hesingh/ventilator/Medtronic/pb560-vent-files-4/BOM Drawings/PB560 Ventilator/10037185AB0.pdf

REVISION

REV | DESCRIPTION
AB | RELEASE/CHANGE PER EC124632

COVIDIEN
6135 Gunbarrel Avenue
Boulder, CO 80301

TITLE:
CPU Software Requirements
Specification, PB560

DOCUMENT NUMBER
10037185

SHEET 1 of 204

REV
AB
PROPRIETARY & CONFIDENTIAL | FOR INTERNAL USE ONLY
This document may not be copied, disclosed, or used in whole or in part without the consent of COVIDIEN. ã 2014 COVIDIEN All Rights Reserved.

# CPU Software Requirements Specification

PB560

THIS IS A REQUISITE PRO DOCUMENT.
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
