hesingh/ventilator/Medtronic/pb560-vent-files-4/BOM Drawings/PB560 Ventilator/10096510/10096506/10096506A00/10096506A00/eqfc.dxf

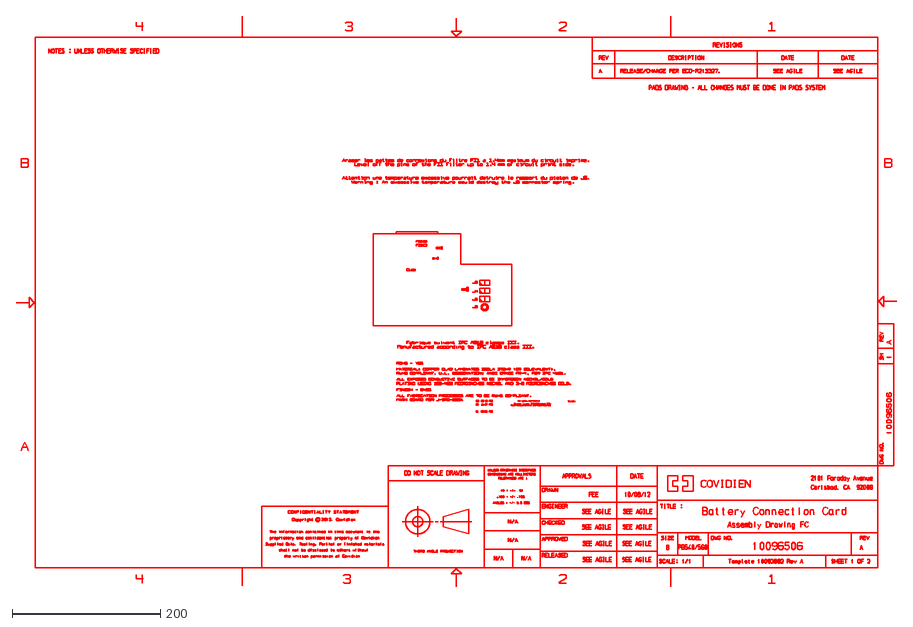
[picture p33: CAD file, 2020-04-06]
Medtronic/pb560-vent-files-4/BOM Drawings/PB560 Ventilator/10096510/10096506/10096506A00/10096506A00/eqfc.dxf
1188.1 x 770.1
