hesingh/ventilator/Medtronic/pb560-vent-files-4/BOM Drawings/PB560 PowerPack/10109800A00/HS Label.SLDPRT

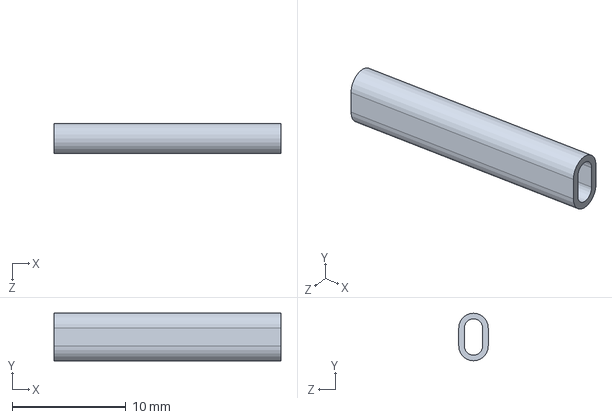
[picture p34: CAD file, 2020-04-06]
Medtronic/pb560-vent-files-4/BOM Drawings/PB560 PowerPack/10109800A00/HS Label.SLDPRT
20.0 x 4.20 x 2.60 mm
