hesingh/ventilator/Medtronic/medtronic-pb560-ventilator-system-file-set-2/3D CAD Models/PB560 Assy/capot 3 capteurs P phase 2.SLDPRT

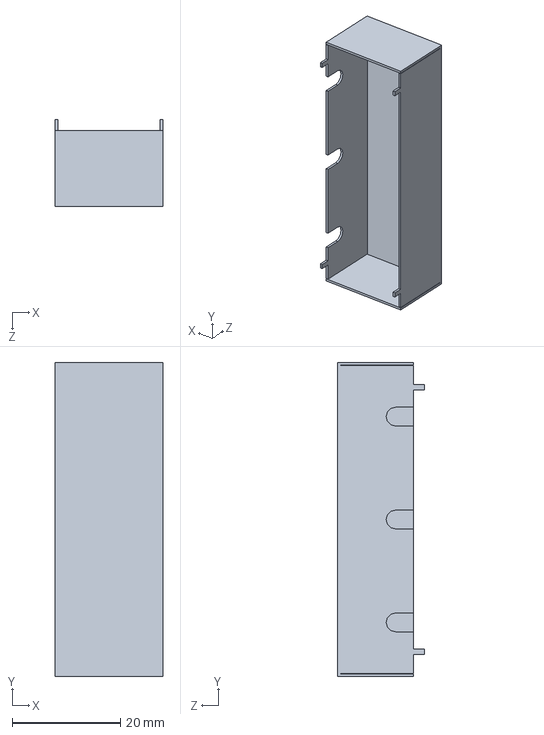
[picture p36: CAD file, 2020-04-06]
Medtronic/medtronic-pb560-ventilator-system-file-set-2/3D CAD Models/PB560 Assy/capot 3 capteurs P phase 2.SLDPRT
19.9 x 58.0 x 16.0 mm
