hesingh/ventilator/Medtronic/medtronic-pb560-ventilator-system-file-set-2/3D CAD Models/PB560 Assy/Insp Mod Connector.SLDPRT

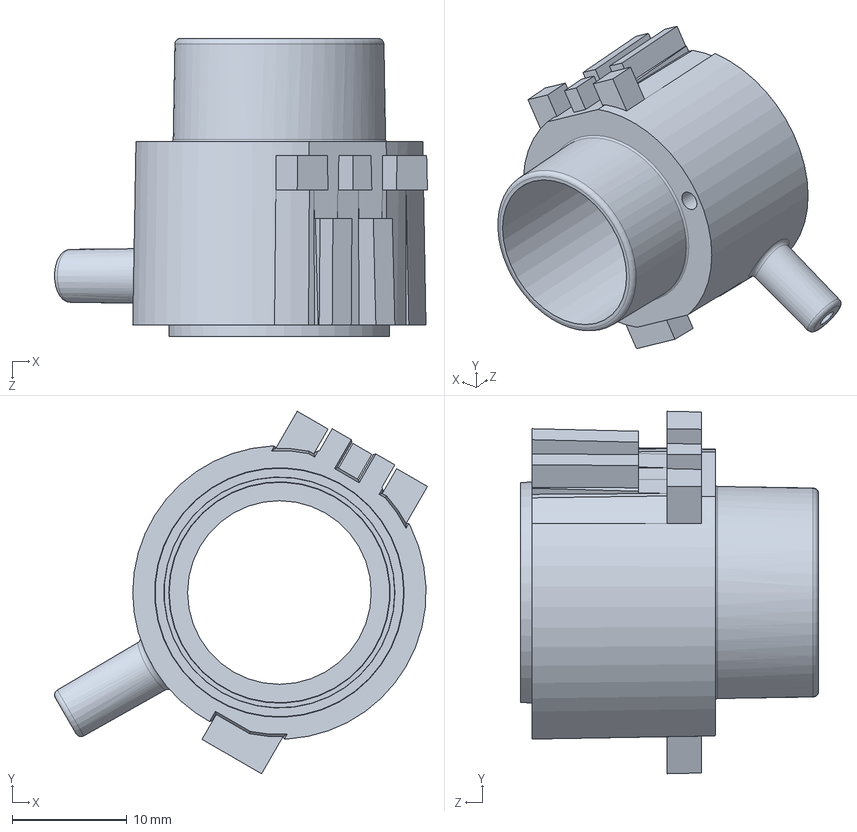
[picture p37: CAD file, 2020-04-06]
Medtronic/medtronic-pb560-ventilator-system-file-set-2/3D CAD Models/PB560 Assy/Insp Mod Connector.SLDPRT
32.5 x 31.6 x 26.0 mm
