hesingh/ventilator/Medtronic/pb560-vent-files-4/BOM Drawings/PB560 PowerPack/10106052C00/JST S2B-ZR-SM4A-TF.SLDPRT

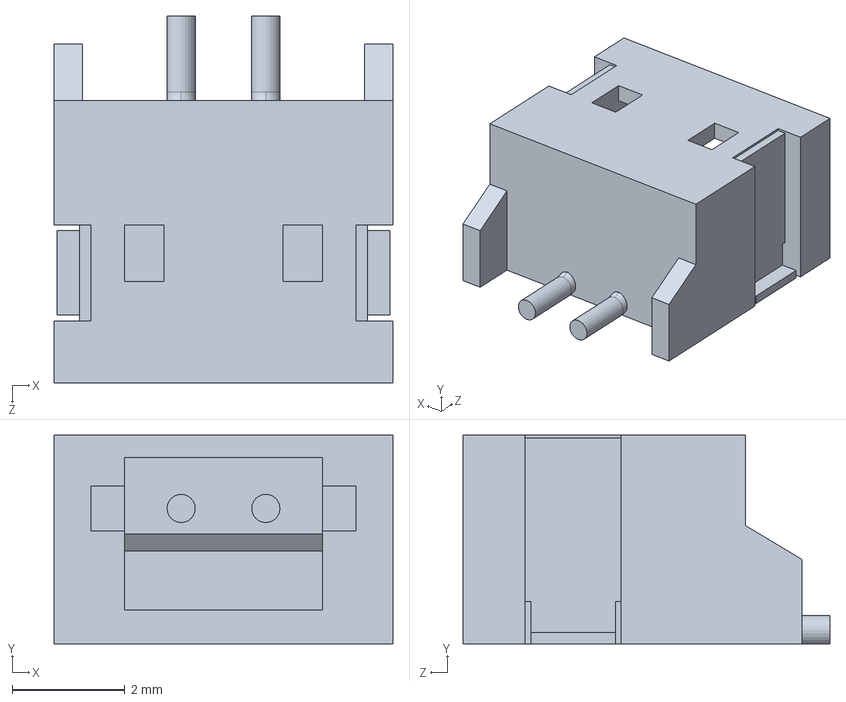
[picture p38: CAD file, 2020-04-06]
Medtronic/pb560-vent-files-4/BOM Drawings/PB560 PowerPack/10106052C00/JST S2B-ZR-SM4A-TF.SLDPRT
6.00 x 3.70 x 6.50 mm
