hesingh/ventilator/Medtronic/pb560-vent-files-4/BOM Drawings/PB560 PowerPack/10109802B00/Switchcraft 761KS15 Insulator sleeve.SLDPRT

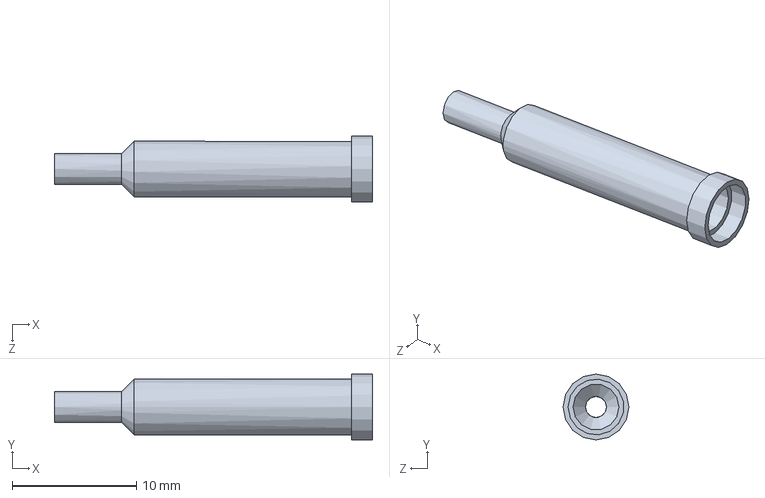
[picture p39: CAD file, 2020-04-06]
Medtronic/pb560-vent-files-4/BOM Drawings/PB560 PowerPack/10109802B00/Switchcraft 761KS15 Insulator sleeve.SLDPRT
25.6 x 5.30 x 5.30 mm
