hesingh/ventilator/Medtronic/pb560-vent-files-4/BOM Drawings/PB560 PowerPack/10106052C00/MOLEX 02661-4020.SLDPRT

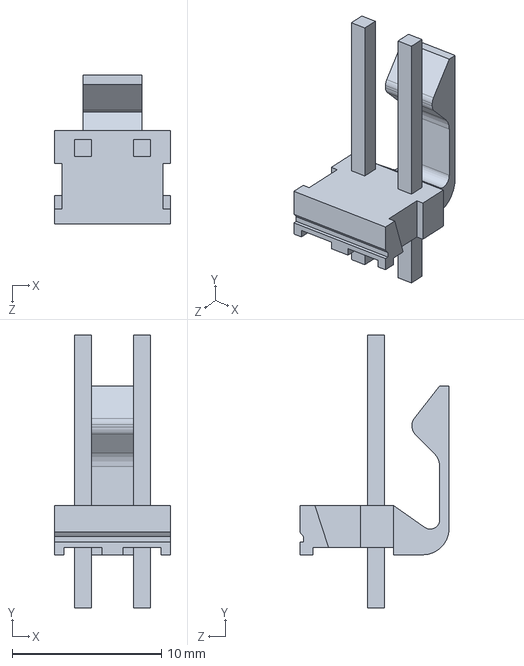
[picture p40: CAD file, 2020-04-06]
Medtronic/pb560-vent-files-4/BOM Drawings/PB560 PowerPack/10106052C00/MOLEX 02661-4020.SLDPRT
7.77 x 18.3 x 10.0 mm
