hesingh/ventilator/Medtronic/pb560-vent-files-4/BOM Drawings/PB560 PowerPack/10109802B00/Switchcraft 761KS15 Centre pin.SLDPRT

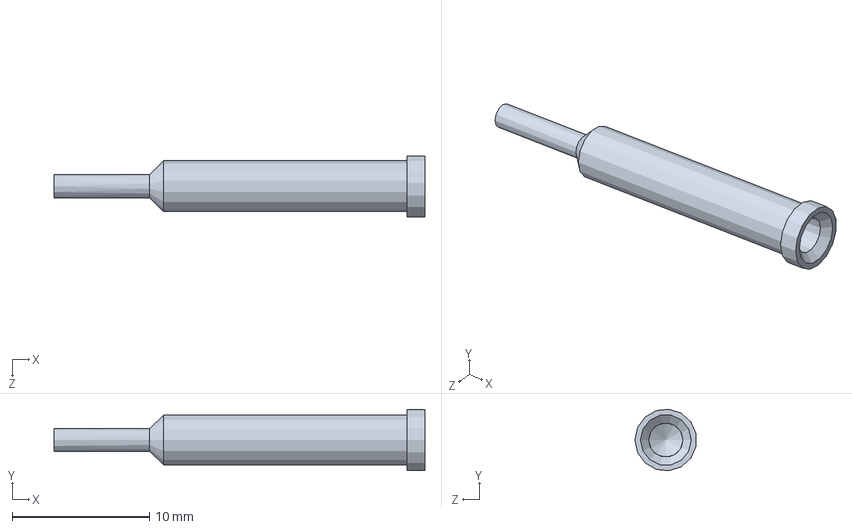
[picture p41: CAD file, 2020-04-06]
Medtronic/pb560-vent-files-4/BOM Drawings/PB560 PowerPack/10109802B00/Switchcraft 761KS15 Centre pin.SLDPRT
27.0 x 4.48 x 4.45 mm
