hesingh/ventilator/Medtronic/medtronic-pb560-ventilator-system-file-set-2/3D CAD Models/PB560 Assy/regulateur.SLDPRT

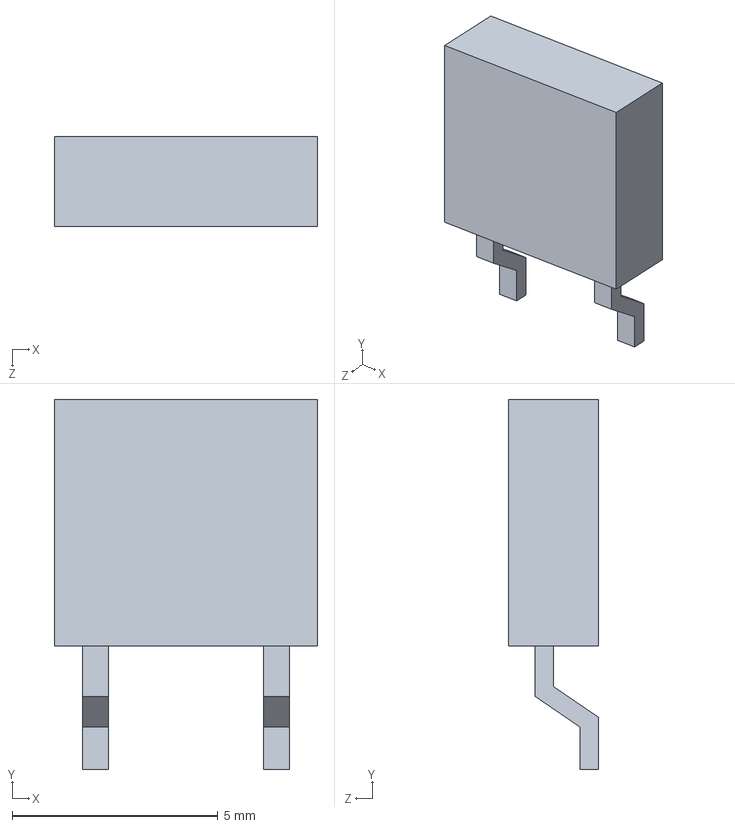
[picture p42: CAD file, 2020-04-06]
Medtronic/medtronic-pb560-ventilator-system-file-set-2/3D CAD Models/PB560 Assy/regulateur.SLDPRT
6.40 x 9.00 x 2.20 mm
