hesingh/ventilator/Medtronic/pb560-vent-files-4/BOM Drawings/PB560 PowerPack/10109802B00/WURTH 74270057.SLDPRT

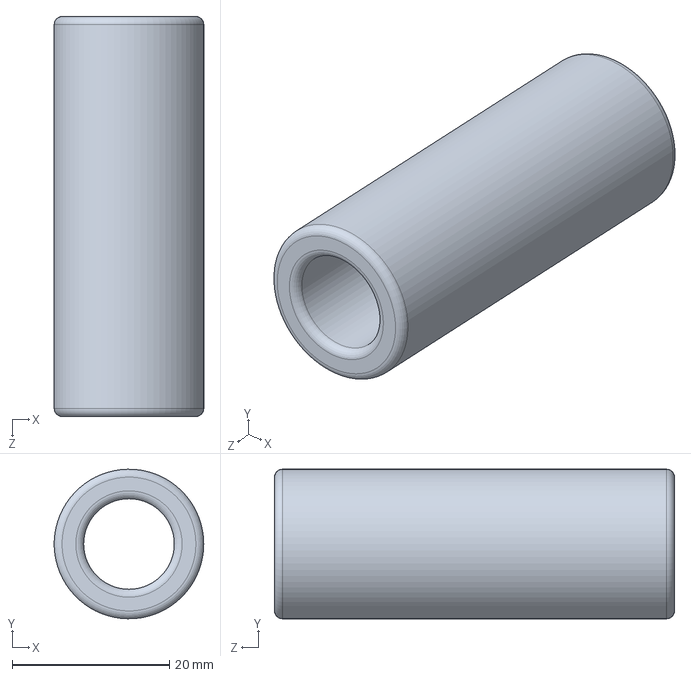
[picture p43: CAD file, 2020-04-06]
Medtronic/pb560-vent-files-4/BOM Drawings/PB560 PowerPack/10109802B00/WURTH 74270057.SLDPRT
19.0 x 19.0 x 50.8 mm
