hesingh/ventilator/Medtronic/medtronic-pb560-ventilator-system-file-set-2/3D CAD Models/PB560 Assy/carte clairitec.SLDPRT

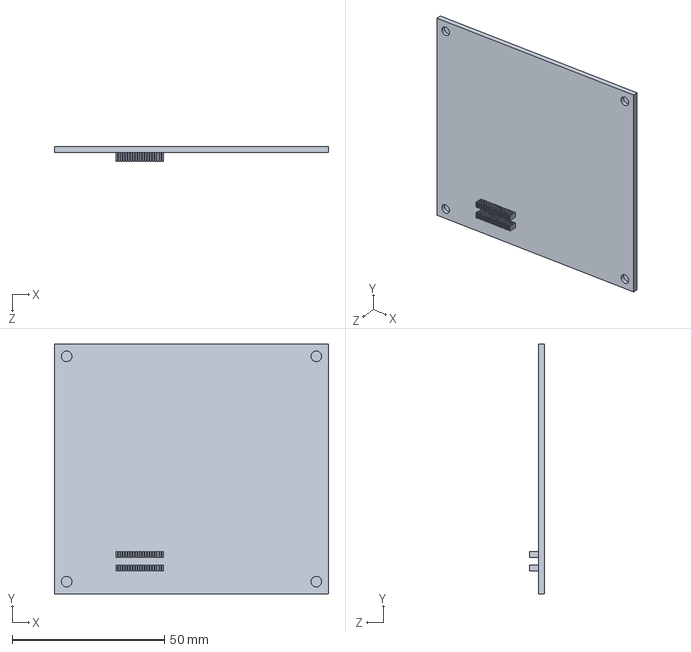
[picture p44: CAD file, 2020-04-06]
Medtronic/medtronic-pb560-ventilator-system-file-set-2/3D CAD Models/PB560 Assy/carte clairitec.SLDPRT
90.0 x 82.0 x 5.00 mm
