hesingh/ventilator/Medtronic/pb560-vent-files-4/BOM Drawings/PB560 PowerPack/10106052C00/MOLEX 43650-0229.SLDPRT

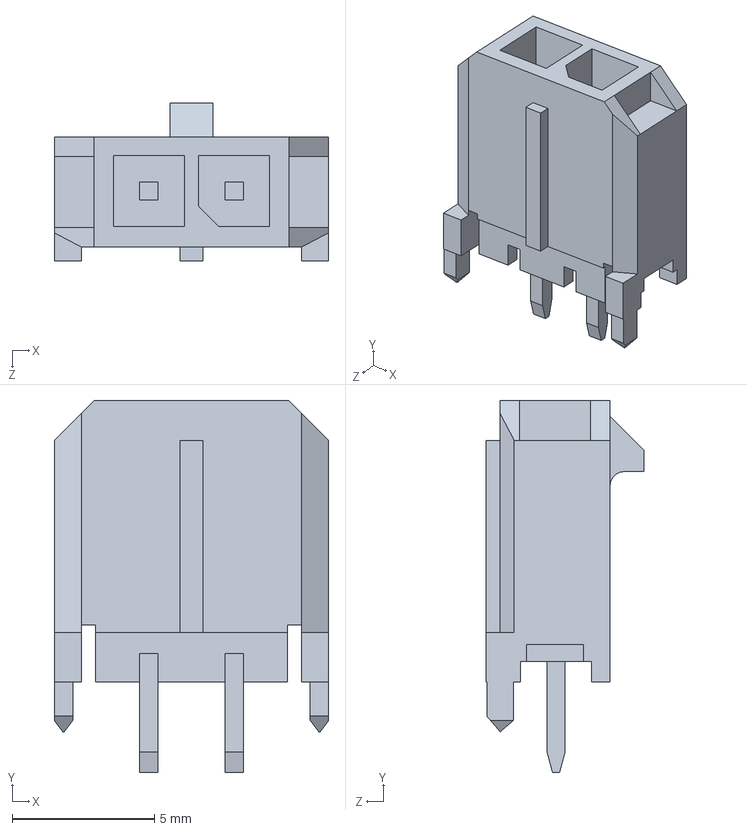
[picture p45: CAD file, 2020-04-06]
Medtronic/pb560-vent-files-4/BOM Drawings/PB560 PowerPack/10106052C00/MOLEX 43650-0229.SLDPRT
9.65 x 13.1 x 5.57 mm
