hesingh/ventilator/Medtronic/pb560-vent-files-4/BOM Drawings/PB560 PowerPack/10109802B00/Switchcraft 761KS15 Terminal spacer.SLDPRT

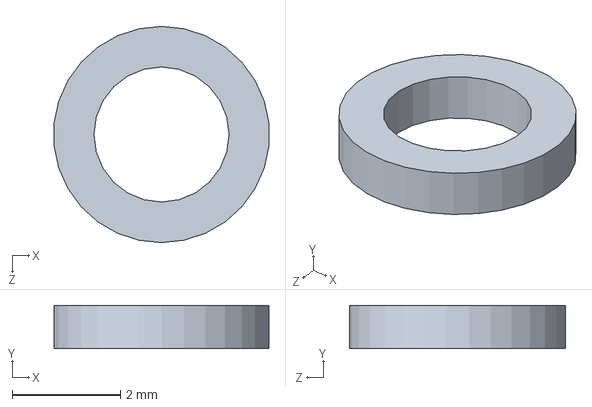
[picture p46: CAD file, 2020-04-06]
Medtronic/pb560-vent-files-4/BOM Drawings/PB560 PowerPack/10109802B00/Switchcraft 761KS15 Terminal spacer.SLDPRT
3.98 x 0.8 x 4.00 mm
