hesingh/ventilator/Medtronic/medtronic-pb560-ventilator-system-file-set-2/3D CAD Models/PB560 Assy/09-48-4038.SLDPRT

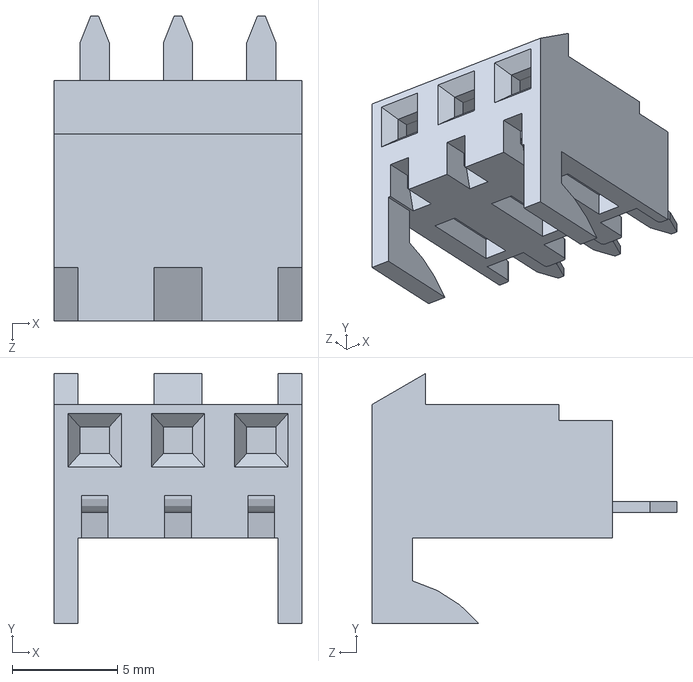
[picture p47: CAD file, 2020-04-06]
Medtronic/medtronic-pb560-ventilator-system-file-set-2/3D CAD Models/PB560 Assy/09-48-4038.SLDPRT
11.8 x 11.9 x 14.5 mm
