hesingh/ventilator/Medtronic/medtronic-pb560-ventilator-system-file-set-2/3D CAD Models/PB560 Assy/HARTING 09185107323.SLDPRT

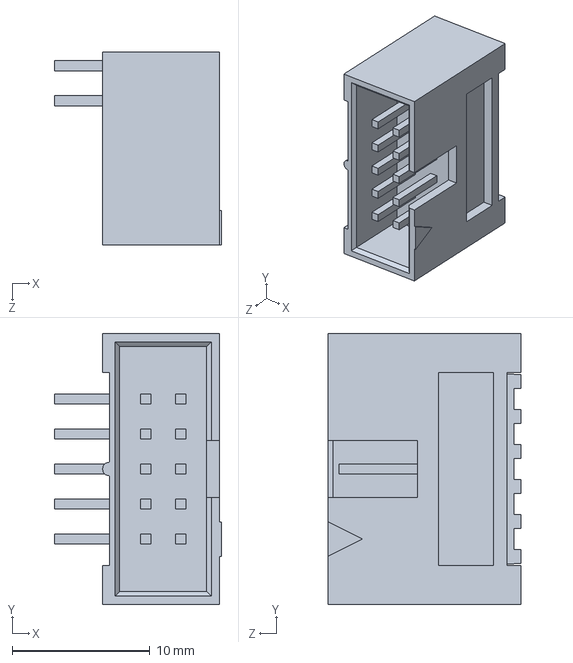
[picture p48: CAD file, 2020-04-06]
Medtronic/medtronic-pb560-ventilator-system-file-set-2/3D CAD Models/PB560 Assy/HARTING 09185107323.SLDPRT
12.1 x 19.7 x 14.0 mm
