hesingh/ventilator/Medtronic/pb560-vent-files-4/BOM Drawings/PB560 PowerPack/10109802B00/LEMO FHG.1B.306.CLAD52.SLDPRT

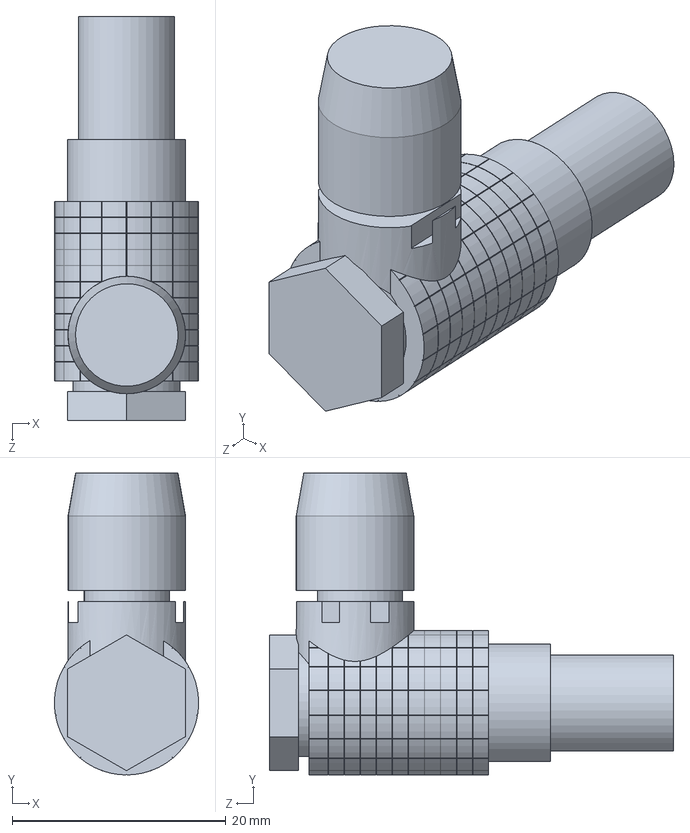
[picture p49: CAD file, 2020-04-06]
Medtronic/pb560-vent-files-4/BOM Drawings/PB560 PowerPack/10109802B00/LEMO FHG.1B.306.CLAD52.SLDPRT
13.5 x 28.2 x 37.8 mm
