hesingh/ventilator/Medtronic/medtronic-pb560-ventilator-system-file-set-2/3D CAD Models/PB560 Assy/3M 7810-0000PR.SLDPRT

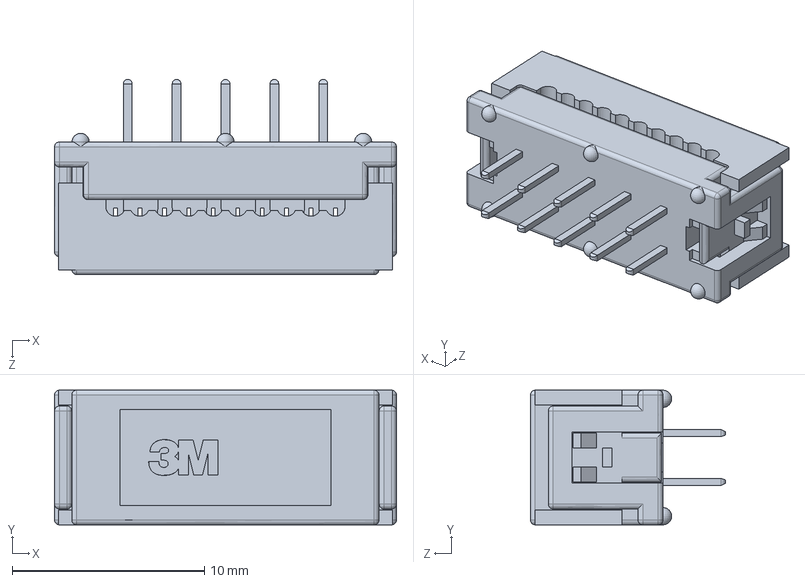
[picture p50: CAD file, 2020-04-06]
Medtronic/medtronic-pb560-ventilator-system-file-set-2/3D CAD Models/PB560 Assy/3M 7810-0000PR.SLDPRT
17.8 x 7.00 x 10.1 mm
