hesingh/ventilator/Medtronic/medtronic-pb560-ventilator-system-file-set-2/3D CAD Models/PB560 Assy/Batt PCB.SLDPRT

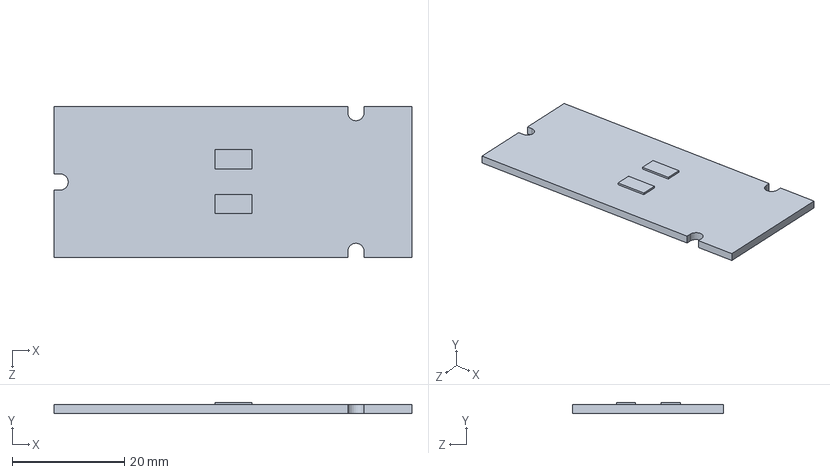
[picture p51: CAD file, 2020-04-06]
Medtronic/medtronic-pb560-ventilator-system-file-set-2/3D CAD Models/PB560 Assy/Batt PCB.SLDPRT
63.9 x 2.00 x 26.9 mm
