hesingh/ventilator/Medtronic/medtronic-pb560-ventilator-system-file-set-2/3D CAD Models/PB560 Assy/Cable tie (ref AML).SLDPRT

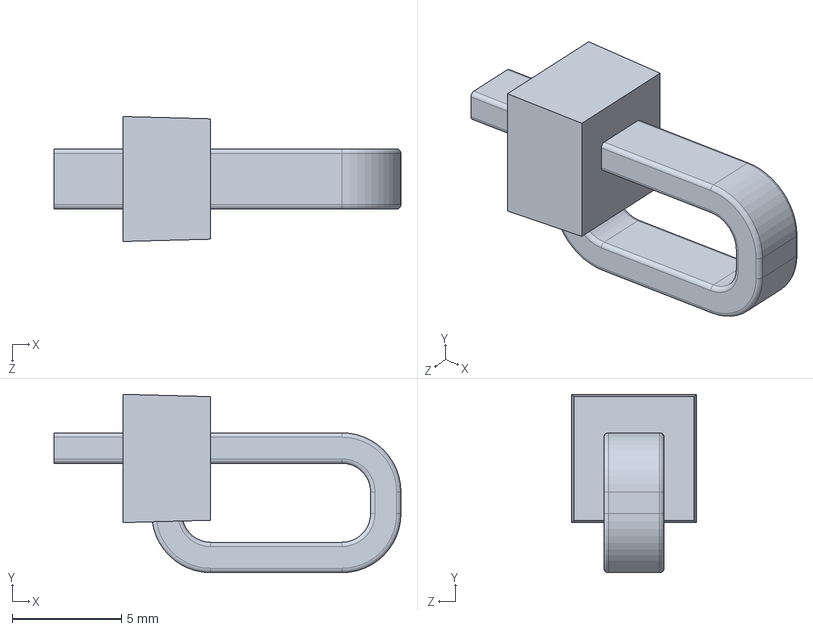
[picture p52: CAD file, 2020-04-06]
Medtronic/medtronic-pb560-ventilator-system-file-set-2/3D CAD Models/PB560 Assy/Cable tie (ref AML).SLDPRT
15.9 x 8.15 x 5.71 mm
