hesingh/ventilator/Medtronic/medtronic-pb560-ventilator-system-file-set-2/3D CAD Models/PB560 Assy/3M 4032 x30mm.SLDPRT

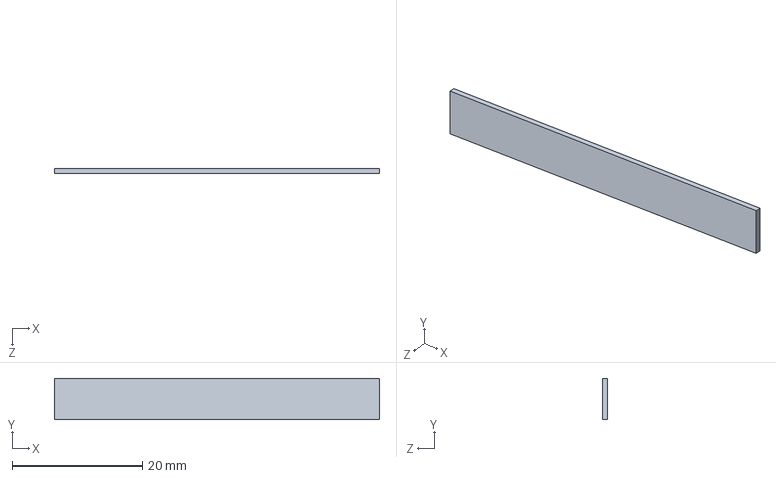
[picture p53: CAD file, 2020-04-06]
Medtronic/medtronic-pb560-ventilator-system-file-set-2/3D CAD Models/PB560 Assy/3M 4032 x30mm.SLDPRT
50.0 x 6.35 x 0.8 mm
