hesingh/ventilator/Medtronic/medtronic-pb560-ventilator-system-file-set-2/3D CAD Models/PB560 Assy/tuyau 15x21 silicone.SLDPRT

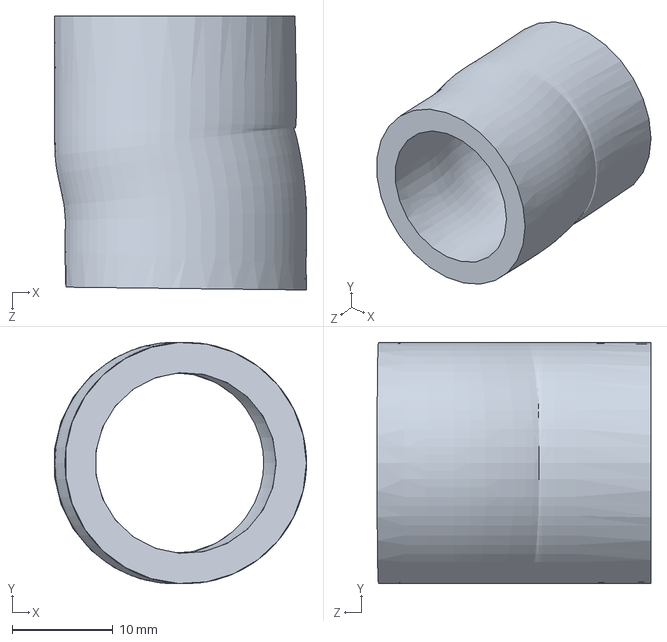
[picture p54: CAD file, 2020-04-06]
Medtronic/medtronic-pb560-ventilator-system-file-set-2/3D CAD Models/PB560 Assy/tuyau 15x21 silicone.SLDPRT
25.1 x 24.0 x 27.2 mm
