hesingh/ventilator/Medtronic/medtronic-pb560-ventilator-system-file-set-2/3D CAD Models/PB560 Assy/tuyau  droit sortie vanne O2.SLDPRT

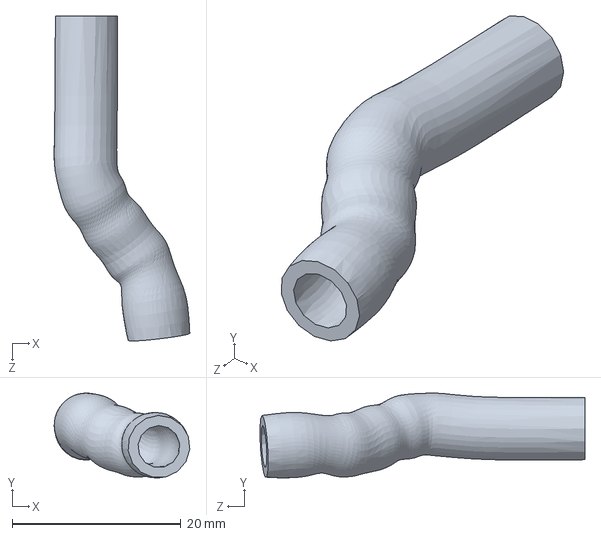
[picture p55: CAD file, 2020-04-06]
Medtronic/medtronic-pb560-ventilator-system-file-set-2/3D CAD Models/PB560 Assy/tuyau droit sortie vanne O2.SLDPRT
16.1 x 10.0 x 38.5 mm
