hesingh/ventilator/Medtronic/medtronic-pb560-ventilator-system-file-set-2/3D CAD Models/PB560 Assy/MOLEX 22-05-7098.SLDPRT

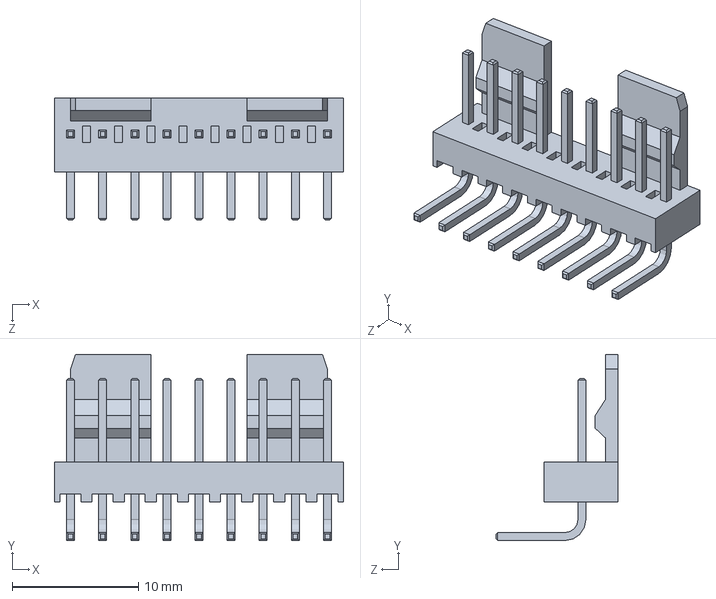
[picture p56: CAD file, 2020-04-06]
Medtronic/medtronic-pb560-ventilator-system-file-set-2/3D CAD Models/PB560 Assy/MOLEX 22-05-7098.SLDPRT
22.9 x 14.7 x 9.65 mm
