hesingh/ventilator/Medtronic/medtronic-pb560-ventilator-system-file-set-2/3D CAD Models/PB560 Assy/tuyau pression prox1.6x4.8.SLDPRT

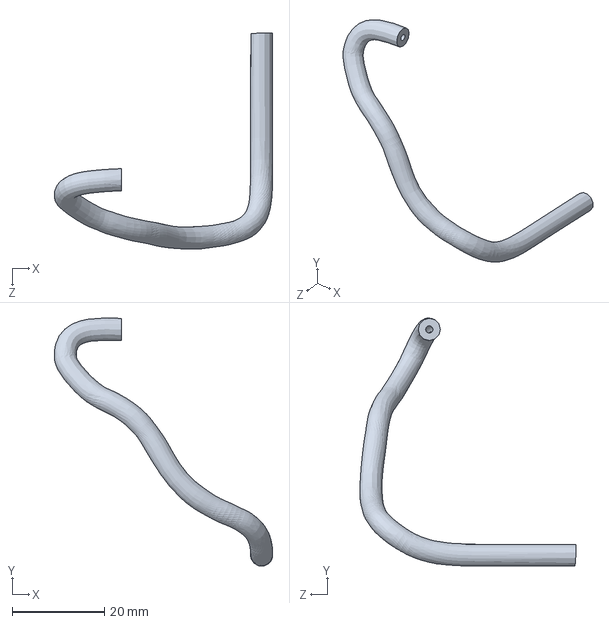
[picture p57: CAD file, 2020-04-06]
Medtronic/medtronic-pb560-ventilator-system-file-set-2/3D CAD Models/PB560 Assy/tuyau pression prox1.6x4.8.SLDPRT
47.2 x 53.6 x 46.8 mm
