hesingh/ventilator/Medtronic/medtronic-pb560-ventilator-system-file-set-2/3D CAD Models/PB560 Assy/thermistances CTN.SLDPRT

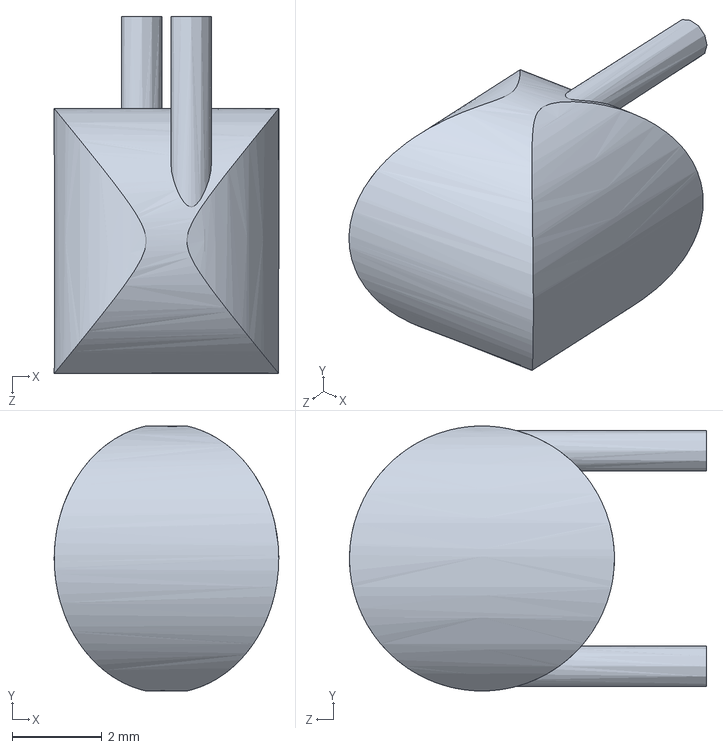
[picture p58: CAD file, 2020-04-06]
Medtronic/medtronic-pb560-ventilator-system-file-set-2/3D CAD Models/PB560 Assy/thermistances CTN.SLDPRT
5.00 x 5.90 x 7.95 mm
