hesingh/ventilator/Medtronic/medtronic-pb560-ventilator-system-file-set-2/3D CAD Models/PB560 Assy/tuyau sortie vanne pilot1.6x4.8.SLDPRT

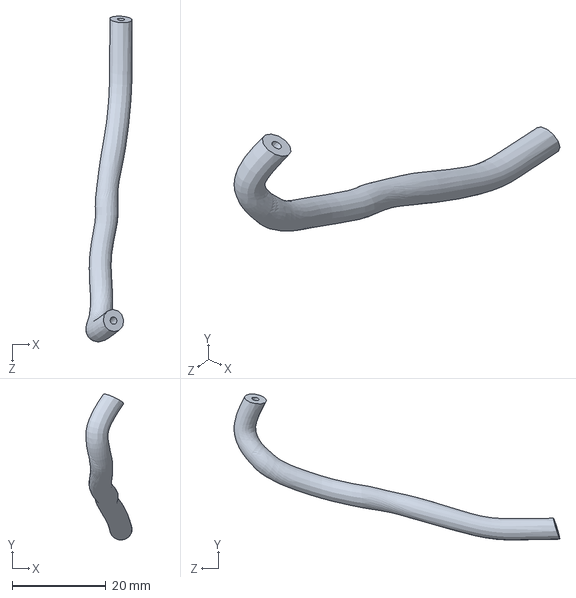
[picture p59: CAD file, 2020-04-06]
Medtronic/medtronic-pb560-ventilator-system-file-set-2/3D CAD Models/PB560 Assy/tuyau sortie vanne pilot1.6x4.8.SLDPRT
9.88 x 31.1 x 69.5 mm
