hesingh/ventilator/Medtronic/medtronic-pb560-ventilator-system-file-set-2/3D CAD Models/PB560 Assy/etiq reperage vanne O2.SLDPRT

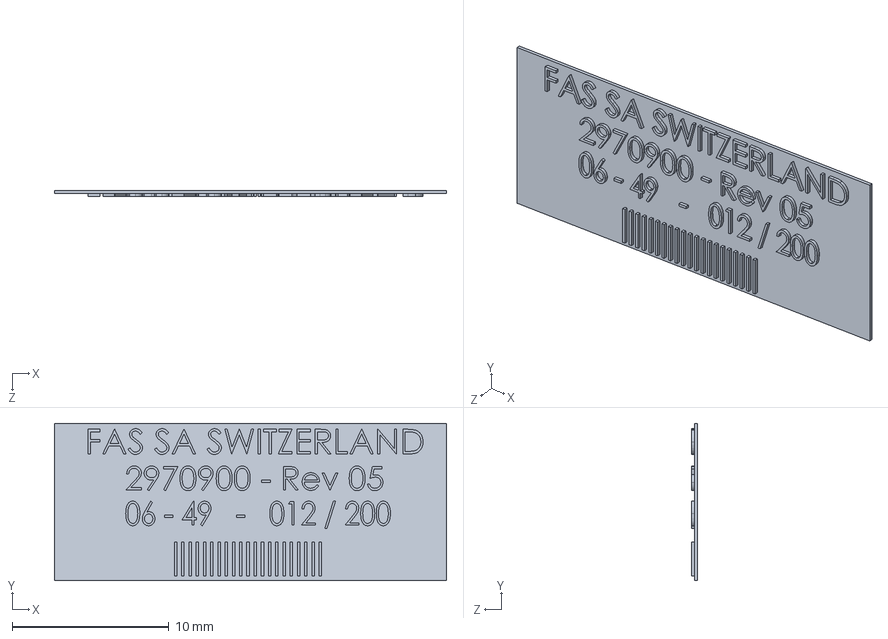
[picture p60: CAD file, 2020-04-06]
Medtronic/medtronic-pb560-ventilator-system-file-set-2/3D CAD Models/PB560 Assy/etiq reperage vanne O2.SLDPRT
25.0 x 10.0 x 0.4 mm
