hesingh/ventilator/Medtronic/medtronic-pb560-ventilator-system-file-set-2/3D CAD Models/PB560 Assy/Molex 90635-1262.SLDPRT

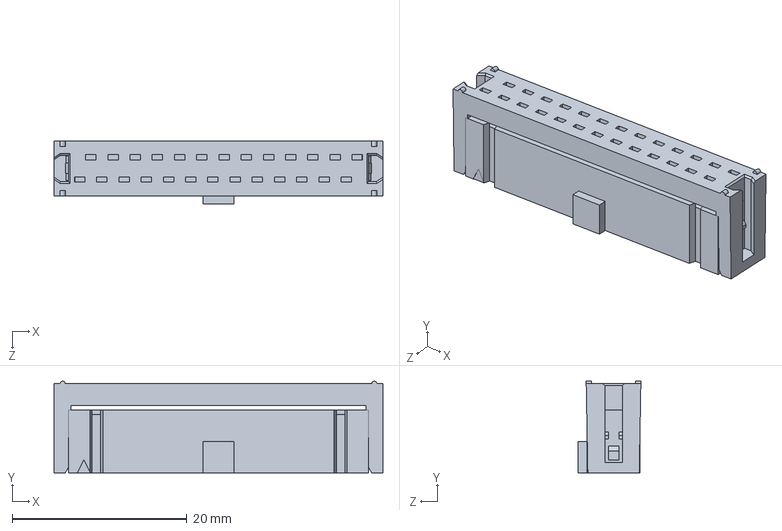
[picture p61: CAD file, 2020-04-06]
Medtronic/medtronic-pb560-ventilator-system-file-set-2/3D CAD Models/PB560 Assy/Molex 90635-1262.SLDPRT
37.6 x 10.5 x 7.18 mm
