hesingh/ventilator/Medtronic/medtronic-pb560-ventilator-system-file-set-2/3D CAD Models/PB560 Assy/HIROSE HR30-6R-6S.SLDPRT

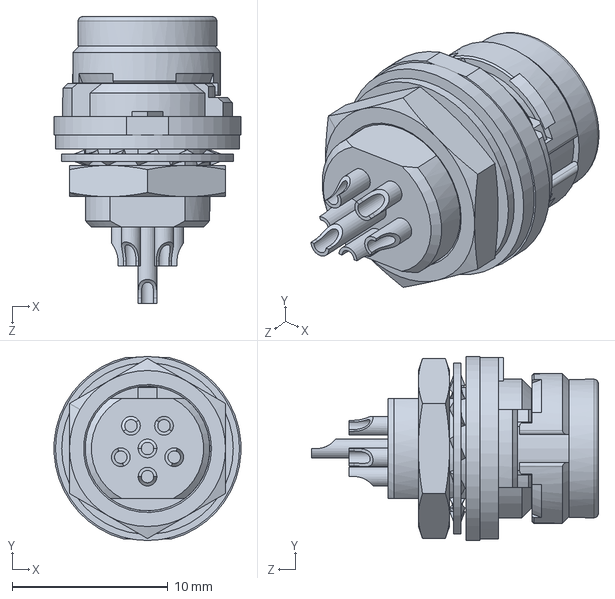
[picture p62: CAD file, 2020-04-06]
Medtronic/medtronic-pb560-ventilator-system-file-set-2/3D CAD Models/PB560 Assy/HIROSE HR30-6R-6S.SLDPRT
12.0 x 11.8 x 18.4 mm
