hesingh/ventilator/Medtronic/medtronic-pb560-ventilator-system-file-set-2/3D CAD Models/PB560 Assy/alimentation phase 2.SLDPRT

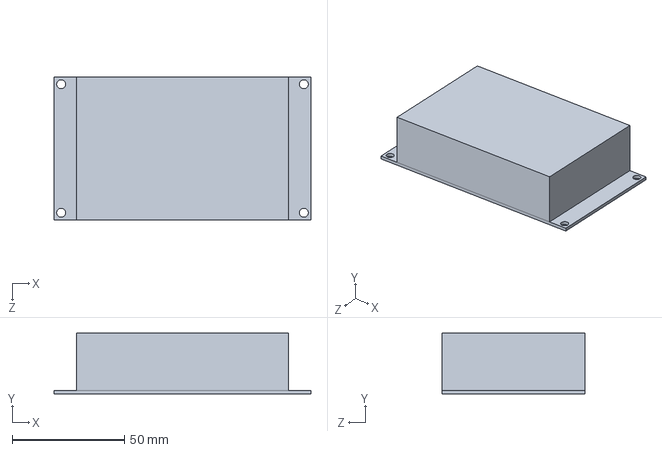
[picture p63: CAD file, 2020-04-06]
Medtronic/medtronic-pb560-ventilator-system-file-set-2/3D CAD Models/PB560 Assy/alimentation phase 2.SLDPRT
114.3 x 27.0 x 63.5 mm
