hesingh/ventilator/Medtronic/medtronic-pb560-ventilator-system-file-set-2/3D CAD Models/PB560 Assy/1mm bumper.SLDPRT

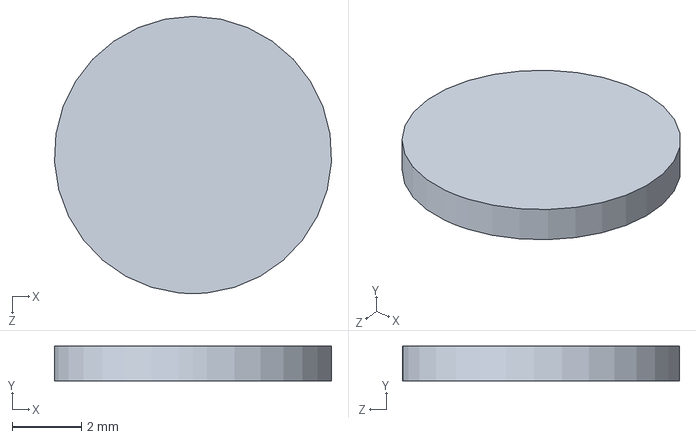
[picture p64: CAD file, 2020-04-06]
Medtronic/medtronic-pb560-ventilator-system-file-set-2/3D CAD Models/PB560 Assy/1mm bumper.SLDPRT
7.99 x 1.00 x 8.00 mm
