hesingh/ventilator/Medtronic/medtronic-pb560-ventilator-system-file-set-2/3D CAD Models/PB560 Assy/Batt Contacts tab.SLDPRT

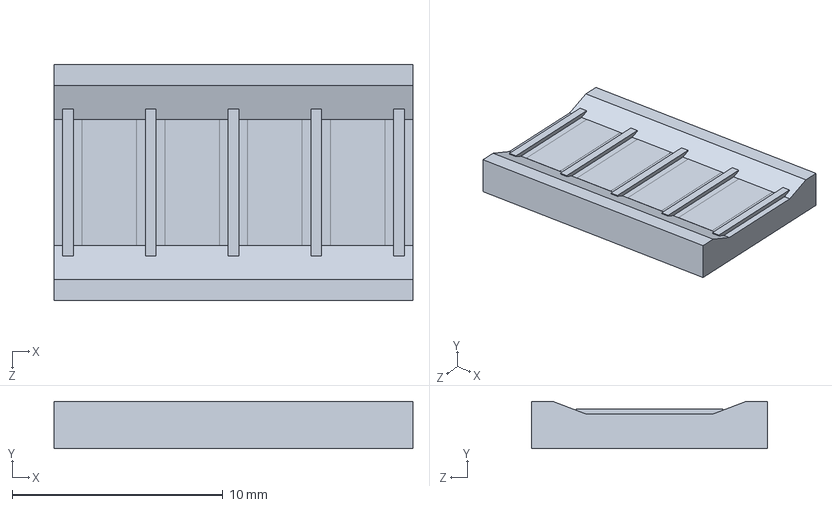
[picture p66: CAD file, 2020-04-06]
Medtronic/medtronic-pb560-ventilator-system-file-set-2/3D CAD Models/PB560 Assy/Batt Contacts tab.SLDPRT
17.0 x 2.25 x 11.2 mm
