hesingh/ventilator/Medtronic/medtronic-pb560-ventilator-system-file-set-2/3D CAD Models/PB560 Assy/Rondelle plate - ZU  3 x 6 EP 0.8.sldprt

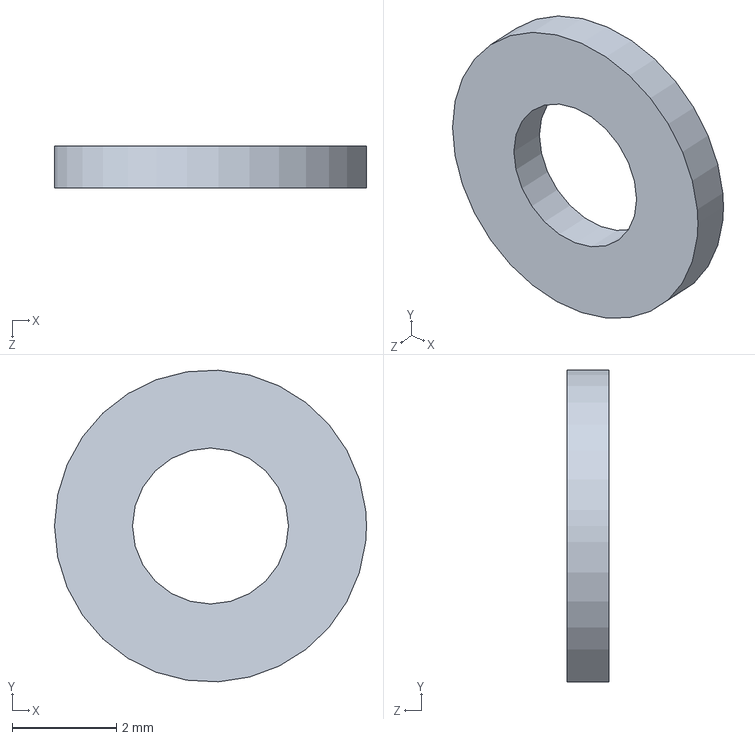
[picture p67: CAD file, 2020-04-06]
Medtronic/medtronic-pb560-ventilator-system-file-set-2/3D CAD Models/PB560 Assy/Rondelle plate - ZU 3 x 6 EP 0.8.sldprt
6.00 x 5.99 x 0.8 mm
