hesingh/ventilator/Medtronic/medtronic-pb560-ventilator-system-file-set-2/3D CAD Models/PB560 Assy/MODULE PRISE 230+INTER.SLDPRT

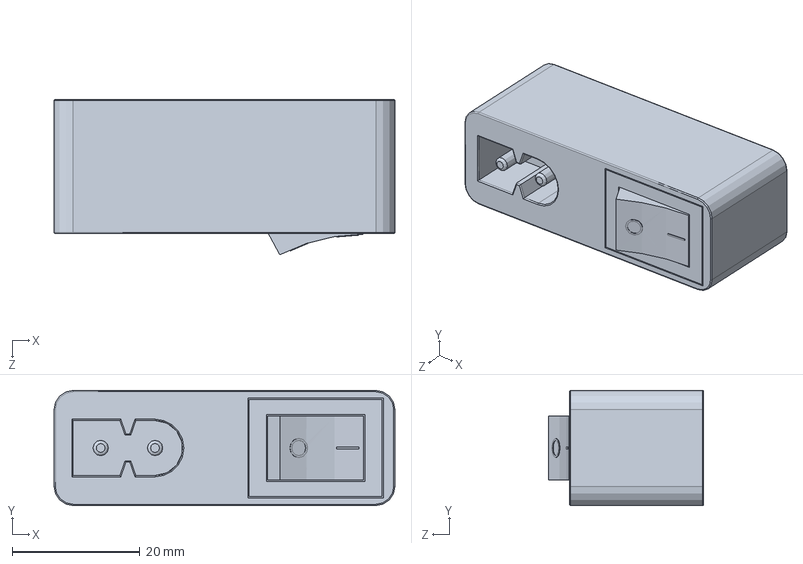
[picture p68: CAD file, 2020-04-06]
Medtronic/medtronic-pb560-ventilator-system-file-set-2/3D CAD Models/PB560 Assy/MODULE PRISE 230+INTER.SLDPRT
53.3 x 18.0 x 24.3 mm
