hesingh/ventilator/Medtronic/medtronic-pb560-ventilator-system-file-set-2/3D CAD Models/PB560 Assy/Vis KA22x5 hexalobes.SLDPRT

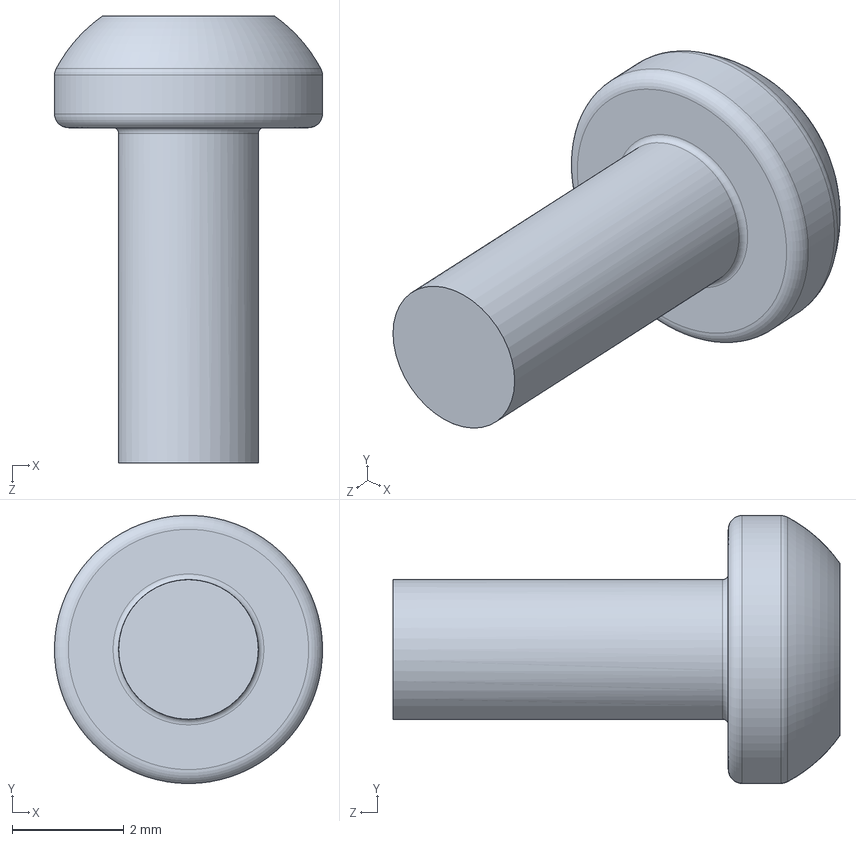
[picture p69: CAD file, 2020-04-06]
Medtronic/medtronic-pb560-ventilator-system-file-set-2/3D CAD Models/PB560 Assy/Vis KA22x5 hexalobes.SLDPRT
4.80 x 4.80 x 8.00 mm
