hesingh/ventilator/Medtronic/medtronic-pb560-ventilator-system-file-set-2/3D CAD Models/PB560 Assy/carte buzzer.SLDPRT

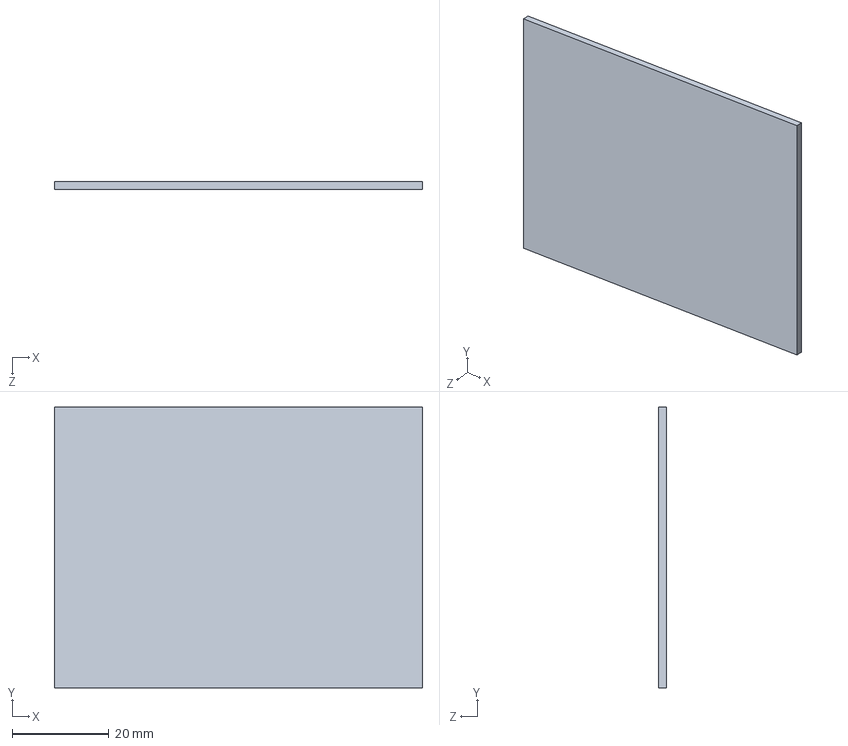
[picture p70: CAD file, 2020-04-06]
Medtronic/medtronic-pb560-ventilator-system-file-set-2/3D CAD Models/PB560 Assy/carte buzzer.SLDPRT
76.0 x 58.0 x 1.60 mm
