hesingh/ventilator/Medtronic/medtronic-pb560-ventilator-system-file-set-2/3D CAD Models/PB560 Assy/Front End Cap.SLDPRT

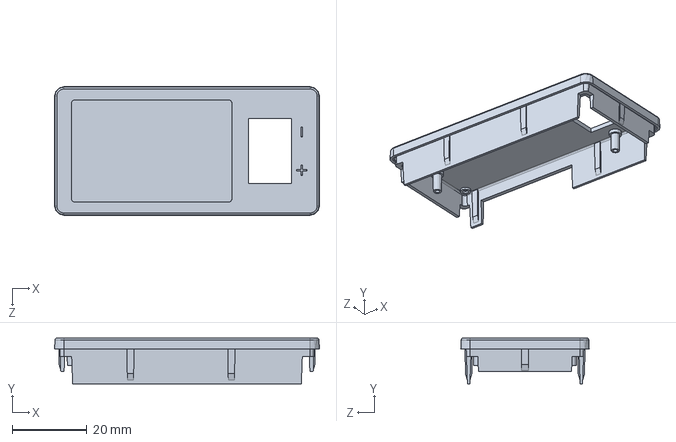
[picture p71: CAD file, 2020-04-06]
Medtronic/medtronic-pb560-ventilator-system-file-set-2/3D CAD Models/PB560 Assy/Front End Cap.SLDPRT
70.9 x 12.3 x 34.4 mm
