hesingh/ventilator/Medtronic/medtronic-pb560-ventilator-system-file-set-2/3D CAD Models/PB560 Assy/condensateur.SLDPRT

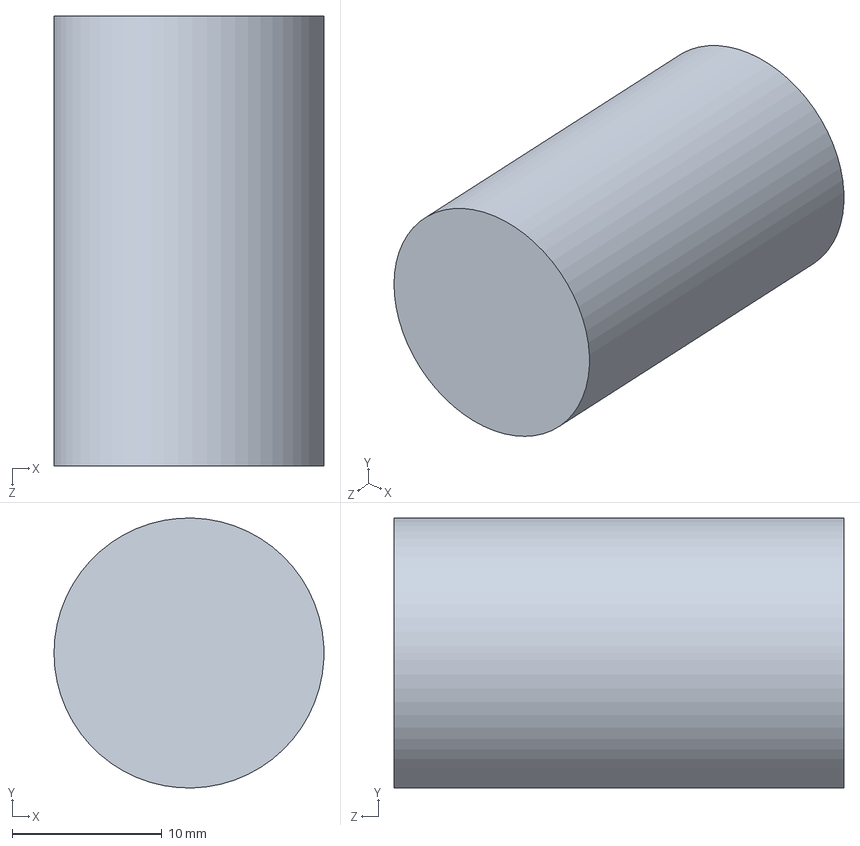
[picture p72: CAD file, 2020-04-06]
Medtronic/medtronic-pb560-ventilator-system-file-set-2/3D CAD Models/PB560 Assy/condensateur.SLDPRT
18.0 x 18.0 x 30.0 mm
