hesingh/ventilator/Medtronic/medtronic-pb560-ventilator-system-file-set-2/3D CAD Models/PB560 Assy/cache transfo.SLDPRT

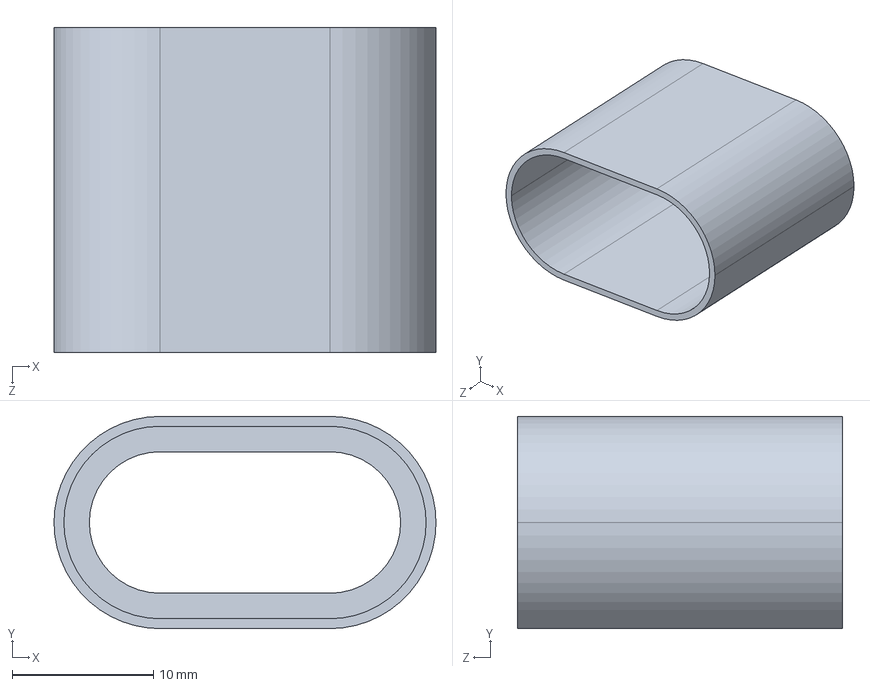
[picture p73: CAD file, 2020-04-06]
Medtronic/medtronic-pb560-ventilator-system-file-set-2/3D CAD Models/PB560 Assy/cache transfo.SLDPRT
27.0 x 15.0 x 23.0 mm
