hesingh/ventilator/Medtronic/medtronic-pb560-ventilator-system-file-set-2/3D CAD Models/PB560 Assy/Extruded housing.SLDPRT

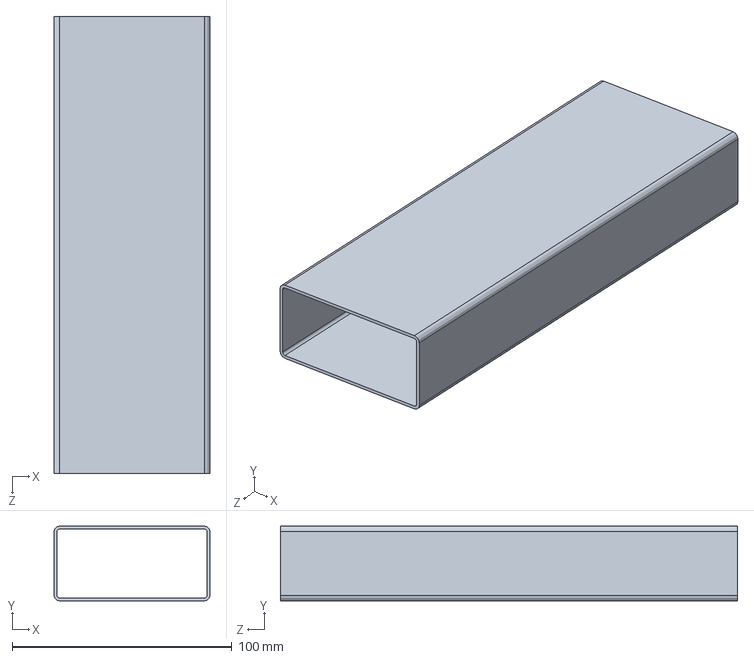
[picture p74: CAD file, 2020-04-06]
Medtronic/medtronic-pb560-ventilator-system-file-set-2/3D CAD Models/PB560 Assy/Extruded housing.SLDPRT
71.0 x 34.0 x 208.0 mm
