hesingh/ventilator/Medtronic/medtronic-pb560-ventilator-system-file-set-2/3D CAD Models/PB560 Assy/MOLEX 22-05-7088.SLDPRT

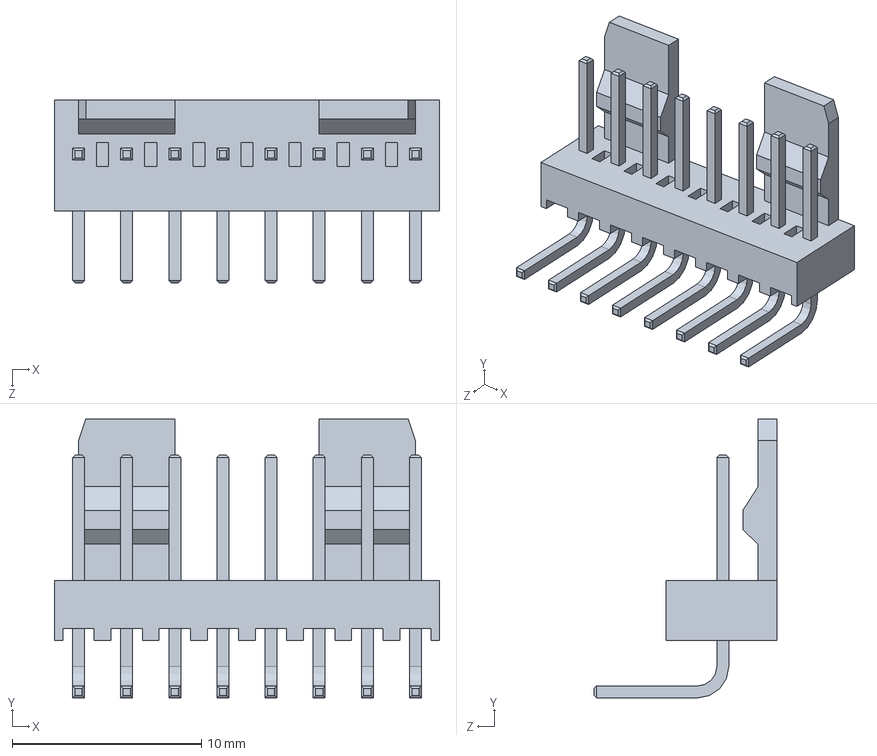
[picture p75: CAD file, 2020-04-06]
Medtronic/medtronic-pb560-ventilator-system-file-set-2/3D CAD Models/PB560 Assy/MOLEX 22-05-7088.SLDPRT
20.3 x 14.7 x 9.65 mm
