hesingh/ventilator/Medtronic/medtronic-pb560-ventilator-system-file-set-2/3D CAD Models/PB560 Assy/AFFICHEUR TWIN.SLDPRT

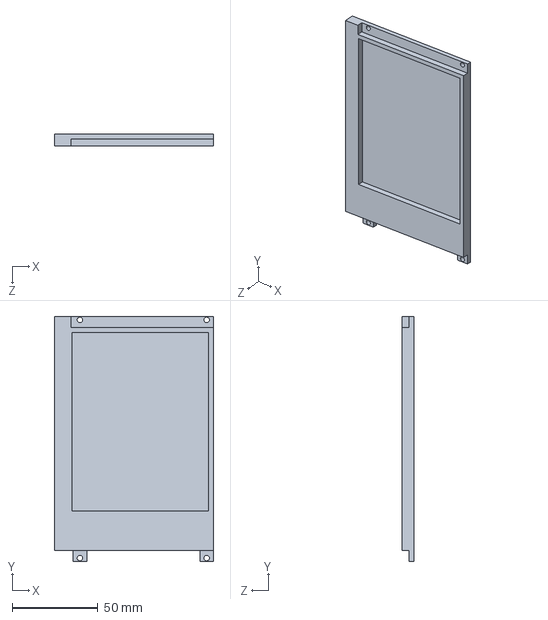
[picture p76: CAD file, 2020-04-06]
Medtronic/medtronic-pb560-ventilator-system-file-set-2/3D CAD Models/PB560 Assy/AFFICHEUR TWIN.SLDPRT
92.6 x 142.6 x 7.00 mm
