hesingh/ventilator/Medtronic/medtronic-pb560-ventilator-system-file-set-2/3D CAD Models/PB560 Assy/capteur pression absolue.SLDPRT

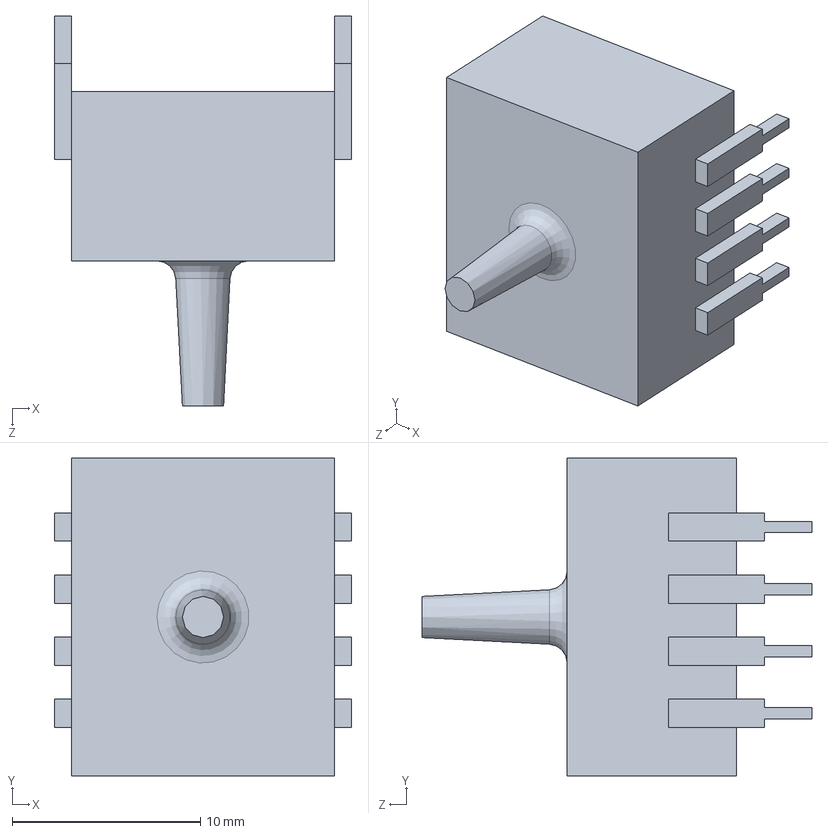
[picture p77: CAD file, 2020-04-06]
Medtronic/medtronic-pb560-ventilator-system-file-set-2/3D CAD Models/PB560 Assy/capteur pression absolue.SLDPRT
15.8 x 16.9 x 20.7 mm
