hesingh/ventilator/Medtronic/medtronic-pb560-ventilator-system-file-set-2/3D CAD Models/PB560 Assy/26-48-1125.SLDPRT

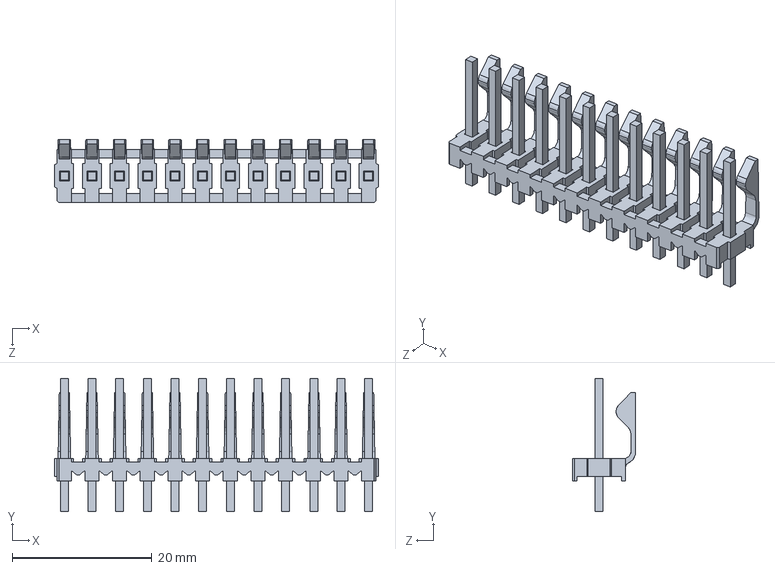
[picture p78: CAD file, 2020-04-06]
Medtronic/medtronic-pb560-ventilator-system-file-set-2/3D CAD Models/PB560 Assy/26-48-1125.SLDPRT
46.4 x 19.1 x 9.02 mm
