hesingh/ventilator/Medtronic/medtronic-pb560-ventilator-system-file-set-2/3D CAD Models/PB560 Assy/capteur debit.SLDPRT

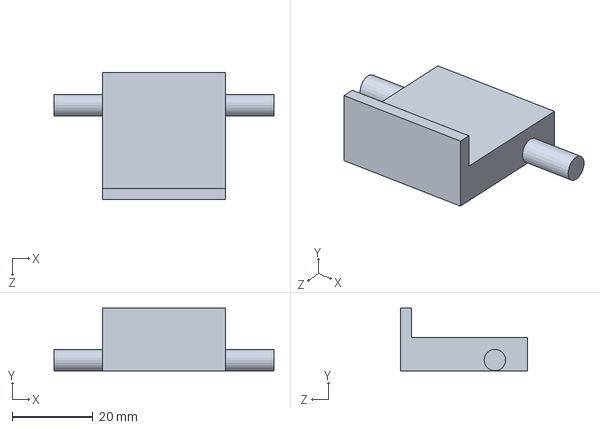
[picture p79: CAD file, 2020-04-06]
Medtronic/medtronic-pb560-ventilator-system-file-set-2/3D CAD Models/PB560 Assy/capteur debit.SLDPRT
54.5 x 15.5 x 31.5 mm
