hesingh/ventilator/Medtronic/medtronic-pb560-ventilator-system-file-set-2/3D CAD Models/PB560 Assy/tuyau pression vanne pilot1.6x4.8.SLDPRT

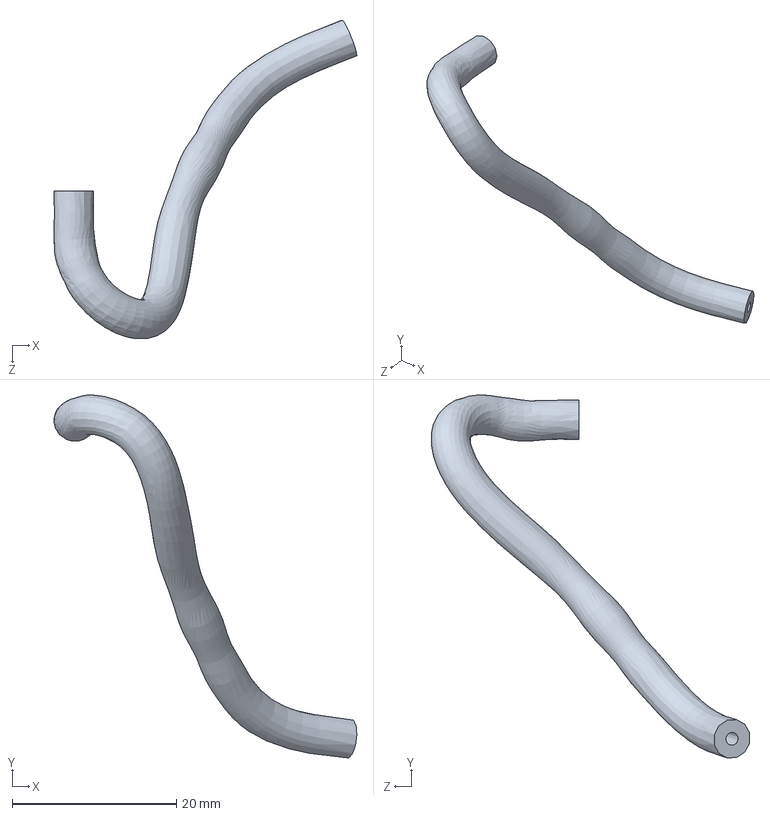
[picture p80: CAD file, 2020-04-06]
Medtronic/medtronic-pb560-ventilator-system-file-set-2/3D CAD Models/PB560 Assy/tuyau pression vanne pilot1.6x4.8.SLDPRT
36.8 x 44.2 x 38.7 mm
