hesingh/ventilator/Medtronic/medtronic-pb560-ventilator-system-file-set-2/3D CAD Models/PB560 Assy/PRECI-DIP 811-S1-002-30-014101.SLDPRT

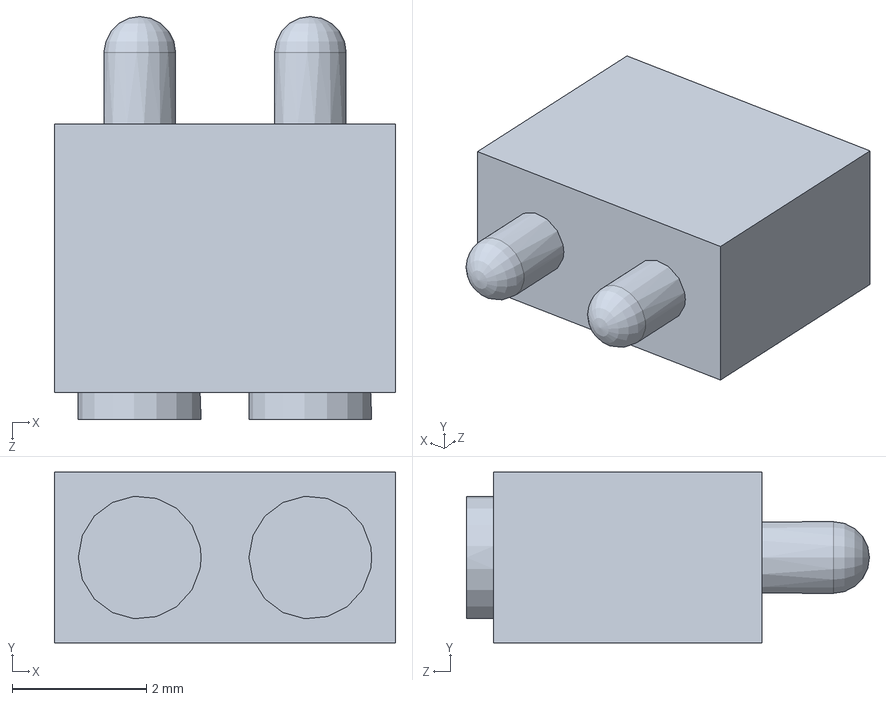
[picture p81: CAD file, 2020-04-06]
Medtronic/medtronic-pb560-ventilator-system-file-set-2/3D CAD Models/PB560 Assy/PRECI-DIP 811-S1-002-30-014101.SLDPRT
5.08 x 2.54 x 6.00 mm
