hesingh/ventilator/Medtronic/medtronic-pb560-ventilator-system-file-set-2/3D CAD Models/PB560 Assy/entretoise richco lg16.SLDPRT

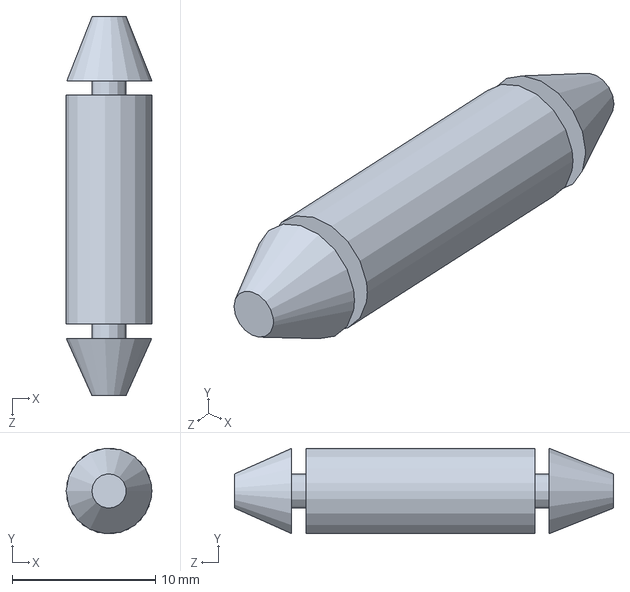
[picture p82: CAD file, 2020-04-06]
Medtronic/medtronic-pb560-ventilator-system-file-set-2/3D CAD Models/PB560 Assy/entretoise richco lg16.SLDPRT
6.00 x 5.97 x 26.5 mm
