hesingh/ventilator/Medtronic/medtronic-pb560-ventilator-system-file-set-2/3D CAD Models/PB560 Assy/boitier capteur pression asdx.SLDPRT

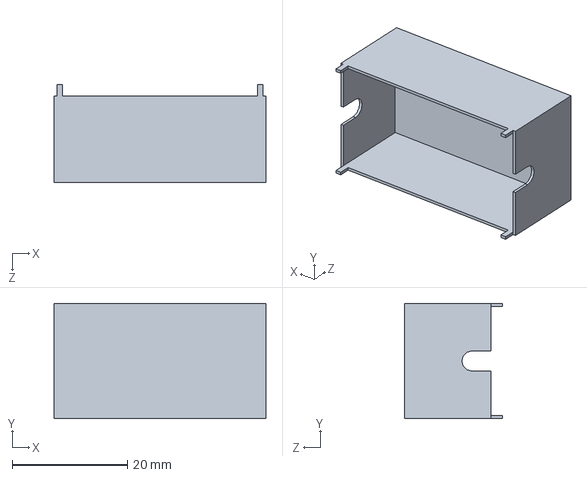
[picture p84: CAD file, 2020-04-06]
Medtronic/medtronic-pb560-ventilator-system-file-set-2/3D CAD Models/PB560 Assy/boitier capteur pression asdx.SLDPRT
36.8 x 20.0 x 17.0 mm
