hesingh/ventilator/Medtronic/medtronic-pb560-ventilator-system-file-set-2/3D CAD Models/PB560 Assy/39-28-5264.SLDPRT

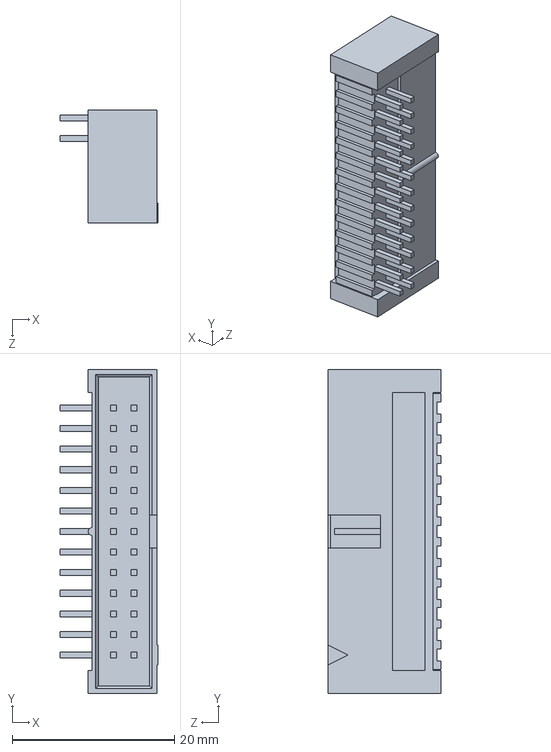
[picture p85: CAD file, 2020-04-06]
Medtronic/medtronic-pb560-ventilator-system-file-set-2/3D CAD Models/PB560 Assy/39-28-5264.SLDPRT
12.1 x 40.0 x 14.0 mm
