hesingh/ventilator/Medtronic/medtronic-pb560-ventilator-system-file-set-2/3D CAD Models/PB560 Assy/buzzer1.SLDPRT

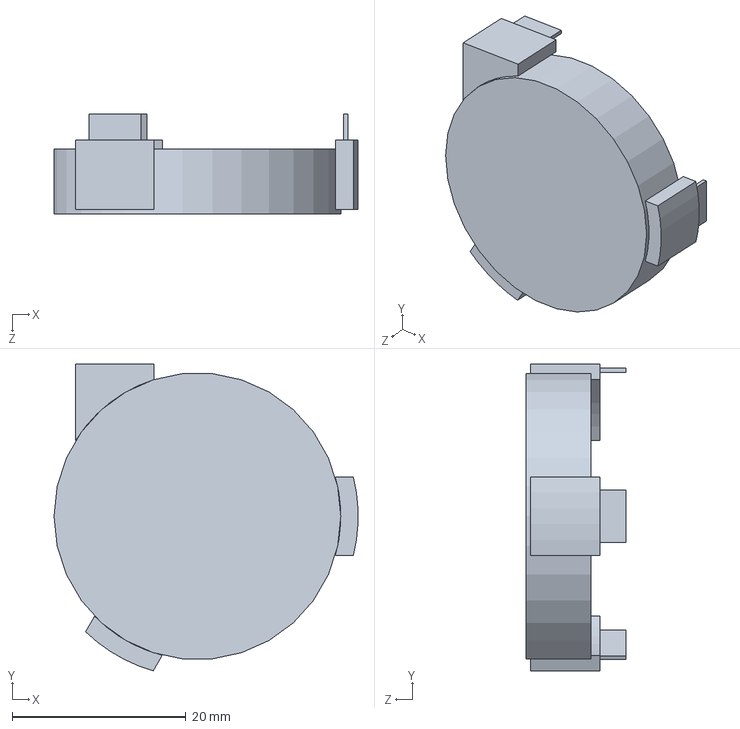
[picture p86: CAD file, 2020-04-06]
Medtronic/medtronic-pb560-ventilator-system-file-set-2/3D CAD Models/PB560 Assy/buzzer1.SLDPRT
35.0 x 35.3 x 11.5 mm
