hesingh/ventilator/Medtronic/medtronic-pb560-ventilator-system-file-set-2/3D CAD Models/PB560 Assy/Back End Cap.SLDPRT

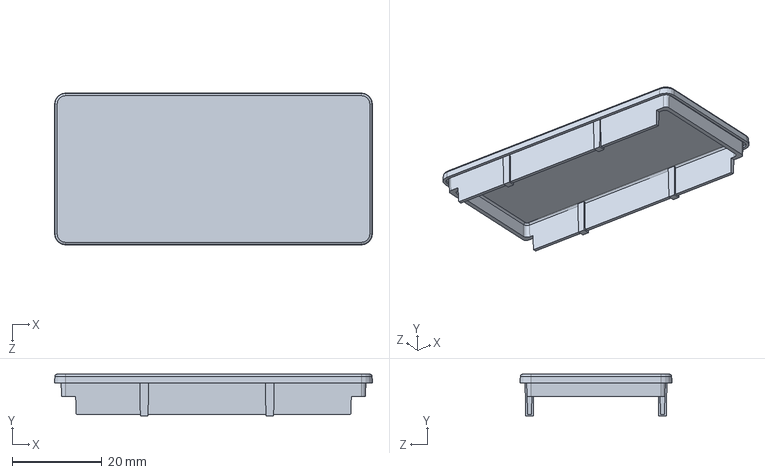
[picture p87: CAD file, 2020-04-06]
Medtronic/medtronic-pb560-ventilator-system-file-set-2/3D CAD Models/PB560 Assy/Back End Cap.SLDPRT
70.9 x 9.30 x 33.9 mm
