hesingh/ventilator/Medtronic/medtronic-pb560-ventilator-system-file-set-2/3D CAD Models/PB560 Assy/isolant adhésif capot capteur.SLDPRT

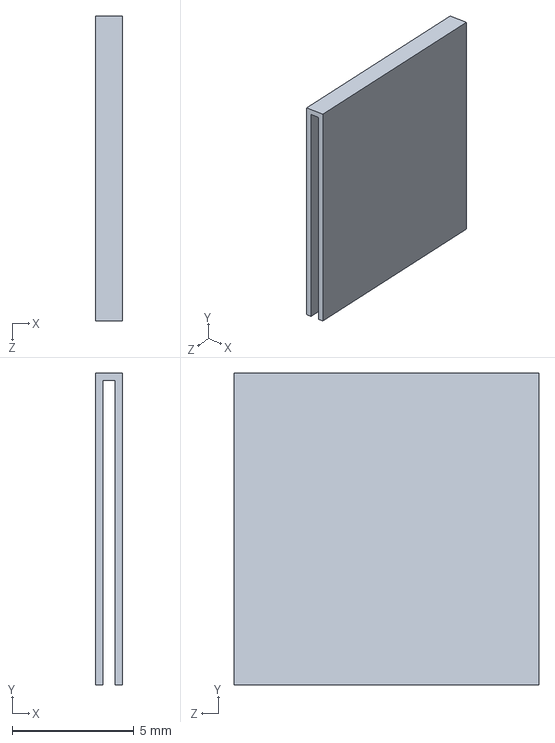
[picture p88: CAD file, 2020-04-06]
Medtronic/medtronic-pb560-ventilator-system-file-set-2/3D CAD Models/PB560 Assy/isolant adhésif capot capteur.SLDPRT
1.10 x 12.8 x 12.5 mm
