hesingh/ventilator/Medtronic/medtronic-pb560-ventilator-system-file-set-2/3D CAD Models/PB560 Assy/isolant adhésif ens afficheur.SLDPRT

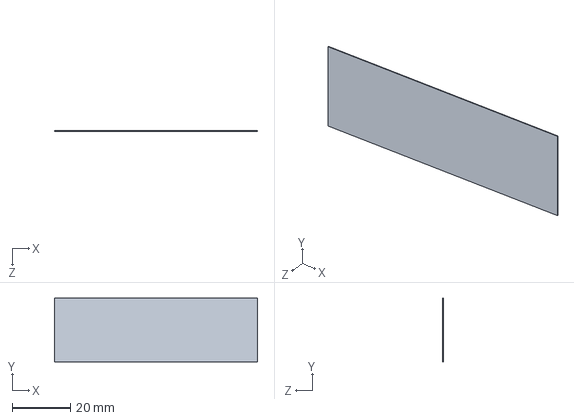
[picture p89: CAD file, 2020-04-06]
Medtronic/medtronic-pb560-ventilator-system-file-set-2/3D CAD Models/PB560 Assy/isolant adhésif ens afficheur.SLDPRT
70.0 x 22.0 x 0.2 mm
