hesingh/ventilator/Medtronic/medtronic-pb560-ventilator-system-file-set-2/3D CAD Models/PB560 Assy/tuyau alim vanne 1.6x4.8.SLDPRT

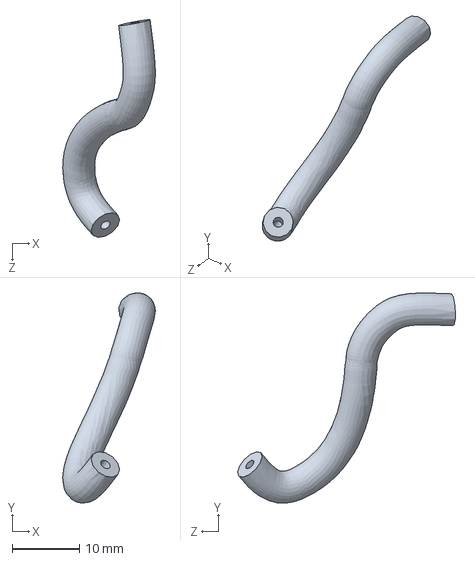
[picture p90: CAD file, 2020-04-06]
Medtronic/medtronic-pb560-ventilator-system-file-set-2/3D CAD Models/PB560 Assy/tuyau alim vanne 1.6x4.8.SLDPRT
13.8 x 31.3 x 32.5 mm
