hesingh/ventilator/Medtronic/medtronic-pb560-ventilator-system-file-set-2/3D CAD Models/PB560 Assy/new circuit support alimentation avec usb.SLDPRT

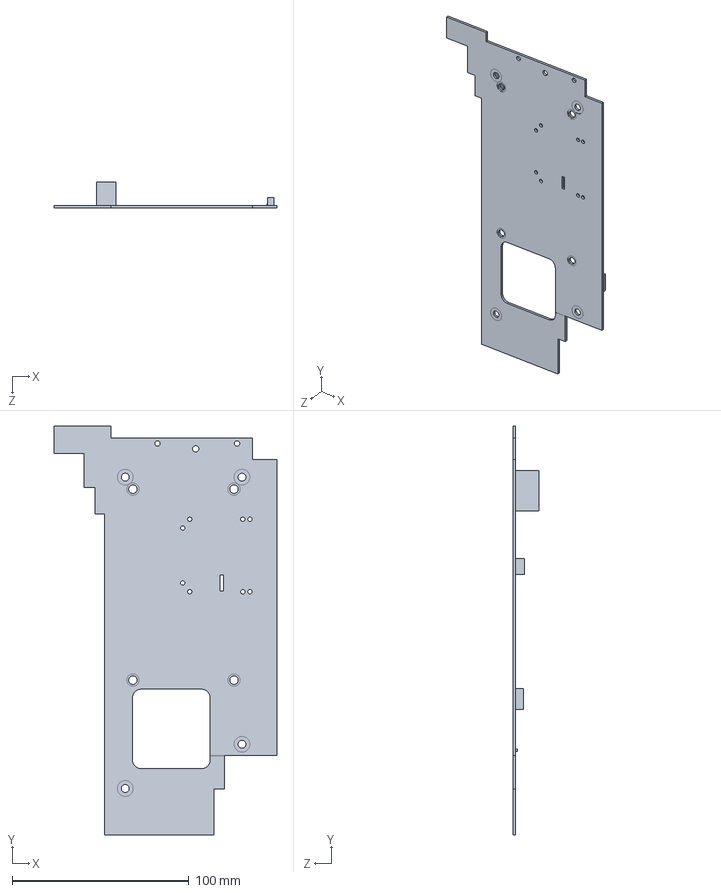
[picture p91: CAD file, 2020-04-06]
Medtronic/medtronic-pb560-ventilator-system-file-set-2/3D CAD Models/PB560 Assy/new circuit support alimentation avec usb.SLDPRT
125.9 x 231.2 x 14.8 mm
