hesingh/ventilator/Medtronic/medtronic-pb560-ventilator-system-file-set-2/3D CAD Models/PB560 Assy/capot 2 capteurs P phase 2.SLDPRT

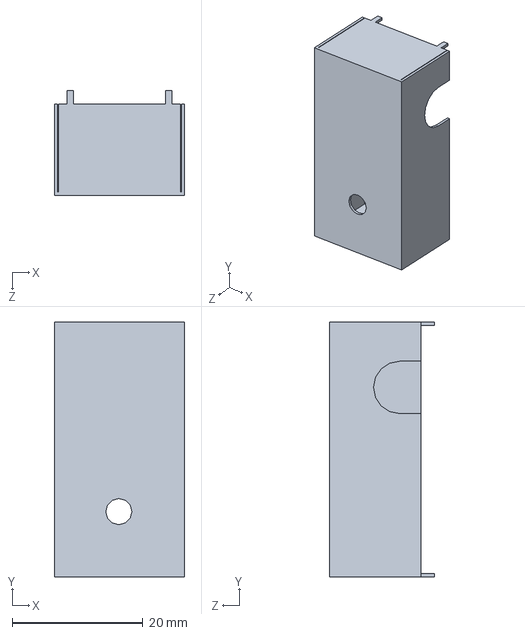
[picture p92: CAD file, 2020-04-06]
Medtronic/medtronic-pb560-ventilator-system-file-set-2/3D CAD Models/PB560 Assy/capot 2 capteurs P phase 2.SLDPRT
19.9 x 39.0 x 16.0 mm
