hesingh/ventilator/Medtronic/medtronic-pb560-ventilator-system-file-set-2/3D CAD Models/PB560 Assy/tuyau d├йbit expi P2.SLDPRT

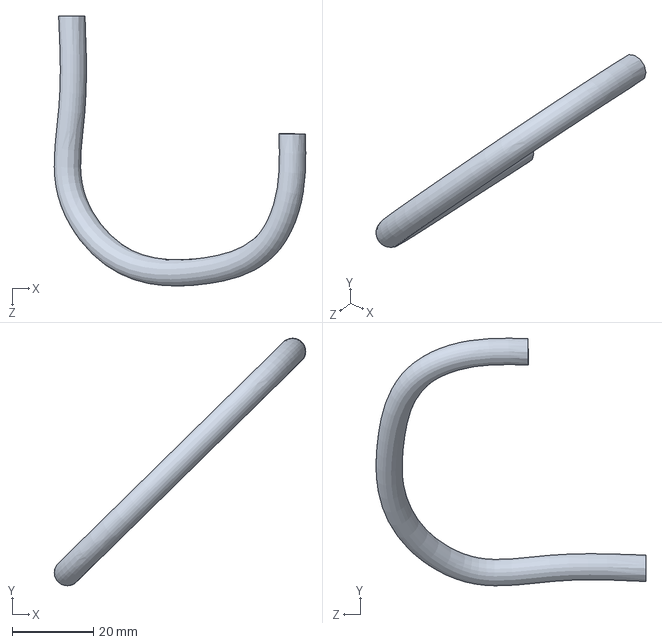
[picture p93: CAD file, 2020-04-06]
Medtronic/medtronic-pb560-ventilator-system-file-set-2/3D CAD Models/PB560 Assy/tuyau d├йbit expi P2.SLDPRT
61.8 x 60.8 x 66.3 mm
