hesingh/ventilator/Medtronic/medtronic-pb560-ventilator-system-file-set-2/3D CAD Models/PB560 Assy/Vis TCB M3-12 hexalobes acier zingué.sldprt

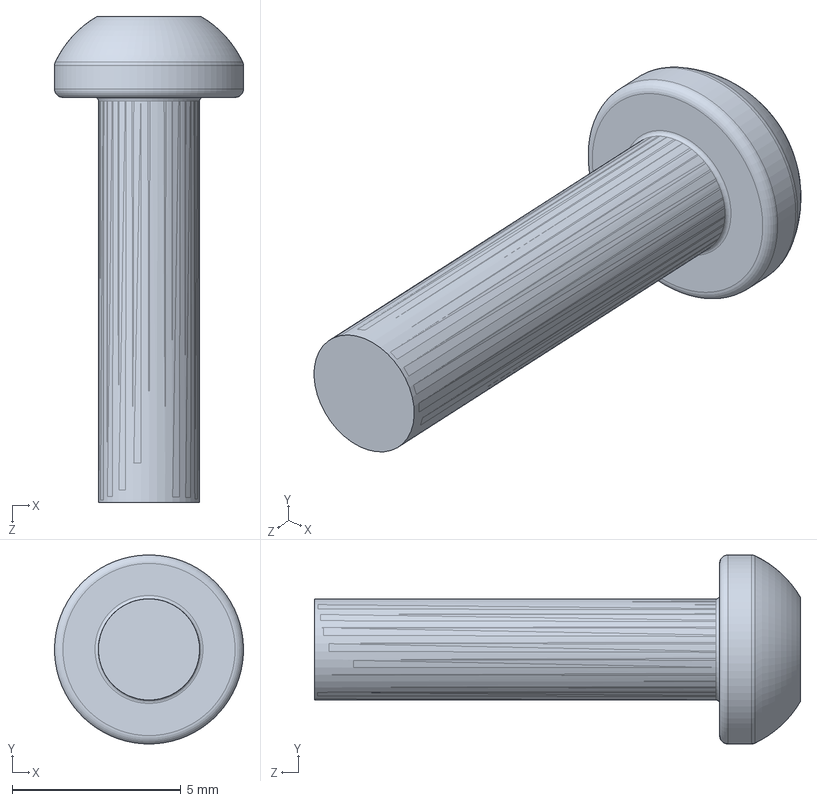
[picture p94: CAD file, 2020-04-06]
Medtronic/medtronic-pb560-ventilator-system-file-set-2/3D CAD Models/PB560 Assy/Vis TCB M3-12 hexalobes acier zingué.sldprt
5.60 x 5.60 x 14.4 mm
