hesingh/ventilator/Medtronic/medtronic-pb560-ventilator-system-file-set-2/3D CAD Models/PB560 Assy/Coude banjo M5-tuyau 6.SLDPRT

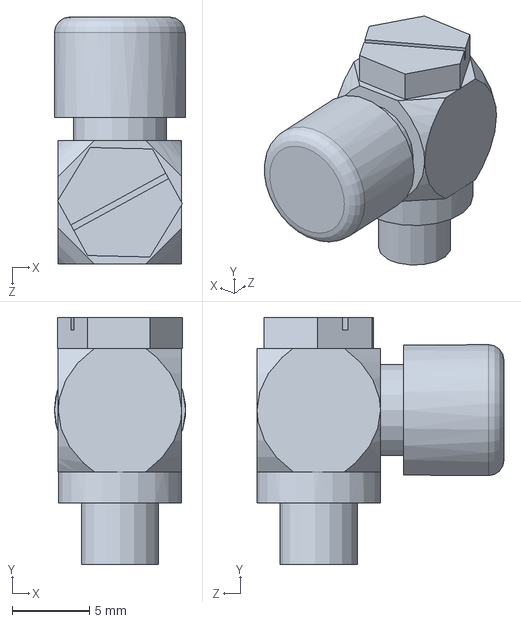
[picture p95: CAD file, 2020-04-06]
Medtronic/medtronic-pb560-ventilator-system-file-set-2/3D CAD Models/PB560 Assy/Coude banjo M5-tuyau 6.SLDPRT
8.50 x 16.0 x 16.0 mm
