hesingh/ventilator/Medtronic/medtronic-pb560-ventilator-system-file-set-2/3D CAD Models/PB560 Assy/condensateur C88.SLDPRT

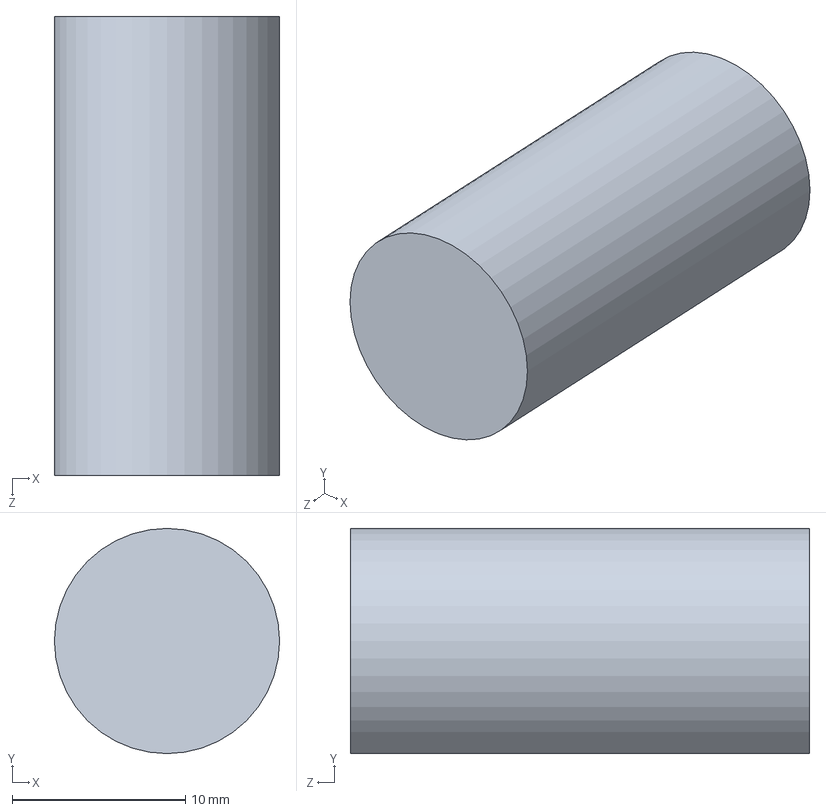
[picture p96: CAD file, 2020-04-06]
Medtronic/medtronic-pb560-ventilator-system-file-set-2/3D CAD Models/PB560 Assy/condensateur C88.SLDPRT
13.0 x 13.0 x 26.5 mm
