hesingh/ventilator/Medtronic/medtronic-pb560-ventilator-system-file-set-2/3D CAD Models/PB560 Assy/connecteur 12-30V.SLDPRT

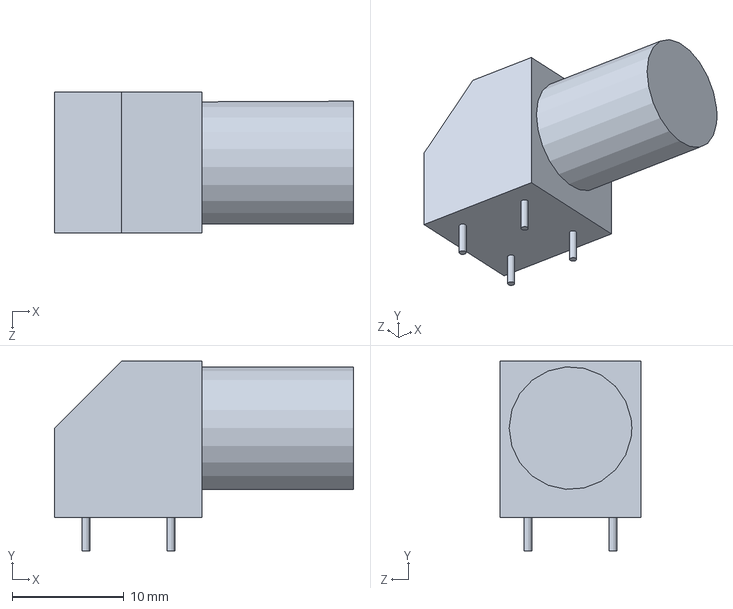
[picture p97: CAD file, 2020-04-06]
Medtronic/medtronic-pb560-ventilator-system-file-set-2/3D CAD Models/PB560 Assy/connecteur 12-30V.SLDPRT
26.8 x 17.0 x 12.6 mm
