hesingh/ventilator/Medtronic/medtronic-pb560-ventilator-system-file-set-2/3D CAD Models/PB560 Assy/MOLEX 43650-0212.SLDPRT

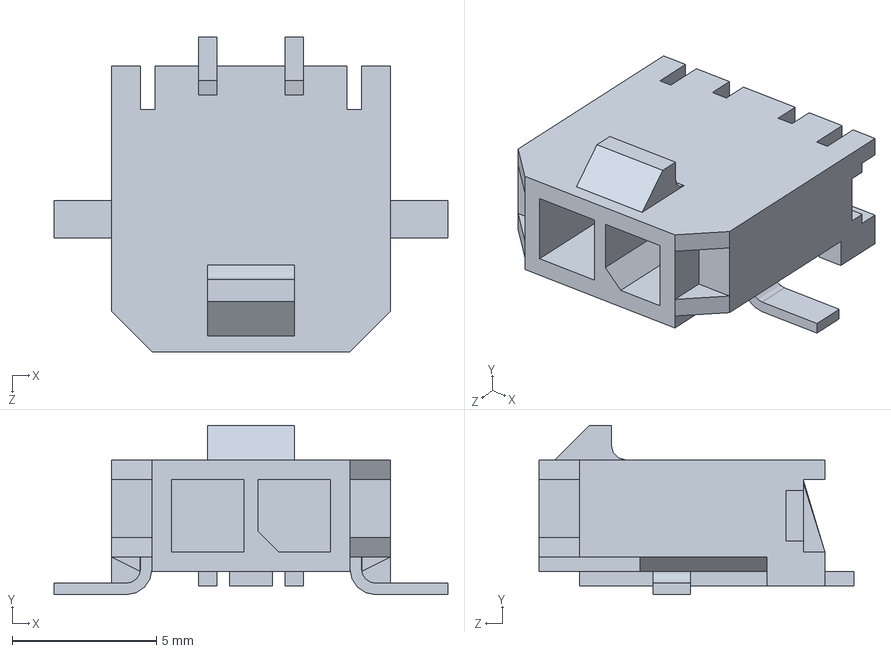
[picture p98: CAD file, 2020-04-06]
Medtronic/medtronic-pb560-ventilator-system-file-set-2/3D CAD Models/PB560 Assy/MOLEX 43650-0212.SLDPRT
13.6 x 5.87 x 10.9 mm
