hesingh/ventilator/Medtronic/medtronic-pb560-ventilator-system-file-set-2/3D CAD Models/PB560 Assy/embase cpu légendair phase 2 ind 01.SLDPRT

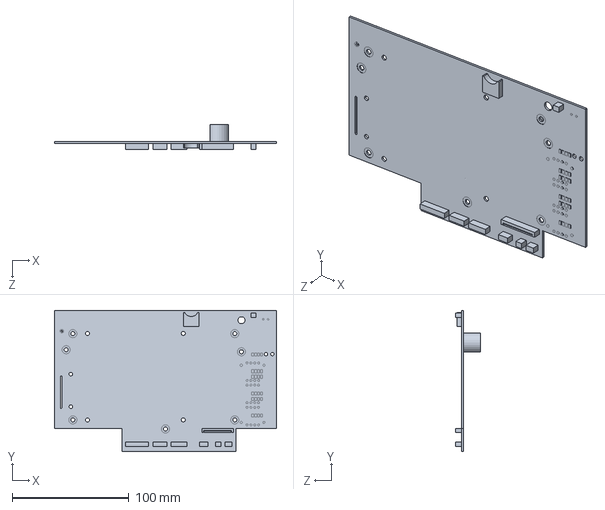
[picture p99: CAD file, 2020-04-06]
Medtronic/medtronic-pb560-ventilator-system-file-set-2/3D CAD Models/PB560 Assy/embase cpu légendair phase 2 ind 01.SLDPRT
190.0 x 121.0 x 21.0 mm
