hesingh/ventilator/Medtronic/medtronic-pb560-ventilator-system-file-set-2/3D CAD Models/PB560 Assy/INGUN GKS 913 305 230 A 15 02 S.SLDPRT

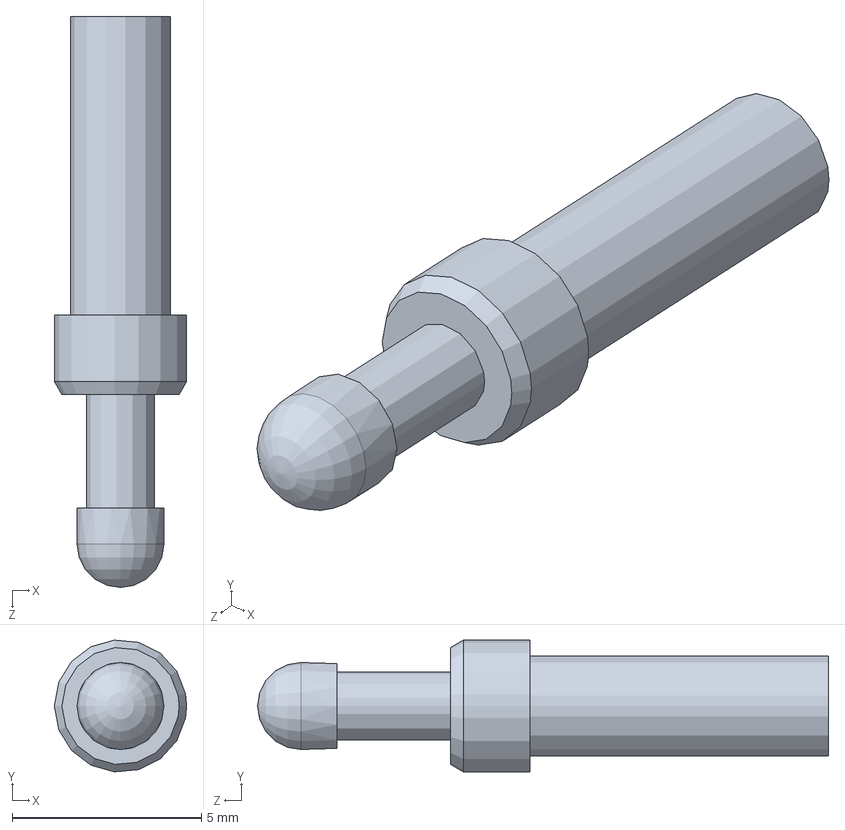
[picture p100: CAD file, 2020-04-06]
Medtronic/medtronic-pb560-ventilator-system-file-set-2/3D CAD Models/PB560 Assy/INGUN GKS 913 305 230 A 15 02 S.SLDPRT
3.50 x 3.49 x 15.1 mm
