hesingh/ventilator/Medtronic/medtronic-pb560-ventilator-system-file-set-2/3D CAD Models/PB560 Assy/entretoise hexa  m3x12.SLDPRT

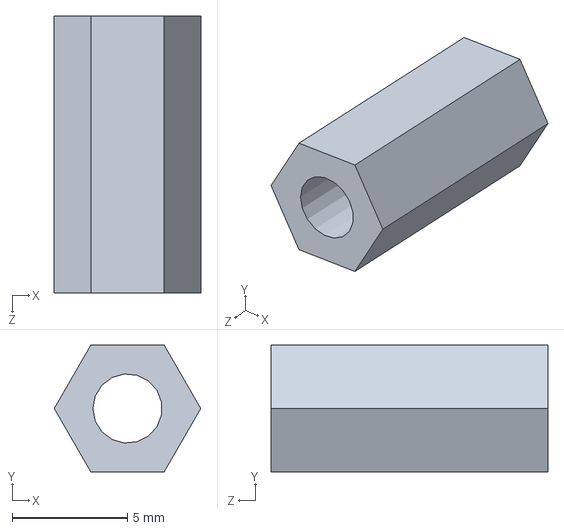
[picture p101: CAD file, 2020-04-06]
Medtronic/medtronic-pb560-ventilator-system-file-set-2/3D CAD Models/PB560 Assy/entretoise hexa m3x12.SLDPRT
6.35 x 5.50 x 12.0 mm
