hesingh/ventilator/Medtronic/medtronic-pb560-ventilator-system-file-set-2/3D CAD Models/PB560 Assy/26-48-1035.SLDPRT

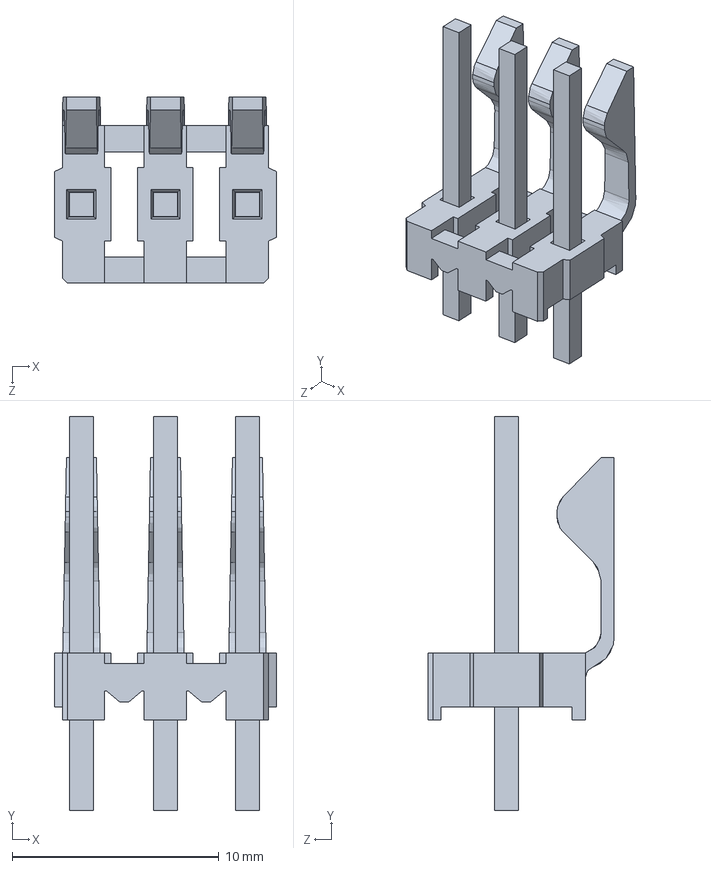
[picture p102: CAD file, 2020-04-06]
Medtronic/medtronic-pb560-ventilator-system-file-set-2/3D CAD Models/PB560 Assy/26-48-1035.SLDPRT
10.7 x 19.1 x 9.02 mm
