hesingh/ventilator/Medtronic/medtronic-pb560-ventilator-system-file-set-2/3D CAD Models/PB560 Assy/39-26-7265.SLDPRT

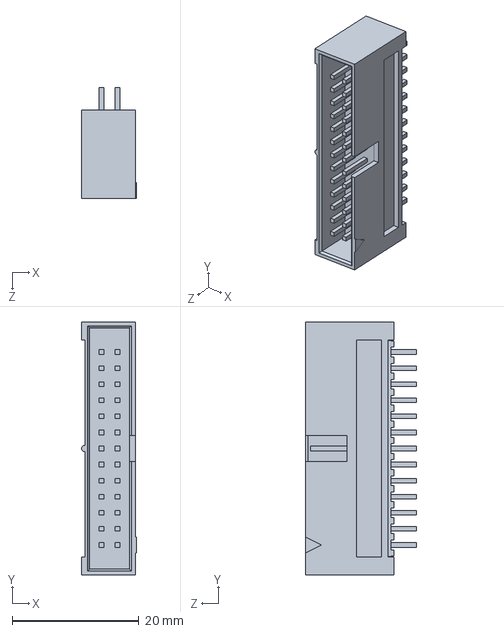
[picture p103: CAD file, 2020-04-06]
Medtronic/medtronic-pb560-ventilator-system-file-set-2/3D CAD Models/PB560 Assy/39-26-7265.SLDPRT
8.65 x 40.0 x 17.5 mm
