hesingh/ventilator/Medtronic/medtronic-pb560-ventilator-system-file-set-2/3D CAD Models/PB560 Assy/Exh Valve connector.SLDPRT

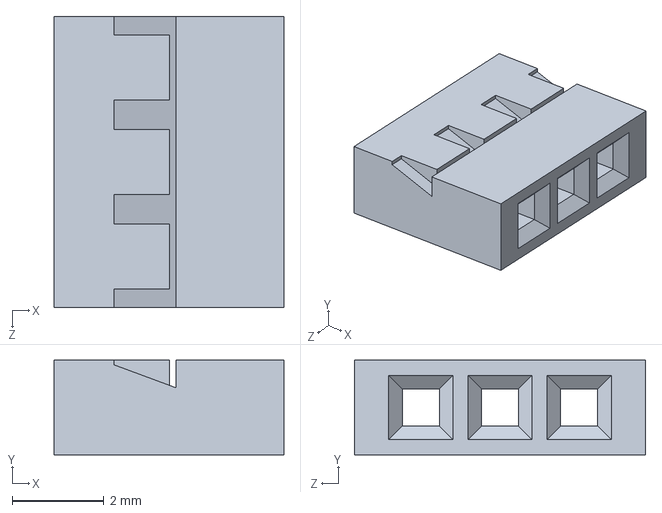
[picture p104: CAD file, 2020-04-06]
Medtronic/medtronic-pb560-ventilator-system-file-set-2/3D CAD Models/PB560 Assy/Exh Valve connector.SLDPRT
5.00 x 2.06 x 6.33 mm
