hesingh/ventilator/Medtronic/medtronic-pb560-ventilator-system-file-set-2/3D CAD Models/PB560 Assy/tuyau pression interne1.6x4.8.SLDPRT

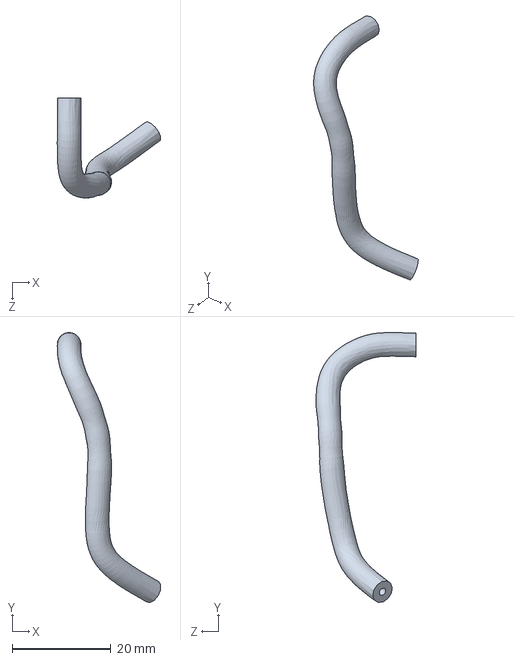
[picture p105: CAD file, 2020-04-06]
Medtronic/medtronic-pb560-ventilator-system-file-set-2/3D CAD Models/PB560 Assy/tuyau pression interne1.6x4.8.SLDPRT
21.0 x 54.7 x 20.3 mm
