hesingh/ventilator/Medtronic/medtronic-pb560-ventilator-system-file-set-2/3D CAD Models/PB560 Assy/22-27-2021.SLDPRT

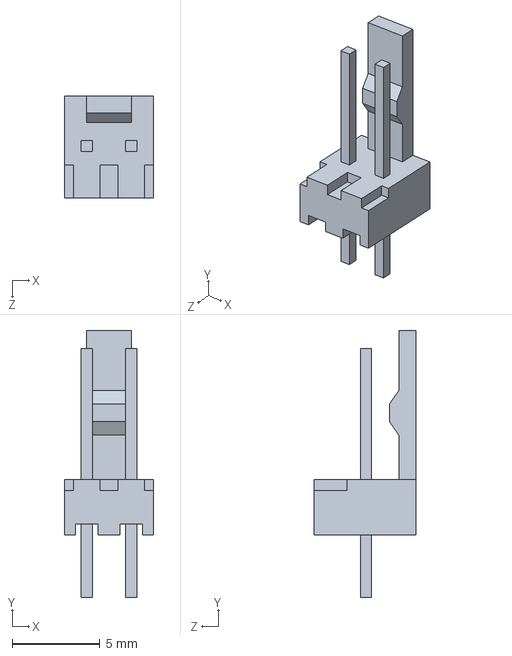
[picture p106: CAD file, 2020-04-06]
Medtronic/medtronic-pb560-ventilator-system-file-set-2/3D CAD Models/PB560 Assy/22-27-2021.SLDPRT
5.08 x 15.2 x 5.84 mm
