hesingh/ventilator/Medtronic/medtronic-pb560-ventilator-system-file-set-2/3D CAD Models/PB560 Assy/I0 179 Entretoise Mediane Legendair.SLDPRT

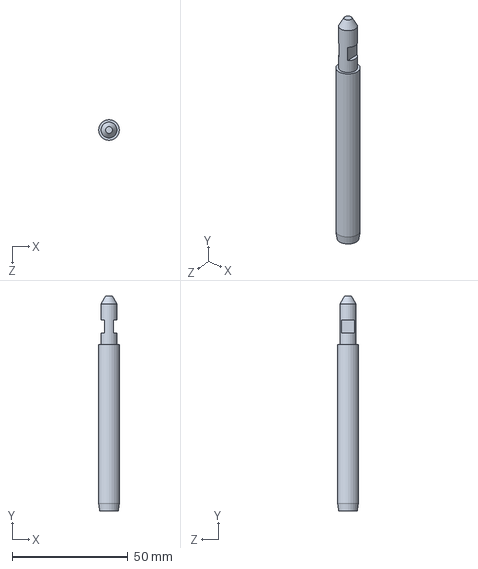
[picture p107: CAD file, 2020-04-06]
Medtronic/medtronic-pb560-ventilator-system-file-set-2/3D CAD Models/PB560 Assy/I0 179 Entretoise Mediane Legendair.SLDPRT
9.00 x 93.0 x 9.00 mm
