hesingh/ventilator/Medtronic/medtronic-pb560-ventilator-system-file-set-2/3D CAD Models/PB560 Assy/condensateur dia 10.SLDPRT

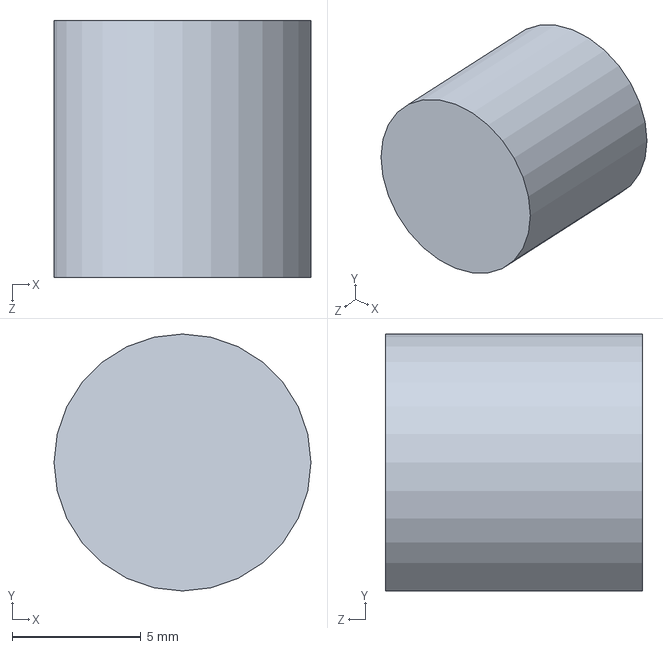
[picture p108: CAD file, 2020-04-06]
Medtronic/medtronic-pb560-ventilator-system-file-set-2/3D CAD Models/PB560 Assy/condensateur dia 10.SLDPRT
10.0 x 10.0 x 10.0 mm
