hesingh/ventilator/Medtronic/medtronic-pb560-ventilator-system-file-set-2/3D CAD Models/PB560 Assy/tuyau d├йbit inspi P2.SLDPRT

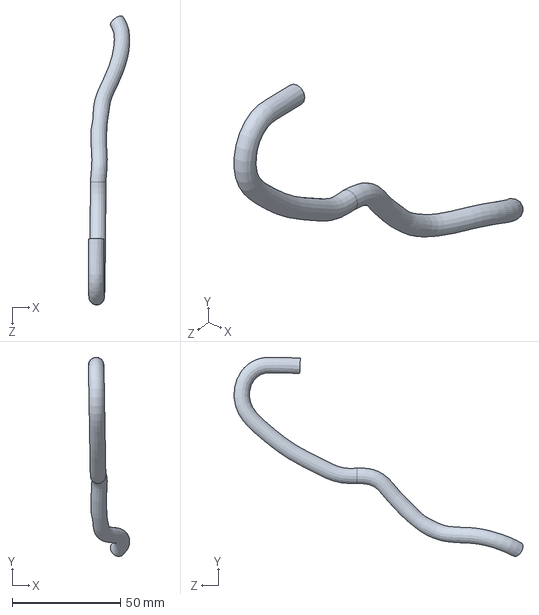
[picture p109: CAD file, 2020-04-06]
Medtronic/medtronic-pb560-ventilator-system-file-set-2/3D CAD Models/PB560 Assy/tuyau d├йbit inspi P2.SLDPRT
19.1 x 92.3 x 133.7 mm
