hesingh/ventilator/Medtronic/medtronic-pb560-ventilator-system-file-set-2/3D CAD Models/PB560 Assy/tuyau alim ballonnet1.6x4.8.SLDPRT

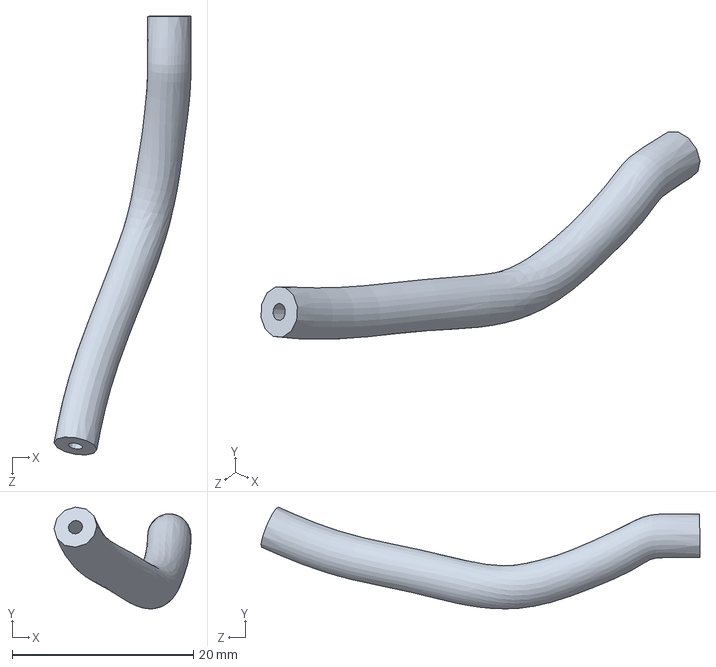
[picture p110: CAD file, 2020-04-06]
Medtronic/medtronic-pb560-ventilator-system-file-set-2/3D CAD Models/PB560 Assy/tuyau alim ballonnet1.6x4.8.SLDPRT
15.1 x 11.2 x 48.5 mm
