hesingh/ventilator/Medtronic/medtronic-pb560-ventilator-system-file-set-2/3D CAD Models/PB560 Assy/capteurpressionASDX001D44R.SLDPRT

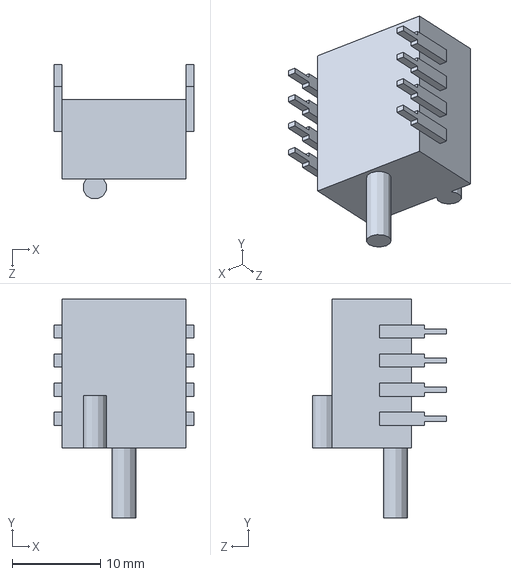
[picture p111: CAD file, 2020-04-06]
Medtronic/medtronic-pb560-ventilator-system-file-set-2/3D CAD Models/PB560 Assy/capteurpressionASDX001D44R.SLDPRT
15.8 x 24.8 x 15.2 mm
