hesingh/ventilator/Medtronic/medtronic-pb560-ventilator-system-file-set-2/3D CAD Models/PB560 Assy/Joint blindage conducteur 72x21xép4.SLDPRT

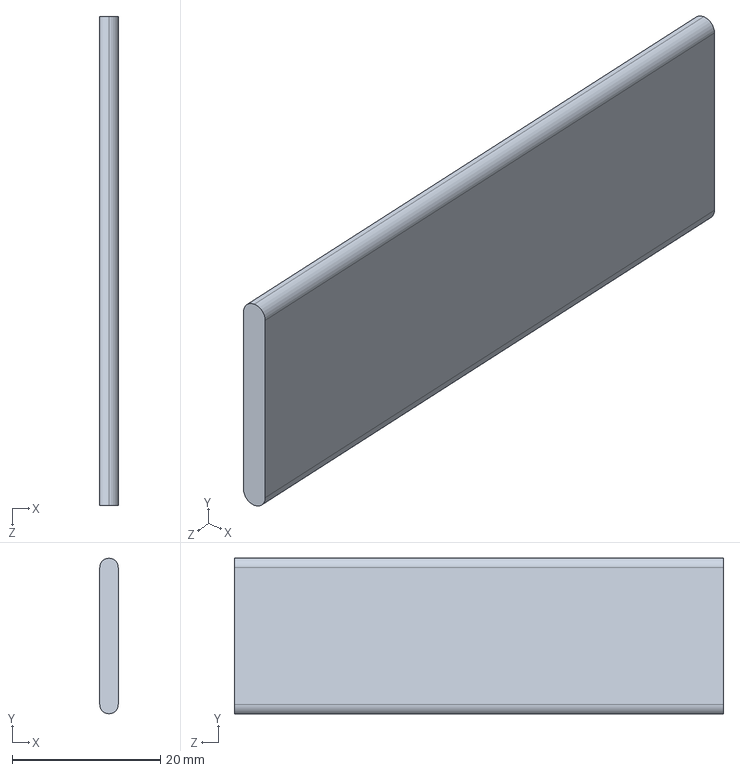
[picture p113: CAD file, 2020-04-06]
Medtronic/medtronic-pb560-ventilator-system-file-set-2/3D CAD Models/PB560 Assy/Joint blindage conducteur 72x21xép4.SLDPRT
2.50 x 21.0 x 66.0 mm
