hesingh/ventilator/Medtronic/medtronic-pb560-ventilator-system-file-set-2/3D CAD Models/PB560 Assy/tuyau d├йbit expi P1.SLDPRT

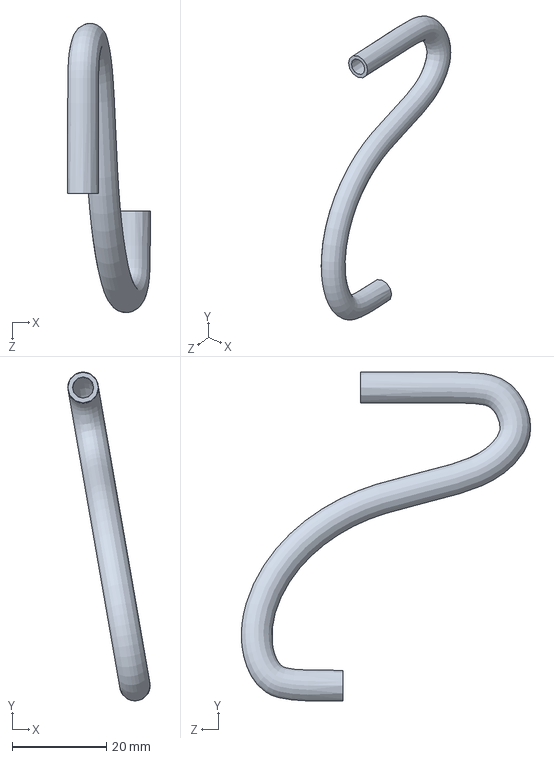
[picture p114: CAD file, 2020-04-06]
Medtronic/medtronic-pb560-ventilator-system-file-set-2/3D CAD Models/PB560 Assy/tuyau d├йbit expi P1.SLDPRT
17.5 x 69.7 x 61.3 mm
