hesingh/ventilator/Medtronic/medtronic-pb560-ventilator-system-file-set-2/3D CAD Models/PB560 Assy/capteurpressionASDX100D44R.SLDPRT

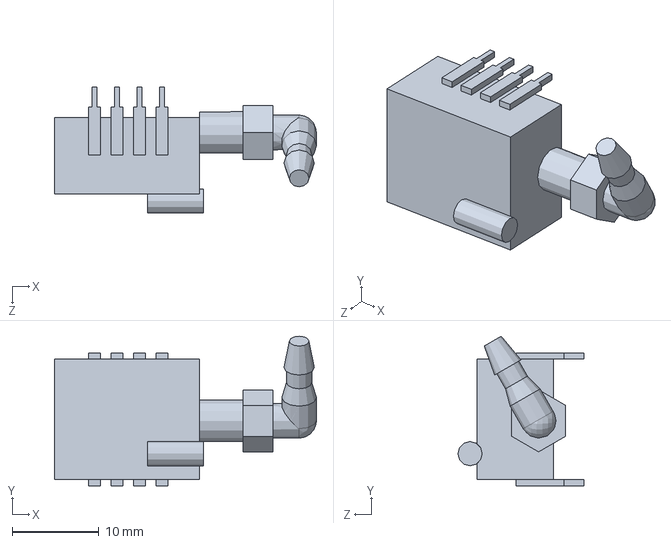
[picture p116: CAD file, 2020-04-06]
Medtronic/medtronic-pb560-ventilator-system-file-set-2/3D CAD Models/PB560 Assy/capteurpressionASDX100D44R.SLDPRT
30.2 x 17.2 x 14.5 mm
