hesingh/ventilator/Medtronic/medtronic-pb560-ventilator-system-file-set-2/3D CAD Models/PB560 Assy/tuyau d├йbit inspi P1.SLDPRT

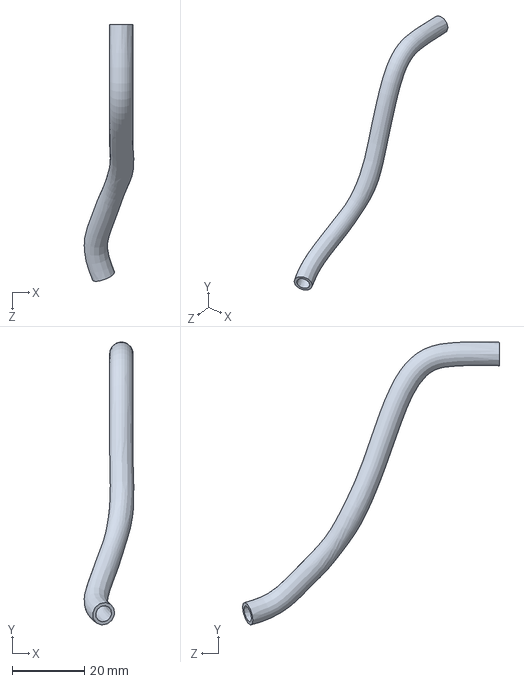
[picture p117: CAD file, 2020-04-06]
Medtronic/medtronic-pb560-ventilator-system-file-set-2/3D CAD Models/PB560 Assy/tuyau d├йbit inspi P1.SLDPRT
13.7 x 78.2 x 71.1 mm
