hesingh/ventilator/Medtronic/medtronic-pb560-ventilator-system-file-set-2/3D CAD Models/PB560 Assy/tuyau O2 entrée vanne.SLDPRT

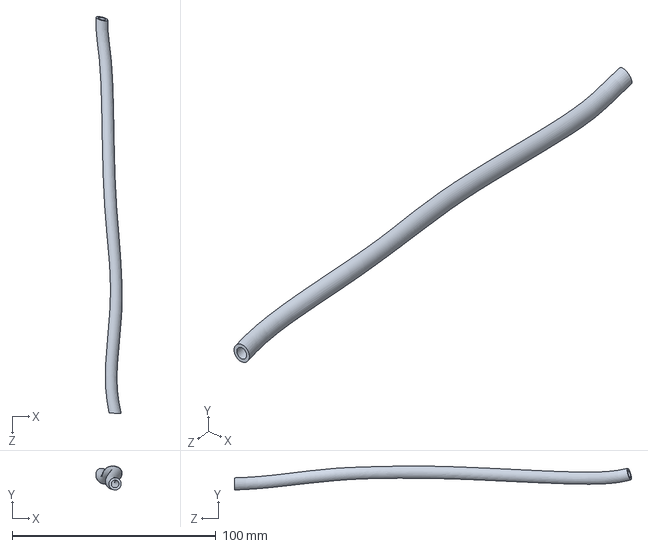
[picture p118: CAD file, 2020-04-06]
Medtronic/medtronic-pb560-ventilator-system-file-set-2/3D CAD Models/PB560 Assy/tuyau O2 entrée vanne.SLDPRT
12.9 x 11.8 x 195.1 mm
