hesingh/ventilator/Medtronic/medtronic-pb560-ventilator-system-file-set-2/3D CAD Models/PB560 Assy/22-05-7028.SLDPRT

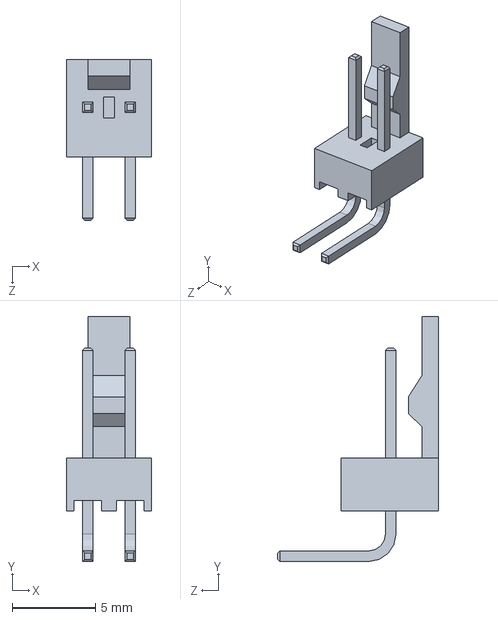
[picture p119: CAD file, 2020-04-06]
Medtronic/medtronic-pb560-ventilator-system-file-set-2/3D CAD Models/PB560 Assy/22-05-7028.SLDPRT
5.08 x 14.7 x 9.65 mm
