hesingh/ventilator/Medtronic/medtronic-pb560-ventilator-system-file-set-2/3D CAD Models/PB560 Assy/tuyau alim vanne 4x6.SLDPRT

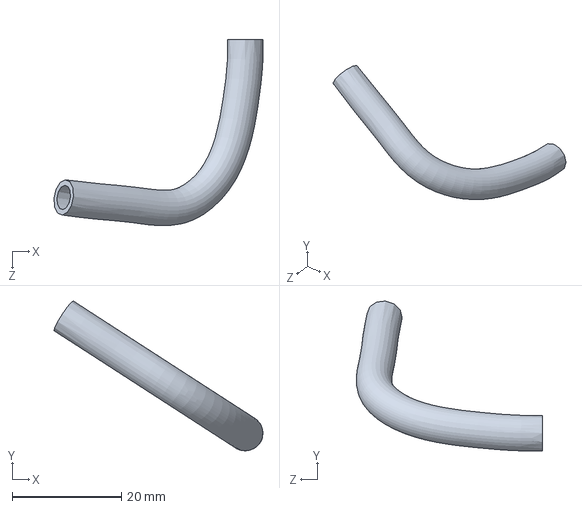
[picture p120: CAD file, 2020-04-06]
Medtronic/medtronic-pb560-ventilator-system-file-set-2/3D CAD Models/PB560 Assy/tuyau alim vanne 4x6.SLDPRT
38.2 x 27.4 x 34.1 mm
