hesingh/ventilator/Medtronic/medtronic-pb560-ventilator-system-file-set-2/3D CAD Models/PB560 Assy/connect molex 22-01-2025.SLDPRT

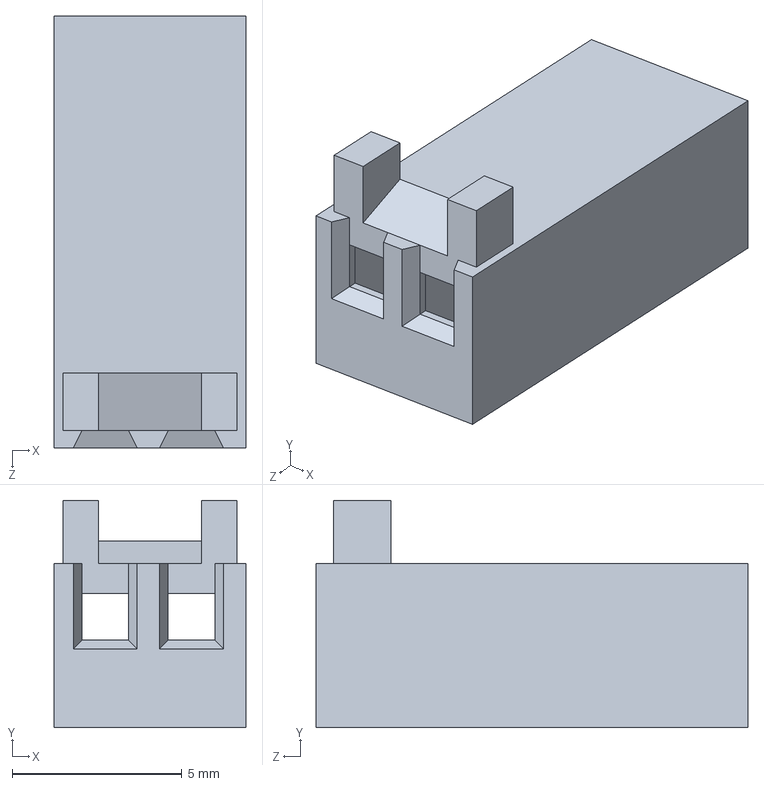
[picture p121: CAD file, 2020-04-06]
Medtronic/medtronic-pb560-ventilator-system-file-set-2/3D CAD Models/PB560 Assy/connect molex 22-01-2025.SLDPRT
5.64 x 6.68 x 12.7 mm
