hesingh/ventilator/Medtronic/medtronic-pb560-ventilator-system-file-set-2/3D CAD Models/PB560 Assy/connecteur USB miniB.SLDPRT

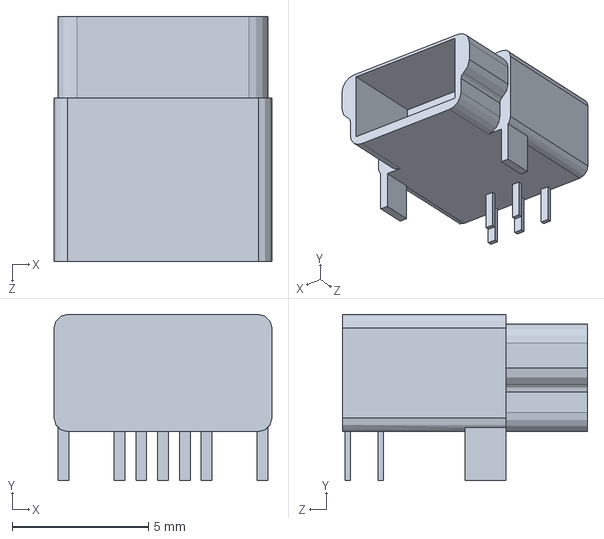
[picture p122: CAD file, 2020-04-06]
Medtronic/medtronic-pb560-ventilator-system-file-set-2/3D CAD Models/PB560 Assy/connecteur USB miniB.SLDPRT
8.00 x 6.10 x 9.00 mm
