hesingh/ventilator/Medtronic/medtronic-pb560-ventilator-system-file-set-2/3D CAD Models/PB560 Assy/connecteur USB A vertical.SLDPRT

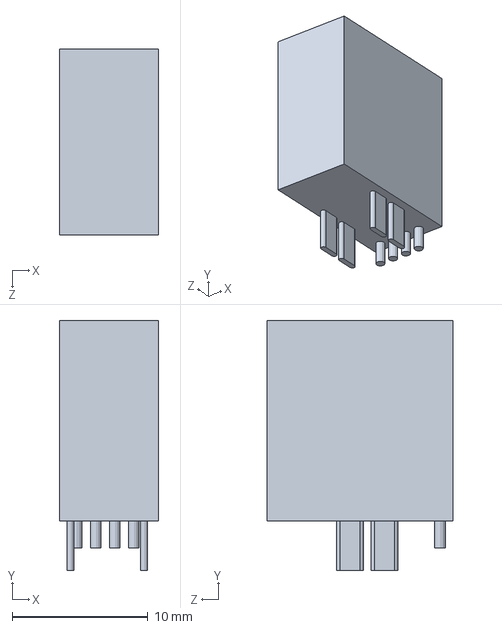
[picture p123: CAD file, 2020-04-06]
Medtronic/medtronic-pb560-ventilator-system-file-set-2/3D CAD Models/PB560 Assy/connecteur USB A vertical.SLDPRT
7.25 x 18.4 x 13.7 mm
