hesingh/ventilator/Medtronic/medtronic-pb560-ventilator-system-file-set-2/3D CAD Models/PB560 Assy/09-48-4128.SLDPRT

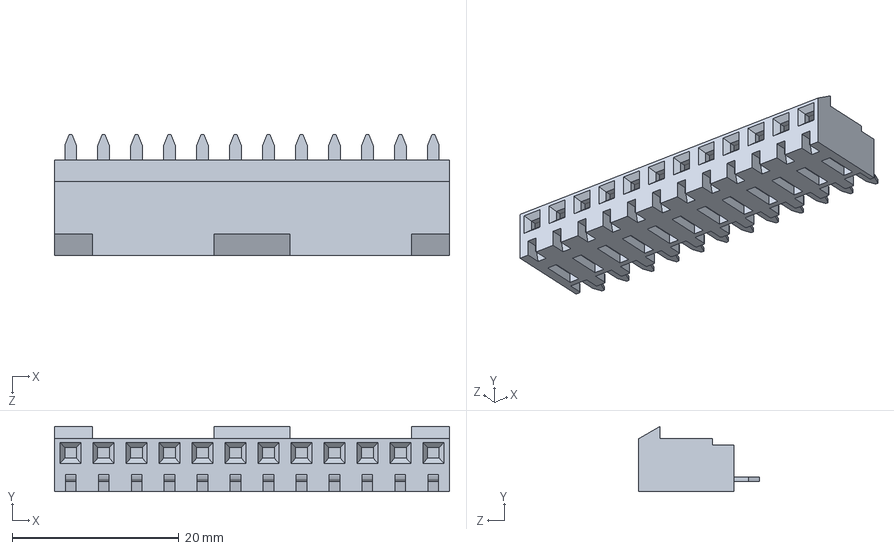
[picture p124: CAD file, 2020-04-06]
Medtronic/medtronic-pb560-ventilator-system-file-set-2/3D CAD Models/PB560 Assy/09-48-4128.SLDPRT
47.4 x 7.82 x 14.5 mm
