hesingh/ventilator/Medtronic/medtronic-pb560-ventilator-system-file-set-2/3D CAD Models/PB560 Assy/I0 178 Entretoise AR Legendair.SLDPRT

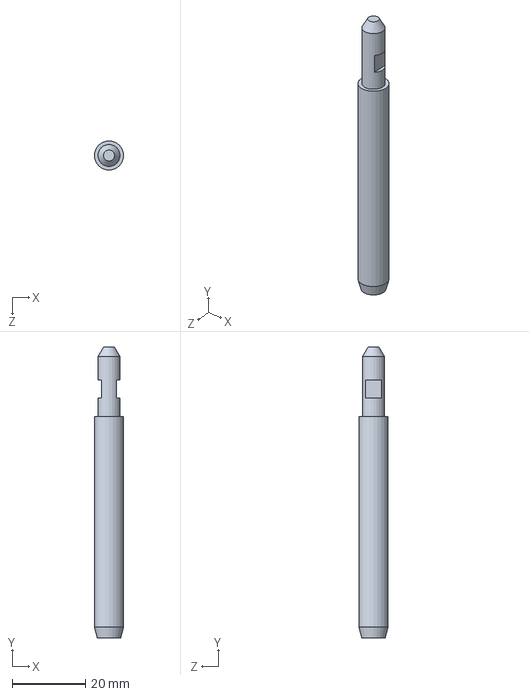
[picture p125: CAD file, 2020-04-06]
Medtronic/medtronic-pb560-ventilator-system-file-set-2/3D CAD Models/PB560 Assy/I0 178 Entretoise AR Legendair.SLDPRT
8.00 x 79.5 x 8.00 mm
