hesingh/ventilator/Medtronic/medtronic-pb560-ventilator-system-file-set-2/3D CAD Models/PB560 Assy/feritte nappe afficheur.SLDPRT

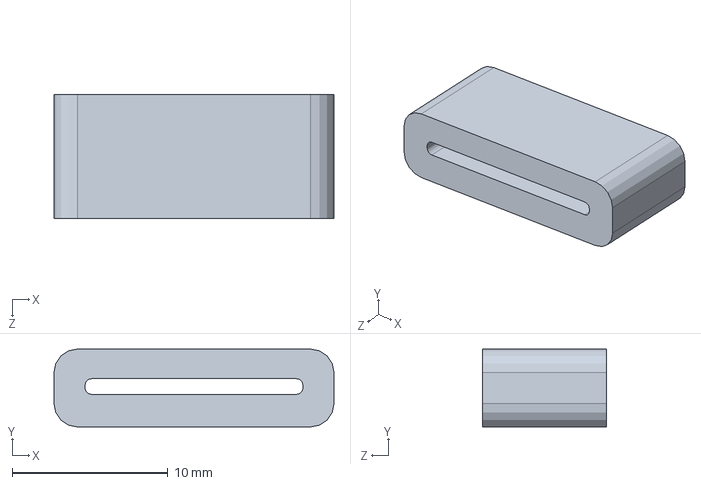
[picture p126: CAD file, 2020-04-06]
Medtronic/medtronic-pb560-ventilator-system-file-set-2/3D CAD Models/PB560 Assy/feritte nappe afficheur.SLDPRT
18.0 x 5.00 x 8.00 mm
