hesingh/ventilator/Medtronic/medtronic-pb560-ventilator-system-file-set-2/3D CAD Models/PB560 Assy/HIROSE HR25A-7R-8S.SLDPRT

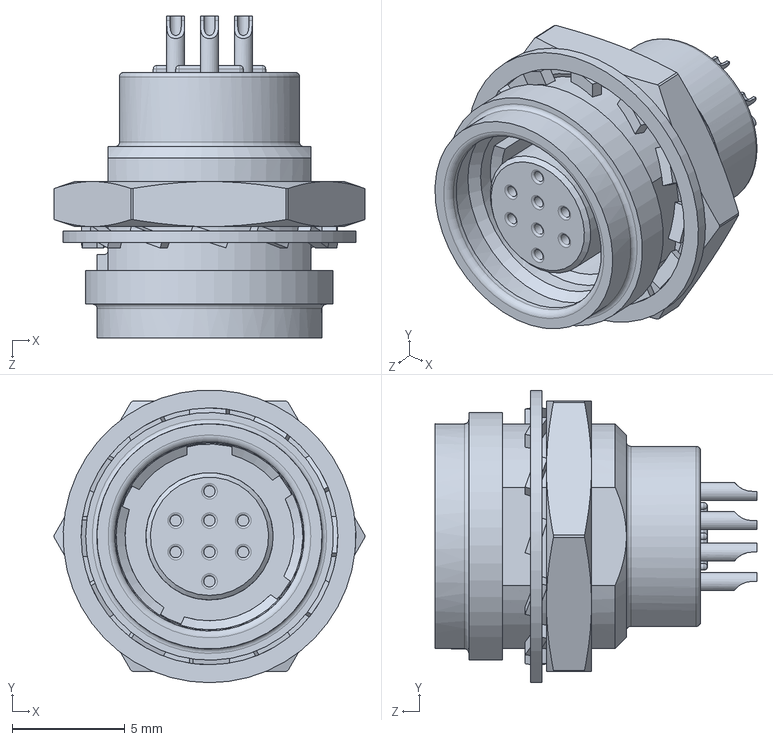
[picture p127: CAD file, 2020-04-06]
Medtronic/medtronic-pb560-ventilator-system-file-set-2/3D CAD Models/PB560 Assy/HIROSE HR25A-7R-8S.SLDPRT
13.8 x 13.0 x 14.3 mm
