hesingh/ventilator/Medtronic/medtronic-pb560-ventilator-system-file-set-2/3D CAD Models/PB560 Assy/embase cpu.SLDPRT

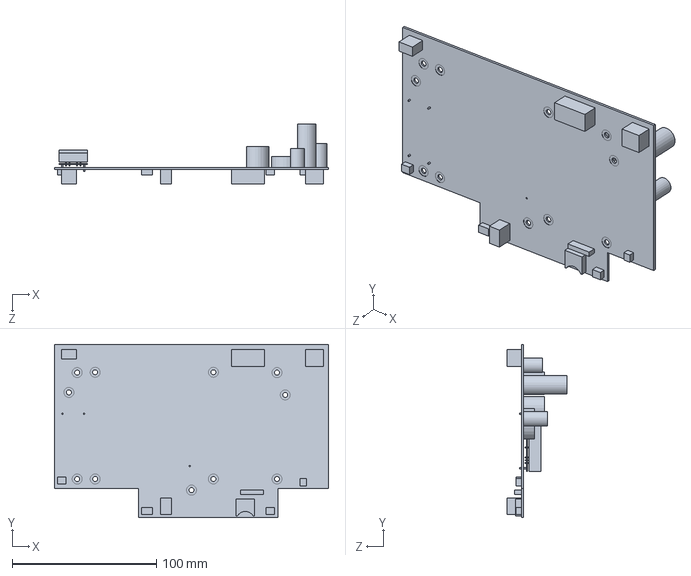
[picture p128: CAD file, 2020-04-06]
Medtronic/medtronic-pb560-ventilator-system-file-set-2/3D CAD Models/PB560 Assy/embase cpu.SLDPRT
190.0 x 120.0 x 41.5 mm
