hesingh/ventilator/Medtronic/medtronic-pb560-ventilator-system-file-set-2/3D CAD Models/PB560 Assy/connect molex 22-01-2087.SLDPRT

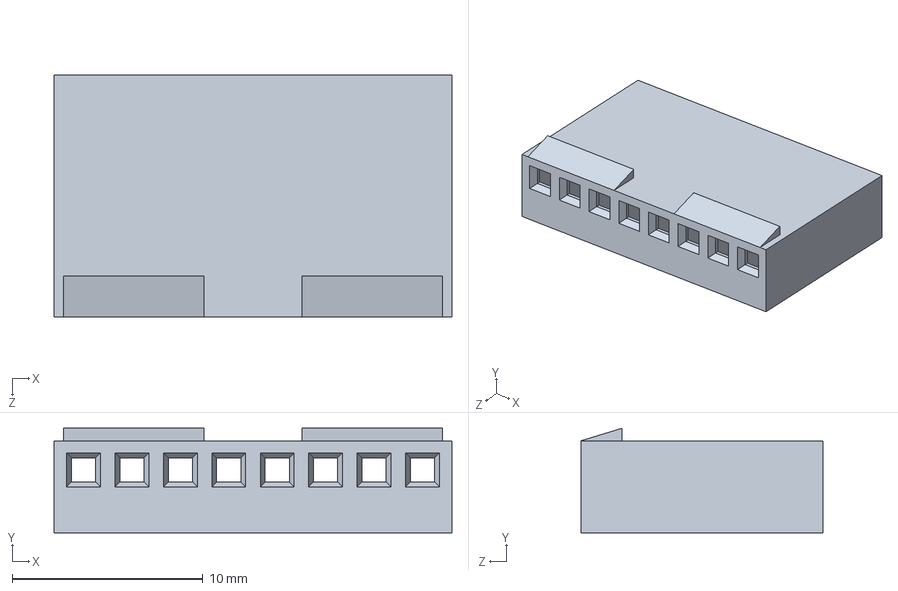
[picture p129: CAD file, 2020-04-06]
Medtronic/medtronic-pb560-ventilator-system-file-set-2/3D CAD Models/PB560 Assy/connect molex 22-01-2087.SLDPRT
20.9 x 5.49 x 12.7 mm
