hesingh/ventilator/Medtronic/medtronic-pb560-ventilator-system-file-set-2/3D CAD Models/PB560 Assy/MOLEX 43645 0200.SLDPRT

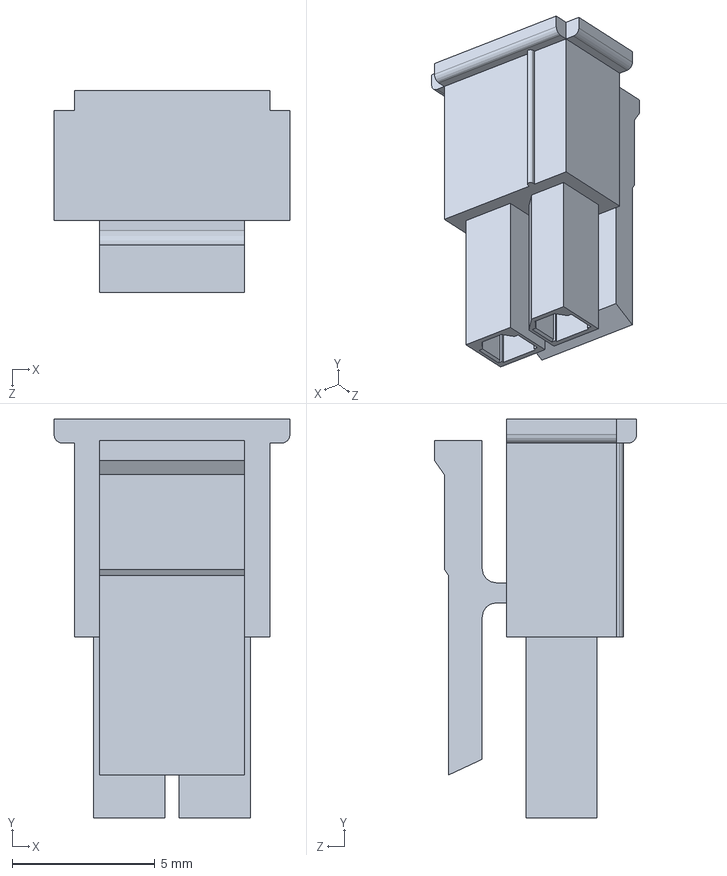
[picture p130: CAD file, 2020-04-06]
Medtronic/medtronic-pb560-ventilator-system-file-set-2/3D CAD Models/PB560 Assy/MOLEX 43645 0200.SLDPRT
8.28 x 14.0 x 7.10 mm
