hesingh/ventilator/Medtronic/pb560-vent-files-4/Risk Documents/10037183W00.xlsx

Sheet: General Information
 |  |  |  | Document #: | 10037183 | Revision: | W
1 | Purpose and Scope
 | The purpose of this analysis is to identify hazards associated with the intended use, as well as, reasonably foreseeable misuse of the medical device and any potentially resulting harms in accordance with EN ISO 14971.
 | This document covers the patient, all intended users, and the device itself during manufacture, use, servicing, transportation, and storage of the medical device.
2 | Assumptions:
 | This hazard analysis assumes that the PB560, PB540, PB520 and PowerPack shall only be operated by qualified, properly trained personnel (i.e. used by prescription only). The users of thePB560, PB540, PB520 and PowerPack include: clinicians, physicians, nurses, homecare providers, patients and patient’s families.
 | Per the Risk Management Plan, 10035479, risk management activities are retrospective to comply with EN ISO 14971:2012, and Remediation Plan for Risk Management Documents 10130032, and shall be carried out in accordance with MITG Risk Management Method GS10004411. Because this is retrospective, the columns in the Product Risk Analysis table below that call for the 'Pre-mitigation risk assessment' will not be populated. The 'Post mitigation' (risidual) risk assessment columns will be the only ones used because the mitigations have already been applied. The PB500 Risk Assessment Team considered the probability of both P1 and P2 occurring together without defining each other separately. The residual probability of harm was arrived by combining engineering design expertise with data from a 3 years period of PB500 customer complaints.
 | Within this file cells that have been shaded brown represent the start of the hazard. All causes, harms and mitigations listed below this line are appropriate for the hazard. P1, P2 and risk zones are correct for the row associated with the 'harm x severity' found on the same row. Grey shading has been used to block out unused cells and are considered equivalent to 'not applicable' for documentation purposes.
3 | Intended Users and Use Environment
 | · Risk Management activities are retrospective to comply with EN ISO 14971:2012 [R5] and Remediation Plan for Risk Management Documents 10130032 [R10], and shall be carried out in accordance with MITG Risk Management Method GS10004411 [R1]. | Intended Users and Use Environment:
 |  | The ventilator is a restricted medical device intended for use by qualified, trained personnel under the direction of a doctor and may be operated by clinicians, physicians, nurses, homecare providers, patients and patient’s families.
 | 3.2 | The intended use environments for the above personnel include:
 |  | The PB500 ventilator is intended for use in institutional, home, and portable settings. The ventilator is not for use as an emergency transport ventilator.
 | 3.3 | Intended Patient Population:
 |  | The PB500 series ventilators are indicated for the continuous or intermittent mechanical ventilatory support of patients weighing at least 11 lbs (5 kg) who require mechanical ventilation delivered invasively or non-invasively.
4 | System Definition/Exclusions:
 | N/A
5 | Characteristics Related to Safety
 | 5.1 | Primary Operating Function(s):
 |  | The PB500 ventilators are applicable for adult and pediatric patients who require the following general types of invasive (via endotracheal and tracheostomy tubes) or non-invasive (via mouthpiece, nasal mask or full face mask) ventilatory support, as prescribed by an attending doctor: • Positive Pressure ventilation • Assist/Control, SIMV, or CPAP modes of ventilation • Breath types including Volume Control, Pressure Control, and Pressure Support PB560 also supports volume control ventilation
 | 5.2 | Frequently Used Function(s):
 |  | N/A
 | 5.3 | Essential Performance:
 |  | Essential Performance for the PB560 ventilator is defined within RE00147193.
6 | Standard Revisions:
 | The standards referenced in the Risk Anaysis Chart correspond with the following standard revisions:
 | EN 60601-1:2006 + A12:2014 |  | Medical Electrical Equipment - Part 1: General Requirements for Safety - Collateral Standard - Safety Requirements for Medical Electrical Systems
 | EN ISO 10993-1:2009 |  | Biological Evaluation of medical devices Part 1: Evaluation and testing within a risk management process
 | EN 10651-2:2009 |  | Lung Ventilators for Medical Use- Particular Requirements for Basic Safety and Essential Performance Part 2: Home Care Ventilators for Ventilator-Dependent Patient
 | IEC 60601-1-11:2015 IEC 60601-1-11:2015 |  | Medical electrical equipment – Part 1-11: General requirements for basic safety and essential performance – Collateral Standard: Requirements for medical electrical equipment and medical electrical systems used in the home healthcare environment
 | EN 60601-1-6:2010 + A1:2014 IEC 60601-1-6: 2010 +A1:2013 |  | Medical Electrical Equipment - Part 1: General Requirements for Safety -2- Collateral standard: Usability
 | EN 60601-1-8:2007 + A11:2017 IEC 60601-1-8:2006 + A1:2012 |  | General Requirements, tests and guidance for alarm systems in medical electrical equipment and medical electrical systems
 | EN ISO 80601-2-55:2011 |  | Medical electrical equipment Part 2-55: Particular requirements for basic safety and essential performance of respiratory gas monitor
 | EN ISO 80601-2-72:2015 |  | Medical Electrical Equipment - Part 2-72:Particular requirements for basic safety and essential performance of home healthcare environments ventilator-dependent patients
 | EN 60601-1-2:2015 IEC 60601-1-2:2014 |  | Medical Electrical Equipment - Part 1-2: General requirements for basic safety and essential performance - Collateral Standard: Electromagnetic Disturbances - requirements and tests
7 | PB560 Worst case Testing
 | Rationale for Worst Case Tubing: The characteristics of the patient circuit impact ventilator’s performance in multiple ways by dynamic interaction with the ventilator’s pneumatic system as well as through thermodynamic and fluid mechanic phenomena pursuant to varying patterns and dynamic characteristics of gas flow through the patient-ventilator system. The accuracy of the measurement of timing and magnitude of pressure and flow changes for detection are dependent on tubing characteristics. The accuracy for delivered and exhaled tidal volumes are directly related to the respective accuracy of the tubing compliance volume during inhalation and exhalation. The ratio of tubing compliance to the patient’s respiratory compliance as well as the rate of circuit pressurization (function of flow rate and circuit resistance) are among the main factors influencing the accuracy of tubing compliance volume. Therefore, the worst-case patient circuit for volume-based ventilation is considered to be the one with highest resistance and the highest compliance. In general, higher circuit resistance poses more challenges for pressure-based ventilation. For testing, the worst-case patient circuit will be selected from amongst the specified breathing circuits based on their compliance and resistance properties. Therefore, the worst-case patient circuit for verification is considered to be the one with highest resistance and the highest compliance i.e. P/N: 5094000 and 5093900.
 | Rationale for Bacteria Filters (As per RE00164878): 351U5856 Bacteria Filters are considered least favorable due to highest resistance and volume combination of all standard bacteria filters recommended for use with the PB560.

Sheet: Annex C Questions
 |  |  | Document #: | 10037183 | Revision: | W
Reference ISO 14971 | Question | Factors to Consider | Response (N/A = Not Relevant) | Potential Hazards(s) | Potential Hazardous situation(s) | Notes / Comments
C.2.1 | What is the intended use and how is the medical device to be used? | What is the medical device's role relative to: • diagnosis, prevention, monitoring, treatment, or alleviation of disease, | The Puritan Bennett™ 560 Ventilator is indicated for the continuous or intermittent mechanical ventilatory support of patients weighing at least 11 lb (5 kg) who require mechanical ventilation. The ventilator is a restricted medical device intended for use by qualified, trained personnel under the direction of a doctor. Specifically, the ventilator is applicable for adult and pediatric patients who require the following general types of invasive or non-invasive ventilatory support, as prescribed by an attending doctor: • Positive Pressure ventilation • Assist/Control, SIMV, or CPAP modes of ventilation • Breath types including Volume Control, Pressure Control, and Pressure Support The ventilator may be operated by: • Respiratory therapists • Doctors • Nurses • Homecare providers • Patient and patient’s families | Refer to RE00076775 Ventilation Hazards | N/A | N/A
 |  | • compensation for injury or handicap or
 |  | • replacement or modification of anatomy, or control of conception?
 |  | • what are the indications for use (e.g., patient population)?
 |  | Does the medical device sustain or support life?
 |  | Is special intervention necessary in the case of failure of the medical device?
C.2.2 | Is the medical device intended to be implanted? | Consider: the location of implantation, the characteristics of the patient population, age, weight, physical activity, the effect of aging on implant performance, the expected lifetime of the implant, the reversibility of the implantation. | N/A | Refer to RE00076775 Ventilation Hazards | N/A | N/A
C.2.3 | Is the medical device intended to be in contact with the patient or other persons? | Nature of the intended contact, i.e. surface contact, invasive contact, or implantation and, for each, the period and frequency of contact. • surface contact points; • invasive contact / contact through body orifices; • implantable contact (permanent / absorbable) | N/A None of the parts of the ventilator is in direct patient contact. A breathing circuit is connected to the ventilator. The breathing circuit does not come into contact with the patient directly. The ventilator may be used with an endotracheal tube, tracheal tube, face mask, nasal mask or prongs, or mouthpiece. |  | N/A | N/A
C.2.4 | What materials or components are utilized in the medical device or are used with, or are in contact with, the medical device? | Consider: • compatibility with relevant substances; | Clinicians may use a variety of interfaces to connect patients to the ventilator: nasal masks or full face masks; endotracheal or tracheotomy tubes. |  | N/A | N/A
 |  | • compatibility with tissues or body fluids;
 |  | • whether characteristics relevant to safety are known;
 |  | • is the device manufactured utilizing materials of animal origin? See Annex I and ISO 22442 Annex I – Biological Hazards ISO 22442-1:2007 = provides requirements and guidance on risk management related to the hazards typical of medical devices manufactured utilizing animal tissues or derivatives
C.2.5 | Is energy delivered to or extracted from the patient? | Consider: • the type of energy transferred; | N/A | N/A | N/A | N/A
 |  | • its control, quality, quantity, intensity, and duration;
 |  | • whether energy levels are higher than those currently used for similar devices.
C.2.6 | Are substances delivered to or extracted from the patient? | Consider: • whether the substance is delivered or extracted; | The ventilator delivers regulated air and/or oxygen to the patient via a medical pipeline system or from gas cylinders. It is supplied to the patient circuit through check valves and exits to the patient circuit close to patient pressure. This ventilator is not for use with anesthetic gases. | Refer to RE00076775 Ventilation Hazards | N/A | N/A
 |  | • whether it is a single substance or range of substances;
 |  | • the maximum and minimum transfer rates and control thereof.
C.2.7 | Are biological materials processed by the medical device for subsequent re-use, transfusion, or transplantation? | Consider: the type of process and substance(s) processed (e.g., auto-transfusion, dialysis, blood component, or cell therapy processing). | N/A | N/A | N/A | N/A
C.2.8 | Is the medical device supplied sterile or intended to be sterilized by the user, or are other microbiological controls applicable? | Consider: • whether the medical device is intended for single use or to be reusable; | N/A The ventilator is not a sterile device | N/A | N/A | N/A
 |  | • any packaging;
 |  | • shelf-life issues;
 |  | • limitation on the number of re-use cycles;
 |  | • method of product sterilization;
 |  | • the impact of other sterilization methods not intended by the manufacturer.
 |  | • Is the medical device properly marked to inform the user whether it is for single use or to be re-used? • Does the packaging clearly indicate any limitation of handling or shelf-life? • Does the accompanying document clearly indicate proper methods of and agents to be used for cleaning or sterilization, and inform about frequencies of cleaning?
 |  | • Simplicity of disassembling / reassembling and any USE errors connected to these?
C.2.9 | Is the medical device intended to be routinely cleaned and disinfected by the user? | Consider: • the types of cleaning or disinfecting agents to be used and any limitations on the number of cleaning cycles. | All external panels and surfaces should be cleaned before and after each patient use and as often as necessary to keep the ventilator clean. Additionally the ventilator should be cleaned the ventilator periodically, whenever it is soiled or dirty, before any maintenance operation, and before storing the ventilator. Approved Cleaning Solutions for Exterior Ventilator Surfaces: Mild dishwashing detergent 70% isopropyl alcohol (rubbing alcohol) 10% chlorine bleach (90% tap water) Glutaraldehyde Hospital disinfectant cleaners Hydrogen peroxide 15% ammonia (85% tap water) Ammonia-based household cleaners Household cleaners Instruction for the cleaning of the accessories is to follow the manufacturer’s instructions for cleaning the ventilator’s accessories and components, including the patient circuit. The exhalation block is intended for single use by a single patient . It may periodically be cleaned, but it cannot be disinfected or sterilized. To maintain good measurement quality when used continuously, clean the exhalation block periodically. The exhalation block should be changed every 4 months and cannot be reused with any other patient. | Refer to RE00076775 Ventilation Hazards | N/A | N/A
 |  | • The design of the medical device can influence the effectiveness of routine cleaning and disinfection. In addition, consideration should be given to the effect of cleaning and disinfecting agents on the safety or performance of the device.
C.2.10 | Is the medical device intended to modify the patient environment? | Consider: • temperature; • humidity; • atmospheric gas composition; • pressure; • light. | The ventilator modifies the patient's breathing environment. User-selectable ventilation modes are: • Assisted Controlled Volume (V A/C) • Assisted Controlled Pressure (P A/C) • Volume Synchronized Intermittent Mandatory Ventilation (V SIMV) • Pressure Synchronized Intermittent Mandatory Ventilation (P SIMV) • Continuous Positive Airway Pressure (CPAP) • Pressure Support Ventilation with apnea ventilation (PSV/ST) | Refer to RE00076775 Ventilation Hazards | N/A | N/A
C.2.11 | Are measurements taken? | Consider: the variables measured and the accuracy and the precision of the measurement results. Also, users have to be aware of frequencies at which measurements have to be initiated, parameters influencing the result, consumables needed, how to handle or interpret the results. Standard issues are legibility and exactness of displays. Neglecting routine maintenance also might cause wrong results. | The ventilator measures and monitors patient respiratory parameters. A trained user will need to understand, evaluate and adjust parameters.
C.2.12 | Is the medical device interpretative? | Consider: whether conclusions are presented by the medical device from input or acquired data, the algorithms used, and confidence limits. Special attention should be given to unintended applications of the data or algorithm.
C.2.13 | Is the medical device intended for use in conjunction with other medical devices, medicines, or other medical technologies? | Consider: identifying any other medical devices, medicines, or other medical technologies that can be involved and the potential problems associated with such interactions, as well as patient compliance with the therapy.
C.2.14 | Are there unwanted outputs of energy or substances? | • Energy-related Consider: noise and vibration, heat, radiation (including ionizing, non-ionizing, and ultraviolet /visible/infrared radiation), contact temperatures, leakage currents, and electric or magnetic fields. | There are no unwanted outputs of energy or substances under normal operating conditions. | Refer to RE00076775 Ventilation Hazards | N/A | N/A
 |  | • The adverse effects of noise, vibration, heat, and waste products (exhaust gases) on physiology and psychology of users and thirds.
 |  | • Substance-related Consider: substances used in manufacturing, cleaning or testing having unwanted physiological effects if they remain in the product.
 |  | • Other substance-related Consider: discharge of chemicals, waste products, and body fluids.
C.2.15 | Is the medical device susceptible to environmental influences? | Consider: the operational, transport and storage environments. These include light, temperature, humidity, vibrations, spillage, susceptibility to variations in power and cooling supplies, and electromagnetic interference. | Yes – temperature, pressure, humidity, vibration, electrical/magnetic field. | Refer to RE00076775 Ventilation Hazards
C.2.16 | Does the medical device influence the environment? | Consider:: • the effects on power and cooling supplies; | Yes – alarm noises/notifications. | Refer to RE00076775 Ventilation Hazards | N/A | N/A
 |  | • emission of toxic materials;
 |  | • the generation of electromagnetic disturbance
C.2.17 | Are there essential consumables or accessories associated with the medical device? | Consider: specifications for such consumables or accessories and any restrictions placed upon users in their selection of these. | Consumables and Replacement Intervals • Air Inlet Filter - (Foam + Fine Particle) Once a month or more often, depending on the extent of soiling • Inspirited Bacteria Filter See manufacturer’s recommendation • Patient Circuit - See manufacturer’s recommendation - Single use Single patient • FIO2 Sensor - 14 to 18 months or more often in case of persistent calibration failure • Exhalation Block 4 months(*) (and for each new patient) humidifiers, water traps • Oxygen solenoid valve - Every 15,000 hours of use •Turbine - Every 15,000 hours of use •Exhalation solenoid valve - Every 15,000 hours of use •Cooling fan - Every 15,000 hours of use •Clean and disinfect Insp block - Every two years •Measurements check and - Every two years •calibration - Every two years •Battery, lithium-ion 4.8 Ah memory - Every two years •Battery, lithium, 3V - Every two years •Buzzer PCBA - Every two years | Refer to RE00076775 Ventilation Hazards | N/A | N/A
C.2.18 | Is maintenance or calibration necessary? | Consider: • whether maintenance or calibration are to be carried out by the operator or user or by a specialist; | Each time the exhalation block or circuit is removed and reinstalled or after installing a new exhalation block, the exhalation flow sensor must be recalibrated before the using the ventilator. This process is automatic and does not require the use of a measurement device. Each time the FIO2 sensor is removed and reinstalled, and on a weekly basis, the FIO2 sensor must be recalibrated before using the ventilator. This process does not require the use of a measurement device. | Refer to RE00076775 Ventilation Hazards | N/A | N/A
 |  | • are special substances or equipment necessary for proper maintenance or calibration?
C.2.19 | Does the medical device contain software? | Consider: whether software is intended to be installed, verified, modified, or exchanged by the operator or user or by a specialist. | Software is installed by a qualified service engineer | N/A | N/A | N/A
C.2.20 | Does the medical device have a restricted shelf-life? | Consider: labeling or indicators and the disposal of such medical devices when the expiration date is reached. | N/A | N/A | N/A | N/A
C.2.21 | Are there any delayed or long-term use effects? | Consider: ergonomic and cumulative effects. Examples could include pumps for saline that corrode over time, mechanical fatigue, loosening of straps and attachments, vibration effects, labels that wear or fall off, long term material degradation. | The patient can become dependent on the ventilator to provide respiration. The ventilator will remain in good service condition when the preventative maintenance schedule is adhered to | Refer to RE00076775 Ventilation Hazards | N/A | N/A
C.2.22 | To what mechanical forces will the medical device be subjected? | Consider: whether the forces to which the medical device will be subjected are under the control of the user or controlled by interaction with other persons. | Shipping – ISTA 2A; shock and vibration The ventilator is suitable for use in institutional, home, and portable settings. It is not intended for use as an emergency transport ventilator. - suitable for use on commercial aircraft, per FAA requirements | Refer to RE00076775 Ventilation Hazards | N/A | N/A
C.2.23 | What determines the lifetime of the medical device? | Consider: aging and battery depletion. | The lifetime of the device is determined by a number of factors: • Life of product line is from inception to withdraw from market • Shelf-Life of components is determined by Stability and Packaging evaluation. | Refer to RE00076775 Ventilation Hazards | N/A | N/A
C.2.24 | Is the medical device intended for single use? | Consider: does the medical device self-destruct after use? Is it obvious that the device has been used? | No | N/A | N/A | N/A
C.2.25 | Is safe decommissioning or disposal of the medical device necessary? | Consider: the waste products that are generated during the disposal of the medical device itself. For example, does it contain toxic or hazardous material, or is the material recyclable? | The ventilator is marked to ensure that it enters the recycled waste system. 'Recycle electrical and electronic items with this marking according to local regulations (EN50419). Do not discard with ordinary household waste. This includes the ventilator and the battery.' | Refer to RE00076775 Ventilation Hazards | N/A | N/A
C.2.26 | Does installation or use of the medical device require special training or special skills? | Consider: the novelty of the medical device and the likely skill and training of the person installing the device. | The ventilator is for use as prescribed by a doctor. The ventilator may be operated by: • Respiratory therapists • Doctors • Nurses • Homecare providers • Patient and patient’s families It is the responsibility of the clinician or clinical educator to ensure that both the patient and the caregiver fully understand the daily use of the ventilator. | Refer to RE00076775 Ventilation Hazards | N/A | N/A
C.2.27 | How will information for safe use be provided? | Consider: • whether information will be provided directly to the end user by the manufacturer or will it involve the participation of third parties such as installers, care providers, health care professionals, or pharmacists, and whether this will have implications for training; | Training and manuals | Refer to RE00076775 Ventilation Hazards | N/A | N/A
 |  | • commissioning and handing over to the end user and whether it is likely/possible that installation can be carried out by people without the necessary skills; |  | Refer to RE00076775 Ventilation Hazards | N/A | N/A
 |  | • based on the expected life of the device, whether re-training or re-certification of operators or service personnel would be required. |  | Refer to RE00076775 Ventilation Hazards | N/A | N/A
C.2.28 | Will new manufacturing processes need to be established or introduced? | Consider: new technology or a new scale of production. | N/A | N/A | N/A | N/A
C.2.29 | Is successful application of the medical device critically dependent on human factors such as the user interface? | Factors that should be considered include user interface design features that can contribute to use error. Features should be designed so that they cannot be easily misused by busy users in an environment where distractions are commonplace, e.g. device control, symbols used, ergonomic features physical design and layout, hierarchy of operation, menus for software driven devices, visibility of warnings, and audibility of alarms, standardized color coding.
C.2.29.1 | Can the user interface design features contribute to use error? | Factors that should be considered are user interface design features that can contribute to use error. Examples of interface design features include: control and indicators, symbols used, ergonomic features, physical design and layout, hierarchy of operation, menus for software driven devices, visibility of warnings, audibility of alarms, and standardization of color coding. See IEC 60601-1-6 for additional guidance on usability and IEC 60601-1-8 for guidance on alarms. | Yes | Refer to RE00076775 Ventilation Hazards | N/A | N/A
C.2.29.2 | Is the medical device used in an environment where distractions can cause use error? | Consider: • the consequence of use error; | Yes | Refer to RE00076775 Ventilation Hazards | N/A | N/A
 |  | • whether the distractions are commonplace; |  | Refer to RE00076775 Ventilation Hazards | N/A | N/A
 |  | • whether the user can be disturbed by an infrequent distraction |  | Refer to RE00076775 Ventilation Hazards | N/A | N/A
C.2.29.3 | Does the medical device have connecting parts or accessories? | Consider: the possibility of wrong connections, similarity to other products’ connections, connection force, feedback on connection integrity, and over- and under-tightening | Yes | Refer to RE00076775 Ventilation Hazards | N/A | N/A
C.2.29.4 | Does the medical device have a control interface? | Consider: spacing, coding, grouping, mapping, modes of feedback, blunders, slips, control differentiation, visibility, direction of activation or change, whether the controls are continuous or discrete, and the reversibility of settings or actions. | Yes | Refer to RE00076775 Ventilation Hazards | N/A | N/A
C.2.29.5 | Does the medical device display information? | Consider: visibility in various environments, orientation, the visual capabilities of the user, populations and perspectives, clarity of the presented information, units, color coding, and the accessibility of critical information. | Yes | Refer to RE00076775 Ventilation Hazards | N/A | N/A
C.2.29.6 | Is the medical device controlled by a menu? | Consider: complexity and number of layers, awareness of state, location of settings, navigation method, number of steps per action, sequence clarity and memorization problems, and importance of control function relative to its accessibility and the impact of deviating from specified operating procedures. | Yes | Refer to RE00076775 Ventilation Hazards | N/A | N/A
C.2.29.7 | Will the medical device be used by persons with special needs? | Consider: the user, their mental and physical abilities, skill, and training, ergonomic aspects, the use environment, installation requirements, and the patient's capability to control or influence the use of the medical device. Special attention should be paid to users with special needs, such as handicapped persons, the elderly, and children. Their special needs might include assistance by another person to enable the use of a medical device. Is the medical device intended to be used by individuals with various skill levels and cultural backgrounds? | Only if the user is differently abled | Refer to RE00076775 Ventilation Hazards | N/A | N/A
C.2.29.8 | Can the user interface be used to initiate user actions? | Consider: the possibility of initiating a deliberate action for the user to enter a controlled operation mode, which enlarges the risks for the patient and which creates awareness for the user for this condition. | yes | N/A | N/A | N/A
C.2.30 | Does the medical device use an alarm system? | Consider: are the risk of false alarms, missing alarms, disconnected alarm systems, unreliable remote alarm systems, and the medical staff’s possibility of understanding how the alarm system works. Guidance for alarm systems is given in IEC 60601-1-8. | Yes | N/A | N/A | N/A
C.2.31 | In what way(s) might the medical device be deliberately misused? | Consider: are incorrect use of connectors, disabling safety features or alarms, neglect of manufacturer's recommended maintenance. | User error inputting the prescribed settings User Error - ventilator settings inappropriate for patient User Error - not adhering to the PM schedule User Error - O2 not connected or obstructed User Error - cables not connected correctly User Error - Physical damage from impact or vibration, or transport bag fault User Error - environmental temperature or relative humidity exceeded User Error - Physical damage from liquid ingress due to spillage or excessive cleaning liquid | Refer to RE00076775 Ventilation Hazards | N/A | N/A
C.2.32 | Does the medical device hold data critical to patient care? | Consider: the consequence of the data being modified or corrupted. | Yes | Refer to RE00076775 Ventilation Hazards | N/A | N/A
C.2.33 | Is the medical device intended to be mobile or portable? | Consider: necessary grips, handles, wheels, brakes, mechanical stability, and durability. | Portable | Refer to RE00076775 Ventilation Hazards | N/A | N/A
C.2.34 | Does the use of the medical device depend on essential performance? | Consider: for example, the characteristics of the output of life-supporting devices or the operation of an alarm. See IEC60601-1-1 for discussion of performance. | Yes | N/A | N/A | N/A

Sheet: Risk Analysis Chart
 |  | Document: | 10037183 | Revision: |  |  | W
SECTION 1 |  |  |  |  |  |  |  |  |  | SECTION 3
RISK ASSESSMENT
HAZARD ANALYSIS |  |  |  |  |  |  |  |  | RISK ANALYSIS (PRE-MITIGATION) | RISK CONTROL (POST-MITIGATION) |  |  |  |  |  |  |  | VERIFICATION |  | RISK ACCEPTABILITY
Hazard ID | Hazard (may be combined with Hazardous Situation) | Hazardous Situation (may be combined with Hazard) | Potential Cause | Potential Harm Name | Essential Performance (Y/N) | FDA Harms Code | Harm Description | Severity | Req. ID | Risk Control Options Use the following risk control options in the priority order listed |  | Information provided to the User | P1 | P2 | Prob. of occurrence of Harm | Risk Zone | Occurrence Rationale | Verification of Implementation | Verification of Effectiveness | Risk Acceptable? | Risk Acceptance Rationale
 |  |  |  |  |  |  |  |  |  | (1st choice) Inherently safe by design | (2nd choice) Protective measures |  |  |  |  |  | P2
VH1 | Alarm - audio volume too high | Patient or user reports alarm volume is too high |  | Anxiety | N | 2328 | Mild symptoms; intervention not indicated; eliminate stressors Asymptomatic asynchrony observed on monitoring. | 1 | PRD417 |  |  | Manual - WARNING: Alarm volume should be adjusted with respect to the ventilator’s operating environment and so that the patient's caretakers can hear the alarms. The audible alarm vents located at the front of the device should never be obstructed. The alarmcan be paused with the Alarm Pause function by pressing the ALARM CONTROL key twice once the alarm has been declared. | 2 | 4 | 2 | 1 | P2 scores are based on clinical expert opinion, engineering inputs, and no patient harm reported in complaint data. | VHVH41 | 10038637 PB560-520 Trace Matrix | Yes | This risk is acceptable and has been reduced as far as possible. The benefits of home care ventilation outweighs this potential risk.
 |  |  | User adjusts alarm volume inappropriately for the environment speaker is out of specification |  | N | 2328 | Symptomatic; requiring minor change in ventilator settings (e.g., sensitivity, eSens) | 2 | PRD32 |  | Protective- alarm volume is adjustable 65 to 80 dBA through the preference menu |  | 2 | 2 | 1 | 1
 |  |  | DFMEA CPU PCBA: No alarm on reset |  | N | 2328 | Symptomatic with vital sign impacts; requiring major change in ventilator settings | 3 | PRD33 |  | Background checks for alarm functions |  | 2 | 1 | 1 | 1
 |  |  |  |  | N | 2328 | Symptomatic requiring major change in therapy (e.g., sedation, paralytics, controlled ventilation) | 4 | PRD296 |  |  | Manual - Operational Verification Checklist - Verify the alarm volume is adapted to the patient environment. | 2 | 1 | 1 | 2
 |  |  |  |  | N |  |  |  | PRD433 (560) |  |  | PB560 - WARNING: A ventilator-dependent patient should always be monitored by trained and competent medical personnel. Ensure that the patient’s caregiver is able and prepared to take suitable action in the event the ventilator identifies an alarmed condition or experiences a problem.
VH2 | Alarm - Delay in response | User or caregiver does not respond to alarm as they do not hear alarm or misinterprets alarm priority | User adjusts alarm volume inappropriately for the environment | Delay of Treatment (Prolonged procedure) | N | N/A | Minor delay, no patient impact | 1 | PRD417 |  |  | Manual - WARNING: Alarm volume should be adjusted with respect to the ventilator’s operating environment and so that the patient's caretakers can hear the alarms. The audible alarm vents located at the front of the device should never be obstructed. The alarm can be paused with the Alarm Pause function by pressing the ALARM CONTROL key twice once the alarm has been declared. | 2 | 3 | 1 | 1 | P2 scores are based on clinical expert opinion, engineering inputs, and complaint data. | 10038637 PB560-520 Trace Matrix | 10038637 PB560-520 Trace Matrix | Yes | This risk is acceptable and has been reduced as far as possible. The benefit of using the ventilator for homecare outweighs the potential risk.
 |  |  | Use Error - Alarm priority misinterpreted by the user |  | N | N/A | Delay with minor patient impact (e.g., extended manual ventilation, stable patient). | 2 | PRD32 |  | Protective - alarm volume is adjustable 65 to 80 dBA through the preference menu |  | 2 | 3 | 1 | 1
 |  |  | User closes the door to a patient room |  | N | N/A | Delay with major patient impact (e.g., extended manual ventilation, unstable severe pulmonary status) | 3 | PRD296 |  |  | Manual - Operational Verification Checklist - Verify the alarm volume is adapted to the patient environment. | 2 | 3 | 1 | 1
 |  |  | User doesn't react to all alarms in event of multiple alarm activation |  | N | N/A | Prolonged delay with major patient impact,. replacement ventilator unavailable (e.g., extended manual ventilation, unstable severe pulmonary status,) | 4 | PRD433 (560) |  |  | PB560 - WARNING: A ventilator-dependent patient should always be monitored by trained and competent medical personnel. Ensure that the patient’s caregiver is able and prepared to take suitable action in the event the ventilator identifies an alarmed condition or experiences a problem. | 2 | 2 | 1 | 2
 |  |  |  |  | N | N/A | Death | 5 | PRD404 |  |  | Manual - WARNING: When an alarm condition is triggered, or there is evidence of a patient-ventilator fault or problem, examine the patient first before examining the ventilator. | 2 | 2 | 1 | 2
 |  |  |  |  | N |  |  |  | PRD43 | Nurse call optional accessory
 |  |  |  |  | Y |  |  |  | PRD162 |  | Protective: Visual alarm messages appear on the screen and may flash
VH3 | Alarm Failure | Device or device accessory fails to alarm when it meets alarm condition such as volume, flow, pressure, device alerts. | Total Power Loss | Delay of Treatment (Prolonged procedure) | N | N/A | Minor delay, no patient impact | 1 |  |  | Protective- The ventilator has 2 speakers - dual circuits and dual speakers provide back up to alarm function |  | 2 | 3 | 1 | 1 | P2 scores are based on clinical expert opinion, engineering inputs, and complaint data | 10038637 PB560-520 Trace Matrix | 10038637 PB560-520 Trace Matrix | Yes | This risk is acceptable and has been reduced as far as possible. The benefits of home care ventilation outweighs this potential risk.
 |  |  | SWFMEA Alarms No detection of High Peak Pressure No detection of Low Pressure Incorrect monitored exhaled tidal volume (VTE)from flow sensor No detection of Apnea No detection of High Breath Rate/Respiratory Rate No detection of Occlusion No detection of "Check Proximal Line 1 " alarm No detection of disconnect No detection of FIO2 alarm condition No main power loss detection |  | Y | N/A | Delay with minor patient impact (e.g., extended manual ventilation, stable patient). | 2 | PRD53 PRD54 |  | Security shut down alarm will sound on total power loss |  | 2 | 3 | 1 | 1
 |  |  |  |  | N | N/A | Delay with major patient impact (e.g., extended manual ventilation, unstable severe pulmonary status) | 3 | PRD162 |  | graphics to display patient response |  | 2 | 2 | 1 | 1
 |  |  |  | Respiratory failure | N | 2484 | Symptomatic early clinical intervention; Requires increased ventilatory support of one or more parameters | 2 | PRD50 |  | The ventilator performs visual and auditory tests of LEDs and alarm buzzers |  | 2 | 1 | 1 | 1
 |  |  |  |  | N | 2484 | Symptomatic; Requires multiple ventilator adjustments, administration of medication, and/or elective change from non-invasive to invasive ventilation. | 3 |  |  | Protective - each alarm condition has different priority alarms |  | 2 | 1 | 1 | 1
 |  |  |  |  | N | 2484 | Symptomatic; Requires move from non-invasive to invasive ventilation with emergent intubation. | 4 | PRD404 |  |  | Manual - WARNING: When an alarm condition is triggered, or there is evidence of a patient-ventilator fault or problem, examine the patient first before examining the ventilator. | 2 | 1 | 1 | 2
 |  |  |  |  | N | 2484 | Death | 5 | PRD296 PRD437 |  |  | Manual - Operational Verification Checklist If the ventilator fails the alarm tests or if you cannot complete the tests, refer to Chapter 3, “Alarms and Troubleshooting” or call your equipment supplier or Covidien. | 2 | 1 | 1 | 2
 |  |  |  | Pneumothorax | N | 2012 | Asymptomatic; clinical or diagnostic observations only; intervention not indicated | 1 | PRD433 (560) |  |  | PB560 - WARNING: A ventilator-dependent patient should always be monitored by trained and competent medical personnel. Ensure that the patient’s caregiver is able and prepared to take suitable action in the event the ventilator identifies an alarmed condition or experiences a problem. | 2 | 1 | 1 | 1
 |  |  |  |  | N | 2012 | Symptomatic intervention indicated (e.g. tube placement without sclerosis (no pleurodesis), hospitalization observation, electively place chest tube | 2 | PRD435 |  |  | Manual - Warnings - While the ventilator is in use, an alternative means of ventilation should always be available in the event of a ventilator problem. This is particularly true for ventilator-dependent patients. Supplementary observation, appropriate for the patient's condition, is also recommended. | 2 | 1 | 1 | 1
 |  |  |  |  | N |  |  |  | PRD437 |  |  | PB560 - WARNING: If the ventilator fails the alarm tests or if you cannot complete the tests, refer to section 3.8, “Troubleshooting” or call your equipment supplier or Covidien.
 |  |  |  |  | N |  |  |  | PRD436 (560) |  |  | PB560 - WARNING: Verify the functionality of the alarm conditions before connecting the patient to the ventilator
VH4 | False Alarm | Ventilator alarm(s) activated when it should not have occurred | Flow sensor or pressure sensor out of calibration or inaccurate. SW detection criteria is faulty. | Delay of Treatment (Prolonged procedure) | N | N/A | Minor delay, no patient impact | 1 | PRD396 | Calibration of the exhalation flow sensor |  |  | 2 | 2 | 1 | 1 | P2 scores are based on clinical expert opinion, engineering inputs, and complaint data | 10038637 PB560-520 Trace Matrix | 10038637 PB560-520 Trace Matrix | Yes | This risk is acceptable and has been reduced as far as possible. The benefits of home care ventilation outweighs this potential risk.
 |  |  | SWFMEA Alarms Incorrect detection of High Peak Pressure Incorrect detection of Low Pressure Incorrect monitored exhaled tidal volume (VTE) from flow sensor Incorrect detection of Apnea Incorrect detection of Occlusion Incorrect detection of "Check Proximal Line 1 " alarm Incorrect detection of disconnect Monitors Incorrect annunciation of FIO2 alarm Incorrect battery level monitor |  | N | N/A | Delay with minor patient impact (e.g., extended manual ventilation, stable patient). | 2 | PRD50 |  | visual and auditory tests of LEDs and alarm buzzers (POST) |  | 2 | 2 | 1 | 1
 |  |  |  |  | N | N/A | Delay with major patient impact (e.g., extended manual ventilation, unstable severe pulmonary status) | 3 | PRD357 |  | Preventative maintenance schedule - pressure sensor change |  | 2 | 2 | 1 | 1
 |  |  |  |  | N |  |  |  | PRD162 |  | graphics to display patient response
 |  |  |  |  | N |  |  |  | PRD356 |  |  | WARNING: To ensure proper performance of the ventilator, the preventative maintenance schedule should be followed. For further information contact Covidien.
 |  |  |  |  | N |  |  |  | PRD435 |  |  | Manual - Warnings - While the ventilator is in use, an alternative means of ventilation should always be available in the event of a ventilator problem. This is particularly true for ventilator-dependent patients. Supplementary observation, appropriate for the patient's condition, is also recommended.
 |  |  |  |  | N |  |  |  | PRD433 (560) |  |  | PB560 - WARNING: A ventilator-dependent patient should always be monitored by trained and competent medical personnel. Ensure that the patient’s caregiver is able and prepared to take suitable action in the event the ventilator identifies an alarmed condition or experiences a problem.
VH5 | No shut down alarm | Audible alarm fails to activate during an unexpected shut down. | User error - lack of service - Buzzer board with battery not serviced | Delay of Treatment (Prolonged procedure) | N | N/A | Minor delay, no patient impact | 1 | PRD50 PRD417 | POST |  |  | 2 | 1 | 1 | 1 | P2 scores are based on clinical expert opinion, engineering inputs, and complaint data | 10038637 PB560-520 Trace Matrix | 10038637 PB560-520 Trace Matrix | Yes | This risk is acceptable and has been reduced as far as possible. The benefits of home care ventilation outweighs this potential risk.
 |  |  | DFMEA CPU PCBA: Security buzzer Buzzer board connector |  | N | N/A | Delay with minor patient impact (e.g., extended manual ventilation, stable patient). | 2 |  |  | Protective - The ventilator has 2 speakers - dual circuits and dual speakers provide back u to alarm function |  | 2 | 1 | 1 | 1
 |  |  | DFMEA Cables - Buzzer board to CPU cable |  | N | N/A | Delay with major patient impact (e.g., extended manual ventilation, unstable severe pulmonary status) | 3 | PRD51 | Safety net - watchdogs |  |  | 2 | 1 | 1 | 1
 |  |  | DFMEA Buzzer PCBA: DC/DC (5V to 12V) Convertor Supply Switch (5V; battery) Power supply loss management Buzzer PCBA back up coin battery Coin Battery Oscillator PWM signal process Buzzers CPU/ Buzzer Board connector Shutdown DC/DC management |  | N | N/A | Prolonged delay with major patient impact,. replacement ventilator unavailable (e.g., extended manual ventilation, unstable severe pulmonary status,) | 4 | PRD50 |  | BUZZER FAULT1 alarm - Defective operation of the buzzers BUZZER FAULT2 alarm - Failure detected in the Very High Priority buzzer BUZZER FAULT3 alarm - Battery Charge Failure due to incorrect voltage BUZZER LOW BATTERY alarm - Buzzer Battery Failure (previously called BUZZER FAULT 4) |  | 2 | 1 | 1 | 2
 |  |  | SWFMEA Audio Device Driver |  | N | N/A | Death | 5 | PRD417 |  |  | warning instructing the user to adjust the alarm volume to an appropriate level and to be careful not to obstruct the buzzers outlet. | 2 | 1 | 1 | 2
 |  |  |  | Respiratory failure | N | 2484 | Symptomatic early clinical intervention; Requires increased ventilatory support of one or more parameters | 2 | PRD296 |  |  | Manual - Operational Verification Checklist | 2 | 2 | 1 | 1
 |  |  |  |  | N | 2484 | Symptomatic; Requires multiple ventilator adjustments, administration of medication, and/or elective change from non-invasive to invasive ventilation. | 3 | PRD435 |  |  | Manual - Warnings - While the ventilator is in use, an alternative means of ventilation should always be available in the event of a ventilator problem. This is particularly true for ventilator-dependent patients. Supplementary observation, appropriate for the patient's condition, is also recommended. | 2 | 1 | 1 | 1
 |  |  |  |  | N | 2484 | Symptomatic; Requires move from non-invasive to invasive ventilation with emergent intubation. | 4 | PRD433 (560) |  |  | PB560 - WARNING: A ventilator-dependent patient should always be monitored by trained and competent medical personnel. Ensure that the patient’s caregiver is able and prepared to take suitable action in the event the ventilator identifies an alarmed condition or experiences a problem. | 2 | 1 | 1 | 2
VH6 | False annunciation of security (shut down) alarm | Audible shut down alarm activates during ventilation. | DFMEA - CPU PCBA: Security Buzzer | Anxiety |  | 2328 | Mild symptoms; intervention not indicated; eliminate stressors Asymptomatic asynchrony observed on monitoring. | 1 |  | Design - Power button and audio pause pressed at the same time will turn the alarm off |  |  | 2 | 2 | 1 | 1 | P2 scores are based on clinical expert opinion, engineering inputs, and complaint data | 10038637 PB560-520 Trace Matrix | 10038637 PB560-520 Trace Matrix | Yes | This risk is acceptable and has been reduced as far as possible. The benefits of home care ventilation outweighs this potential risk.
 |  |  | DFMEA Buzzer PCBA: Shutdown DC/DC management |  | N | 2328 | Symptomatic; requiring minor change in ventilator settings (e.g., sensitivity, eSens) | 2 | PRD50 |  | BUZZER FAULT1 alarm - Defective operation of the buzzers BUZZER FAULT2 alarm - Failure detected in the Very High Priority buzzer BUZZER FAULT3 alarm - Battery Charge Failure due to incorrect voltage BUZZER LOW BATTERY alarm - Buzzer Battery Failure (previously called BUZZER FAULT 4) |  | 2 | 2 | 1 | 1
 |  |  | DFMEA Cables - Nurse call system / CPU cables and connectors |  | N | 2328 | Symptomatic with vital sign impacts; requiring major change in ventilator settings | 3 | PRD296 |  |  | Manual - Operational Verification Checklist | 2 | 2 | 1 | 1
 |  |  |  | Delay of Treatment (Prolonged procedure) | N | N/A | Minor delay, no patient impact | 1 | PRD435 |  |  | Manual - Warnings - While the ventilator is in use, an alternative means of ventilation should always be available in the event of a ventilator problem. This is particularly true for ventilator-dependent patients. Supplementary observation, appropriate for the patient's condition, is also recommended. | 2 | 2 | 1 | 1
 |  |  |  |  | N | N/A | Delay with minor patient impact (e.g., extended manual ventilation, stable patient). | 2 | PRD433 (560) |  |  | PB560 - WARNING: A ventilator-dependent patient should always be monitored by trained and competent medical personnel. Ensure that the patient’s caregiver is able and prepared to take suitable action in the event the ventilator identifies an alarmed condition or experiences a problem. | 2 | 2 | 1 | 1
 |  |  |  |  | N | N/A | Delay with major patient impact (e.g., extended manual ventilation, unstable severe pulmonary status) | 3 | PRD404 |  |  | When an alarm condition is triggered, or there is evidence of a patient-ventilator fault or problem, examine the patient first before examining the ventilator. | 2 | 2 | 1 | 1
VH7 | Alarm - Remote - fail | Remote alarms fail to activate when the ventilator meets an alarm condition. | User Error - Mixing up between open and closed nurse call system | Delay of Treatment (Prolonged procedure) | N | N/A | Minor delay, no patient impact | 1 | PRD41 |  | The ventilator connects to either a normally-open nurse call system or a normally closed nurse call system that will transmit any alarm to the nurse call system. | Clinicians Manual - WARNING: To connect the ventilator to a Nurse Call device, contact Covidien to check the ventilator's compatibility with the Nurse Call device and order a suitable connection cable. | 2 | 2 | 1 | 1 | P2 scores are based on clinical expert opinion, engineering inputs, and complaint data | 10038637 PB560-520 Trace Matrix | 10038637 PB560-520 Trace Matrix | Yes | This risk is acceptable and has been reduced as far as possible. The benefits of home care ventilation outweighs this potential risk.
 |  |  | User Error - Cable not connected |  | N | N/A | Delay with minor patient impact (e.g., extended manual ventilation, stable patient). | 2 | PRD42 |  | The ventilator connects to a normally-closed nurse call system that will transmit any alarm to the nurse call system. | Clinicians Manual - WARNING: Do not use Nurse Call devices that operate based on the closure of an electrical circuit, because the devices often do not take into account possible cable disconnection or a total loss of power. Ensure that the Nurse Call device is always connected to the ventilator. | 2 | 2 | 1 | 1
 |  |  | DFMEA- CPU PCBA Remote alarm or nurse call Remote alarm connector KEYBOARD MEMBRANE - USER INTERFACE Nurse call / Remote alarm- Connection to ventilator |  | N | N/A | Delay with major patient impact (e.g., extended manual ventilation, unstable severe pulmonary status) | 3 | PRD43 |  | The ventilator's nurse call is activated when an audible alarm is active and shall be audio paused by pressing the audio paused key of the ventilator. |  | 2 | 2 | 1 | 1
 |  |  | Misidentification of nurse call cable |  | N | N/A | Prolonged delay with major patient impact,. replacement ventilator unavailable (e.g., extended manual ventilation, unstable severe pulmonary status,) | 4 | PRD239 |  |  | Clinicians Manual - WARNING: Before using the Nurse Call system, ensure that its connections are secure and it operates properly. For more information, contact Covidien. | 2 | 1 | 1 | 2
 |  |  |  |  | N | N/A | Death | 5 | PRD232 |  |  | The user and clinician manuals include accurate explanations to check the connection of opened and closed nurse call system. | 2 | 1 | 1 | 2
 |  |  |  | Respiratory failure | N | 2484 | Symptomatic early clinical intervention; Requires increased ventilatory support of one or more parameters | 2 | PRD267 |  |  | The service manual includes an explanation to check proper connection of the opened and closed nurse call system. Complete a self-test after the cable has been installed and at regular intervals to ensure the system is operating as intended. | 2 | 2 | 1 | 1
 |  |  |  |  | Y | 2484 | Supplemental oxygen is given; COPD patients: Use with caution. Monitored closely. Symptomatic; Requires multiple ventilator adjustments, administration of medication, and/or elective change from non-invasive to invasive ventilation. | 3 |  |  | Protective - primary ventilator alarms are not impacted alarms for volume, flow, pressure, rate, device alerts |  | 2 | 2 | 1 | 1
 |  |  |  |  | N | 2484 | Life-threatening consequences; urgent intervention, intubation, or move from non-invasive to invasive ventilatory support indicated. | 4 |  |  | CHECK REMOTE ALARM - No activation of Nurse Call or remote alarm system when an alarm is in progress. |  | 2 | 1 | 1 | 2
 |  |  |  |  | N | 2484 | Death | 5 | PRD336 | Remote cable compatibilities |  |  | 2 | 1 | 1 | 2
 |  |  |  |  | N |  |  |  | PRD435 |  |  | Manual - Warnings - While the ventilator is in use, an alternative means of ventilation should always be available in the event of a ventilator problem. This is particularly true for ventilator-dependent patients. Supplementary observation, appropriate for the patient's condition, is also recommended.
 |  |  |  |  | N |  |  |  | PRD433 (560) |  |  | PB560 - WARNING: A ventilator-dependent patient should always be monitored by trained and competent medical personnel. Ensure that the patient’s caregiver is able and prepared to take suitable action in the event the ventilator identifies an alarmed condition or experiences a problem.
VH8 | Alarm - Audio - Constant | User is unable to manually reset the audible alarm and/or audible alarm fails to reset when the ventilator alarm violation condition has resolved. | SWFMEA Audio Device Driver | Delay of Treatment (Prolonged procedure) | N | N/A | Minor delay, no patient impact | 1 |  | Design Power cycling resets the ventilator clearing the issue |  |  | 1 | 2 | 1 | 1 | P2 scores are based on clinical expert opinion, engineering inputs, and complaint data | 10038637 PB560-520 Trace Matrix | 10038637 PB560-520 Trace Matrix | Yes | This risk is acceptable and has been reduced as far as possible. The benefits of home care ventilation outweighs this potential risk.
 |  |  |  |  | N | N/A | Delay with minor patient impact (e.g., extended manual ventilation, stable patient). | 2 | PRD162 |  | graphics to display patient response |  | 1 | 2 | 1 | 1
 |  |  |  |  | N | N/A | Delay with major patient impact (e.g., extended manual ventilation, unstable severe pulmonary status) | 3 | PRD50 |  | POST - performs visual and auditory tests of LEDs and alarm buzzers |  | 1 | 2 | 1 | 1
 |  |  |  | Anxiety | N | 2328 | Mild symptoms; intervention not indicated; eliminate stressors Asymptomatic asynchrony observed on monitoring. | 1 | PRD435 |  |  | Manual - Warnings - While the ventilator is in use, an alternative means of ventilation should always be available in the event of a ventilator problem. This is particularly true for ventilator-dependent patients. Supplementary observation, appropriate for the patient's condition, is also recommended. | 1 | 2 | 1 | 1
 |  |  |  |  | N | 2328 | Symptomatic; requiring minor change in ventilator settings (e.g., sensitivity, eSens) | 2 | PRD433 (560) |  |  | PB560 - WARNING: A ventilator-dependent patient should always be monitored by trained and competent medical personnel. Ensure that the patient’s caregiver is able and prepared to take suitable action in the event the ventilator identifies an alarmed condition or experiences a problem. | 1 | 2 | 1 | 1
 |  |  |  |  |  | 2328 | Symptomatic with vital sign impacts; requiring major change in ventilator settings | 3 |  |  |  |  | 1 | 2 | 1 | 1
VH9 | Alarm - Visual - Constant | User is unable to manually reset the visual alarm and/or visual alarm fails to reset when the ventilator alarm violation condition has resolved. | DFMEA- CPU PCBA keyboard connector | Delay of Treatment (Prolonged procedure) | Y | N/A | Minor delay, no patient impact | 1 | PRD32 PRD33 |  | Audible alarms annunciate |  | 1 | 2 | 1 | 1 | P2 scores are based on clinical expert opinion, engineering inputs, and complaint data | 10038637 PB560-520 Trace Matrix | 10038637 PB560-520 Trace Matrix | Yes | This risk is acceptable and has been reduced as far as possible. The benefits of home care ventilation outweighs this potential risk.
 |  |  |  |  | N | N/A | Delay with minor patient impact (e.g., extended manual ventilation, stable patient). | 2 | PRD162 |  | graphics to display patient response |  | 1 | 2 | 1 | 1
 |  |  |  |  | N | N/A | Delay with major patient impact (e.g., extended manual ventilation, unstable severe pulmonary status) | 3 | PRD435 |  |  | Manual - Warnings - While the ventilator is in use, an alternative means of ventilation should always be available in the event of a ventilator problem. This is particularly true for ventilator-dependent patients. Supplementary observation, appropriate for the patient's condition, is also recommended. | 1 | 2 | 1 | 1
 |  |  |  | Anxiety | N | 2328 | Mild symptoms; intervention not indicated; eliminate stressors Asymptomatic asynchrony observed on monitoring. | 1 | PRD433 (560) |  |  | PB560 - WARNING: A ventilator-dependent patient should always be monitored by trained and competent medical personnel. Ensure that the patient’s caregiver is able and prepared to take suitable action in the event the ventilator identifies an alarmed condition or experiences a problem. | 1 | 2 | 1 | 1
 |  |  |  |  |  | 2328 | Symptomatic; requiring minor change in ventilator settings (e.g., sensitivity, eSens) | 2 |  |  |  |  | 1 | 2 | 1 | 1
 |  |  |  |  |  | 2328 | Symptomatic with vital sign impacts; requiring major change in ventilator settings | 3 |  |  |  |  | 1 | 2 | 1 | 1
VH10 | Alarm - Audio - fails to enunciate/sound | Audio alarms fail to activate when the ventilator meets the alarm violation conditions. | DFMEA CPU PCBA Watchdog | Delay of Treatment (Prolonged procedure) | N | N/A | Minor delay, no patient impact | 1 |  |  | Protective - The ventilator has 2 speakers - dual circuits and dual speakers provide back u to alarm function | Operational Verification Test | 2 | 3 | 1 | 1 | P2 scores are based on clinical expert opinion, engineering inputs, and complaint data | 10038637 PB560-520 Trace Matrix | 10038637 PB560-520 Trace Matrix | Yes | This risk is acceptable and has been reduced as far as possible. The benefits of home care ventilation outweighs this potential risk.
 |  |  | SWFMEA Audio Device Driver |  | N | N/A | Delay with minor patient impact (e.g., extended manual ventilation, stable patient). | 2 | PRD51 |  | Safety net -Alarm system that continuously monitors both patient and machine. The machine-related alarm conditions are factory set, |  | 2 | 3 | 1 | 1
 |  |  |  |  | N | N/A | Delay with major patient impact (e.g., extended manual ventilation, unstable severe pulmonary status) | 3 | PRD162 |  | graphics to display patient response |  | 2 | 2 | 1 | 1
 |  |  |  | Respiratory failure | Y | 2484 | Symptomatic early clinical intervention; Requires increased ventilatory support of one or more parameters | 2 |  |  | alarms for volume, flow, pressure, rate, device alerts |  | 2 | 1 | 1 | 1
 |  |  |  |  | Y | 2484 | Symptomatic; Requires multiple ventilator adjustments, administration of medication, and/or elective change from non-invasive to invasive ventilation. | 3 | PRD53 PRD54 |  | Security shut down alarm will sound on total power loss |  | 2 | 1 | 1 | 1
 |  |  |  |  | N | 2484 | Symptomatic; Requires move from non-invasive to invasive ventilation with emergent intubation. | 4 | PRD404 |  |  | When an alarm condition is triggered, or there is evidence of a patient-ventilator fault or problem, examine the patient first before examining the ventilator. | 2 | 1 | 1 | 2
 |  |  |  |  | N | 2484 | Death | 5 | PRD162 |  | graphics to display patient response |  | 2 | 1 | 1 | 2
 |  |  |  | Pneumothorax | N | 2012 | Asymptomatic; clinical or diagnostic observations only; intervention not indicated | 1 | PRD435 |  |  | Manual - Warnings - While the ventilator is in use, an alternative means of ventilation should always be available in the event of a ventilator problem. This is particularly true for ventilator-dependent patients. Supplementary observation, appropriate for the patient's condition, is also recommended. | 2 | 1 | 1 | 1
 |  |  |  |  | N | 2012 | Small to Moderate Pneumothorax, electively place chest tube or observation | 2 | PRD433 (560) |  |  | PB560 - WARNING: A ventilator-dependent patient should always be monitored by trained and competent medical personnel. Ensure that the patient’s caregiver is able and prepared to take suitable action in the event the ventilator identifies an alarmed condition or experiences a problem. | 2 | 1 | 1 | 1
 |  |  |  |  |  | 2012 | Ventilation: Pneumothorax requiring placement chest tube with hospitalization or prolonged hospitalization | 3 |  |  |  |  | 2 | 1 | 1 | 1
 |  |  |  |  |  | 2012 | Life-threatening consequences; Tension pneumothorax; airway compromise requiring intubation; urgent surgical intervention or emergency Chest tube placement indicated | 4 |  |  |  |  | 2 | 1 | 1 | 2
VH11 | Alarm - Visual - fails to illuminate/light | Visual alarm indicator and/or alarm message fail to activate when the ventilator meets the alarm violation conditions | DFMEA CPU PCBA - Power Supply Board connector - keyboard connector | Delay of Treatment (Prolonged procedure) | N | N/A | Minor delay, no patient impact | 1 | PRD296 |  |  | Manual - Operational Verification Checklist | 1 | 2 | 1 | 1 | P2 scores are based on clinical expert opinion, engineering inputs, and complaint data | 10038637 PB560-520 Trace Matrix | 10038637 PB560-520 Trace Matrix | Yes | This risk is acceptable and has been reduced as far as possible. The benefits of home care ventilation outweighs this potential risk.
 |  |  | DFMEA KEYBOARD MEMBRANE USER INTERFACE |  | Y | N/A | Delay with minor patient impact (e.g., extended manual ventilation, stable patient). | 2 | PRD33 PRD34 |  | audio alarm will annunciate |  | 1 | 2 | 1 | 1
 |  |  |  |  | N | N/A | Delay with major patient impact (e.g., extended manual ventilation, unstable severe pulmonary status) | 3 | PRD162 |  | graphics to display patient response |  | 1 | 2 | 1 | 1
 |  |  |  |  | N |  |  |  | PRD435 |  |  | Manual - Warnings - While the ventilator is in use, an alternative means of ventilation should always be available in the event of a ventilator problem. This is particularly true for ventilator-dependent patients. Supplementary observation, appropriate for the patient's condition, is also recommended.
 |  |  |  |  | N |  |  |  | PRD433 (560) |  |  | PB560 - WARNING: A ventilator-dependent patient should always be monitored by trained and competent medical personnel. Ensure that the patient’s caregiver is able and prepared to take suitable action in the event the ventilator identifies an alarmed condition or experiences a problem.
VH12 | Alarm - Volume too low | Patient or user reports alarm volume is too low. | User adjusts alarm volume inappropriately for the environment | Delay of Treatment (Prolonged procedure) | N | N/A | Minor delay, no patient impact | 1 | PRD32 | Graphics display includes a Parameter adjustment bar for alarm volume | operational verification checklist | Labelling - Manual - WARNING: Alarm volume should be adjusted with respect to the ventilator’s operating environment and so that the patient's caretakers can hear the alarms. The audible alarm vents located at the front of the device should never be obstructed. The alarm can be paused with the Alarm Pause function by pressing the ALARM CONTROL key twice once the alarm has been declared. | 2 | 2 | 1 | 1 | P2 scores are based on clinical expert opinion, engineering inputs, and complaint data | 10038637 PB560-520 Trace Matrix | 10038637 PB560-520 Trace Matrix | Yes | This risk is acceptable and has been reduced as far as possible. The benefits of home care ventilation outweighs this potential risk.
 |  |  | Obstruction of the sound diffusion holes |  | N | N/A | Delay with minor patient impact (e.g., extended manual ventilation, stable patient). | 2 |  |  | Protective - alarm volume is adjustable 65 to 80 dBA |  | 2 | 2 | 1 | 1
 |  |  |  |  | Y | N/A | Delay with major patient impact (e.g., extended manual ventilation, unstable severe pulmonary status) | 3 | PRD32 PRD33 |  | Audible alarms annunciate |  | 2 | 3 | 1 | 1
 |  |  |  |  | N | N/A | Prolonged delay with major patient impact,. replacement ventilator unavailable (e.g., extended manual ventilation, unstable severe pulmonary status,) | 4 | PRD34 |  | Buzzer alarm |  | 2 | 3 | 1 | 2
 |  |  |  |  | N | N/A | Death | 5 |  |  | Visual alarms LEDs |  | 2 | 3 | 1 | 2
 |  |  |  | Respiratory failure | Y | 2484 | Symptomatic early clinical intervention; Requires increased ventilatory support of one or more parameters | 2 | PRD417 |  | Alarm message on display |  | 2 | 2 | 1 | 1
 |  |  |  |  | N | 2484 | Symptomatic; Requires multiple ventilator adjustments, administration of medication, and/or elective change from non-invasive to invasive ventilation. | 3 | PRD435 |  |  | warning instructing the user to adjust the alarm volume to an appropriate level and to be careful not to obstruct the buzzers outlet. | 2 | 1 | 1 | 1
 |  |  |  |  | N | 2484 | Symptomatic; Requires move from non-invasive to invasive ventilation with emergent intubation. | 4 | PRD433 (560) |  |  | Manual - Warnings - While the ventilator is in use, an alternative means of ventilation should always be available in the event of a ventilator problem. This is particularly true for ventilator-dependent patients. Supplementary observation, appropriate for the patient's condition, is also recommended. | 2 | 1 | 1 | 2
 |  |  |  |  | N | 2484 | Death | 5 |  |  |  | PB560 - WARNING: A ventilator-dependent patient should always be monitored by trained and competent medical personnel. Ensure that the patient’s caregiver is able and prepared to take suitable action in the event the ventilator identifies an alarmed condition or experiences a problem. | 2 | 1 | 1 | 2
VH13 | Deleted
VH14 | Battery fails to charge | Battery fails to charge (internal or external). | User error - Ventilator has not been charged whilst in storage | Delay of Treatment (Prolonged procedure) | N | N/A | Minor delay, no patient impact | 1 | PRD213 | Whenever an AC power supply is available, the ventilator recharges the internal battery |  |  | 2 | 2 | 1 | 1 | P2 scores are based on clinical expert opinion, engineering inputs, and complaint data | 10038637 PB560-520 Trace Matrix | 10038637 PB560-520 Trace Matrix | Yes | This risk is acceptable and has been reduced as far as possible. The benefits of home care ventilation outweighs this potential risk.
 |  |  | DFMEA: Power Supply PCBA - Current control for battery charge (Constant current Generator) ACDC POWER cables ports |  | N | N/A | Delay with minor patient impact (e.g., extended manual ventilation, stable patient). | 2 | PRD217 | The ventilator is able to estimate battery ageing. |  |  | 2 | 2 | 1 | 1
 |  |  |  |  | N | N/A | Delay with major patient impact (e.g., extended manual ventilation, unstable severe pulmonary status) | 3 | PRD220 | When the Ventilator is in Active Ventilation State, the time to fully charge the internal battery from a complete discharge does not exceed 13 hours. | Battery charge level is displayed in time whilst ventilating and in % while on standby |  | 2 | 2 | 1 | 1
 |  |  |  |  | N | N/A | Prolonged delay with major patient impact,. replacement ventilator unavailable (e.g., extended manual ventilation, unstable severe pulmonary status,) | 4 | PRD157 | Real time battery life indicator will adjust the indication of battery time remaining depending on current ventilator settings and/or setting changes |  | Manual - WARNING: Before using the ventilator’s internal battery, ensure that the battery is fully charged and that the charge holds. Back up ventilators or those in storage should be connected to an AC power source to protect the integrity of the battery. | 2 | 1 | 1 | 2
 |  |  |  |  | Y | N/A | Death | 5 | PRD199 |  | Battery alarms EMPTY BATTERY ALARM - Internal battery capacity < 10 min. or 3% CHECK BATTERY CHARGE ALARM - Internal battery charging failure |  | 2 | 1 | 1 | 2
 |  |  |  | Respiratory failure | N | 2484 | Symptomatic early clinical intervention; Requires increased ventilatory support of one or more parameters | 2 | PRD243 |  |  | Manual - WARNING: Before using the ventilator’s internal battery, ensure that the battery is fully charged and that the charge holds. Back up ventilators or those in storage should be connected to an AC power source to protect the integrity of the battery. | 2 | 1 | 1 | 1
 |  |  |  |  | N | 2484 | Symptomatic; Requires multiple ventilator adjustments, administration of medication, and/or elective change from non-invasive to invasive ventilation. | 3 | PRD423 |  |  | WARNING: The maximum recommended shelf life of the internal battery is two (2) years. Do not use a battery that has been stored for two years prior to its first use. | 2 | 1 | 1 | 1
 |  |  |  |  | N | 2484 | Symptomatic; Requires move from non-invasive to invasive ventilation with emergent intubation. | 4 | PRD377 | The ventilator packaging includes the storage duration recommended before recharging the internal batteries. |  |  | 2 | 1 | 1 | 2
 |  |  |  |  | N | 2484 | Death | 5 | PRD155 | Design - Battery Power indicator flashes when battery is charging |  |  | 2 | 1 | 1 | 2
 |  |  |  |  | Y |  |  |  | PRD309 |  | LOW BATTERY alarm | Manual - WARNING: When the “LOW BATTERY“ alarm is triggered, immediately connect the ventilator to an AC power supply to maintain ventilation and recharge the internal battery.
 |  |  |  |  | N |  |  |  |  |  |  | Manual - WARNING: To ensure that ventilation continues uninterrupted ensure alternative power sources are available (AC power source, extra batteries, or an auxiliary DC car adapter). Be prepared for the possibility of power failure by having an alternative means of ventilation ready for use—particularly for ventilator-dependent patients.
 |  |  |  |  | Y |  |  |  | PRD197 |  | AC POWER DISCONNECTION alarm
 |  |  |  |  | N |  |  |  | PRD435 |  |  | Manual - Warnings - While the ventilator is in use, an alternative means of ventilation should always be available in the event of a ventilator problem. This is particularly true for ventilator-dependent patients. Supplementary observation, appropriate for the patient's condition, is also recommended.
 |  |  |  |  | N |  |  |  | PRD433 (560) |  |  | PB560 - WARNING: A ventilator-dependent patient should always be monitored by trained and competent medical personnel. Ensure that the patient’s caregiver is able and prepared to take suitable action in the event the ventilator identifies an alarmed condition or experiences a problem.
 |  |  |  |  | N |  |  |  | PRD216 |  |  | PB560 - WARNING: Even if the “INTERNAL BATTERY” charging indicator is off, charging of the battery may sometimes be incomplete if the ambient temperature is above 40°C (104°F) because of the battery’s internal heat safety device.
VH15 | Battery level indication is inaccurate | Displayed Battery level indicator displays incorrect charge status of battery. | SWFMEA: - Incorrect battery level monitor Software algorithms are showing incorrect % | Delay of Treatment (Prolonged procedure) | N | N/A | Minor delay, no patient impact | 1 | PRD155 | Design - Battery Power indicator flashes when battery is charging |  |  | 1 | 2 | 1 | 1 | P2 scores are based on clinical expert opinion, engineering inputs, and complaint data | 10038637 PB560-520 Trace Matrix | 10038637 PB560-520 Trace Matrix | Yes | This risk is acceptable and has been reduced as far as possible. The benefits of home care ventilation outweighs this potential risk.
 |  |  | PM schedule not adhered to |  | N | N/A | Delay with minor patient impact (e.g., extended manual ventilation, stable patient). | 2 | PRD156 | Real time battery life indicator will adjust the indication of battery percent available depending on current ventilator settings and/or setting changes |  |  | 1 | 2 | 1 | 1
 |  |  |  |  | N | N/A | Delay with major patient impact (e.g., extended manual ventilation, unstable severe pulmonary status) | 3 | PRD157 | Real time battery life indicator will adjust the indication of battery time remaining depending on current ventilator settings and/or setting changes |  | Manual - WARNING: Before using the ventilator’s internal battery, ensure that the battery is fully charged and that the charge holds. Back up ventilators or those in storage should be connected to an AC power source to protect the integrity of the battery. | 1 | 1 | 1 | 1
 |  |  |  |  | N | N/A | Prolonged delay with major patient impact,. replacement ventilator unavailable (e.g., extended manual ventilation, unstable severe pulmonary status,) | 4 | PRD158 | The ventilator provides a visual indication of the active ventilator power source (AC, DC or Battery) that is operational in all ventilator states and modes. |  | Manual - WARNING: To ensure that ventilation continues uninterrupted ensure alternative power sources are available (AC power source, extra batteries, or an auxiliary DC car adapter). Be prepared for the possibility of power failure by having an alternative means of ventilation ready for use—particularly for ventilator-dependent patients. | 1 | 1 | 1 | 2
 |  |  |  |  | N | N/A | Death | 5 | PRD219 | When the Ventilator is in Ventilation Stand-by State, the time to fully charge the internal battery from a complete discharge does not exceed 6 hours. |  |  | 1 | 1 | 1 | 2
 |  |  |  | Respiratory failure | N | 2484 | Symptomatic early clinical intervention; Requires increased ventilatory support of one or more parameters | 2 | PRD220 | When the Ventilator is in Active Ventilation State, the time to fully charge the internal battery from a complete discharge does not exceed 13 hours. | Battery charge level is displayed in time whilst ventilating and in % while on standby |  | 1 | 1 | 1 | 1
 |  |  |  |  | N | 2484 | Symptomatic; Requires multiple ventilator adjustments, administration of medication, and/or elective change from non-invasive to invasive ventilation. | 3 | PRD357 | PM schedule - battery charge level information is tested during PM |  |  | 1 | 1 | 1 | 1
 |  |  |  |  | N | 2484 | Symptomatic; Requires move from non-invasive to invasive ventilation with emergent intubation. | 4 | PRD243 |  |  | Manual - WARNING: Before using the ventilator’s internal battery, ensure that the battery is fully charged and that the charge holds. Back up ventilators or those in storage should be connected to an AC power source to protect the integrity of the battery. | 1 | 1 | 1 | 2
 |  |  |  |  | N | 2484 | Death | 5 | PRD423 |  |  | WARNING: The maximum recommended shelf life of the internal battery is two (2) years. Do not use a battery that has been stored for two years prior to its first use. WARNING: Periodic recharging is important to help maximize useful life of the battery. Do not store the internal battery for extended periods, without recharging, as this may reduce the maximum life. | 1 | 1 | 1 | 2
 |  |  |  |  | N |  |  |  | PRD377 | The ventilator packaging shall include the storage duration recommended before recharging the internal batteries.
 |  |  |  |  | Y |  |  |  | PRD199 |  | Battery alarm CHECK BATTERY CHARGE ALARM - Internal battery charging failure
 |  |  |  |  | Y |  |  |  | PRD194 |  | Low Battery Alarm: A ventilator operating on internal battery shall provide a high priority alarm when the estimated remaining operating time is 30 minutes or below.
 |  |  |  |  | N |  |  |  | PRD195 |  | Empty Battery Alarm: A ventilator operating on internal battery shall provide a high priority alarm when the estimated remaining operating time is 10 minutes or below.
 |  |  |  |  | Y |  |  |  | PRD309 |  | LOW BATTERY alarm | Manual - WARNING: When the “LOW BATTERY“ alarm is triggered, immediately connect the ventilator to an AC power supply to maintain ventilation and recharge the internal battery.
 |  |  |  |  | Y |  |  |  | PRD197 |  | AC POWER DISCONNECTION alarm
 |  |  |  |  | Y |  |  |  | PRD53 PRD54 |  | Security shut down alarm will sound on total power loss
 |  |  |  |  | N |  |  |  |  |  |  | Manual - WARNING: To ensure that ventilation continues uninterrupted ensure alternative power sources are available (AC power source, extra batteries, or an auxiliary DC car adapter). Be prepared for the possibility of power failure by having an alternative means of ventilation ready for use—particularly for ventilator-dependent patients.
 |  |  |  |  | N |  |  |  | PRD435 |  |  | Manual - Warnings - While the ventilator is in use, an alternative means of ventilation should always be available in the event of a ventilator problem. This is particularly true for ventilator-dependent patients. Supplementary observation, appropriate for the patient's condition, is also recommended.
 |  |  |  |  | N |  |  |  | PRD433 (560) |  |  | PB560 - WARNING: A ventilator-dependent patient should always be monitored by trained and competent medical personnel. Ensure that the patient’s caregiver is able and prepared to take suitable action in the event the ventilator identifies an alarmed condition or experiences a problem.
VH16 | Battery does not power ventilator | No power when on battery. Ventilator fails to switch to battery. | User does not connect to AC or DC power No Preventative Maintenance - battery life exceeded | Delay of Treatment (Prolonged procedure) | N | N/A | Minor delay, no patient impact | 1 | PRD158 | Visual LED indication of the active ventilator power source (AC, DC or Battery) that is operational in all ventilator states and modes. | - |  | 1 | 3 | 1 | 1 | P2 scores are based on clinical expert opinion, engineering inputs, and complaint data | 10038637 PB560-520 Trace Matrix | 10038637 PB560-520 Trace Matrix | Yes | This risk is acceptable and has been reduced as far as possible. The benefits of home care ventilation outweighs this potential risk.
 |  |  | DFMEA: Power Supply PCBA - reference 3 V supply Micro-controller Cooling fan control (ventilator) Cooling fan connector |  | Y | N/A | Delay with minor patient impact (e.g., extended manual ventilation, stable patient). | 2 | PRD197 |  | AC POWER DISCONNECTION alarm |  | 1 | 2 | 1 | 1
 |  |  |  |  | Y | N/A | Delay with major patient impact (e.g., extended manual ventilation, unstable severe pulmonary status) | 3 | PRD198 |  | DC POWER DISCONNECTION alarm |  | 1 | 1 | 1 | 1
 |  |  |  |  | Y | N/A | Prolonged delay with major patient impact,. replacement ventilator unavailable (e.g., extended manual ventilation, unstable severe pulmonary status,) | 4 | PRD199 |  | Battery alarms EMPTY BATTERY ALARM - Internal battery capacity < 10 min. or 3% CHECK BATTERY CHARGE ALARM - Internal battery charging failure |  | 1 | 1 | 1 | 2
 |  |  |  |  |  | N/A | Death | 5 |  |  |  |  | 1 | 1 | 1 | 2
 |  |  |  | Respiratory failure |  | 2484 | Symptomatic; Requires move from non-invasive to invasive ventilation with emergent intubation. | 4 | PRD423 |  |  |  | 1 | 1 | 1 | 2
 |  |  |  |  | N | 2484 | Death | 5 | PRD407 |  |  | WARNING: Ensure that the ventilator’s internal battery is fully charged before connecting the ventilator to an external DC power source. Powering the ventilator using an external 12– 30 VDC power source (via the DC power cable) does not enable its internal battery to recharge. | 1 | 1 | 1 | 2
 |  |  |  | Hypoventilation | N | 1916 | Asymptomatic; PaCO2 or ETCO2 elevated. | 1 | PRD212 |  |  | PB560 WARNING: Due to its limited internal battery’s reserve capacity, the ventilator should only be operated on the internal battery when no other power source is available. Ensure that the internal battery never becomes fully discharged. | 1 | 3 | 1 | 1
 |  |  |  |  |  | 1916 | Symptomatic; PaCO2 or ETCO2 elevated. ↓ in Minute Ventilation, requires minor ventilator adjustment | 2 |  |  |  |  | 1 | 3 | 1 | 1
 |  |  |  |  |  | 1916 | Symptomatic; PaCO2 or ETCO2 severely elevated. Severe ↓ in Minute Ventilation, requires major ventilator adjustment | 3 |  |  |  |  | 1 | 2 | 1 | 1
 |  |  |  |  |  | 1916 | Symptomatic; PaCO2 or ETCO2 severely elevated/loss of respiratory drive. Severe ↓ in Minute Ventilation, requires Major change of therapy (e.g., ECMO, CPR, Intubation) | 4 | PRD435 |  |  |  | 1 | 1 | 1 | 2
 |  |  |  |  |  | 1916 | Death | 5 | PRD433 (560) |  |  |  | 1 | 1 | 1 | 2
 |  |  |  | Oxygen saturation, Low (Hypoxemia) |  | 2477 | Episodic shortness of breath; resolved with rest. Asymptomatic: self resolving. | 1 |  |  |  |  | 1 | 2 | 1 | 1
 |  |  |  |  |  | 2477 | Symptomatic and/or ≤92: Minor increase or incremental increases in oxygen levels resolves | 2 |  |  |  |  | 1 | 1 | 1 | 1
 |  |  |  |  |  | 2477 | Symptomatic ≤88% : Major increase or incremental increases in oxygen levels and increase ventilatory support. | 3 |  |  |  |  | 1 | 1 | 1 | 1
 |  |  |  |  |  | 2477 | Symptomatic ≤85% prolonged or ≤ 80% sudden and continuous dropping : Major increase or incremental increases in oxygen levels and Major increase ventilatory support. | 4 |  |  |  |  | 1 | 1 | 1 | 2
 |  |  |  |  |  | 2477 | Death | 5 |  |  |  |  | 1 | 1 | 1 | 2
VH17 | Battery is unable to be removed | Battery is stuck or jammed in place. |  | This hazard is not applicable to this ventilator - This failure has been designed out as the PB500 series battery is changed during service. All service engineers must ne trained. Service departments should have the tools necessary to unscrew the door and to drill out the screws if the screws are damaged.
VH18 | Biohazard Exposure | During the use or handling of the device or system (e.g. device surface, circuit, humidifiers) user or patient is exposed to pathogens. | Re-use of single patient use components | Infection | N | 1930 | Infection that resolves without intervention (skin infection-see cellulitis) | 1 | PRD259 |  |  | WARNING: Single Use accessories should not be reused | 2 | 1 | 1 | 1 | P2 scores are based on clinical expert opinion, engineering inputs, and complaint data | 10038637 PB560-520 Trace Matrix | 10038637 PB560-520 Trace Matrix | Yes | This risk is acceptable and has been reduced as far as possible. The benefits of home care ventilation outweighs this potential risk.
 |  |  | contaminated component package Inadequate package design Improper package handling |  | N | 1930 | An infection that requires medical intervention Examples: Antibiotics, antifungals, or antivirals, or medication by mouth or inhalation, Incision/drainage see abscess | 2 | PRD260 |  |  | WARNING: Before opening the packaging for the Patient Circuit, ensure that no damage is evident to the packaging or its contents. Do not use if evidence of damage exists. | 2 | 1 | 1 | 1
 |  |  | User Error - Water trap condensate spilled on removal |  | N | 1930 | Symptomatic; IV antibiotics required with increased ventilatory support. An infection that requires more advanced medical intervention | 3 | PRD262 |  |  | Manual - It is highly recommended that you install a bacteria filter (see Figure 4-12. ) on both single and double-limb circuits. | 2 | 1 | 1 | 1
 |  |  | Contamination of blower vanes due to air inlet filter not being in place |  | N | 1930 | Symptomatic; IV antibiotics required, increased ventilatory support, isolation, refractory to treatment. | 4 | PRD35 |  | The air inlet filter is designed such that an unclean state can be easily detected |  | 2 | 1 | 1 | 2
 |  |  | DFMEA FILTRATION SYSTEM - Exhalation Bacteria filter Inspiratory Bacteria Filter |  | N | 1930 | Death | 5 | PRD251 |  |  | WARNING: Regularly check the cleanliness of the air inlet filter located on the rear of the ventilator. If necessary, replace the filter before the recommended replacement period is over (see Chapter 8, “Routine Maintenance”). This is particularly important when the ventilator is installed on a wheelchair, because environmental conditions may cause the filter to become dirty more rapidly. WARNING: The air inlet filter is not reusable; do not attempt to wash, clean, or reuse it. Failing to replace a dirty air inlet filter, or operating the ventilator without a filter, may cause serious damage to the ventilator. | 2 | 1 | 1 | 2
 |  |  |  | No consequences or impact to patient | N | 2199 | Delay in treatment causes user frustration only (Severity would be no harm) | 1 | PRD264 |  | PM Schedule | Service Manual - WARNING - Do not start ventilation until you ensure the device is correctly assembled, that the air inlet filter is properly installed and unobstructed, and that there is proper clearance all around the unit. Also ensure the patient circuit is correctly connected to both the ventilator and the patient, and that the patient circuit, including all hoses, is not damaged or obstructed. | 2 | 1 | 1 | 1
 |  |  |  | Cross Patient Exposure To Body Fluids | N | 1745 | No medical treatment required if in contact with in-tack skin | 1 | PRD280 | The ventilator packaging and shipping complies with ADR and IATA regulations depending on the level of dangerous goods contained in the device. All finished goods units deemed critical to the safe operation of the ventilator will be subjected to the ISTA-2A test standard ensuring that product integrity is maintained after the distribution environment. |  |  | 2 | 1 | 1 | 1
 |  |  |  |  | N |  | prophylactic treatment required for exposure to blood or body fluid | 2 |  |  |  | Manual - WARNING: The exhalation block is intended for single use by a single patient . It may periodically be cleaned, but it cannot be disinfected or sterilized. To maintain good measurement quality when used continuously, clean the exhalation block periodically. The exhalation block should be changed every 4 months and cannot be reused with any other patient. | 2 | 1 | 1 | 1
 |  |  |  |  | N |  | extended prophylactic treatment required for exposure to blood or body fluid | 3 | PRD405 |  |  | WARNING: A patient treated by mechanical ventilation is highly vulnerable to the risks of infection. Dirty or contaminated equipment is a potential source of infection. Clean the ventilator and its accessories regularly and systematically before and after each use and following any maintenance procedure to reduce the risks of infection. The use of a bacterial filter at the ventilator’s outlet – or both ports if a double-limb circuit is used – is highly recommended. Refer to chapter 7, “Cleaning”. To reduce the risk of infection, wash your hands thoroughly before and after handling the ventilator or its accessories. | 2 | 1 | 1 | 1
 |  |  |  |  | N |  | life threatening infection, hospitalization or prolonged hospitalization, or greater than 3 drugs | 4 |  | DAR filters labelling indicates filtration efficiencies | Acceptable DAR filters are listed as accessories in the User Manual |  | 2 | 1 | 1 | 2
 |  |  |  |  | N |  | Death | 5 |  |  | Air Inlet filter is on the Preventative Maintenance schedule |  | 2 | 1 | 1 | 2
 |  |  |  |  | N |  |  |  | PRD231 |  |  | WARNING: The patient circuit is intended for single use by a single patient and should be changed according to the manufacturer’s recommendations and according to the patient circuit lifetime. Refer to the instructions for use supplied by the manufacturer of the patient circuit (included with the ventilator) and Chapter 4, “Installation and Assembly.”
 |  |  |  |  | N |  |  |  | PRD435 |  |  | Manual - Warnings - While the ventilator is in use, an alternative means of ventilation should always be available in the event of a ventilator problem. This is particularly true for ventilator-dependent patients. Supplementary observation, appropriate for the patient's condition, is also recommended.
 |  |  |  |  | N |  |  |  | PRD433 (560) |  |  | PB560 - WARNING: A ventilator-dependent patient should always be monitored by trained and competent medical personnel. Ensure that the patient’s caregiver is able and prepared to take suitable action in the event the ventilator identifies an alarmed condition or experiences a problem.
 |  |  |  |  | N |  |  |  | PRD1 |  |  | Warning: Lay responsible organisation (e.g. Homecare Vent Provider) must contact local authorities to determine the proper method of disposal of potentially bio hazardous parts and accessories.
VH19 | Breathing circuit leak | Breathing circuit has a leak | Use of a single limb patient circuit with a vented NIV interface and with a volume mode leading to insufficient ventilation | Hypoventilation | Y | 1916 | Asymptomatic; PaCO2 or ETCO2 elevated. | 1 | PRD350 |  | Low pressure alarms CHECK EXH VALVE CHECK PROXIMAL LINE1 NO PROXIMAL LINE2 |  | 2 | 3 | 1 | 1 | P2 scores are based on clinical expert opinion, engineering inputs, and complaint data | 10038637 PB560-520 Trace Matrix | 10038637 PB560-520 Trace Matrix | Yes | This risk is acceptable and has been reduced as far as possible. The benefits of home care ventilation outweighs this potential risk.
 |  |  | Leak in patient circuit |  | Y | 1916 | Symptomatic; PaCO2 or ETCO2 elevated. ↓ in Minute Ventilation, requires minor ventilator adjustment | 2 | PRD174 |  | PATIENT DISCONNECTION alarm |  | 2 | 3 | 1 | 1
 |  |  | Patient movement, Patient circuit accidentally disconnected (ventilation loss) |  | N | 1916 | Symptomatic; PaCO2 or ETCO2 severely elevated. Severe ↓ in Minute Ventilation, requires major ventilator adjustment | 3 | PRD273 |  | All device operational connectors and ports are labeled |  | 2 | 2 | 1 | 1
 |  |  | DFMEA humidifier - connection to the breathing circuit water traps - connection to the breathing circuit |  | N | 1916 | Symptomatic; PaCO2 or ETCO2 severely elevated/loss of respiratory drive. Severe ↓ in Minute Ventilation, requires Major change of therapy (e.g., ECMO, CPR, Intubation) | 4 | PRD248 |  |  | Manual WARNING: The patient circuit should always be positioned to avoid hindering the patient's movements, to prevent accidental disconnection or leakage, and to minimize the risk of patient strangulation. | 2 | 1 | 1 | 2
 |  |  | Use Error - Incorrect set-up of patient circuit |  | Y | 1916 | Death | 5 | PRD178 (560) PRD179 (560) |  | HIGH VTE ALARM LOW VTE Alarm | Manual - WARNING: Minimum and maximum VTE alarm parameters must be properly set to warn in the event of patient disconnection. | 2 | 1 | 1 | 2
 |  |  |  | Oxygen saturation, Low (Hypoxemia) | Y | 2477 | Episodic shortness of breath; resolved with rest. Asymptomatic: self resolving. | 1 | PRD 180 PRD181 PRD188 |  | HIGH VTI ALARM LOW VTI Alarm |  | 2 | 3 | 1 | 1
 |  |  |  |  | Y | 2477 | Symptomatic and/or ≤92: Minor increase or incremental increases in oxygen levels resolves | 2 | PRD184 |  | NO PROXIMAL LINE2 alarm |  | 2 | 2 | 1 | 1
 |  |  |  |  | Y | 2477 | Symptomatic ≤88% : Major increase or incremental increases in oxygen levels and increase ventilatory support. | 3 | PRD320 |  | Leakage alarms HIGH LEAKAGE Alarm EXH VALVE LEAKAGE ALARM E SENS FAULT OR CIRC LEAK |  | 2 | 1 | 1 | 1
 |  |  |  |  | N | 2477 | Symptomatic ≤85% prolonged or ≤ 80% sudden and continuous dropping : Major increase or incremental increases in oxygen levels and Major increase ventilatory support. | 4 | PRD189 (560) |  | HIGH RATE alarm (due to autotriggering) |  | 2 | 1 | 1 | 2
 |  |  |  |  | N | 2477 | Death | 5 | PRD240 |  |  | Manual - WARNING: After assembling, cleaning, or reassembling the patient circuit, and on a daily basis, inspect the hoses and other components to ensure that there are no cracks or leaks and that all connections are secure. On a DAILY basis, inspect the patient circuit to ensure that it shows no signs of damage, is properly connected, and is operating correctly without leakage. | 2 | 1 | 1 | 2
 |  |  |  | Respiratory failure | N | 2484 | Symptomatic early clinical intervention; Requires increased ventilatory support of one or more parameters | 2 | PRD306 |  |  | Manual - WARNING: The patient circuit should not be changed during ventilation. | 2 | 2 | 1 | 1
 |  |  |  |  | N | 2484 | Symptomatic; Requires multiple ventilator adjustments, administration of medication, and/or elective change from non-invasive to invasive ventilation. | 3 | PRD230 |  |  | Description of patient circuit | 2 | 2 | 1 | 1
 |  |  |  |  | N | 2484 | Symptomatic; Requires move from non-invasive to invasive ventilation with emergent intubation. | 4 | PRD415 |  |  | Manual - WARNING: When using non-invasive ventilation (NIV), without an exhalation valve, use a vented nose or face mask or a non vented combined with a leak accessory. When using noninvasive ventilation (NIV), with an exhalation valve, use a non vented mask. | 2 | 1 | 1 | 2
 |  |  |  |  | N | 2484 | Death | 5 | PRD245 |  |  | WARNING: The patient circuit is intended for single use by a single patient and should be changed according to the manufacturer’s recommendations and according to the patient circuit lifetime. | 2 | 1 | 1 | 2
 |  |  |  | Anxiety | N | 2328 | Mild symptoms; intervention not indicated; eliminate stressors Asymptomatic asynchrony observed on monitoring. | 1 | PRD280 | Circuit packaging is ISTA-2 complaint |  |  | 2 | 2 | 1 | 1
 |  |  |  |  | N | 2328 | Symptomatic; requiring minor change in ventilator settings (e.g., sensitivity, eSens) | 2 |  | Design - Water traps are screwed in and keyed |  |  | 2 | 1 | 1 | 1
 |  |  |  |  | N | 2328 | Symptomatic with vital sign impacts; requiring major change in ventilator settings | 3 |  |  |  | WARNING: Users must always possess an additional breathing circuit and exhalation valve | 2 | 1 | 1 | 1
 |  |  |  |  | N | 2328 | Symptomatic requiring major change in therapy (e.g., sedation, paralytics, controlled ventilation) | 4 |  |  |  | The circuit check menu displays instructions for the steps needed to conduct the test and a confirmation step and a warning to ensure the patient is not connected prior to conducting the test. | 2 | 1 | 1 | 2
 |  |  |  |  | N | 2328 | See cause of anxiety | 5 |  | Design - Hose connections are designed that the fittings are not easily pulled out, optional swivel adapter for patient wye |  |  | 2 | 1 | 1 | 2
 |  |  |  | Delay of Treatment (Prolonged procedure) | N | N/A | Minor delay, no patient impact | 1 | PRD247 |  |  | WARNING: To ensure correct and lasting operation of the ventilator, ensure that its air circulation holes (main inlet or cooling) are never obstructed. Place the device in an area where air can freely circulate around the ventilator and avoid installing it near floating fabrics, such as curtains. Do not place the ventilator in a position where a child, Pet or pest can reach it or in any position that might cause it to fall on the patient or someone else. Ensure that the ventilator’s immediate surroundings allow for the proper operational connection of the device without folding, pinching, or damaging any of the required cables or tubes, and that the connection of the patient circuit to the patient provides for a secure, comfortable fit. | 2 | 2 | 1 | 1
 |  |  |  |  | N | N/A | Delay with minor patient impact (e.g., extended manual ventilation, stable patient). | 2 | PRD459 | Circuit leak test |  |  | 2 | 2 | 1 | 1
 |  |  |  |  | N | N/A | Delay with major patient impact (e.g., extended manual ventilation, unstable severe pulmonary status) | 3 | PRD435 |  |  | Manual - Warnings - While the ventilator is in use, an alternative means of ventilation should always be available in the event of a ventilator problem. This is particularly true for ventilator-dependent patients. Supplementary observation, appropriate for the patient's condition, is also recommended. | 2 | 1 | 1 | 1
 |  |  |  |  | N | N/A | Prolonged delay with major patient impact,. replacement ventilator unavailable (e.g., extended manual ventilation, unstable severe pulmonary status,) | 4 | PRD433 (560) |  |  | PB560 - WARNING: A ventilator-dependent patient should always be monitored by trained and competent medical personnel. Ensure that the patient’s caregiver is able and prepared to take suitable action in the event the ventilator identifies an alarmed condition or experiences a problem. | 2 | 1 | 1 | 2
 |  |  |  |  | N | N/A | Death | 5 | PRD411 |  |  | WARNING: The level of inspiratory resistance of the circuit and accessories (bacteria filter, humidifier, and so on) must be as low as possible. Settings – particularly the PATIENT DISCONNECTION alarm, High inspired volume (High VTI), and Low inspired volume (Low VTI) settings – must be periodically adjusted according to changes in the patient circuit resistance – especially when filters are replaced. | 2 | 1 | 1 | 2
VH20 | Breathing circuit occluded, pinched or kinked | Patient Breathing circuit has a restriction causing decreased pressure, flow, or volume. | Mucus impaction, not sufficient ventilation. | Hypoventilation | Y | 1916 | Asymptomatic; PaCO2 or ETCO2 elevated. | 1 | PRD176 |  | HIGH PRESSURE alarm HIGH baseline pressure alarm | WARNING: The patient circuit should always be positioned to avoid hindering the patient's movements, to prevent accidental disconnection or leakage, and to minimize the risk of patient strangulation. | 2 | 3 | 1 | 1 | P2 scores are based on clinical expert opinion, engineering inputs, and complaint data | 10038637 PB560-520 Trace Matrix | 10038637 PB560-520 Trace Matrix | Yes | This risk is acceptable and has been reduced as far as possible. The benefits of home care ventilation outweighs this potential risk.
 |  |  | User error - water inside exhalation block due to humidifier use |  | Y | 1916 | Symptomatic; PaCO2 or ETCO2 elevated. ↓ in Minute Ventilation, requires minor ventilator adjustment | 2 | PRD190 |  | OCCLUSION CHECK CIRCUIT alarms |  | 2 | 2 | 1 | 1
 |  |  | Use error - Patient circuit occluded, pinched or kinked |  | Y | 1916 | Symptomatic; PaCO2 or ETCO2 severely elevated. Severe ↓ in Minute Ventilation, requires major ventilator adjustment | 3 | PRD189 (560) |  | CHECK EXHALATION VALVE alarm (PB560) |  | 2 | 1 | 1 | 1
 |  |  | Patient circuit arm faulty or not used properly installed on the cart. |  | Y | 1916 | Symptomatic; PaCO2 or ETCO2 severely elevated/loss of respiratory drive. Severe ↓ in Minute Ventilation, requires Major change of therapy (e.g., ECMO, CPR, Intubation) | 4 | PRD174 |  | Low pressure alarms CHECK EXH VALVE CHECK PROXIMAL LINE1 |  | 2 | 1 | 1 | 2
 |  |  | SWFMEA No detection of Occlusion |  | N | 1916 | Death | 5 | PRD306 |  |  | Manual - WARNING: The patient circuit should not be changed during ventilation. | 2 | 1 | 1 | 2
 |  |  |  | Lung, Over inflation | N | 2397 | Asymptomatic-Observed | 1 |  |  |  | WARNING: Users must always possess an additional breathing circuit and exhalation valve | 2 | 2 | 1 | 1
 |  |  |  |  | N | 2397 | Small ↑ mean airway pressure, requiring minor change in ventilator settings. | 2 | PRD230 |  |  | Description of patient circuit | 2 | 1 | 1 | 1
 |  |  |  |  | N | 2397 | Moderate ↑ mean airway pressure, radiographical signs, requiring major change in ventilator settings. | 3 | PRD234 |  |  | Manual - WARNING: After assembling, cleaning, or reassembling the patient circuit, and on a daily basis, inspect the hoses and other components to ensure that there are no cracks or leaks and that all connections are secure. | 2 | 1 | 1 | 1
 |  |  |  |  | N | 2397 | Critical↑ mean airway pressure, radiographical signs parenchemal destruction (e.g. blebs), requiring major change in ventilator therapy (e.g., ECMO, HFV) | 4 | PRD248 |  |  | Manual - WARNING: The patient circuit should always be positioned to avoid hindering the patient's movements, to prevent accidental disconnection or leakage, and to minimize the risk of patient strangulation. | 2 | 1 | 1 | 2
 |  |  |  |  | N | 2397 | Death | 5 | PRD273 |  | All device operational connectors and ports are labeled |  | 2 | 1 | 1 | 2
 |  |  |  | Oxygen saturation, Low (Hypoxemia) | N | 2477 | Episodic shortness of breath; resolved with rest. Asymptomatic: self resolving. | 1 | PRD412 |  |  | WARNING: Always position a humidification device so that it is lower than both the ventilator and the patient. Use water traps, if necessary, to limit water in the patient circuit and precautions should be taken when discarding the fluid in the water trap, discard per local ordinance for proper disposal. If a heated humidifier is used, you should always monitor the temperature of the gas delivered to the patient. Gas delivered from the ventilator that becomes too hot may burn the patient's airway. | 2 | 2 | 1 | 1
 |  |  |  |  | Y | 2477 | Symptomatic and/or ≤92: Minor increase or incremental increases in oxygen levels resolves | 2 | PRD174 |  | PATIENT DISCONNECTION alarm |  | 2 | 1 | 1 | 1
 |  |  |  |  | Y | 2477 | Symptomatic ≤88% : Major increase or incremental increases in oxygen levels and increase ventilatory support. | 3 | PRD178 (560) PRD179 (560) |  | HIGH VTE ALARM LOW VTE Alarm |  | 2 | 1 | 1 | 1
 |  |  |  |  | Y | 2477 | Symptomatic ≤85% prolonged or ≤ 80% sudden and continuous dropping : Major increase or incremental increases in oxygen levels and Major increase ventilatory support. | 4 | PRD 180 PRD181 PRD188 |  | HIGH VTI ALARM LOW VTI Alarm |  | 2 | 1 | 1 | 2
 |  |  |  |  | N | 2477 | Death | 5 | PRD247 |  |  | WARNING: To ensure correct and lasting operation of the ventilator, ensure that its air circulation holes (main inlet or cooling) are never obstructed. Place the device in an area where air can freely circulate around the ventilator and avoid installing it near floating fabrics, such as curtains. Do not place the ventilator in a position where a child, Pet or pest can reach it or in any position that might cause it to fall on the patient or someone else. Ensure that the ventilator’s immediate surroundings allow for the proper operational connection of the device without folding, pinching, or damaging any of the required cables or tubes, and that the connection of the patient circuit to the patient provides for a secure, comfortable fit. | 2 | 1 | 1 | 2
 |  |  |  | Delay of Treatment (Prolonged procedure) | Y | N/A | Minor delay, no patient impact | 1 | PRD103 PRD104 PRD105 PRD106 |  | LOW PRESSURE alarms |  | 2 | 2 | 1 | 1
 |  |  |  |  | N | N/A | Delay with minor patient impact (e.g., extended manual ventilation, stable patient). | 2 | PRD107 PRD108 PRD109 |  | High pressure threshold |  | 2 | 2 | 1 | 1
 |  |  |  |  | Y | N/A | Delay with major patient impact (e.g., extended manual ventilation, unstable severe pulmonary status) | 3 | PRD110 PRD111 |  | low inspiratory tidal volume alarm LOW VTI alarm |  | 2 | 1 | 1 | 1
 |  |  |  |  | N | N/A | Prolonged delay with major patient impact,. replacement ventilator unavailable (e.g., extended manual ventilation, unstable severe pulmonary status,) | 4 | PRD112 |  | High VTI settings in CPAP, PRES A/C, PSV ST, and PSIMV Modes |  | 2 | 1 | 1 | 2
 |  |  |  |  | N | N/A | Death | 5 | PRD173 |  | HIGH RATE alarm |  | 2 | 1 | 1 | 2
 |  |  |  |  | Y |  |  |  | PRD174 |  | PATIENT DISCONNECTION alarm
 |  |  |  |  | N |  |  |  | PRD435 |  |  | Manual - Warnings - While the ventilator is in use, an alternative means of ventilation should always be available in the event of a ventilator problem. This is particularly true for ventilator-dependent patients. Supplementary observation, appropriate for the patient's condition, is also recommended.
 |  |  |  |  | N |  |  |  | PRD433 (560) |  |  | PB560 - WARNING: A ventilator-dependent patient should always be monitored by trained and competent medical personnel. Ensure that the patient’s caregiver is able and prepared to take suitable action in the event the ventilator identifies an alarmed condition or experiences a problem.
 |  |  |  |  | N |  |  |  | PRD411 |  |  | WARNING: Resistance of the exhalation valve and accessories (water traps, filters, HMEs, etc.) must be as low as possible. WARNING: The exhalation valve must allow rapid discharge of the circuit pressure. Ensure that the exhalation valve is always clean and its evacuation aperture (exhaust port) is never obstructed.
VH21 | Breath not delivered | Ventilator does not deliver breaths per prescribed setting | User Error - Circuit Check is enabled while the patient is being ventilated or connected to the ventilator. | Hypoventilation | N | 1916 | Asymptomatic; PaCO2 or ETCO2 elevated. | 1 | PRD459 | Circuit leak test |  |  | 2 | 3 | 1 | 1 | P2 scores are based on clinical expert opinion, engineering inputs, and complaint data | 10038637 PB560-520 Trace Matrix | 10038637 PB560-520 Trace Matrix | Yes | This risk is acceptable and has been reduced as far as possible. The benefits of home care ventilation outweighs this potential risk.
 |  |  | User Error - ventilator settings inappropriate for patient (e.g. I sense, E sense) |  | N | 1916 | Symptomatic; PaCO2 or ETCO2 elevated. ↓ in Minute Ventilation, requires minor ventilator adjustment | 2 | PRD460 PRD461 | The circuit check menu displays instructions for the steps needed to conduct the test and a confirmation step and a warning to ensure the patient is not connected prior to conducting the test. |  |  | 2 | 2 | 1 | 1
 |  |  | DFMEA Pneumatic fittings - Inspiratory flow sensor fitting |  | N | 1916 | Symptomatic; PaCO2 or ETCO2 severely elevated. Severe ↓ in Minute Ventilation, requires major ventilator adjustment | 3 | PRD162 |  | graphics to display patient response |  | 2 | 1 | 1 | 1
 |  |  | SWFMEA Breath Delivery Initiates breaths incorrectly Alarms No detection of Apnea No detection of disconnect |  | N | 1916 | Symptomatic; PaCO2 or ETCO2 severely elevated/loss of respiratory drive. Severe ↓ in Minute Ventilation, requires Major change of therapy (e.g., ECMO, CPR, Intubation) | 4 | PRD237 |  |  | WARNING: Before operating the ventilator, read, understand, and strictly follow the information contained in Chapter 1, “Safety Information.” | 2 | 1 | 1 | 2
 |  |  | Use Error - Incorrect set-up of patient circuit |  | N | 1916 | Death | 5 | PRD413 |  |  | WARNING: Adding accessories to the ventilator breathing circuit, such as a humidifier and water trap(s), may result in a decrease in tidal volume delivered to the patient due to the added compressible volume of the accessory. Always assure that the patient is receiving the appropriate inspired volume when altering the breathing circuit configuration. | 2 | 1 | 1 | 2
 |  |  |  | Anxiety | N | 2328 | Mild symptoms; intervention not indicated; eliminate stressors Asymptomatic asynchrony observed on monitoring. | 1 | PRD430 |  |  | WARNING: This ventilator must be used only under the responsibility and on the prescription of a doctor. | 2 | 3 | 1 | 1
 |  |  |  |  | N | 2328 | Symptomatic; requiring minor change in ventilator settings (e.g., sensitivity, eSens) | 2 | PRD289 |  | Leak is displayed |  | 2 | 2 | 1 | 1
 |  |  |  |  | Y | 2328 | Symptomatic with vital sign impacts; requiring major change in ventilator settings | 3 | PRD320 |  | Leakage alarms HIGH LEAKAGE Alarm EXH VALVE LEAKAGE ALARM E SENS FAULT OR CIRC LEAK |  | 2 | 1 | 1 | 1
 |  |  |  |  | Y | 2328 | Symptomatic requiring major change in therapy (e.g., sedation, paralytics, controlled ventilation) | 4 | PRD172 |  | Apnea alarms |  | 2 | 1 | 1 | 2
 |  |  |  |  | N |  |  |  | PRD173 |  | HIGH RATE alarm
 |  |  |  |  | N |  |  |  | PRD74 | PEEP adjustment range
 |  |  |  |  | N |  |  |  | PRD102 | APNEA TIME adjustment range
 |  |  |  |  | N |  |  |  | PRD388 PRD87 | Inspiratory Sensitivity settings Exhalation sensitivity settings
 |  |  |  |  | Y |  |  |  | PRD103 PRD104 PRD105 PRD106 |  | LOW PRESSURE alarms
 |  |  |  |  | Y |  |  |  | PRD110 PRD111 |  | low inspiratory tidal volume alarm LOW VTI alarm
 |  |  |  |  | N |  |  |  | PRD112 |  | High VTI settings in CPAP, PRES A/C, PSV ST, and PSIMV Modes
 |  |  |  |  | N |  |  |  | PRD435 |  |  | Manual - Warnings - While the ventilator is in use, an alternative means of ventilation should always be available in the event of a ventilator problem. This is particularly true for ventilator-dependent patients. Supplementary observation, appropriate for the patient's condition, is also recommended. Provide the patient with an alternate means of ventilation before conducting any verification tests.
 |  |  |  |  | N |  |  |  | PRD74 |  |  | PEEP adjustment range
 |  |  |  |  | N |  |  |  | PRD433 (560) |  |  | PB560 - WARNING: A ventilator-dependent patient should always be monitored by trained and competent medical personnel. Ensure that the patient’s caregiver is able and prepared to take suitable action in the event the ventilator identifies an alarmed condition or experiences a problem.
 |  |  |  |  | N |  |  |  | PRD54 |  |  | PB560 - WARNING: A continuous alarm condition will be activated if the ventilator power switch is turned off while ventilation is in progress. When the power switch is turned back on again, ventilation will resume without having to press the VENTILATION ON/OFF button.
 |  |  |  |  | N |  |  |  | PRD432 (560) |  |  | PB560 - WARNING: Do not allow a patient to remain connected to the ventilator when ventilation is stopped, because a substantial quantity of exhalation gas, primarily carbon dioxide, may be inhaled by the patient. In some circumstances, inhaling carbon dioxide may lead to under-ventilation, suffocation, and serious injury or death.
 |  |  |  |  | N |  |  |  | PRD435 |  |  | WARNING: Always have immediate access to an alternative means of ventilation, which is ready for use, to avoid patient death or serious injury
 |  |  |  |  | N |  |  |  | PRD1 |  |  | WARNING: When using the ventilator in a carrying case, only use a carrying case that is listed in the instructions for use to prevent adverse ventilator performance which can consequently result in Patient death
 |  |  |  |  | N |  |  |  | PRD1 |  |  | WARNING: Do not cover the ventilator or place in a position that affects proper operation”, eg. front or lateral opening.
 |  |  |  |  | N |  |  |  | PRD320a |  |  | WARNING: The setting of the Max Leak alarm must be adjusted for the patient, but must also be set low enough to allow the HIGH LEAKAGE alarm to trigger properly. Perform the Max Leak Test (refer to section E.7, “Max Leak Test”) to ensure the Max Leak alarm is functionally properly . This alarm only applies to Leak configuration (NIV)
 |  |  |  |  | N |  |  |  | PRD424a |  |  | WARNING: Ensure that the ventilator is switched off and disconnected from all external power supplies before installation.
 |  |  |  |  | N |  |  |  | PRD320a |  |  | WARNING: The Max Leak alarm setting must be adjusted for the patient, but must also be set low enough to allow the High Leakage alarm to trigger properly. Perform the max leak test (see section F.2, Max Leak Test (Only NIV)) to ensure that the alarm is functioning properly. This alarm only applies to leak configuration (NIV).
VH22 | Ventilator autotrigger | Inappropriate triggering of ventilation when the patient is not attempting to initiate a breath(e.g. inappropriate sensitivity, cardiogenic noise, leaks) | User Error - Incorrect set up by Clinician - too sensitive settings | Lung, Over inflation | N | 2397 | Asymptomatic-Observed | 1 | PRD161 | Indication of patient triggered breath |  |  | 2 | 2 | 1 | 1 | P2 scores are based on clinical expert opinion, engineering inputs, and complaint data | 10038637 PB560-520 Trace Matrix | 10038637 PB560-520 Trace Matrix | Yes | This risk is acceptable and has been reduced as far as possible. The benefits of home care ventilation outweighs this potential risk.
 |  |  | leaks |  | Y | 2397 | Small ↑ mean airway pressure, requiring minor change in ventilator settings. | 2 | PRD178 (560) PRD179 (560) |  | HIGH VTE ALARM LOW VTE Alarm | Manual - WARNING: Minimum and maximum VTE alarm parameters must be properly set to warn in the event of patient disconnection. | 2 | 2 | 1 | 1
 |  |  | DFMEA CPU PCBA - Inspiratory flow measure PNEUMATIC FITTINGS - flow sensor fitting |  | Y | 2397 | Moderate ↑ mean airway pressure, radiographical signs, requiring major change in ventilator settings. | 3 | PRD320 |  | Leakage alarms HIGH LEAKAGE Alarm EXH VALVE LEAKAGE ALARM E SENS FAULT OR CIRC LEAK |  | 2 | 1 | 1 | 1
 |  |  | SWFMEA Breath delivery Initiates breaths incorrectly Alarms No detection of High Breath Rate/Respiratory Rate |  | N | 2397 | Critical↑ mean airway pressure, radiographical signs parenchemal destruction (e.g. blebs), requiring major change in ventilator therapy (e.g., ECMO, HFV) | 4 | PRD173 |  | HIGH RATE alarm |  | 2 | 1 | 1 | 2
 |  |  |  |  | N | 2397 | Death | 5 | PRD191 |  | BREATH TIME CYCLED Alarm |  | 2 | 1 | 1 | 2
 |  |  |  | Hyperventilation | N | 1910 | Asymptomatic; PaCO2 or ETCO2 low. Mild tachypnea. | 1 | PRD359 | CHECKLIST |  | WARNING: Ensure that the I Sens setting is not set to OFF when ventilating patients capable of triggering spontaneous breaths. Carefully modify the trigger threshold setting to reduce the risk of ventilator autotriggering. Level 0P, the most sensitive inspiratory trigger, is recommended for pediatric use. For an adult, this setting may result in ventilator autotriggering. | 2 | 3 | 1 | 1
 |  |  |  |  | N | 1910 | Symptomatic; PaCO2 or ETCO2 low. Tachypnea/↑ in Minute Ventilation, requires minor ventilator adjustment | 2 | PRD307 |  |  | WARNING: If APNEA TIME is set to a value higher than 60/Control R then the APNEA alarm will not activate. If an APNEA alarm is required, set the APNEA setting to YES in the Preferences Menu. | 2 | 2 | 1 | 1
 |  |  |  |  | N | 1910 | Symptomatic; PaCO2 or ETCO2 low. Tachypnea/↑ in Minute Ventilation, requires major ventilator adjustment | 3 | PRD447 (560) |  |  | WARNING: The Apnea Alarm should be set to YES for ventilator dependent patients. | 2 | 1 | 1 | 1
 |  |  |  | Hypoventilation | N | 1916 | Asymptomatic; PaCO2 or ETCO2 elevated. | 1 | PRD296 |  |  | Manual - Operational Verification Checklist - Ensure the patient breathing circuit is correctly attached to the ventilator | 2 | 2 | 1 | 1
 |  |  |  |  | N | 1916 | Symptomatic; PaCO2 or ETCO2 elevated. ↓ in Minute Ventilation, requires minor ventilator adjustment | 2 | PRD107 PRD108 PRD109 |  | High pressure threshold |  | 2 | 2 | 1 | 1
 |  |  |  |  | Y | 1916 | Symptomatic; PaCO2 or ETCO2 severely elevated. Severe ↓ in Minute Ventilation, requires major ventilator adjustment | 3 | PRD110 PRD111 |  | low inspiratory tidal volume alarm LOW VTI alarm |  | 2 | 1 | 1 | 1
 |  |  |  | Anxiety | N | 2328 | Mild symptoms; intervention not indicated; eliminate stressors Asymptomatic asynchrony observed on monitoring. | 1 | PRD162 |  | graphics to display patient response |  | 2 | 3 | 1 | 1
 |  |  |  |  | N | 2328 | Symptomatic; requiring minor change in ventilator settings (e.g., sensitivity, eSens) | 2 | PRD86 | EXH SENS setting |  |  | 2 | 2 | 1 | 1
 |  |  |  |  | N | 2328 | Symptomatic with vital sign impacts; requiring major change in ventilator settings | 3 | PRD83 | adjustable trigger sensitivity setting |  |  | 2 | 1 | 1 | 1
 |  |  |  |  | N |  |  |  | PRD435 |  |  | Manual - Warnings - While the ventilator is in use, an alternative means of ventilation should always be available in the event of a ventilator problem. This is particularly true for ventilator-dependent patients. Supplementary observation, appropriate for the patient's condition, is also recommended.
 |  |  |  |  | N |  |  |  | PRD433 (560) |  |  | PB560 - WARNING: A ventilator-dependent patient should always be monitored by trained and competent medical personnel. Ensure that the patient’s caregiver is able and prepared to take suitable action in the event the ventilator identifies an alarmed condition or experiences a problem.
VH23 | Burning smell or odor | Device or device accessory exhibits a burning smell or odor |  | Anxiety | N | 2328 | Mild symptoms; intervention not indicated; eliminate stressors Asymptomatic asynchrony observed on monitoring. | 1 |  | Design - Cooling fan will withdraw any smoke from the interior of the ventilator |  |  | 2 | 2 | 1 | 1 | P2 scores are based on clinical expert opinion, engineering inputs, and complaint data | 10038637 PB560-520 Trace Matrix | 10038637 PB560-520 Trace Matrix | Yes | This risk is acceptable and has been reduced as far as possible. The benefits of home care ventilation outweighs this potential risk.
 |  |  | DFMEA Blower Turbine |  | N | 2328 | Symptomatic; requiring minor change in ventilator settings (e.g., sensitivity, eSens) | 2 |  | Design - No inlet into the gas pathway from the ventilator electrical interior |  |  | 2 | 2 | 1 | 1
 |  |  |  |  | N | 2328 | Symptomatic with vital sign impacts; requiring major change in ventilator settings | 3 |  | All PCBAs are IPC compliant which includes flame retardant materials |  |  | 2 | 1 | 1 | 1
 |  |  |  |  | N | 2328 | Symptomatic requiring major change in therapy (e.g., sedation, paralytics, controlled ventilation) | 4 | PRD435 |  |  | Manual - Warnings - While the ventilator is in use, an alternative means of ventilation should always be available in the event of a ventilator problem. This is particularly true for ventilator-dependent patients. Supplementary observation, appropriate for the patient's condition, is also recommended. | 2 | 1 | 1 | 2
 |  |  |  | Chemical (gas or liquid)exposure , Hazardous | N | 2570-Chemical Exposure | Minor Inflammation, no treatment needed | 1 | PRD433 (560) |  |  | PB560 - WARNING: A ventilator-dependent patient should always be monitored by trained and competent medical personnel. Ensure that the patient’s caregiver is able and prepared to take suitable action in the event the ventilator identifies an alarmed condition or experiences a problem. | 2 | 2 | 1 | 1
 |  |  |  |  | N |  | Temporary injury or impairment that requires minor professional medical intervention | 2 | PRD1 | PB560 Ventilator is designed to meet the The ventilator complies with Medical Electrical Equipment: General Requirements for Safety IEC 60601-1 |  |  | 2 | 2 | 1 | 1
 |  |  |  |  |  |  | Results in injury or impairment requiring major professional medical intervention; May require hospitalization for treatment due to chemical exposure; Patient stable. | 3 |  |  |  |  | 2 | 1 | 1 | 1
 |  |  |  | No consequences or impact to patient |  | 2199 | Delay in treatment causes user frustration only (Severity would be no harm) | 1 |  |  |  |  | 2 | 3 | 1 | 1
 |  |  |  | Delay of Treatment (Prolonged procedure) |  | N/A | Minor delay, no patient impact | 1 |  |  |  |  | 2 | 3 | 1 | 1
 |  |  |  |  |  | N/A | Delay with minor patient impact (e.g., extended manual ventilation, stable patient). | 2 |  |  |  |  | 2 | 2 | 1 | 1
 |  |  |  |  |  | N/A | Delay with major patient impact (e.g., extended manual ventilation, unstable severe pulmonary status) | 3 |  |  |  |  | 2 | 1 | 1 | 1
 |  |  |  |  |  | N/A | Prolonged delay with major patient impact,. replacement ventilator unavailable (e.g., extended manual ventilation, unstable severe pulmonary status,) | 4 |  |  |  |  | 2 | 1 | 1 | 2
VH24 | Cable Entanglement | Device or device accessory that becomes entangled around patient or user | Patient circuit wraps around neck, legs, arms - patient or user harm | Tissue Damage/Tissue Trauma | N | 2104 | Minor tissue damage not requiring medical intervention (minor bruise); Self-limited; Minor bleeding/injury to tissue/vessels that may resolve without medical intervention | 1 |  |  | Breathing circuits come equipped with cable management clips. |  | 1 | 1 | 1 | 1 | P2 scores are based on clinical expert opinion, engineering inputs, and complaint data | 10038637 PB560-520 Trace Matrix | 10038637 PB560-520 Trace Matrix | Yes | This risk is acceptable and has been reduced as far as possible. The benefits of home care ventilation outweighs this potential risk.
 |  |  | Patient circuit wraps around neck, legs, arms - ventilator disconnect |  | N | 2104 | Tissue damage requiring minor suturing. Bleeding/injury to tissue/vessels that may resolve with minor medical intervention Examples: minor suture repair may be required (including closing of extended incision), no blood transfusions. | 2 | PRD248 |  |  | WARNING: The patient circuit should always be positioned to avoid hindering the patient's movements, to prevent accidental disconnection or leakage, and to minimize the risk of patient strangulation. | 1 | 1 | 1 | 1
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
