hesingh/ventilator/Medtronic/medtronic-pb560-ventilator-system-file-set-1/Electrical Schematics/PB560 - Electrical Schematics/10105965B00_10106052_POWERPACK2 BOARD (DUAL BATTERY).pdf

D | D
C | C
B | B
A | A
3 | Project: Powerpack2 (dual battery)

4

# Power supply & Switching Microcontroller

# 3. Bypass capacitors shall be distributed evenly amongst power

pins of the IC power and GND pin.

# 4. Always observe layout guidelines and documentation from the component

manufacturers, beside the indications and comments marked on schematics.

R?

# SHEET

# 1. Components marked with a dashed and crossed box will not

be installed during assembly.

# Title Page

# DESCRIPTION

# TABLE OF CONTENTS

2 | Block Diagram

NOTES: UNLESS OTHERWISE SPECIFIED.

1

2. Please refer to the 10106052 - Powerpack board (dual battery) Bill of Material (BOM) which provides all necessary component information for the final assembly.

# 5. J1 to J8 conn - Through hole components, place on Top side of the PCB

# 6. RL1, FL1, J9 & J11 conn - Through hole components, place on Top right side of the PCB

# 7. J12 conn - SMD component, place on Bottom left side of the PCB

8. Power tracks - marked with thick line on schematic, should be able to withstand minimum 3.3A continuous current route as wide as possible, minimum of 0.6mm.
9. Components names to be marked in silkscreen and also PCB board name, number and revision.
Revision Changes | REVISIONS
REV | DESCRIPTION | DATE | APPROVED
B B B | RELEASE PER ECO-R249715 RELEASE PER ECO-R249715 RELEASE PER ECO-R249715 | SEE AGILE SEE AGILE SEE AGILE | SEE AGILE SEE AGILE SEE AGILE
REV | DESCRIPTION
X01 | Initial release
X02 | D16 added, U1 part number updated to TPS7A1650Q1, C13,C16,C18,C20 to be mounted by default on PCBA.
X03 | Removed D16, replaced with T14, T15, R52 to R56. Capacitors C13, C15, C16, C17, C18, C19, C20, C21 removed. R5, R15 value changed to 18k. R41 value changed to 4.7k. R48 value changed to 62k. U1 changed to NCV87725D7S50R4G. Removed RS-232 interface (U5, C26, C27, C28, C29, C31, J14). Deleted TP1 to TP10. R57, R58 added. R4, R14, R50, R51, R57, R58, D15, T12, T13 marked as not installed.
A | Production release. Changed R26 to 68 Ohm & R32 to 2.2k.
B | Changed R32 to 470 Ohm.

# ORCAD CAPTURE DRAWING -ALL CHANGES MUST BE DONE IN ORCAD SYSTEM

# ORCAD CAPTURE DRAWING -ALL CHANGES MUST BE DONE IN ORCAD SYSTEM

# ORCAD CAPTURE DRAWING -ALL CHANGES MUST BE DONE IN ORCAD SYSTEM

SIZE SIZE SIZE B B B | MODEL MODEL MODEL PB500 PB500 PB500 | DWG NO. DWG NO. DWG NO. 10105965 10105965 10105965 | REV: REV: REV: B B B

# Carlsbad, CA 92008

# 2101 Faraday Avenue

# CONFIDENTIAL STATEMENT

### Copyright (C) 2013, Covidien The information contained in this document is the

proprietary and confidential property of Covidien.

### Supplied Data, Tooling, Partial or Finished Materials shall not be disclosed to others without

the written permissions of Covidien.

APPROVALS APPROVALS APPROVALS | DATE DATE DATE
DRAWN: DRAWN: DRAWN: | 14-May-2013 14-May-2013 14-May-2013 | SCHEMATIC DIAGRAM SCHEMATIC DIAGRAM SCHEMATIC DIAGRAM POWERPACK2 BOARD, PB500 POWERPACK2 BOARD, PB500 POWERPACK2 BOARD, PB500
ENGINEER: ENGINEER: ENGINEER: | 14-May-2013 14-May-2013 14-May-2013
SEE AGILE CHECKED CHECKED CHECKED | SEE AGILE
APPROVED APPROVED APPROVED SEE AGILE SEE AGILE SEE AGILE | SEE AGILE SEE AGILE SEE AGILE
RELEASED: RELEASED: RELEASED: SEE AGILE SEE AGILE SEE AGILE | SEE AGILE SEE AGILE SEE AGILE | SCALE: NONE SCALE: NONE SCALE: NONE | Template 10093694 Rev A Template 10093694 Rev A Template 10093694 Rev A | SHEET SHEET SHEET 1 1 1 4 4 4 of of of

# Carlsbad, CA 92008

# 2101 Faraday Avenue

# CONFIDENTIAL STATEMENT

### Copyright (C) 2013, Covidien The information contained in this document is the

proprietary and confidential property of Covidien.

### Supplied Data, Tooling, Partial or Finished Materials shall not be disclosed to others without

the written permissions of Covidien.

# Carlsbad, CA 92008

# 2101 Faraday Avenue

# CONFIDENTIAL STATEMENT

### Copyright (C) 2013, Covidien The information contained in this document is the

proprietary and confidential property of Covidien.

### Supplied Data, Tooling, Partial or Finished Materials shall not be disclosed to others without

the written permissions of Covidien.

# POWERPACK2 PCBA

## +BAT1

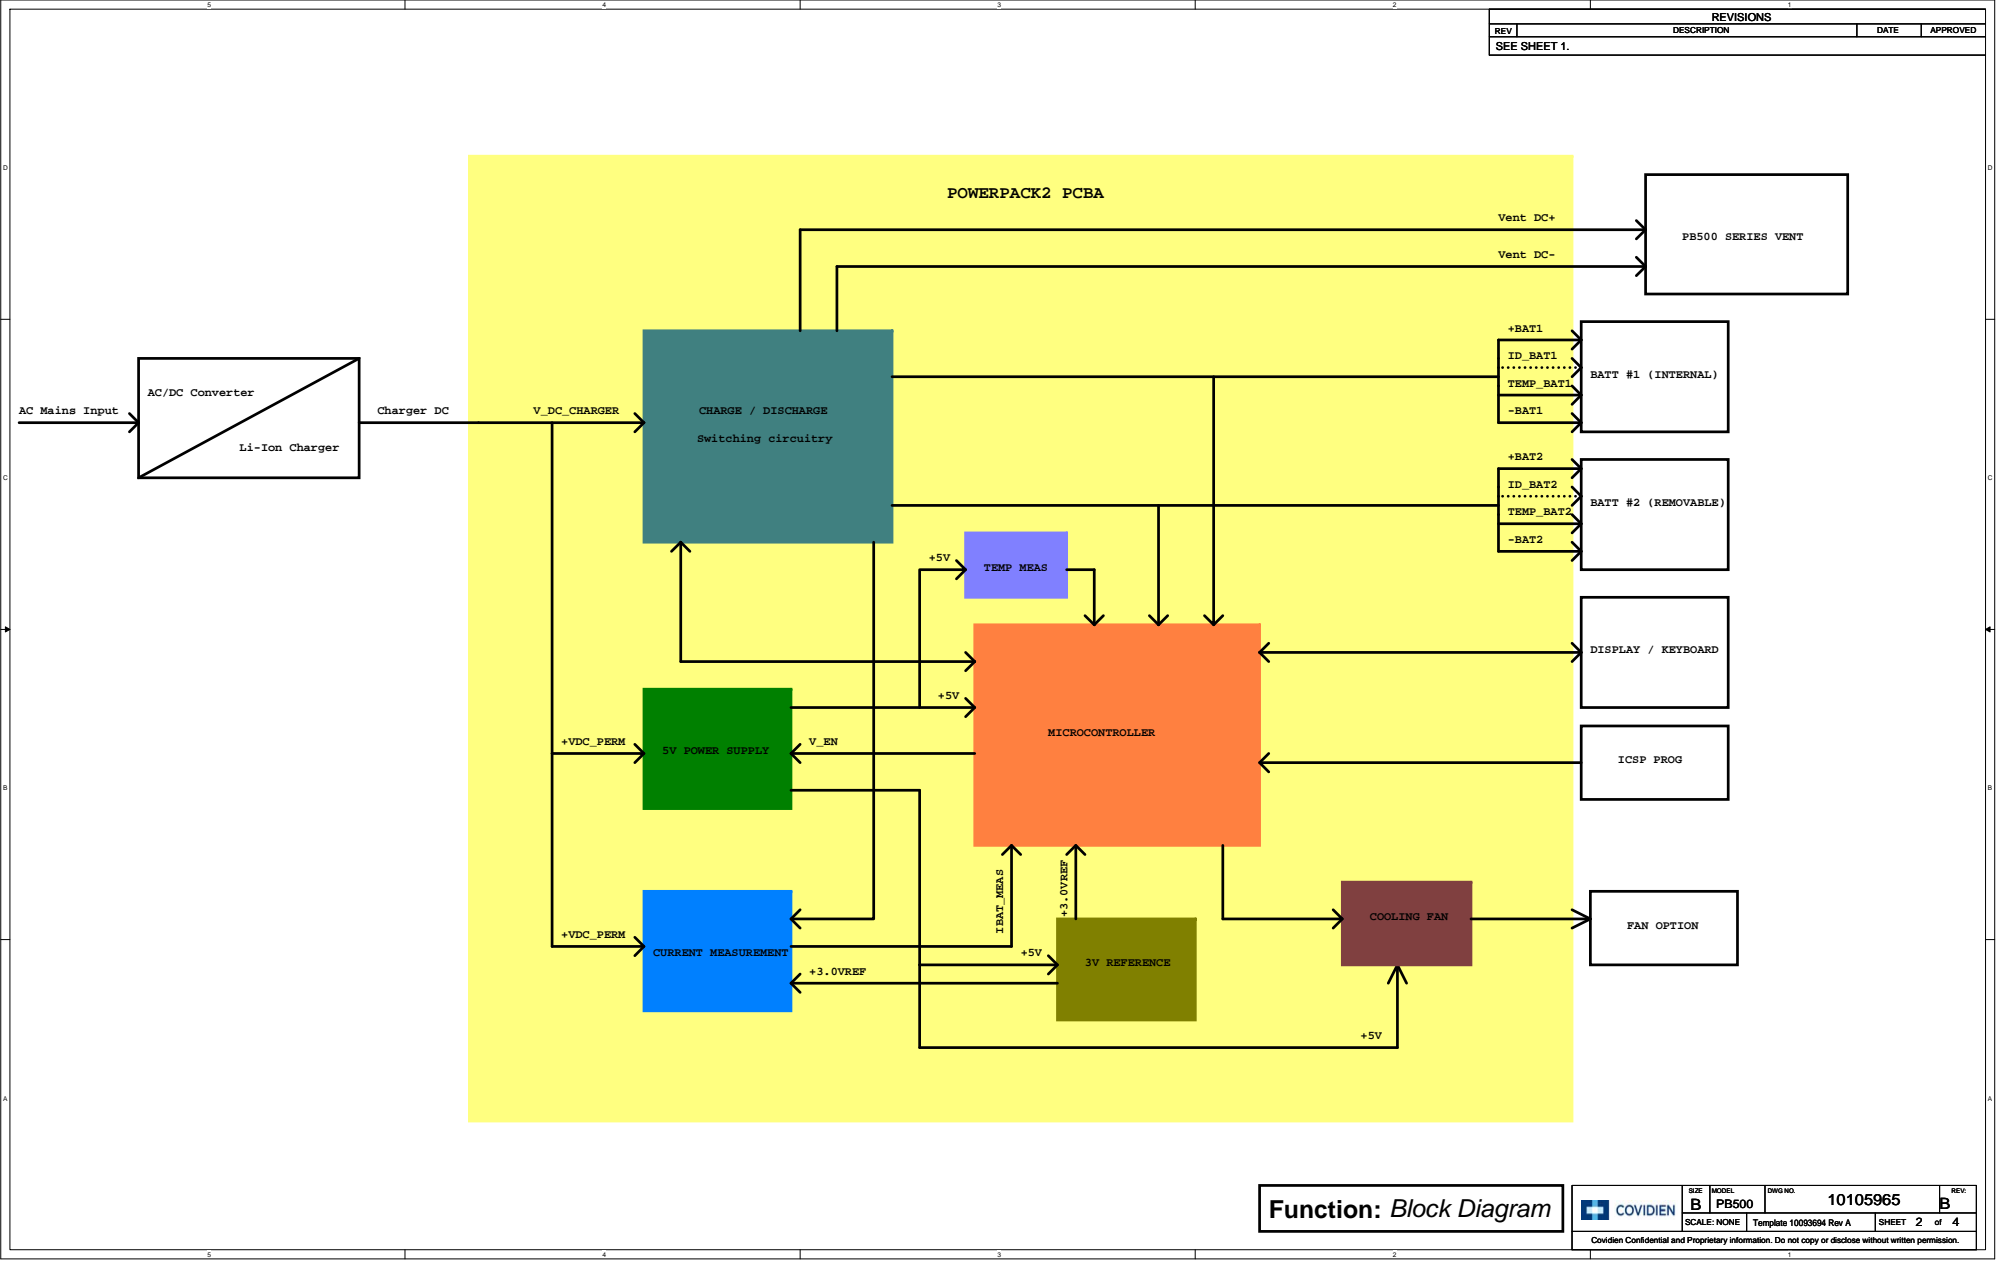
[picture p132: page 2]
V_DC_CHARGER; Switching circuitry; Charger DC; CHARGE / DISCHARGE; BATT #1 (INTERNAL); BATT #2 (REMOVABLE); +BAT2; MICROCONTROLLER; 5V POWER SUPPLY; +VDC_PERM; DISPLAY / KEYBOARD; 3V REFERENCE; CURRENT MEASUREMENT; IBAT_MEAS; +3.0VREF; COOLING FAN; FAN OPTION; ICSP PROG; PB500 SERIES VENT; Vent DC+; Vent DC-; TEMP MEAS +5V; SIZE; MODEL; REV:; SHEET; SCALE: NONE; DWG NO.; Template 10093694 Rev A; SEE SHEET 1.

ID_BAT1

TEMP_BAT1

AC/DC Converter

AC Mains Input

-BAT1

Li-Ion Charger

ID_BAT2

TEMP_BAT2

-BAT2

Function: Block Diagram

Covidien Confidential and Proprietary information. Do not copy or disclose without written permission.

# +5V Power Supply

# Switching block

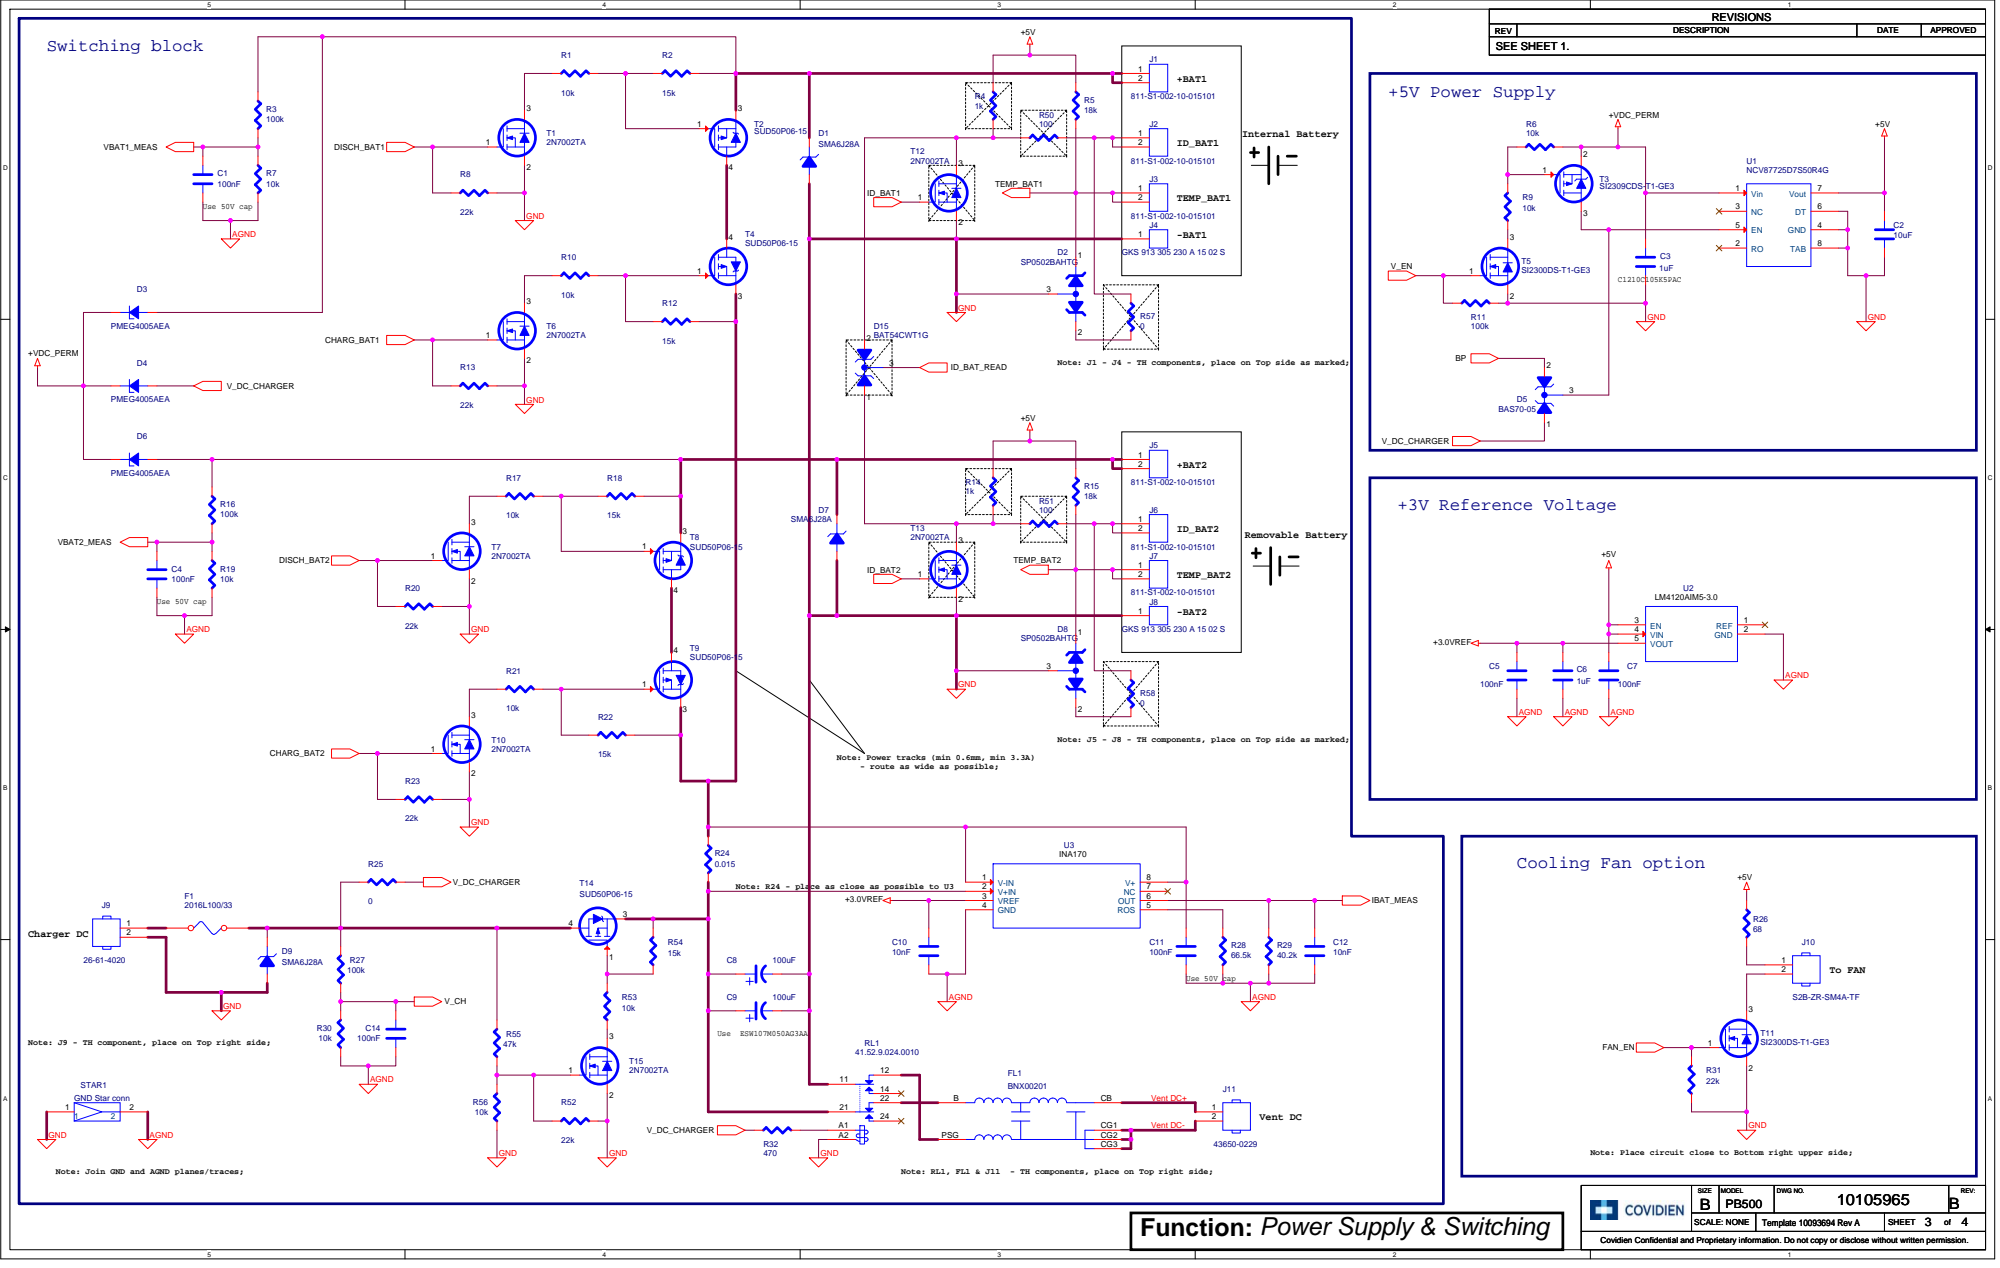
[picture p133: page 3]

Note: J1 - J4 - TH components, place on Top side as marked;

Note: J5 - J8 - TH components, place on Top side as marked;

Note: Power tracks (min 0.6mm, min 3.3A)
- route as wide as possible;

Note: R24 - place as close as possible to U3

Note: J9 - TH component, place on Top right side;

Note: Place circuit close to Bottom right upper side;

Function: Power Supply & Switching

Covidien Confidential and Proprietary information. Do not copy or disclose without written permission.

Microcontroller block | R33 1k

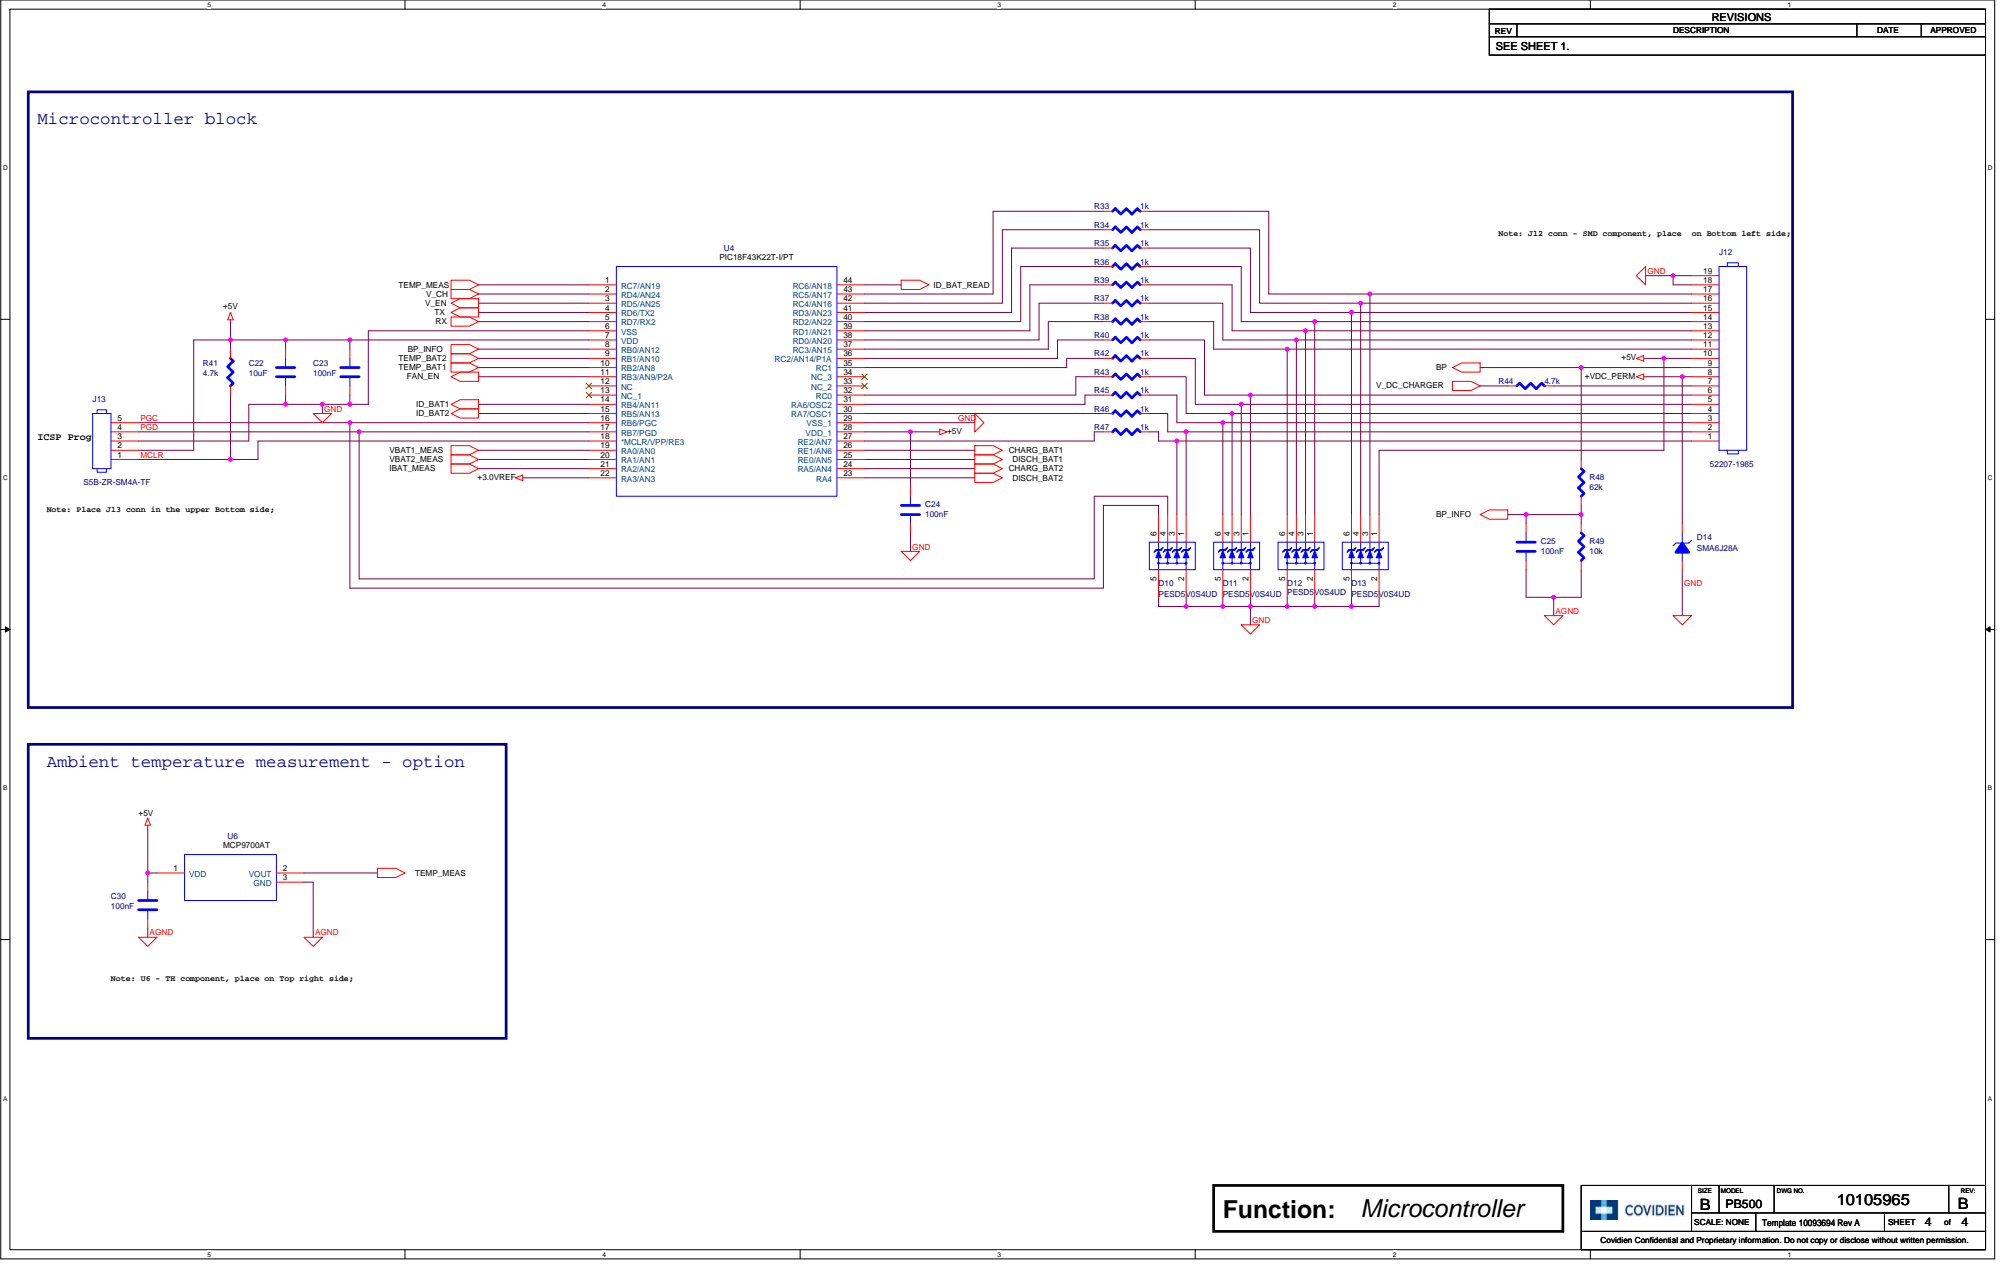
[picture p134: page 4]

Note: J12 conn - SMD component, place on Bottom left side;

15
14
13

Note: Place J13 conn in the upper Bottom side;

Ambient temperature measurement - option

Note: U6 - TH component, place on Top right side;

Covidien Confidential and Proprietary information. Do not copy or disclose without written permission.
