hesingh/ventilator/Medtronic/medtronic-pb560-ventilator-system-file-set-2/Mechanical Part Drawings/10000915/10000915B00.PDF

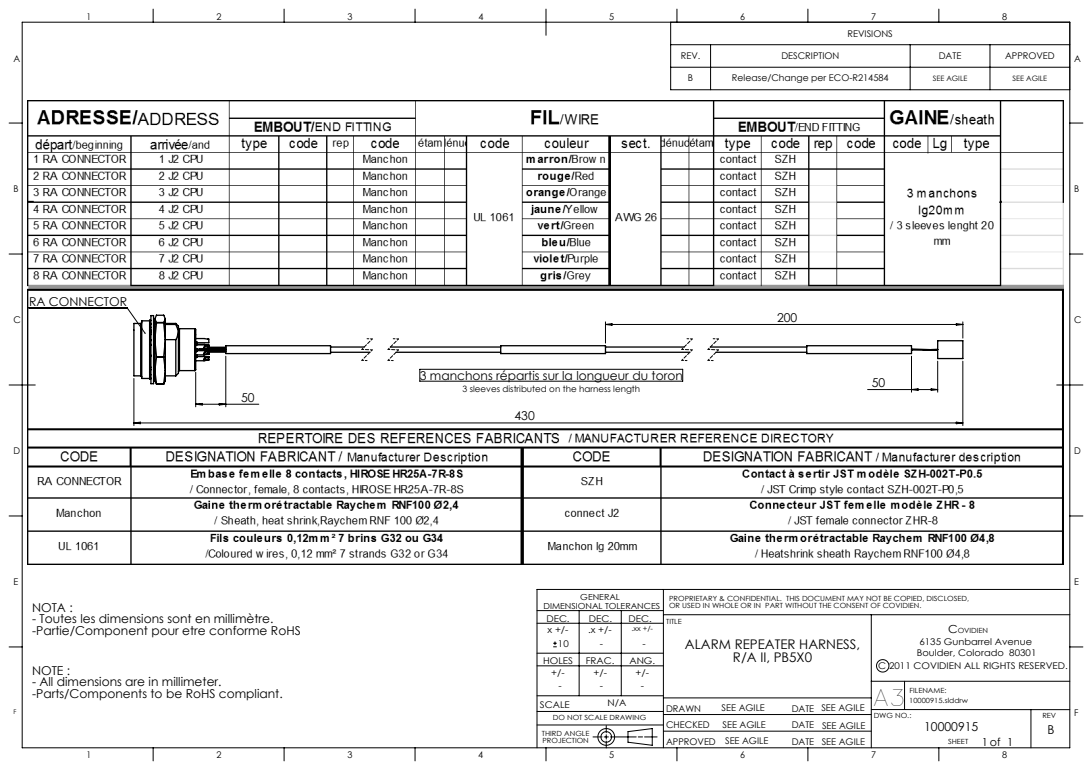
[picture p135: page 1]
RA CONNECTOR; Boulder, Colorado 80301; 6135 Gunbarrel Avenue; DWG NO.:; DIMENSIONAL TOLERANCES; THIRD ANGLE; DO NOT SCALE DRAWING; SEE AGILE

REVISIONS

REV. | DESCRIPTION | DATE | APPROVED
B | Release/Change per ECO-R214584 | SEE AGILE | SEE AGILE

3 manchons répartis sur la longueur du toron

3 sleeves distributed on the harness length

NOTA :
- Toutes les dimensions sont en millimètre.
-Partie/Component pour etre conforme RoHS

PROPRIETARY & CONFIDENTIAL. THIS DOCUMENT MAY NOT BE COPIED, DISCLOSED,
OR USED IN WHOLE OR IN PART WITHOUT THE CONSENT OF COVIDIEN.
TITLE
ALARM REPEATER HARNESS,

NOTE :
- All dimensions are in millimeter.
-Parts/Components to be RoHS compliant.

C 2011 COVIDIEN ALL RIGHTS RESERVED.
