hesingh/ventilator/Medtronic/medtronic-pb560-ventilator-system-file-set-2/Mechanical Part Drawings/10049560/10049560D00.PDF

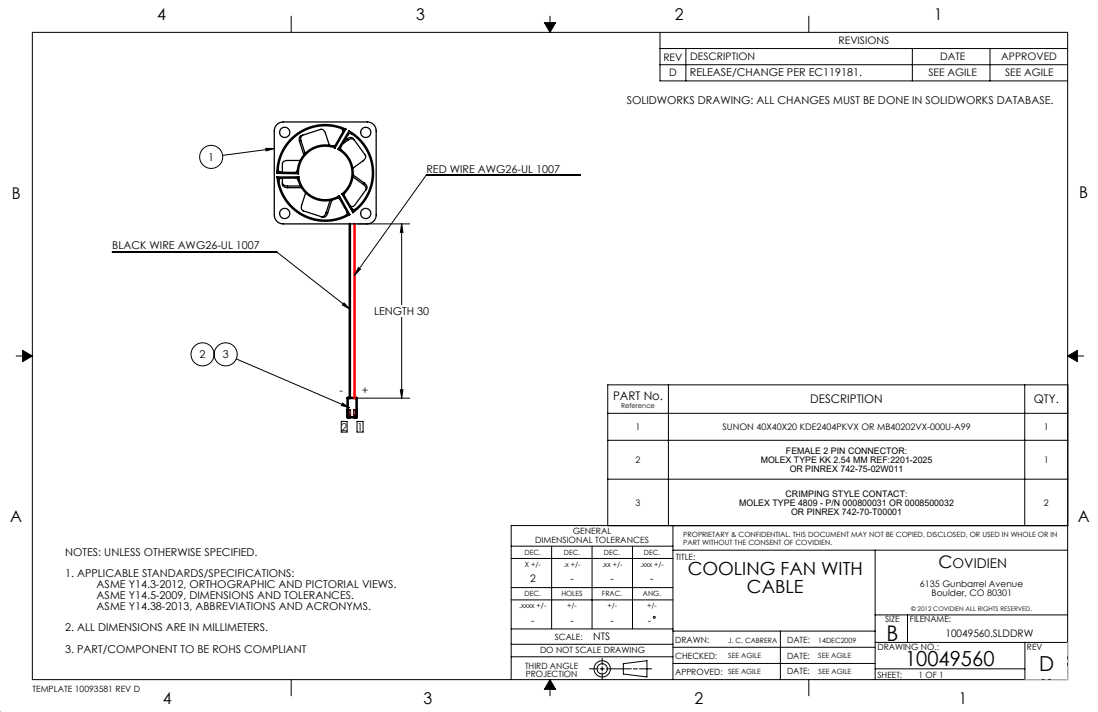
[picture p137: page 1]
LENGTH 30; 2 TEMPLATE 10093581 REV D; .xxxx +/-; THIRD ANGLE; .xxx +/-; SHEET:

REVISIONS

REV | DESCRIPTION | DATE | APPROVED
D | RELEASE/CHANGE PER EC119181. | SEE AGILE | SEE AGILE

SOLIDWORKS DRAWING: ALL CHANGES MUST BE DONE IN SOLIDWORKS DATABASE.

RED WIRE AWG26-UL 1007

BLACK WIRE AWG26-UL 1007

PART No. Reference | DESCRIPTION | QTY.

1 | SUNON 40X40X20 KDE2404PKVX OR MB40202VX-000U-A99 | 1

2 | FEMALE 2 PIN CONNECTOR: MOLEX TYPE KK 2.54 MM REF:2201-2025 OR PINREX 742-75-02W011 | 1

3 | CRIMPING STYLE CONTACT: MOLEX TYPE 4809 - P/N 000800031 OR 0008500032 OR PINREX 742-70-T00001 | 2

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

NOTES: UNLESS OTHERWISE SPECIFIED.
1. APPLICABLE STANDARDS/SPECIFICATIONS:
ASME Y14.3-2012, ORTHOGRAPHIC AND PICTORIAL VIEWS.
ASME Y14.5-2009, DIMENSIONS AND TOLERANCES.
ASME Y14.38-2013, ABBREVIATIONS AND ACRONYMS.
2. ALL DIMENSIONS ARE IN MILLIMETERS.
3. PART/COMPONENT TO BE ROHS COMPLIANT

TITLE: COOLING FAN WITH CABLE | COVIDIEN 6135 Gunbarrel Avenue Boulder, CO 80301 © 2012 COVIDIEN ALL RIGHTS RESERVED. B -

SIZE | FILENAME: 10049560.SLDDRW

NTS SCALE: | DRAWN: J. C. CABRERA CHECKED: SEE AGILE APPROVED: SEE AGILE | DATE: 14DEC2009 DATE: SEE AGILE DATE: SEE AGILE
DO NOT SCALE DRAWING | | | DRAWING NO.: 10049560 | REV D
