hesingh/ventilator/Medtronic/medtronic-pb560-ventilator-system-file-set-2/Mechanical Part Drawings/2967200/2967200C00.pdf

4 | 3 | 2 | 1

D

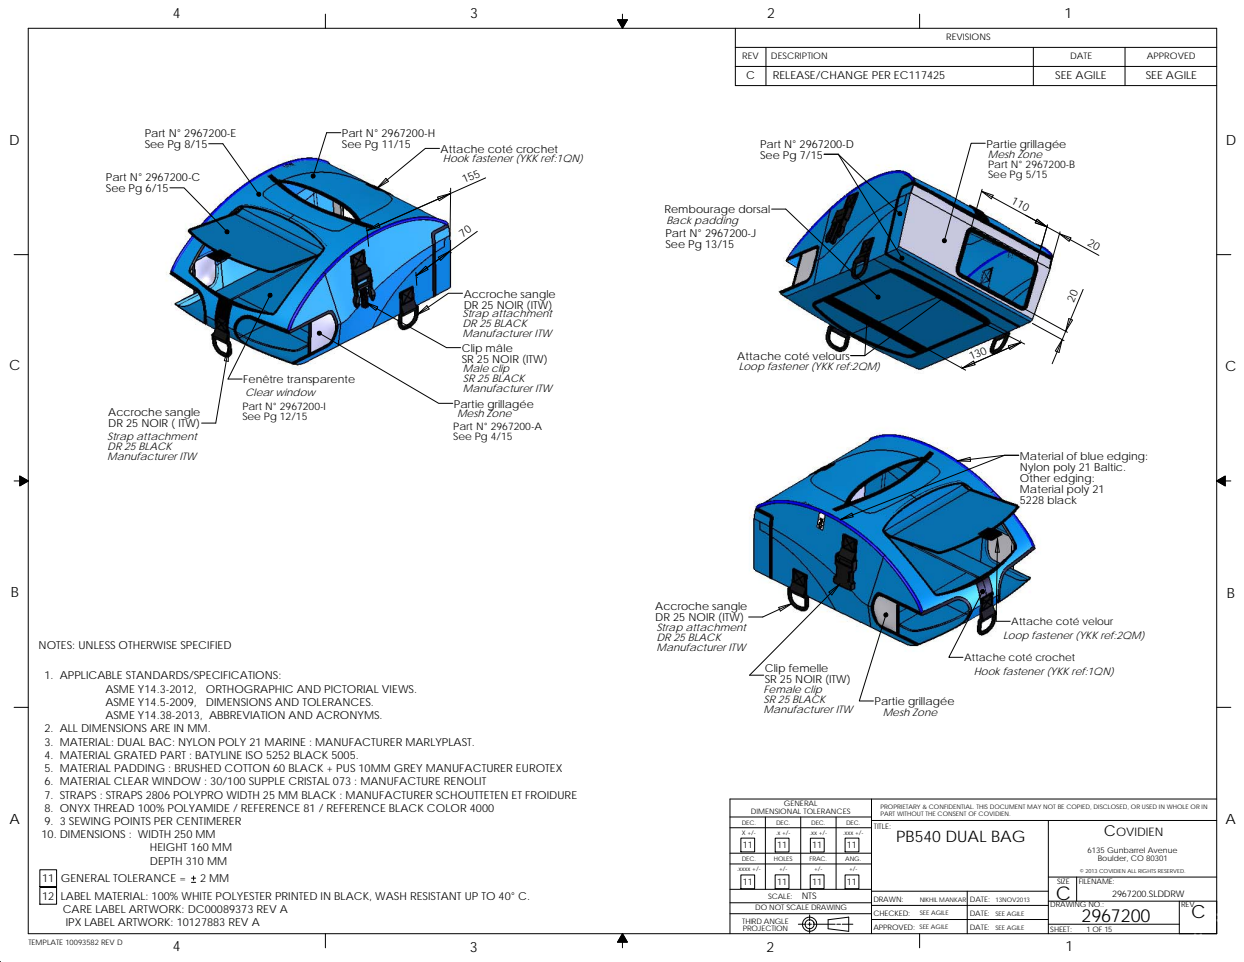
[picture p142: page 1]
HEIGHT 160 MM DEPTH 310 MM; 11 GENERAL TOLERANCE =; TEMPLATE 10093582 REV D; PROJECTION; SHEET:; DATE:; DRAWING NO.:; THIRD ANGLE; See Pg 5/15; Back padding Part N° 2967200-J; Partie grillagée; See Pg 13/15; Rembourage dorsal; See Pg 7/15; Part N° 2967200-D; Part N° 2967200-B; Mesh Zone; Fenêtre transparente; See Pg 8/15; Part N° 2967200-E; See Pg 12/15; Part N° 2967200-I; Clear window; Part N° 2967200-C See Pg 6/15; Part N° 2967200-H See Pg 11/15; Manufacturer ITW

REVISIONS

REV | DESCRIPTION | DATE | APPROVED
RELEASE/CHANGE PER EC117425 | SEE AGILE | SEE AGILE

Attache coté crochet
Hook fastener (YKK ref:1QN)

Accroche sangle
DR 25 NOIR (ITW)
Strap attachment
DR 25 BLACK
Manufacturer ITW
Clip mâle
SR 25 NOIR (ITW)
Male clip
SR 25 BLACK
Partie grillagée
Mesh Zone
Part N° 2967200-A
See Pg 4/15

Attache coté velours
Loop fastener (YKK ref:2QM)

DR 25 NOIR ( ITW)

Material of blue edging:
Nylon poly 21 Baltic.
Other edging:
Material poly 21
5228 black

Attache coté velour

NOTES: UNLESS OTHERWISE SPECIFIED

Clip femelle
Female clip

1. APPLICABLE STANDARDS/SPECIFICATIONS:

ASME Y14.3-2012, ORTHOGRAPHIC AND PICTORIAL VIEWS.
ASME Y14.5-2009, DIMENSIONS AND TOLERANCES.
ASME Y14.38-2013, ABBREVIATION AND ACRONYMS.

2. ALL DIMENSIONS ARE IN MM.
3. MATERIAL: DUAL BAC: NYLON POLY 21 MARINE : MANUFACTURER MARLYPLAST.
4. MATERIAL GRATED PART : BATYLINE ISO 5252 BLACK 5005.
5. MATERIAL PADDING : BRUSHED COTTON 60 BLACK + PUS 10MM GREY MANUFACTURER EUROTEX
6. MATERIAL CLEAR WINDOW : 30/100 SUPPLE CRISTAL 073 : MANUFACTURE RENOLIT
7. STRAPS : STRAPS 2806 POLYPRO WIDTH 25 MM BLACK : MANUFACTURER SCHOUTTETEN ET FROIDURE
8. ONYX THREAD 100% POLYAMIDE / REFERENCE 81 / REFERENCE BLACK COLOR 4000
9. 3 SEWING POINTS PER CENTIMERER
10. DIMENSIONS : WIDTH 250 MM

GENERAL DIMENSIONAL TOLERANCES | PROPRIETARY & CONFIDENTIAL. THIS DOCUMENT MAY NOT BE COPIED, DISCLOSED, OR USED IN WHOLE OR IN PART WITHOUT THE CONSENT OF COVIDIEN.

DEC. | DEC. | DEC. | DEC.
X +/-11 | .x +/-11 | .xx +/-11 | .xxx +/-11

TITLE: PB540 DUAL BAG | COVIDIEN 6135 Gunbarrel Avenue Boulder, CO 80301 © 2013 COVIDIEN ALL RIGHTS RESERVED.

DEC. | HOLES | FRAC. | ANG.
.xxxx +/- | +/-11 | +/- | +/-
DO NOT SCALE DRAWING | | | | REV C

12 LABEL MATERIAL: 100% WHITE POLYESTER PRINTED IN BLACK, WASH RESISTANT UP TO 40° C.
CARE LABEL ARTWORK: DC00089373 REV A
IPX LABEL ARTWORK: 10127883 REV A

SIZE | FILENAME: 2967200.SLDDRW
SCALE: NTS | DRAWN: NIKHIL MANKAR | 13NOV2013

CHECKED: SEE AGILE | DATE: SEE AGILE
APPROVED: SEE AGILE | DATE: SEE AGILE

D

D

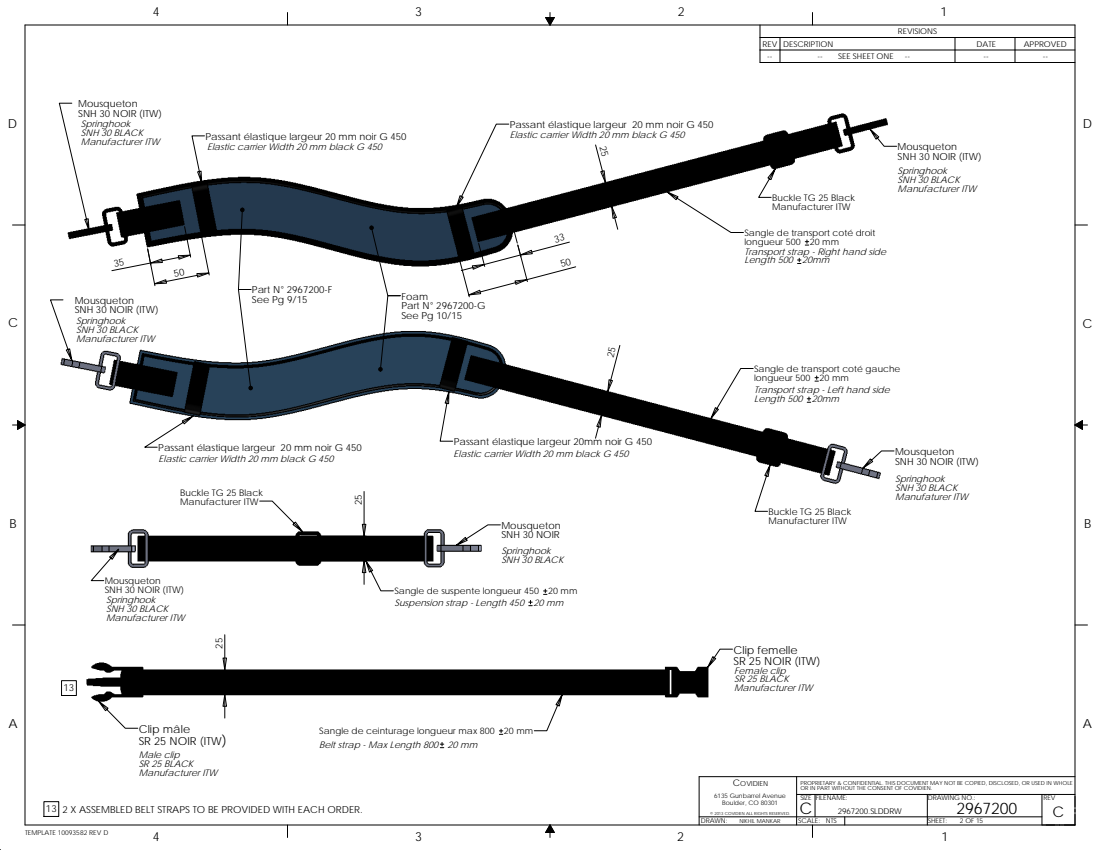
[picture p143: page 2]
Sangle de suspente longueur 450; Mousqueton SNH 30 NOIR; Suspension strap - Length 450; Springhook SNH 30 BLACK; longueur 500; Passant élastique largeur 20 mm noir G 450; Passant élastique largeur 20mm noir G 450; Length 500; Part N° 2967200-F; See Pg 9/15; Foam Part N° 2967200-G; See Pg 10/15; 13 2 X ASSEMBLED BELT STRAPS TO BE PROVIDED WITH EACH ORDER.; 2967200.SLDDRW; 2 TEMPLATE 10093582 REV D; Sangle de ceinturage longueur max 800; Belt strap - Max Length 800; Springhook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

REV | DESCRIPTION | DATE | APPROVED
-- | --SEE SHEET ONE -- | -- | --

Mousqueton
SNH 30 NOIR (ITW)

Passant élastique largeur 20 mm noir G 450

Elastic carrier Width 20 mm black G 450

Springhook
SNH 30 BLACK
Manufacturer ITW

Buckle TG 25 Black

Sangle de transport coté droit
Transport strap - Right hand side

Sangle de transport coté gauche
Transport strap - Left hand side

Manufaturer ITW

Mousqueton SNH 30 NOIR (ITW)

Clip femelle
SR 25 NOIR (ITW)
Female clip
SR 25 BLACK

Clip mâle
Male clip

COVIDIEN 6135 Gunbarrel Avenue Boulder, CO 80301 © 2013 COVIDIEN ALL RIGHTS RESERVED. | PROPRIETARY & CONFIDENTIAL. THIS DOCUMENT MAY NOT BE COPIED, DISCLOSED, OR USED IN WHOLE OR IN PART WITHOUT THE CONSENT OF COVIDIEN.

SIZE | FILENAME: | DRAWING NO.: | REV

DRAWN: | SCALE: NTS | | SHEET: 2 OF 15

D

D

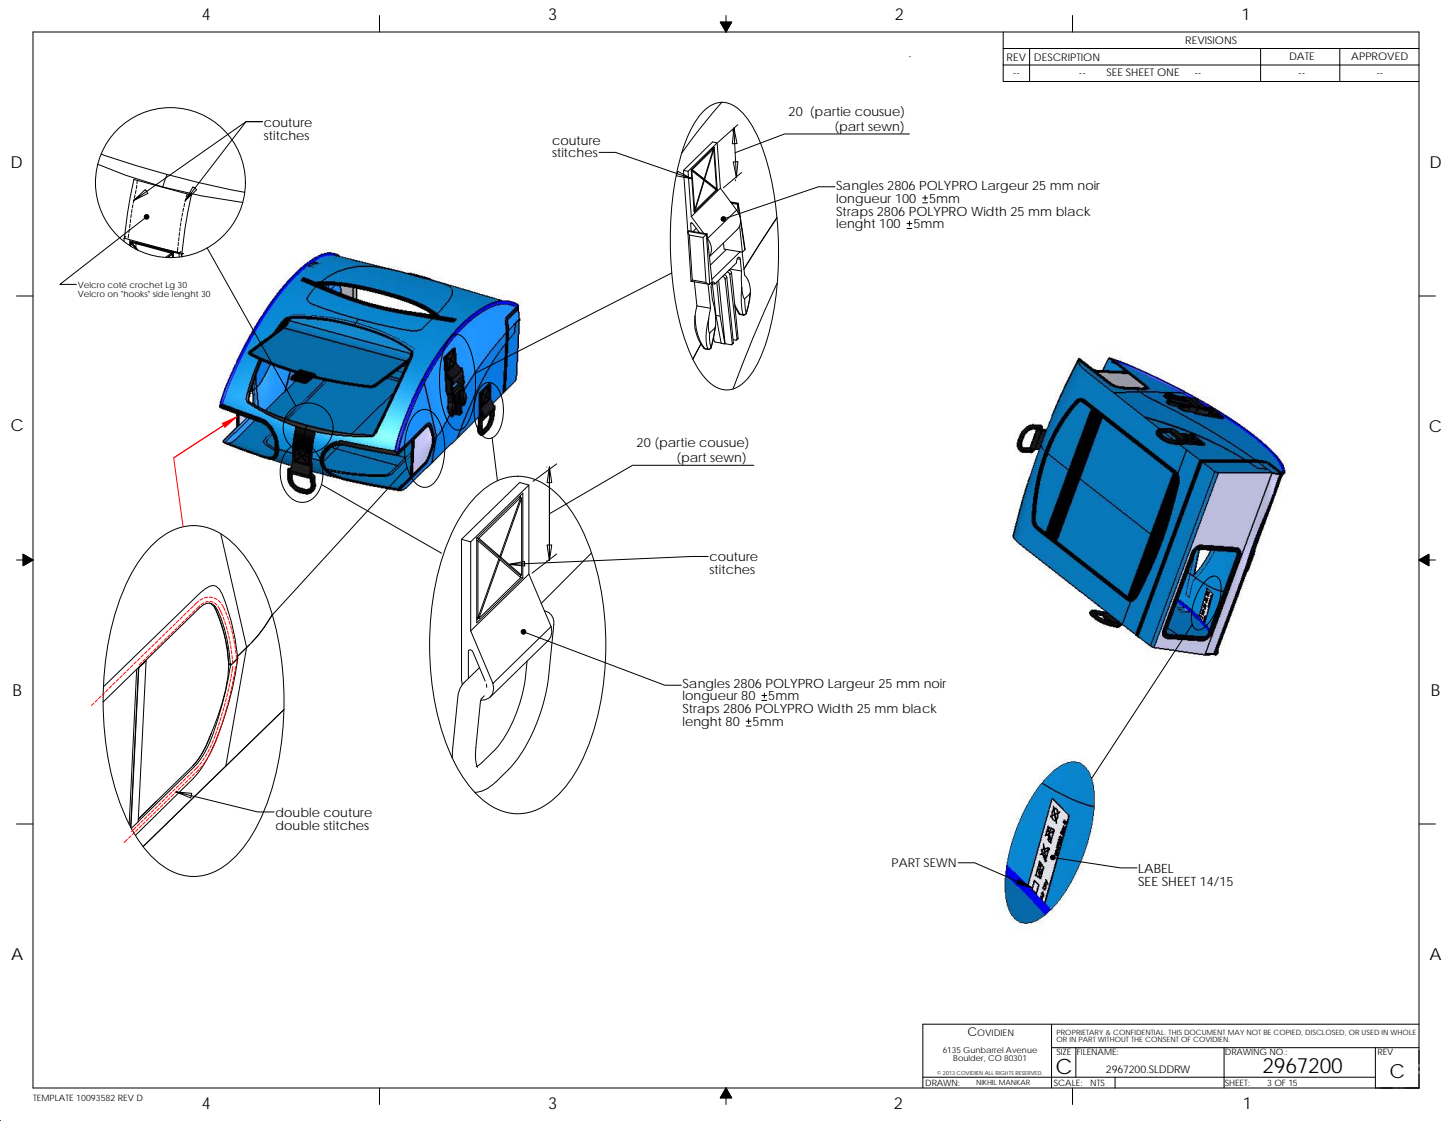
[picture p144: page 3]
20 (partie cousue) (part sewn); longueur 100; lenght 100; couture stitches; double couture double stitches; 2967200.SLDDRW; LABEL SEE SHEET 14/15; PART SEWN; longueur 80; lenght 80

Sangles 2806 POLYPRO Largeur 25 mm noir
Straps 2806 POLYPRO Width 25 mm black

Velcro coté crochet Lg 30
Velcro on "hooks" side lenght 30

D

D

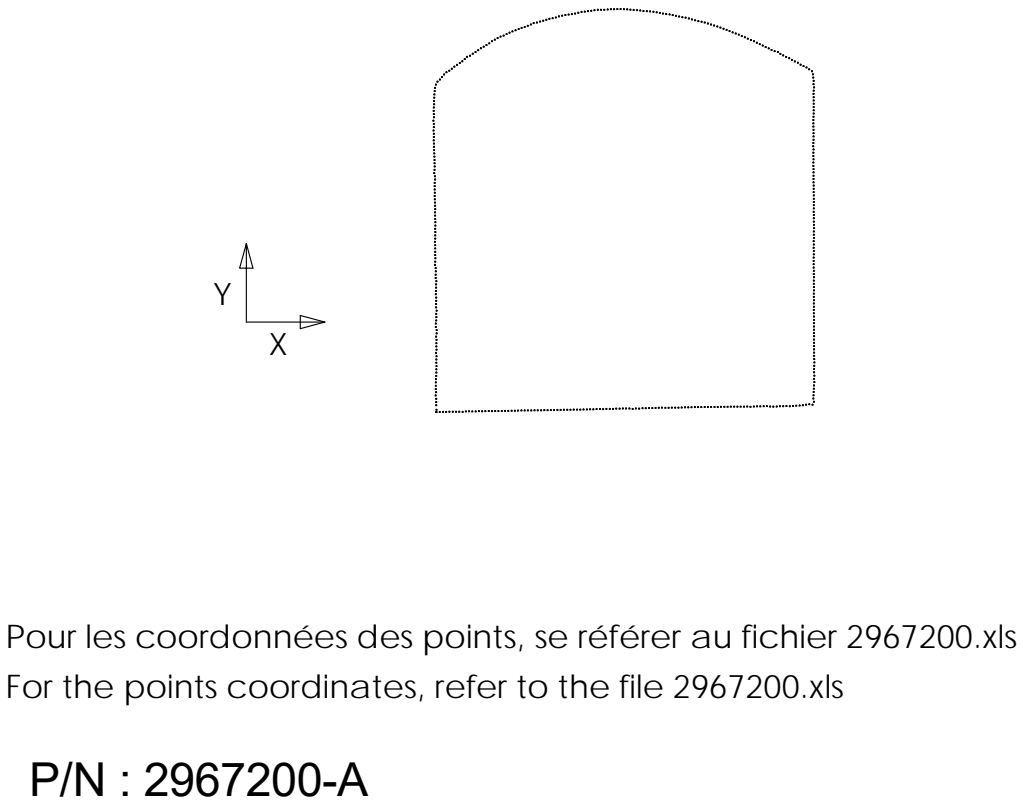
[picture p145: page 4]

Pour les coordonnées des points, se référer au fichier 2967200.xls
For the points coordinates, refer to the file 2967200.xls

D

D

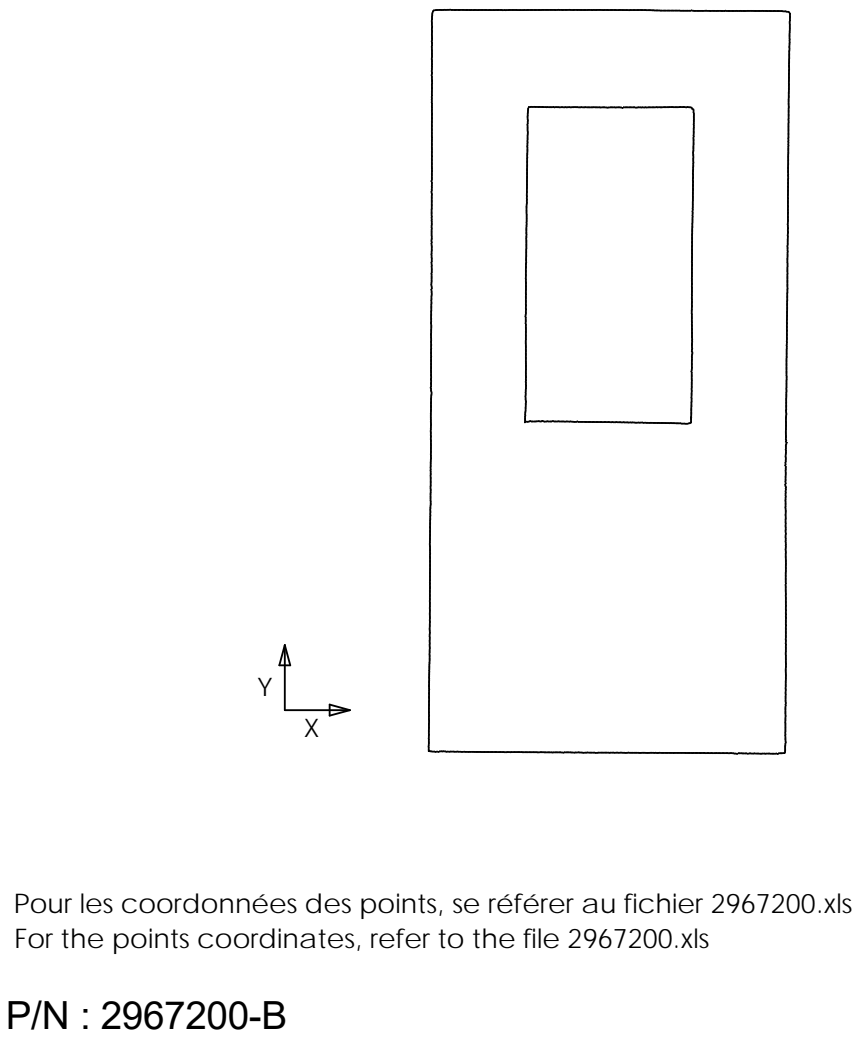
[picture p146: page 5]
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

D

D

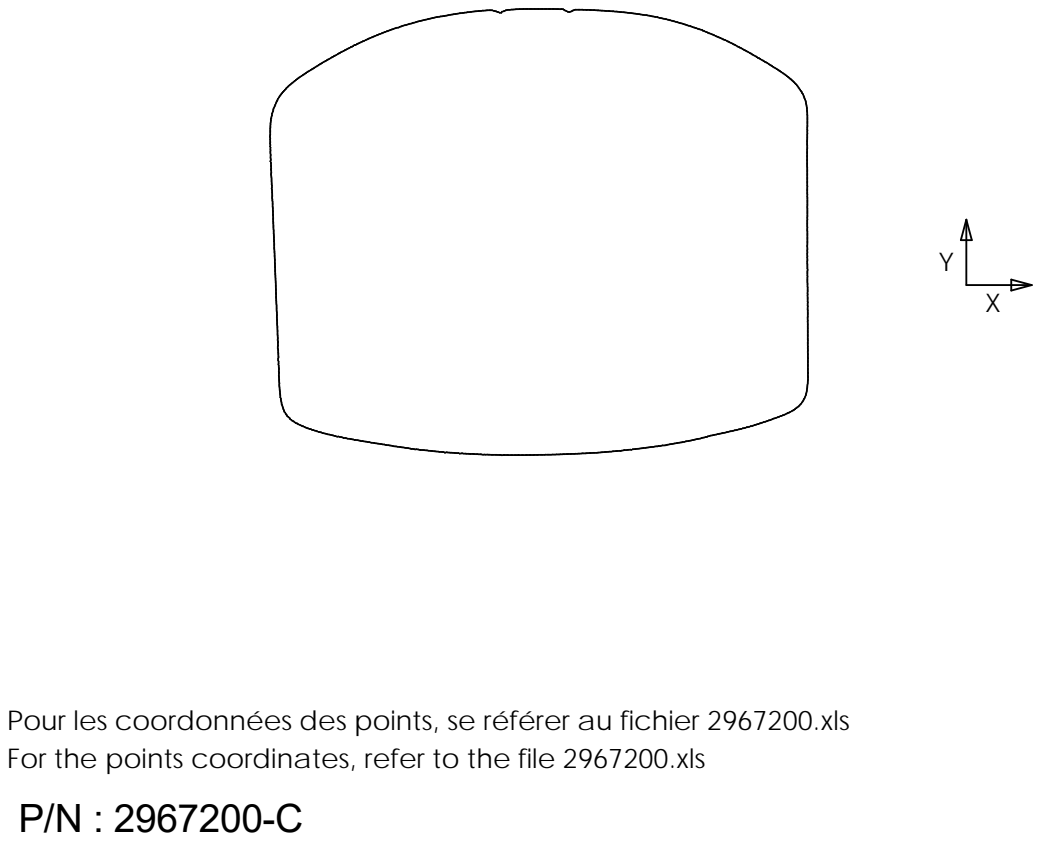
[picture p147: page 6]
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

D

D

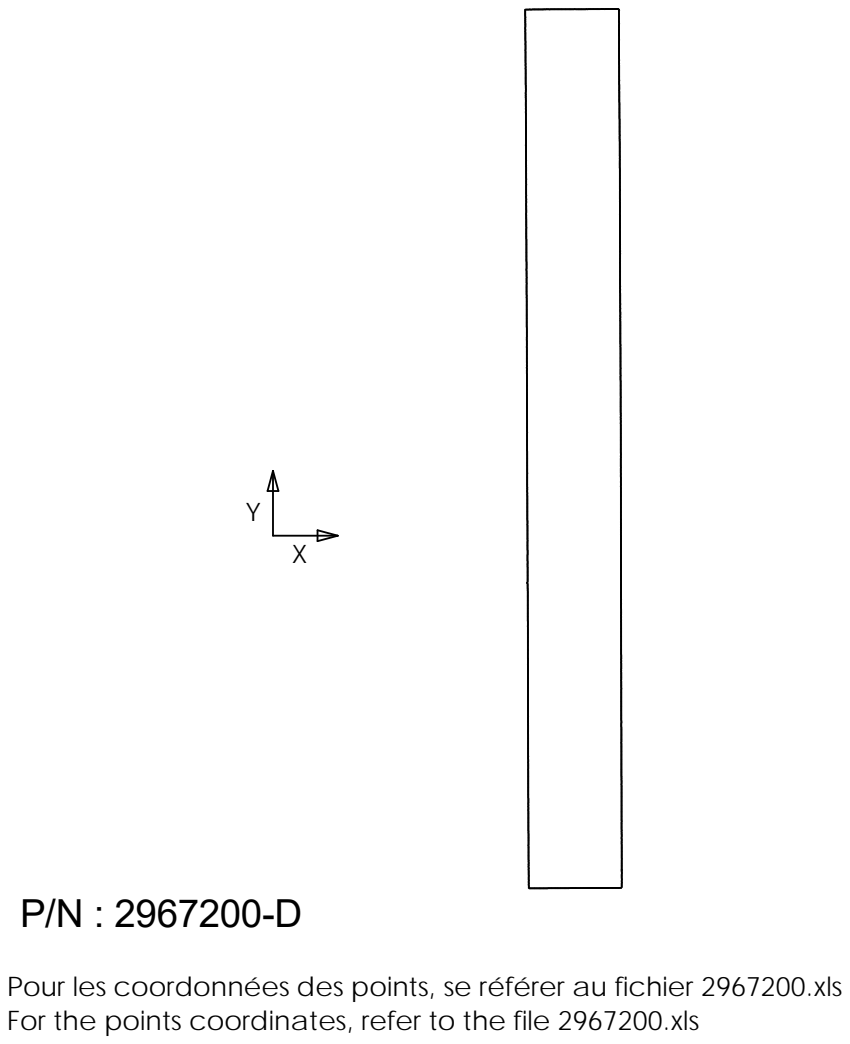
[picture p148: page 7]
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

D

D

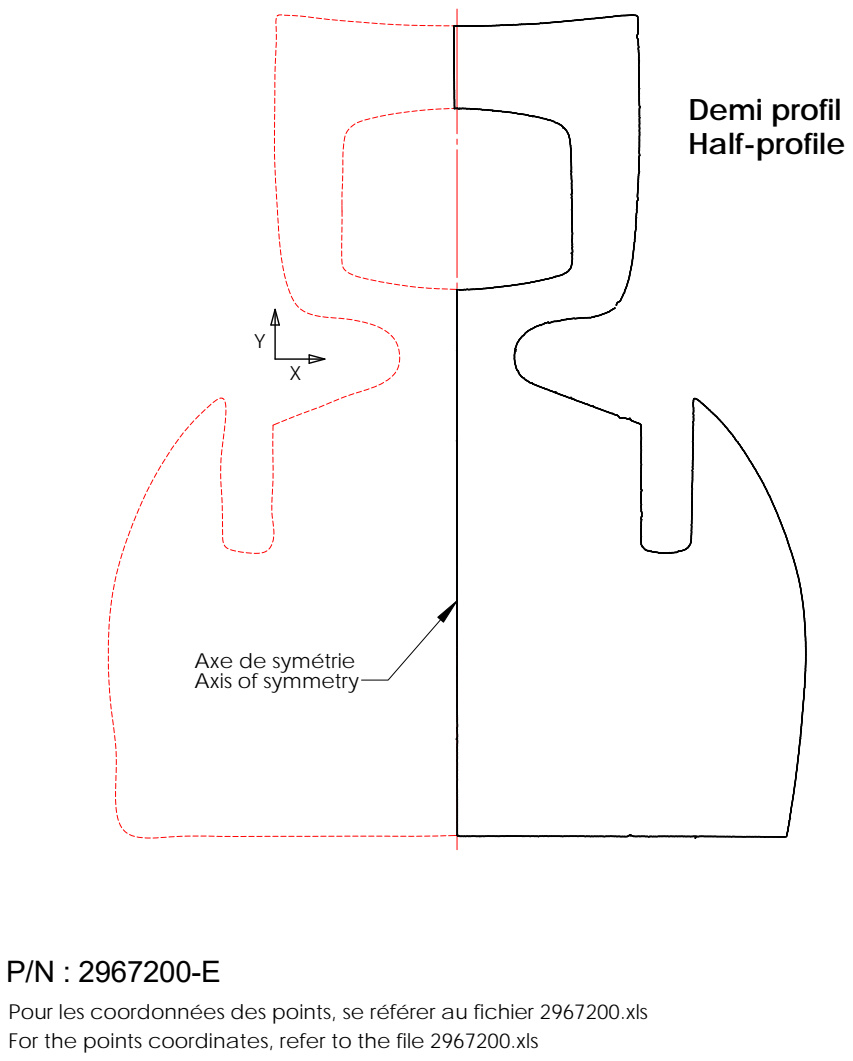
[picture p149: page 8]
Demi profil Half-profile

Axe de symétrie
Axis of symmetry

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

D

D

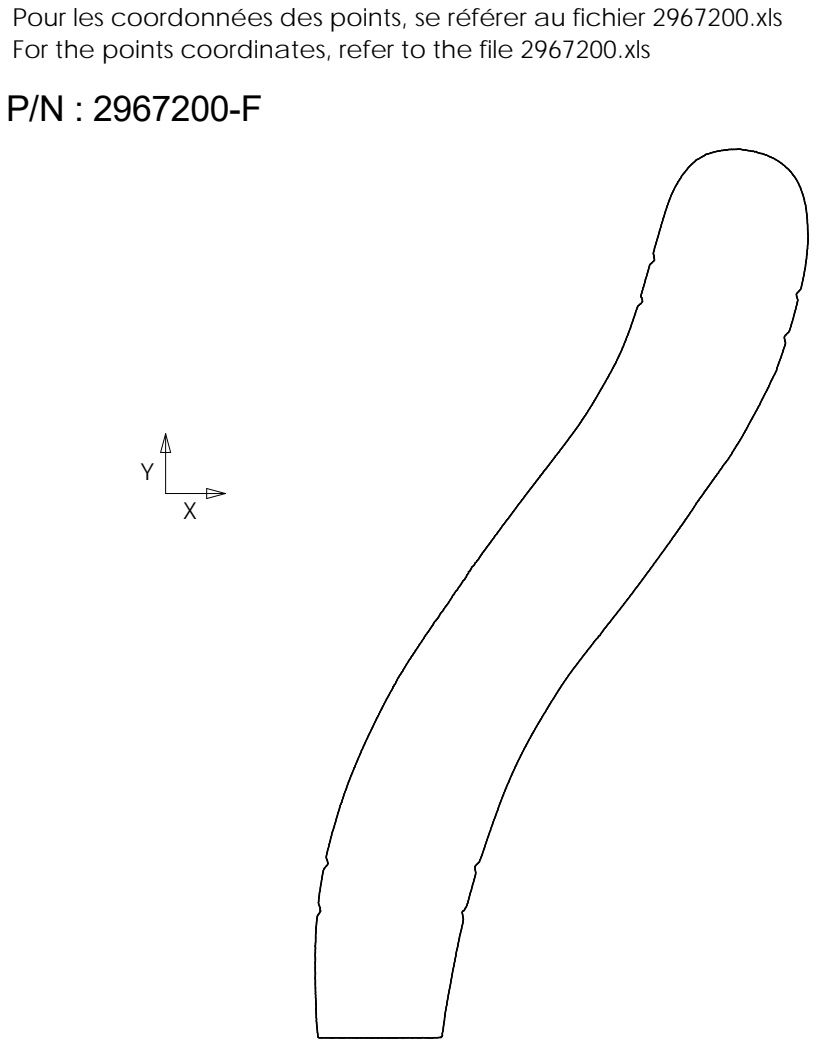
[picture p150: page 9]
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

D

D

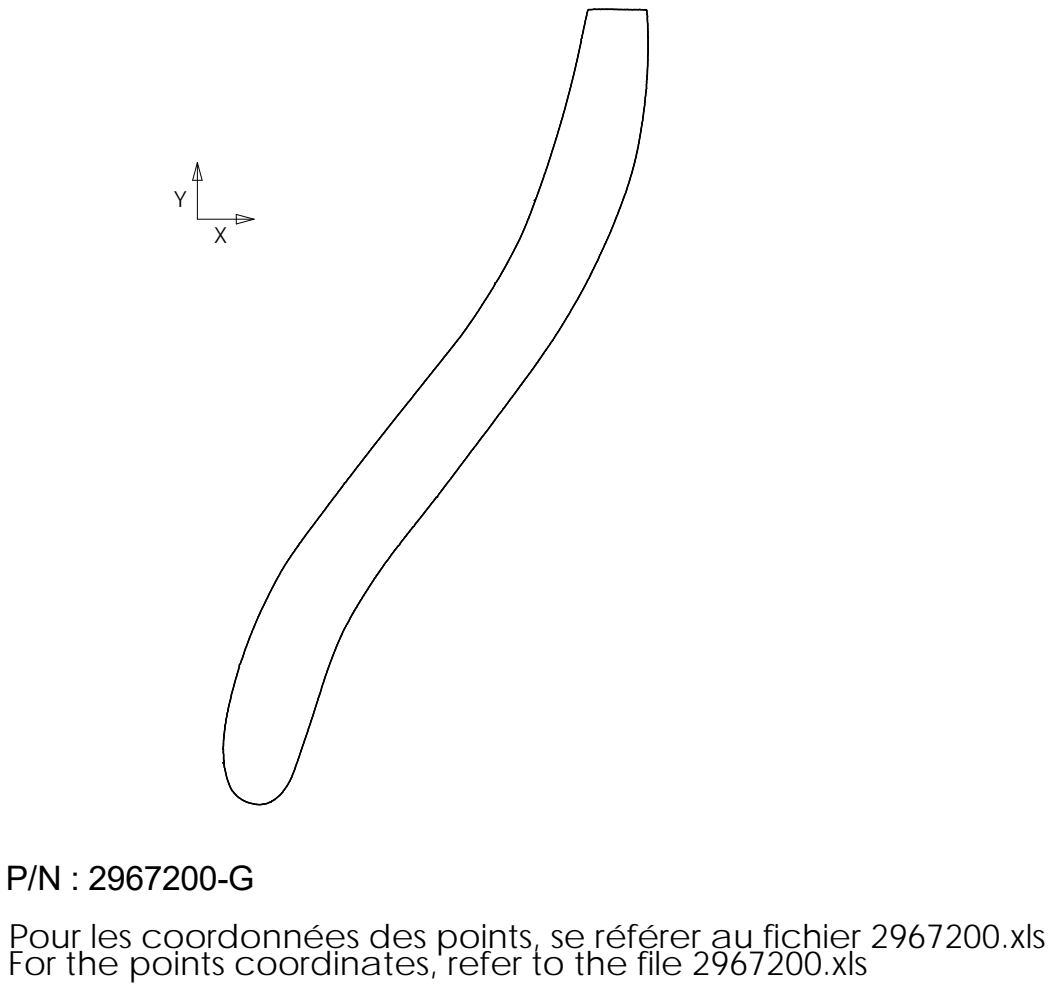
[picture p151: page 10]
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

D

D

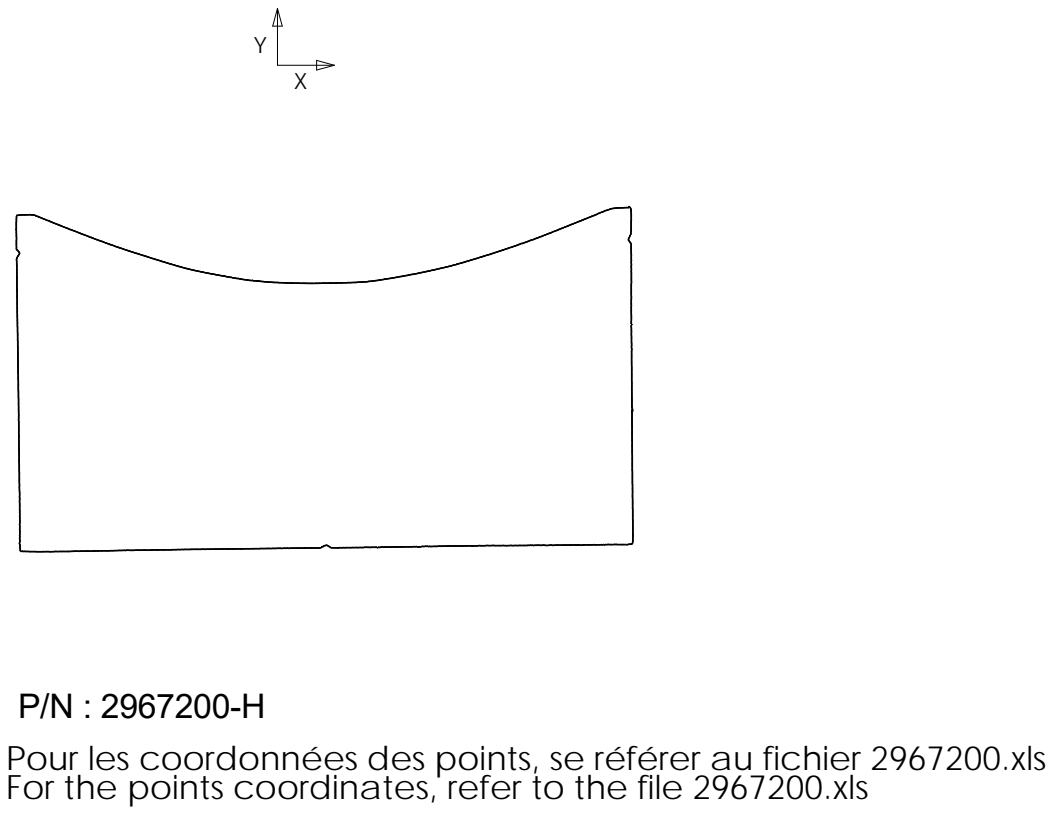
[picture p152: page 11]
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

D

D

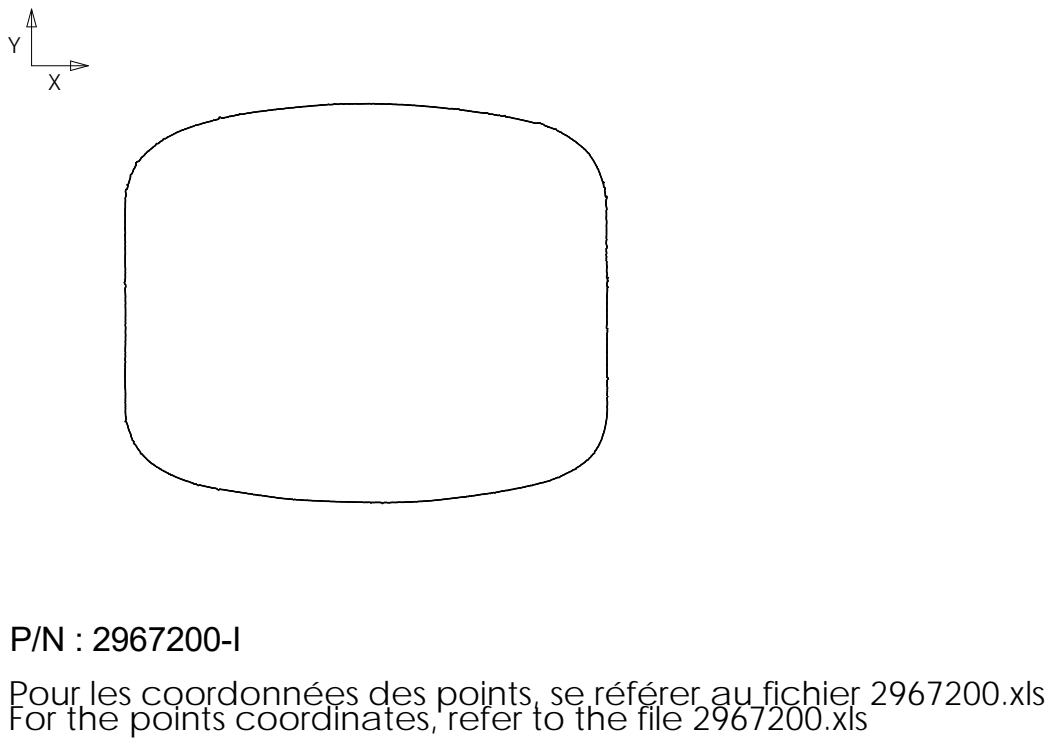
[picture p153: page 12]
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

D

D

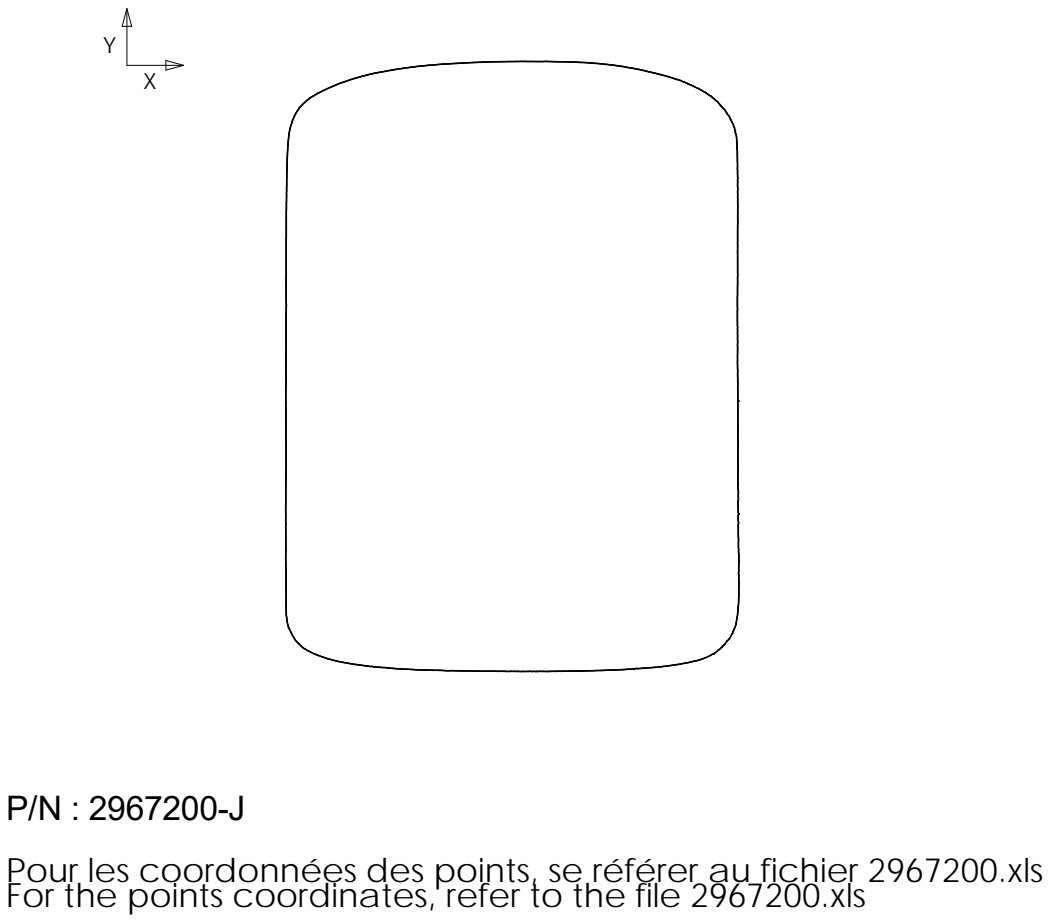
[picture p154: page 13]
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

D

D

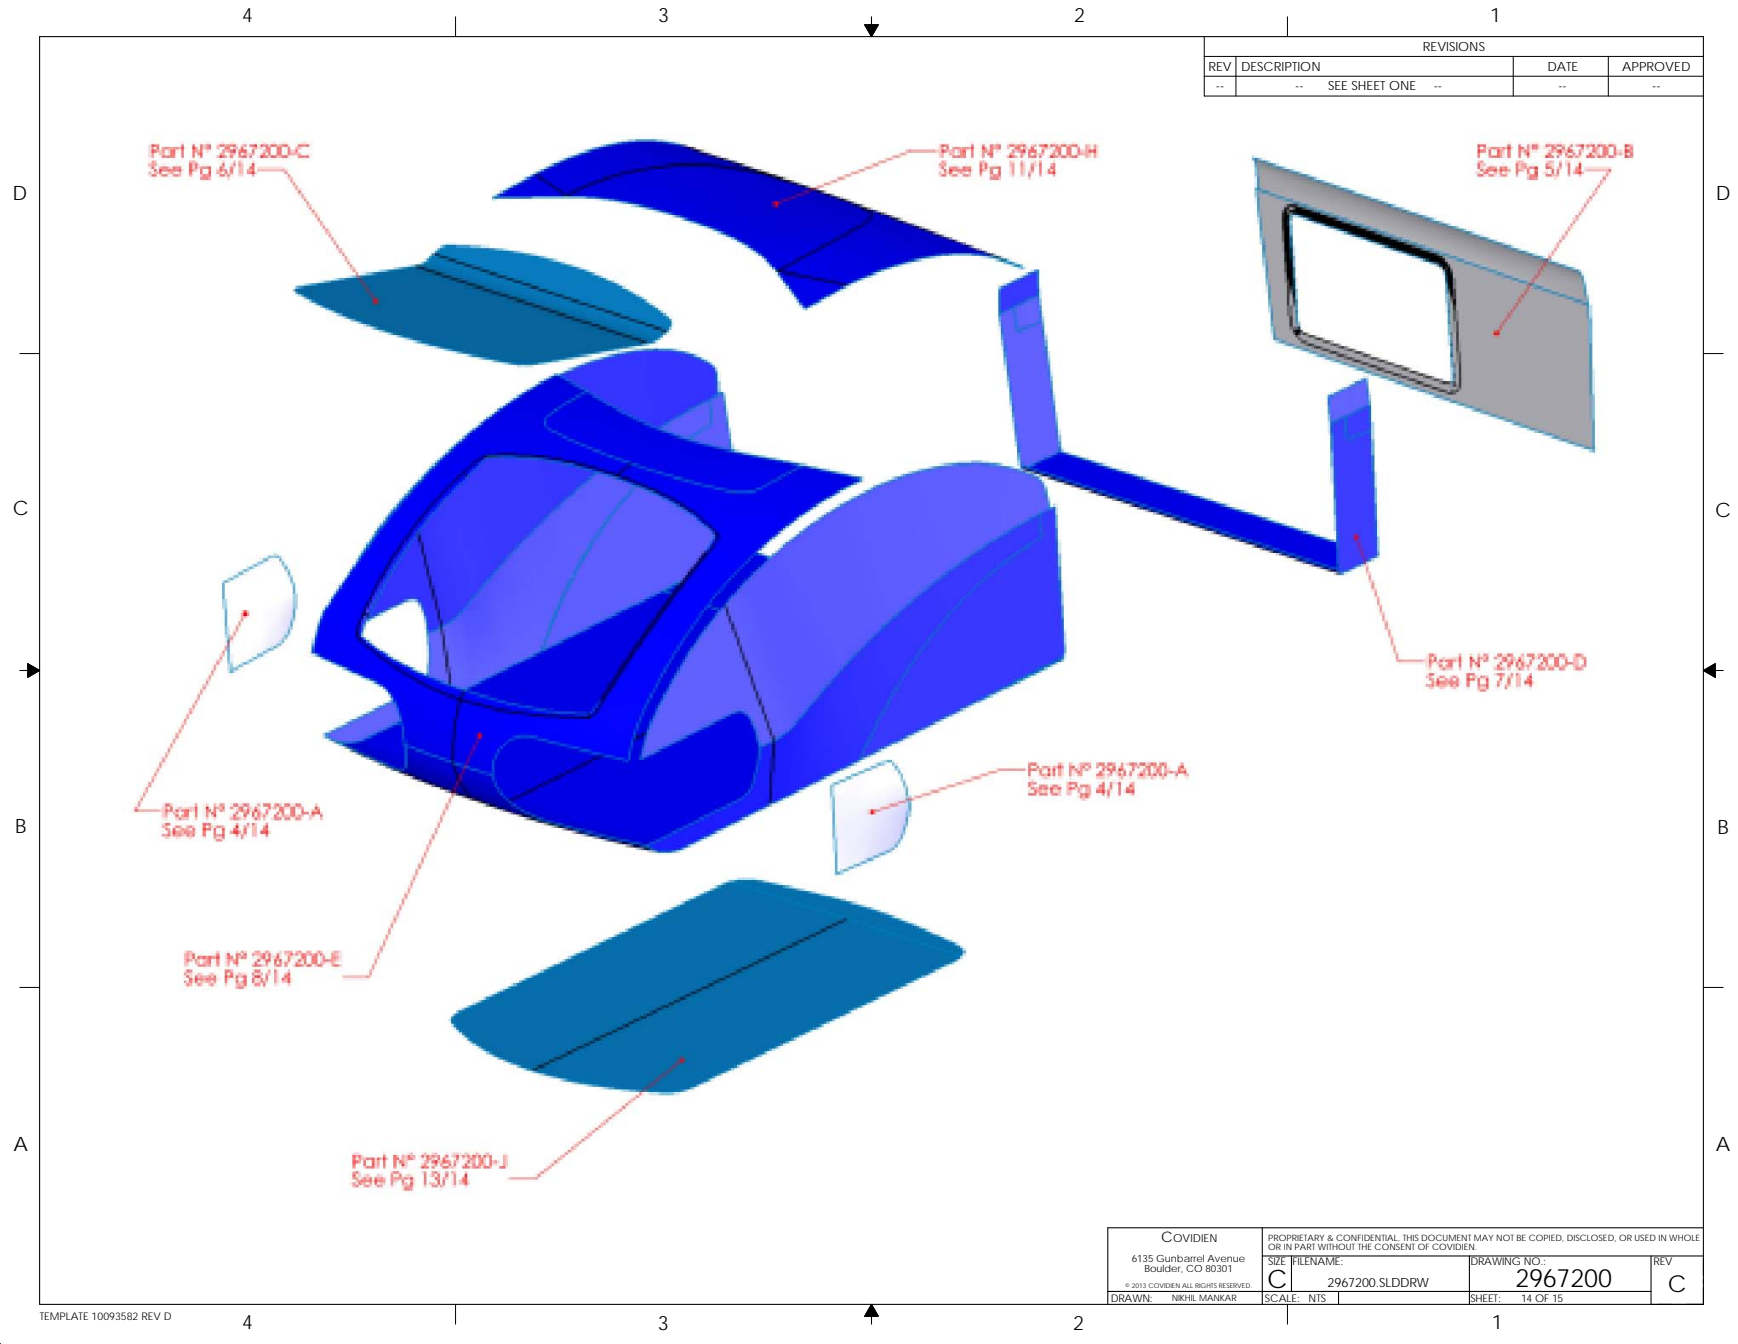
[picture p155: page 14]

D

D

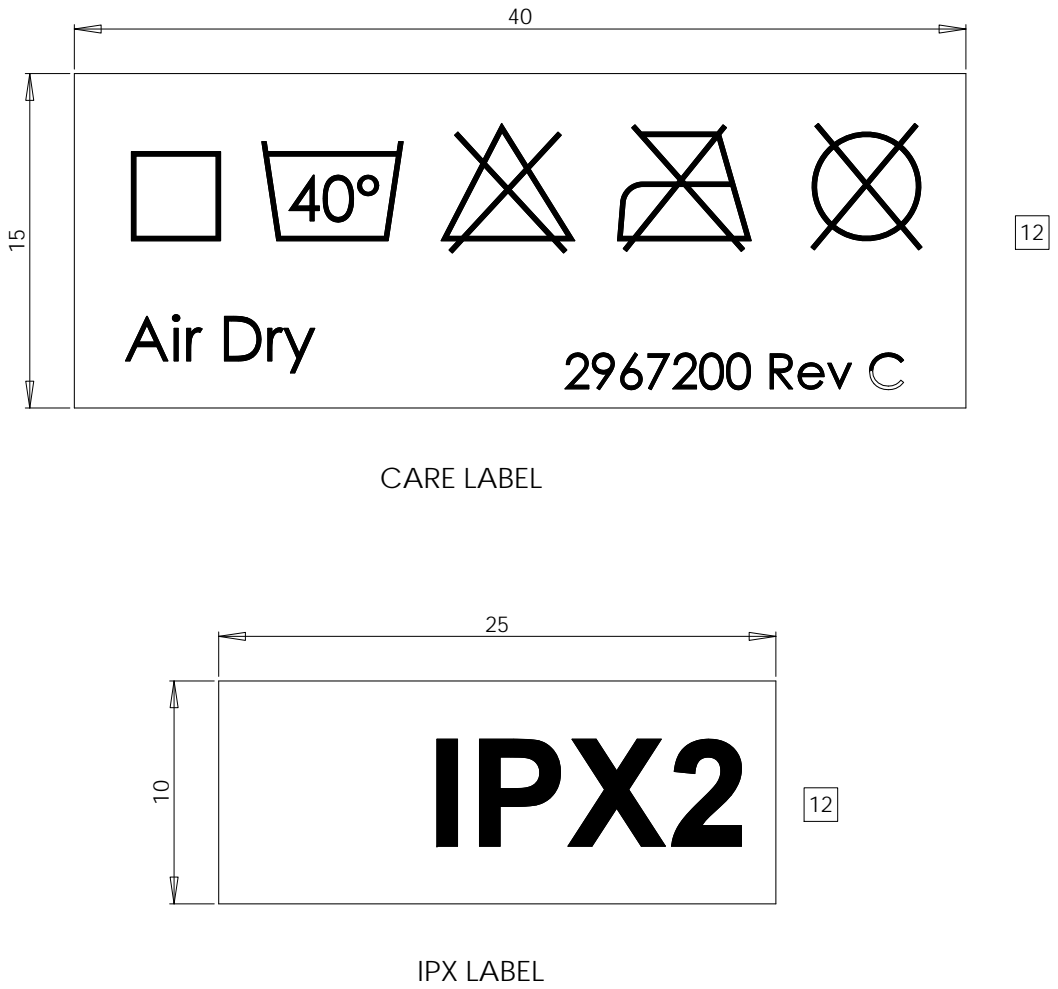
[picture p156: page 15]
CARE LABEL; IPX LABEL
