hesingh/ventilator/Medtronic/medtronic-pb560-ventilator-system-file-set-2/Mechanical Part Drawings/2982400/2982400F00.pdf

8 | 7 | 6 | 5 | 4 | 3 | 2 | 1

E

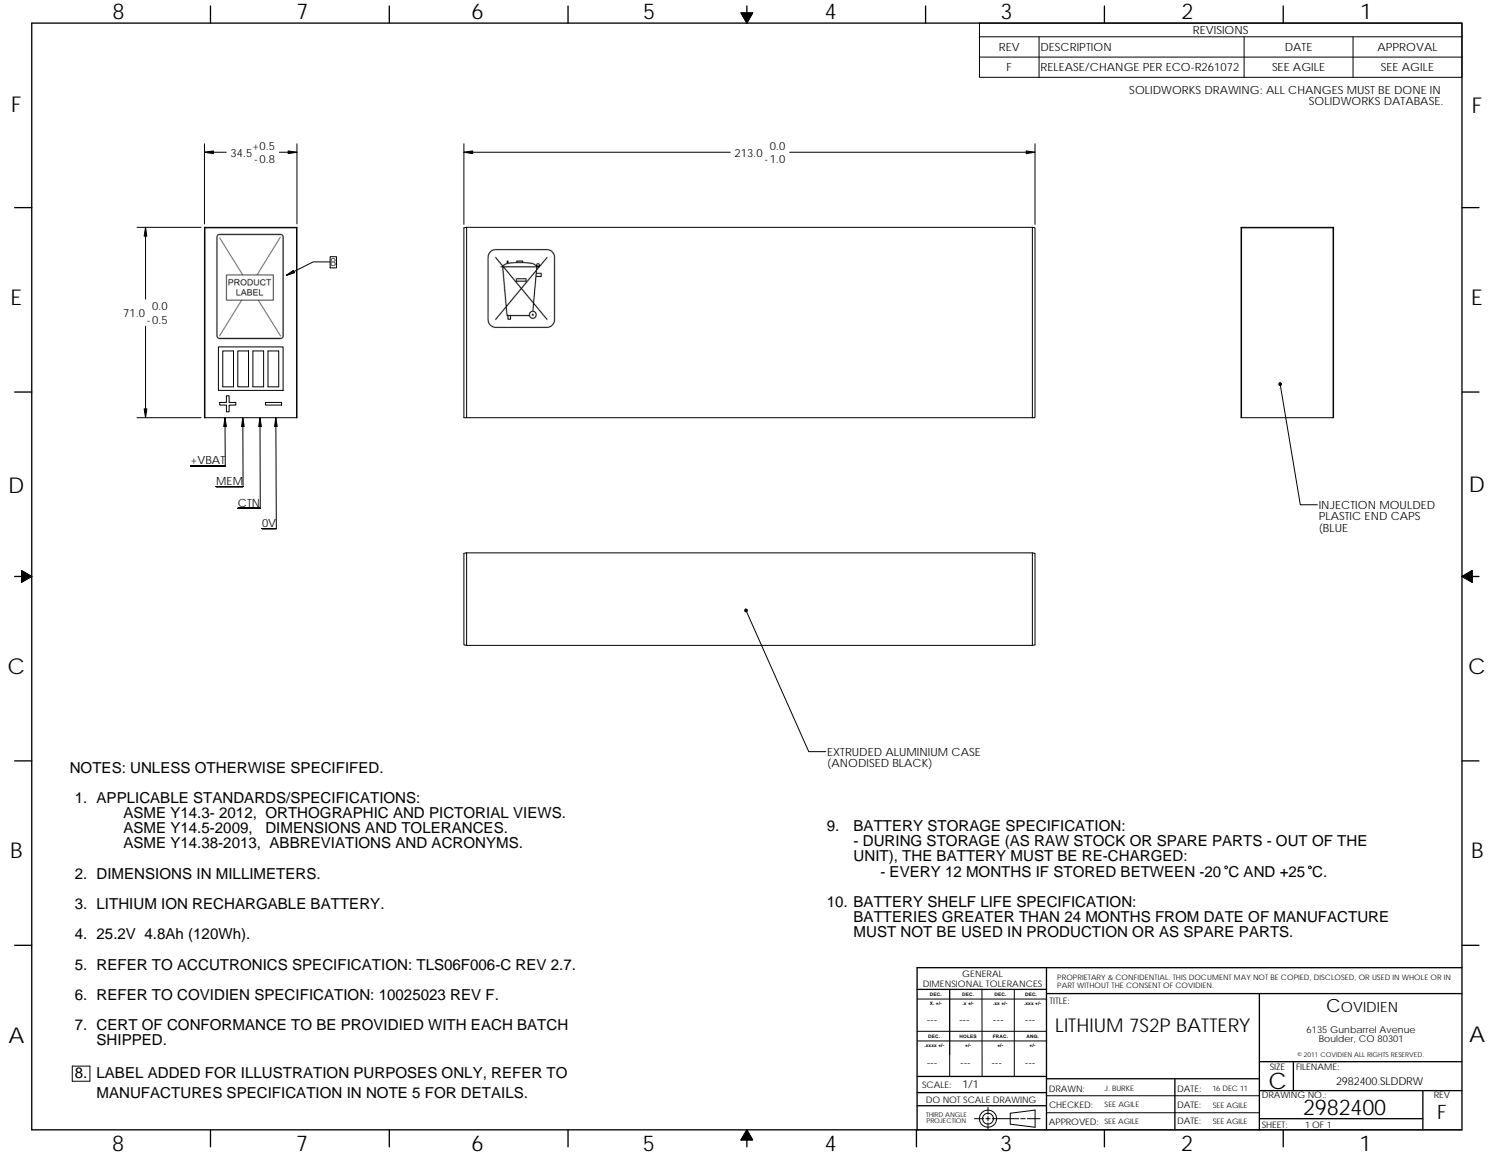
[picture p157: page 1]
2982400.SLDDRW 1/1; 16 DEC 11; PROJECTION; SHEET:; THIRD ANGLE; CTN; MEM; +VBAT; C AND +25; SOLIDWORKS DATABASE.; SHIPPED.; REVISIONS; REV; DESCRIPTION; DATE; APPROVAL; RELEASE/CHANGE PER ECO-R261072; SEE AGILE

SOLIDWORKS DRAWING: ALL CHANGES MUST BE DONE IN

INJECTION MOULDED
PLASTIC END CAPS
(BLUE

EXTRUDED ALUMINIUM CASE
(ANODISED BLACK)

NOTES: UNLESS OTHERWISE SPECIFIFED.
1. APPLICABLE STANDARDS/SPECIFICATIONS:
ASME Y14.3- 2012, ORTHOGRAPHIC AND PICTORIAL VIEWS.
ASME Y14.5-2009, DIMENSIONS AND TOLERANCES.
ASME Y14.38-2013, ABBREVIATIONS AND ACRONYMS.
2. DIMENSIONS IN MILLIMETERS.
3. LITHIUM ION RECHARGABLE BATTERY.
REFER TO ACCUTRONICS SPECIFICATION: TLS06F006-C REV 2.7.
REFER TO COVIDIEN SPECIFICATION: 10025023 REV F.
7. CERT OF CONFORMANCE TO BE PROVIDIED WITH EACH BATCH

9. BATTERY STORAGE SPECIFICATION:
- DURING STORAGE (AS RAW STOCK OR SPARE PARTS - OUT OF THE
UNIT), THE BATTERY MUST BE RE-CHARGED:
- EVERY 12 MONTHS IF STORED BETWEEN -20
BATTERY SHELF LIFE SPECIFICATION:
BATTERIES GREATER THAN 24 MONTHS FROM DATE OF MANUFACTURE
MUST NOT BE USED IN PRODUCTION OR AS SPARE PARTS.

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

DEC. | DEC. | DEC. | DEC.
TITLE: LITHIUM 7S2P BATTERY | COVIDIEN 6135 Gunbarrel Avenue Boulder, CO 80301 © 2011 COVIDIEN ALL RIGHTS RESERVED. SIZE ---

X. +/---- | .x +/---- | .xx +/---- | .xxx +/----

DEC. | HOLES | FRAC. | ANG.
.xxxx +/---- | +/- | +/---- | +/----

C | FILENAME:

8. LABEL ADDED FOR ILLUSTRATION PURPOSES ONLY, REFER TO
MANUFACTURES SPECIFICATION IN NOTE 5 FOR DETAILS.

SCALE: | DRAWN: J. BURKE | DATE:
DO NOT SCALE DRAWING | | | DRAWING NO.: 2982400 | REV F

CHECKED: SEE AGILE | DATE: SEE AGILE
SEE AGILE APPROVED: | DATE: SEE AGILE
