hesingh/ventilator/Medtronic/medtronic-pb560-ventilator-system-file-set-2/Mechanical Part Drawings/3822900/3822900A00.PDF

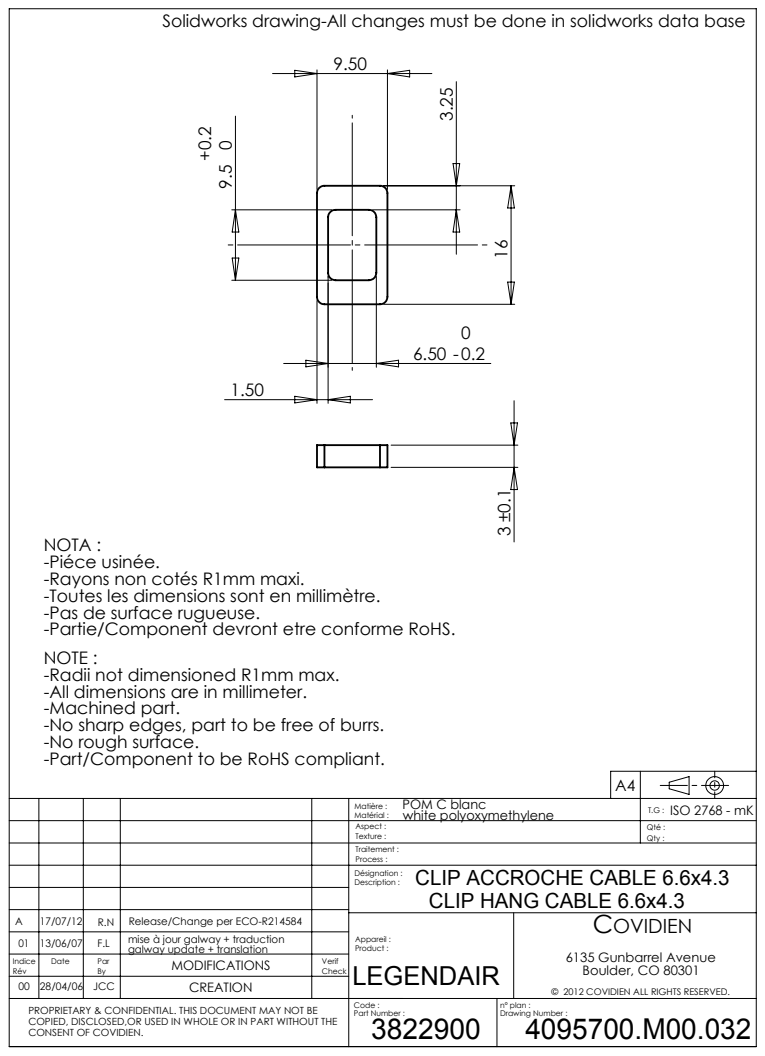
[picture p163: page 1]
6135 Gunbarrel Avenue Boulder, CO 80301; ISO 2768 - mK; Qty :; Qté :; Drawing Number :; n° plan :; Part Number :; Product :; Description :; POM C blanc; Code :; Appareil :; Désignation :; white polyoxymethylene

Solidworks drawing-All changes must be done in solidworks data base 16 9.5

NOTA :
-Piéce usinée.
-Rayons non cotés R1mm maxi.
-Toutes les dimensions sont en millimètre.
-Pas de surface rugueuse.
-Partie/Component devront etre conforme RoHS.
NOTE :
-Radii not dimensioned R1mm max.
-All dimensions are in millimeter.
-Machined part.
-No sharp edges, part to be free of burrs.
-No rough surface.
-Part/Component to be RoHS compliant.

Matière :
Matérial :
Aspect :
Texture :
Traitement :
Process :
CLIP ACCROCHE CABLE 6.6x4.3
CLIP HANG CABLE 6.6x4.3

A 17/07/12 R.N Release/Change per ECO-R214584
mise à jour galway + traduction 01 13/06/07 F.L
00 28/04/06 JCC
PROPRIETARY & CONFIDENTIAL. THIS DOCUMENT MAY NOT BE
COPIED, DISCLOSED,OR USED IN WHOLE OR IN PART WITHOUT THE
CONSENT OF COVIDIEN.

galway update + translation
Par

© 2012 COVIDIEN ALL RIGHTS RESERVED.
