hesingh/ventilator/Medtronic/medtronic-pb560-ventilator-system-file-set-2/Mechanical Part Drawings/3825500/3825500E00.PDF

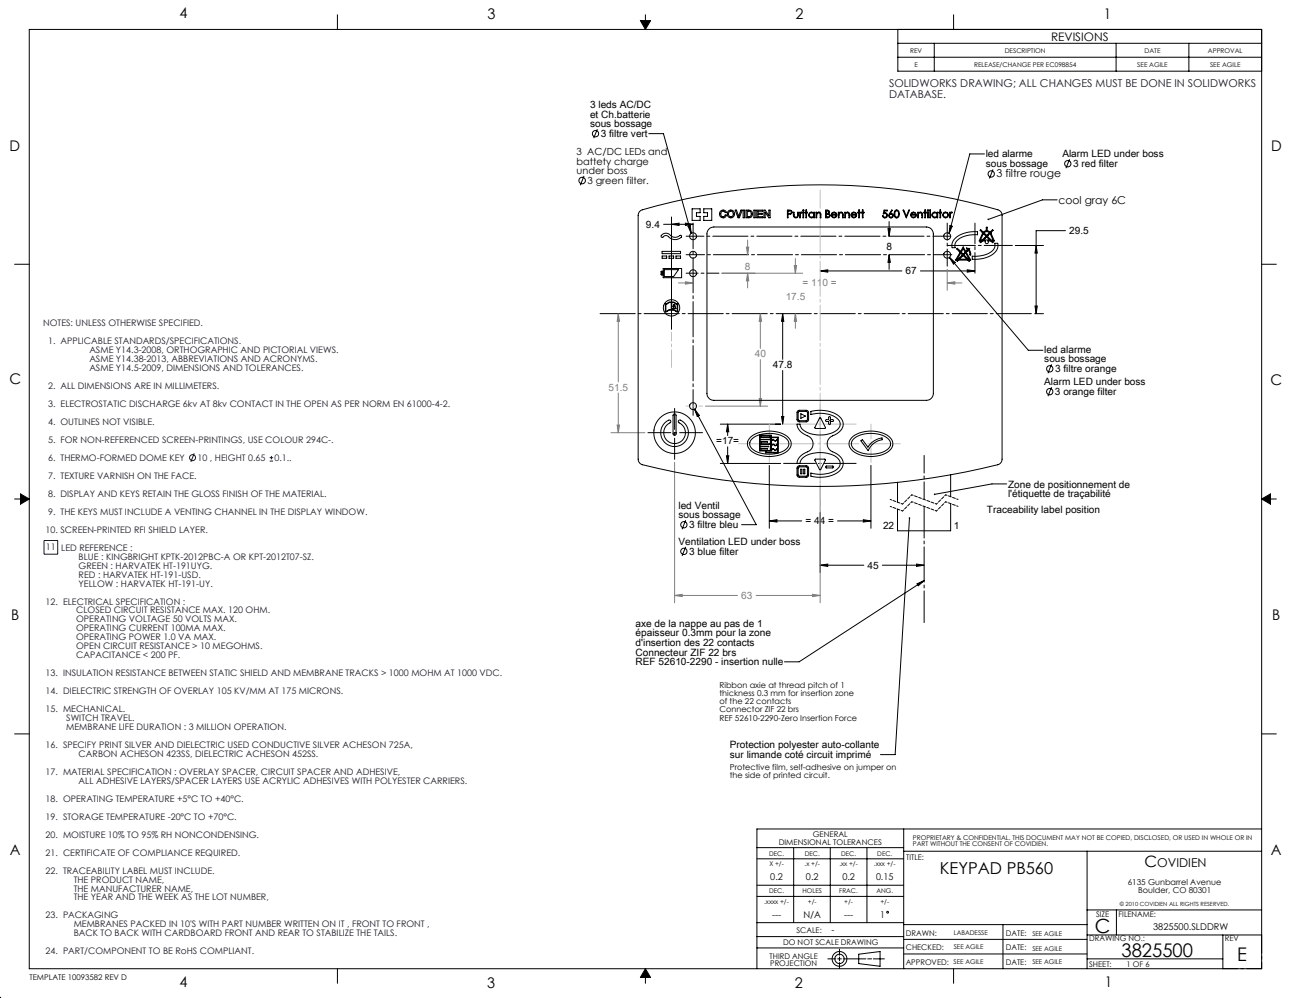
[picture p173: page 1]
led alarme sous bossage 3 filtre rouge; 3 filtre bleu; cool gray 6C; 6. THERMO-FORMED DOME KEY 10 , HEIGHT 0.65; LED REFERENCE :; 2 TEMPLATE 10093582 REV D; .xxxx +/-; THIRD ANGLE; .xxx +/-; SHEET:; DATE:; DRAWING NO.:; DIMENSIONAL TOLERANCES

REVISIONS

REV | DESCRIPTION | DATE | APPROVAL
E | RELEASE/CHANGE PER EC098854 | SEE AGILE | SEE AGILE

SOLIDWORKS DRAWING; ALL CHANGES MUST BE DONE IN SOLIDWORKS
DATABASE.

3 leds AC/DC
et Ch.batterie
sous bossage
3 filtre vert
3 AC/DC LEDs and
battety charge
under boss
3 green filter.

Alarm LED under boss
3 red filter

NOTES: UNLESS OTHERWISE SPECIFIED.
1. APPLICABLE STANDARDS/SPECIFICATIONS.

led alarme
3 filtre orange
3 orange filter

ASME Y14.3-2008, ORTHOGRAPHIC AND PICTORIAL VIEWS.
ASME Y14.38-2013, ABBREVIATIONS AND ACRONYMS.
ASME Y14.5-2009, DIMENSIONS AND TOLERANCES.

2. ALL DIMENSIONS ARE IN MILLIMETERS.
3. ELECTROSTATIC DISCHARGE 6kv AT 8kv CONTACT IN THE OPEN AS PER NORM EN 61000-4-2.
4. OUTLINES NOT VISIBLE.
5. FOR NON-REFERENCED SCREEN-PRINTINGS, USE COLOUR 294C-.
7. TEXTURE VARNISH ON THE FACE.
8. DISPLAY AND KEYS RETAIN THE GLOSS FINISH OF THE MATERIAL.
9. THE KEYS MUST INCLUDE A VENTING CHANNEL IN THE DISPLAY WINDOW.
10. SCREEN-PRINTED RFI SHIELD LAYER.
BLUE : KINGBRIGHT KPTK-2012PBC-A OR KPT-2012T07-SZ.
GREEN : HARVATEK HT-191UYG.
RED : HARVATEK HT-191-USD.
YELLOW : HARVATEK HT-191-UY.
12. ELECTRICAL SPECIFICATION :
CLOSED CIRCUIT RESISTANCE MAX. 120 OHM.
OPERATING VOLTAGE 50 VOLTS MAX.
OPERATING CURRENT 100MA MAX.
OPERATING POWER 1.0 VA MAX.
OPEN CIRCUIT RESISTANCE > 10 MEGOHMS.
CAPACITANCE < 200 PF.
13. INSULATION RESISTANCE BETWEEN STATIC SHIELD AND MEMBRANE TRACKS > 1000 MOHM AT 1000 VDC.
14. DIELECTRIC STRENGTH OF OVERLAY 105 KV/MM AT 175 MICRONS.
15. MECHANICAL.
SWITCH TRAVEL.
MEMBRANE LIFE DURATION : 3 MILLION OPERATION.
16. SPECIFY PRINT SILVER AND DIELECTRIC USED CONDUCTIVE SILVER ACHESON 725A,
CARBON ACHESON 423SS, DIELECTRIC ACHESON 452SS.
17. MATERIAL SPECIFICATION : OVERLAY SPACER, CIRCUIT SPACER AND ADHESIVE,
ALL ADHESIVE LAYERS/SPACER LAYERS USE ACRYLIC ADHESIVES WITH POLYESTER CARRIERS.
18. OPERATING TEMPERATURE +5°C TO +40°C.
19. STORAGE TEMPERATURE -20°C TO +70°C.
20. MOISTURE 10% TO 95% RH NONCONDENSING.
21. CERTIFICATE OF COMPLIANCE REQUIRED.
22. TRACEABILITY LABEL MUST INCLUDE.
THE PRODUCT NAME,
THE MANUFACTURER NAME,
THE YEAR AND THE WEEK AS THE LOT NUMBER,
23. PACKAGING
MEMBRANES PACKED IN 10'S WITH PART NUMBER WRITTEN ON IT , FRONT TO FRONT ,
BACK TO BACK WITH CARDBOARD FRONT AND REAR TO STABILIZE THE TAILS.
24. PART/COMPONENT TO BE RoHS COMPLIANT.

Zone de positionnement de
l'étiquette de traçabilité
Traceability label position

led Ventil
Ventilation LED under boss
3 blue filter

axe de la nappe au pas de 1
épaisseur 0.3mm pour la zone
d'insertion des 22 contacts
Connecteur ZIF 22 brs
REF 52610-2290 - insertion nulle

Ribbon axie at thread pitch of 1
thickness 0.3 mm for insertion zone
of the 22 contacts
Connector ZIF 22 brs
REF 52610-2290-Zero Insertion Force
Protection polyester auto-collante
sur limande coté circuit imprimé
Protective film, self-adhesive on jumper on
the side of printed circuit.

PROPRIETARY & CONFIDENTIAL. THIS DOCUMENT MAY NOT BE COPIED, DISCLOSED, OR USED IN WHOLE OR IN
PART WITHOUT THE CONSENT OF COVIDIEN.

TITLE: KEYPAD PB560 | COVIDIEN 6135 Gunbarrel Avenue Boulder, CO 80301 © 2010 COVIDIEN ALL RIGHTS RESERVED. C N/A

SIZE | FILENAME: 3825500.SLDDRW

-SCALE: | DRAWN: LABADESSE CHECKED: SEE AGILE APPROVED: SEE AGILE | SEE AGILE DATE: SEE AGILE DATE: SEE AGILE
DO NOT SCALE DRAWING | | | REV E

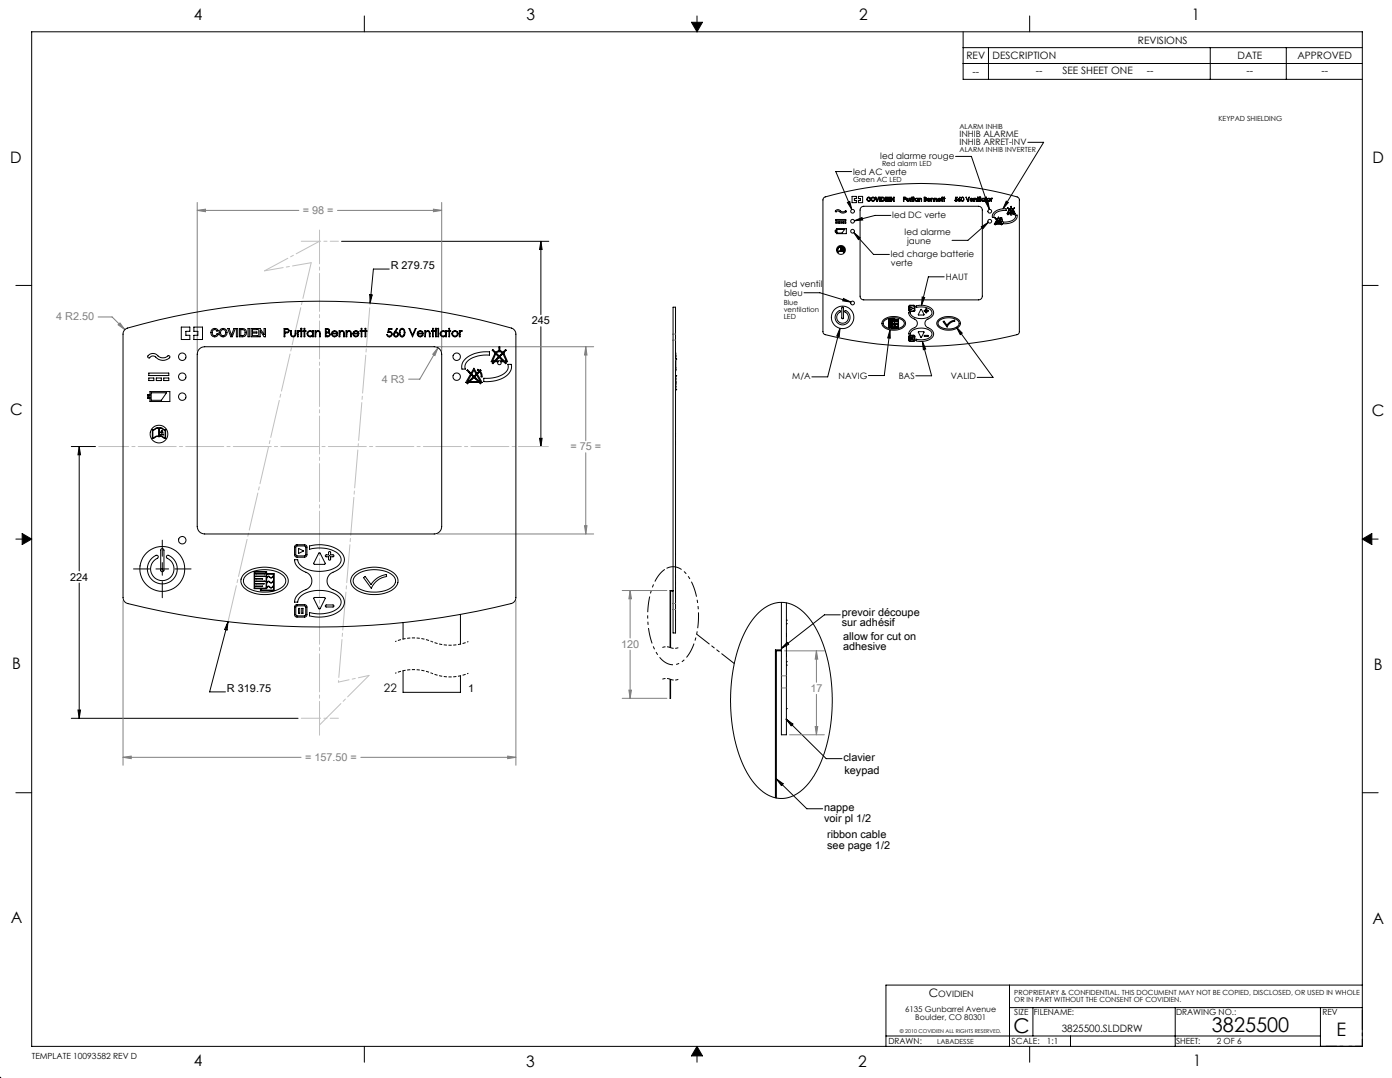
[picture p174: page 2]
led ventil; KEYPAD SHIELDING; voir pl 1/2 ribbon cable see page 1/2

REV | DESCRIPTION | DATE | APPROVED
-- | --SEE SHEET ONE -- | -- | --

ALARM INHIB
INHIB ALARME
INHIB ARRET-INV
ALARM INHIB INVERTER

led alarme rouge
Red alarm LED
led AC verte
Green AC LED

led DC verte
led alarme
jaune
led charge batterie
verte

prevoir découpe
sur adhésif
allow for cut on
adhesive

COVIDIEN 6135 Gunbarrel Avenue Boulder, CO 80301 © 2010 COVIDIEN ALL RIGHTS RESERVED. | PROPRIETARY & CONFIDENTIAL. THIS DOCUMENT MAY NOT BE COPIED, DISCLOSED, OR USED IN WHOLE OR IN PART WITHOUT THE CONSENT OF COVIDIEN.

C | FILENAME: 3825500.SLDDRW | DRAWING NO.: | REV E

DRAWN: LABADESSE | SCALE: 1:1 | | SHEET: 2 OF 6

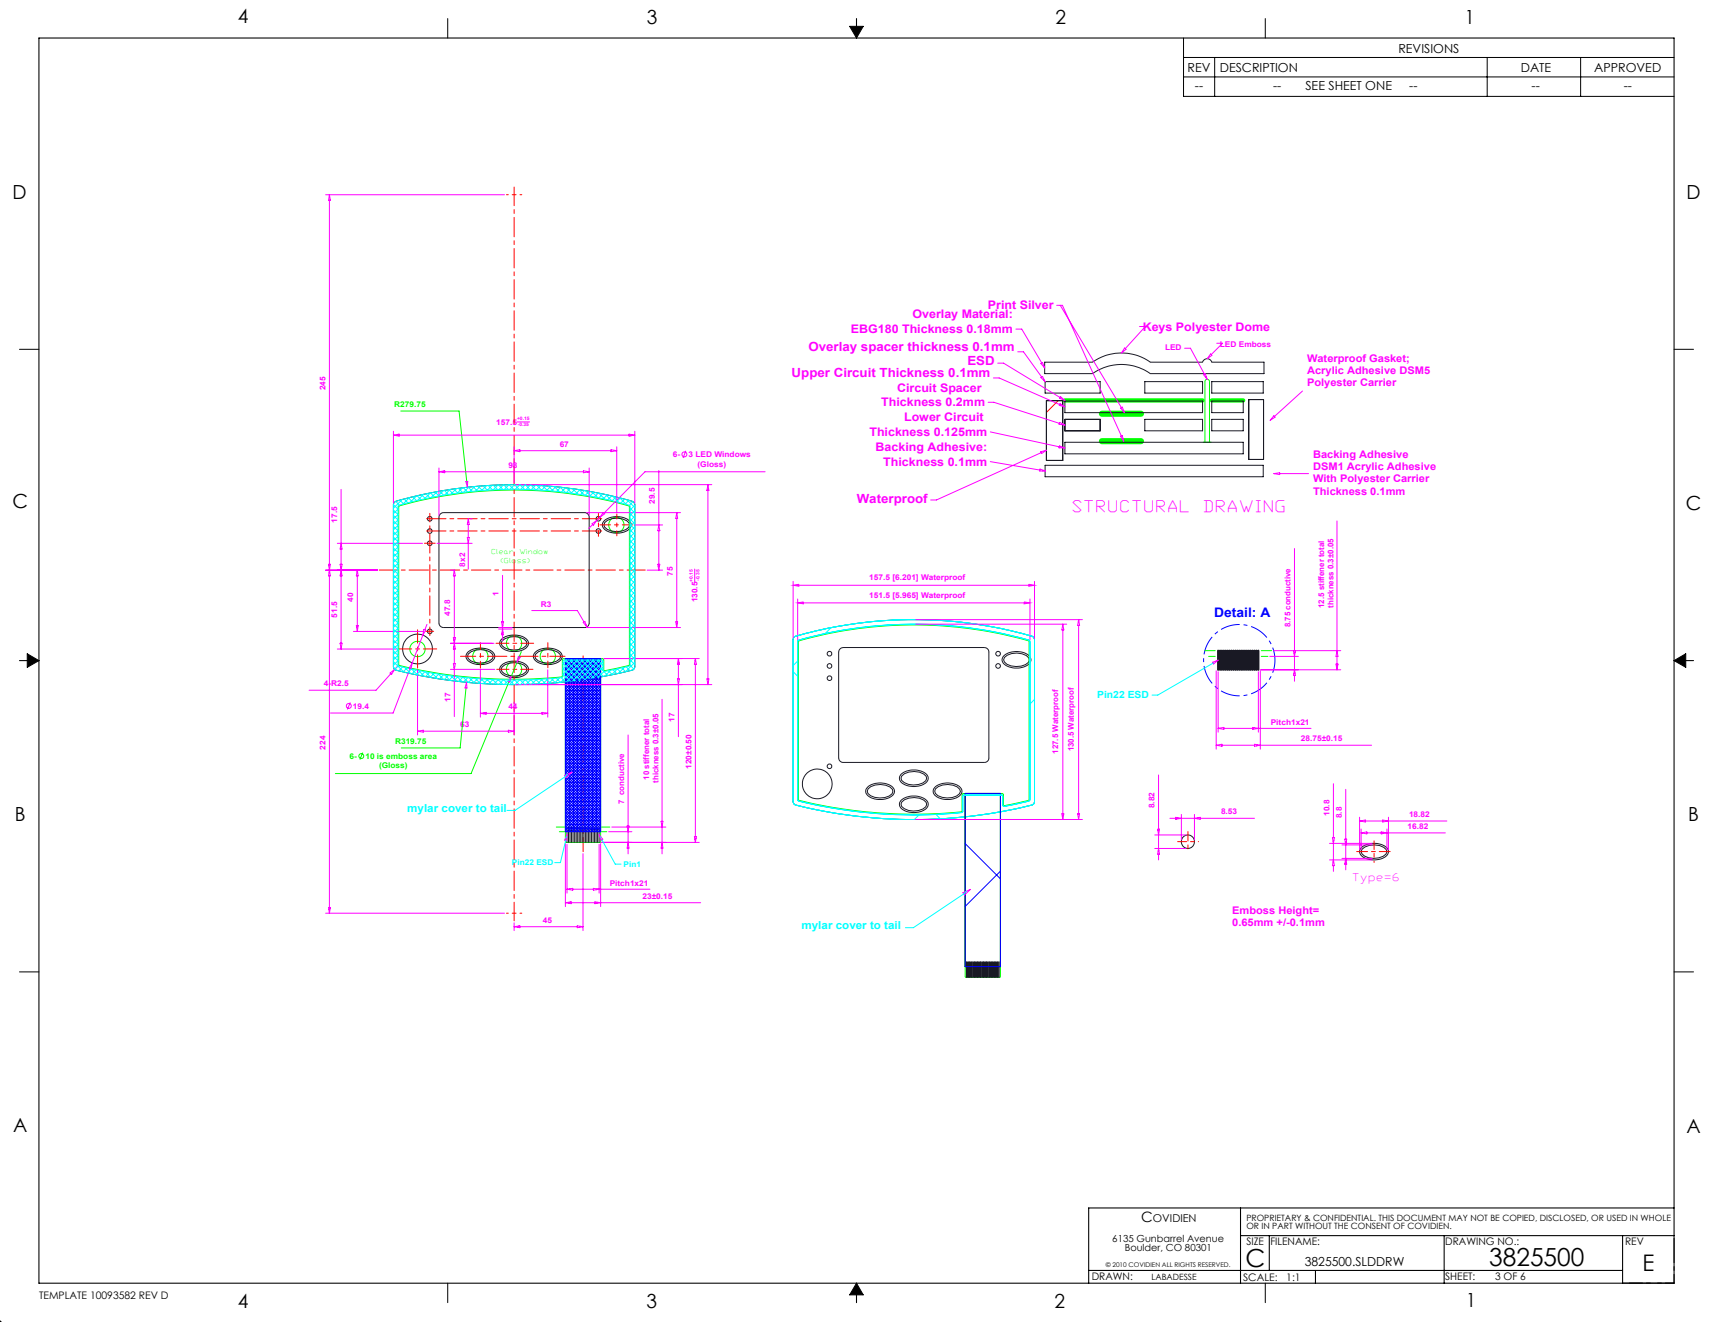
[picture p175: page 3]
151.5 [5.965] Waterproof; 157.5 [6.201] Waterproof; Lower Circuit Thickness 0.125mm; Circuit Spacer Thickness 0.2mm; Backing Adhesive: Thickness 0.1mm; Overlay Material:; STRUCTURAL DRAWING; Print Silver; Pin22 ESD; Detail: A; Emboss Height= 0.65mm +/-0.1mm; Waterproof Gasket; Acrylic Adhesive DSM5 Polyester Carrier; Clear Window; Pin1; 10 stiffener total; thickness 0.3±0.05; 7 conductive; 6- 3 LED Windows; 130.5 Waterproof; 127.5 Waterproof; 8.75 conductive; 12.5 stiffener total

EBG180 Thickness 0.18mm
Overlay spacer thickness 0.1mm
Upper Circuit Thickness 0.1mm

Keys Polyester Dome
LED Emboss LED

Backing Adhesive
DSM1 Acrylic Adhesive
With Polyester Carrier
Thickness 0.1mm

6- 10 is emboss area
(Gloss)

mylar cover to tail

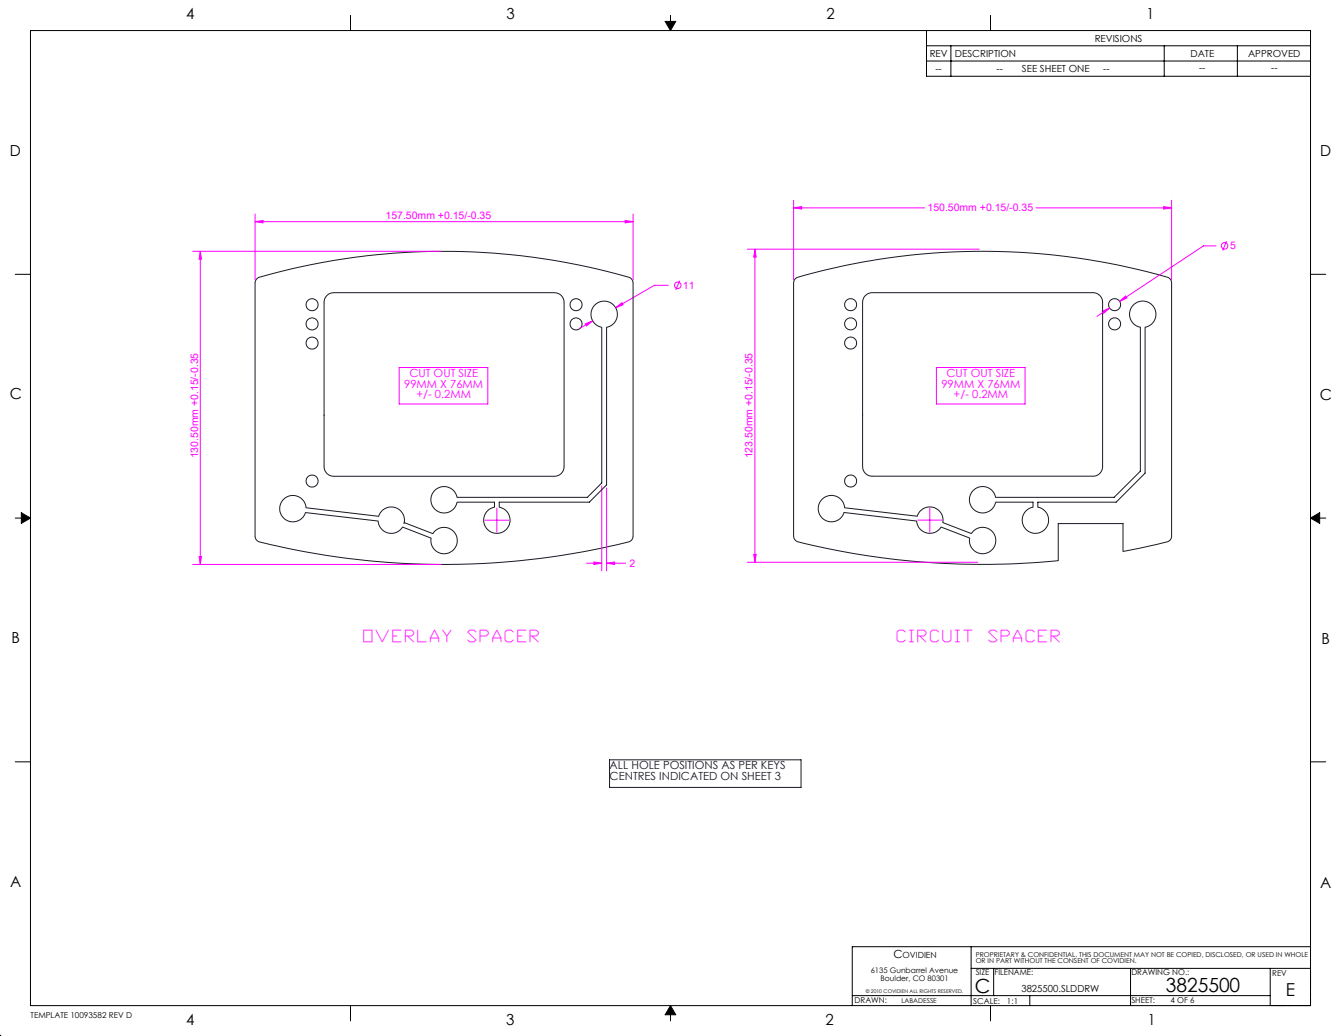
[picture p176: page 4]
OVERLAY SPACER; CIRCUIT SPACER; CUT OUT SIZE 99MM X 76MM +/- 0.2MM

ALL HOLE POSITIONS AS PER KEYS
CENTRES INDICATED ON SHEET 3

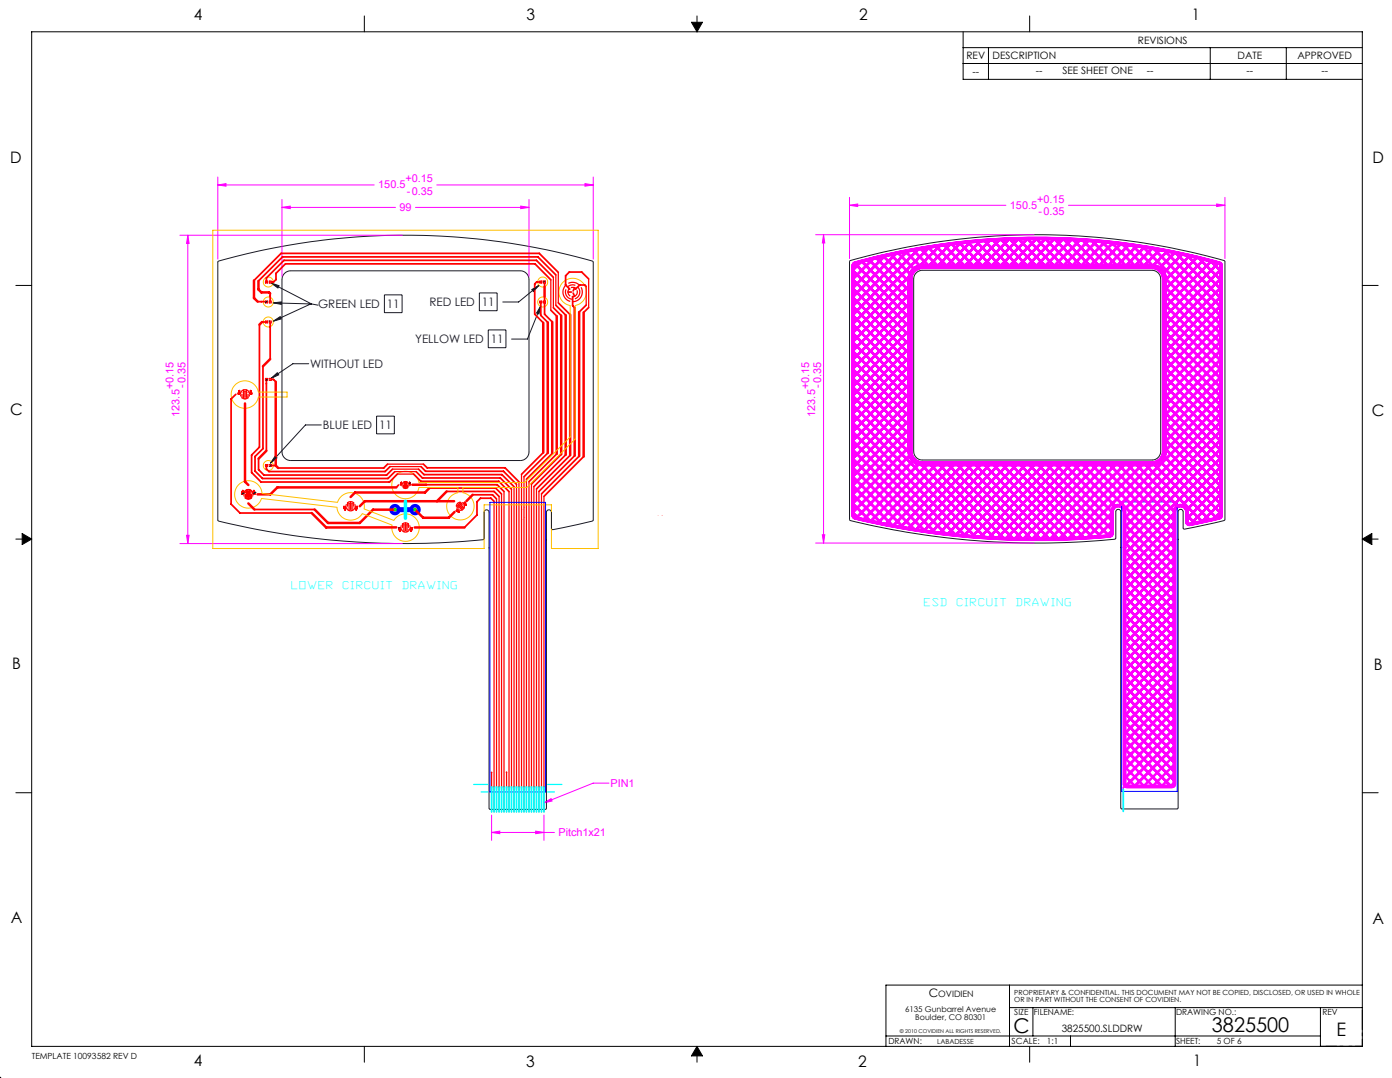
[picture p177: page 5]
GREEN LED; WITHOUT LED; RED LED; YELLOW LED; BLUE LED

LOWER CIRCUIT DRAWING

ESD CIRCUIT DRAWING

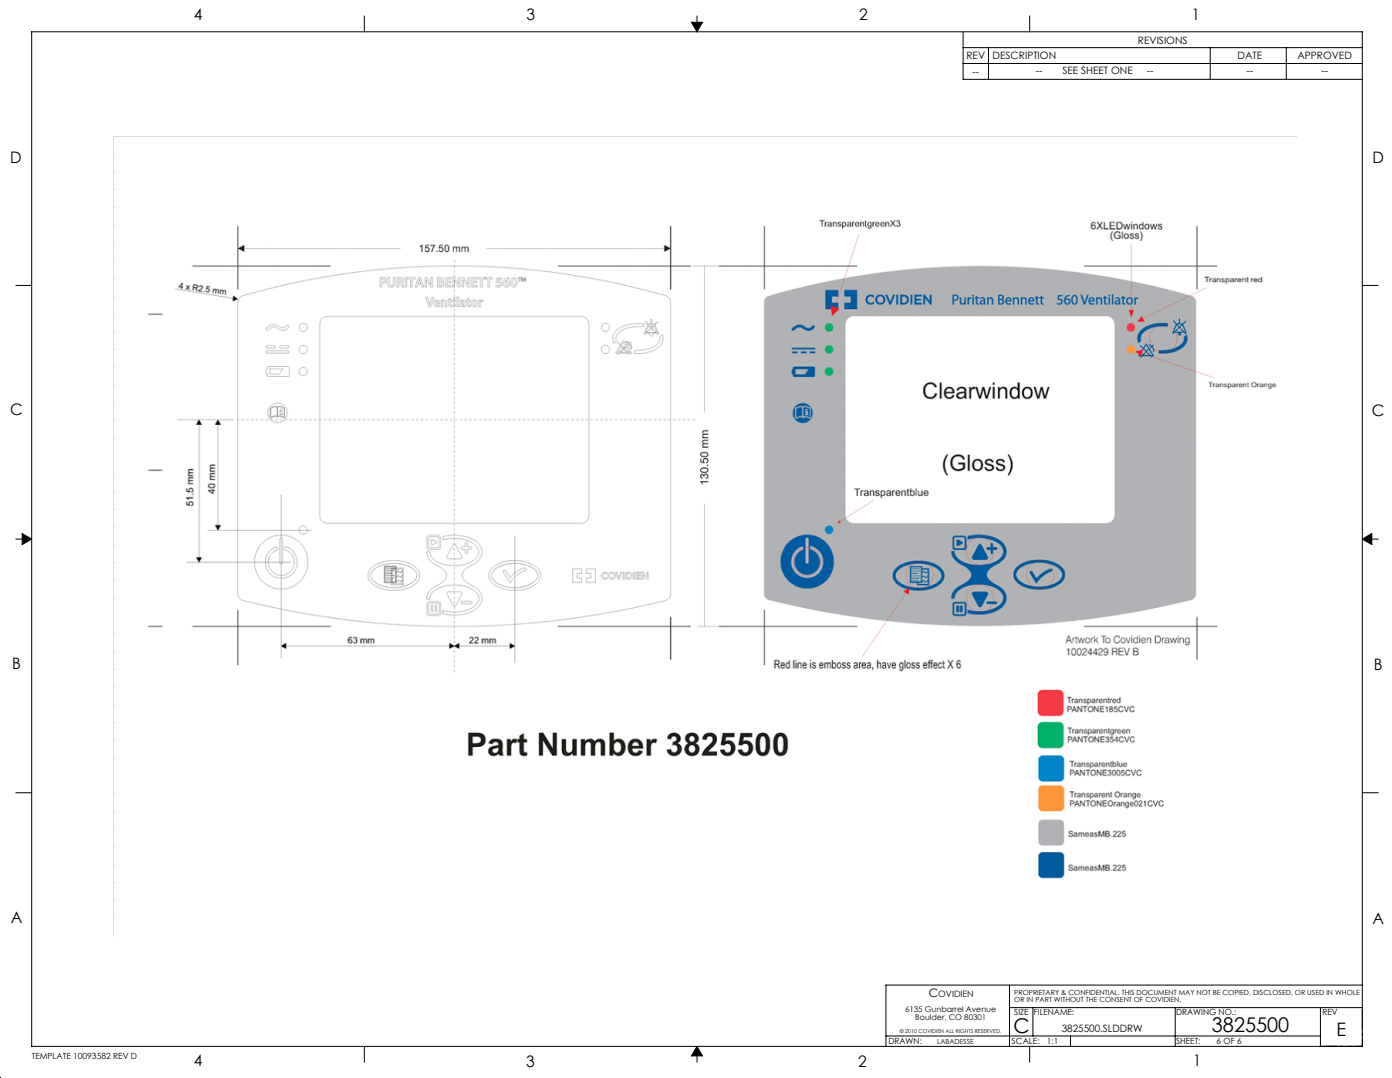
[picture p178: page 6]
