hesingh/ventilator/Medtronic/medtronic-pb560-ventilator-system-file-set-2/Mechanical Part Drawings/2963300/2963300B00.PDF

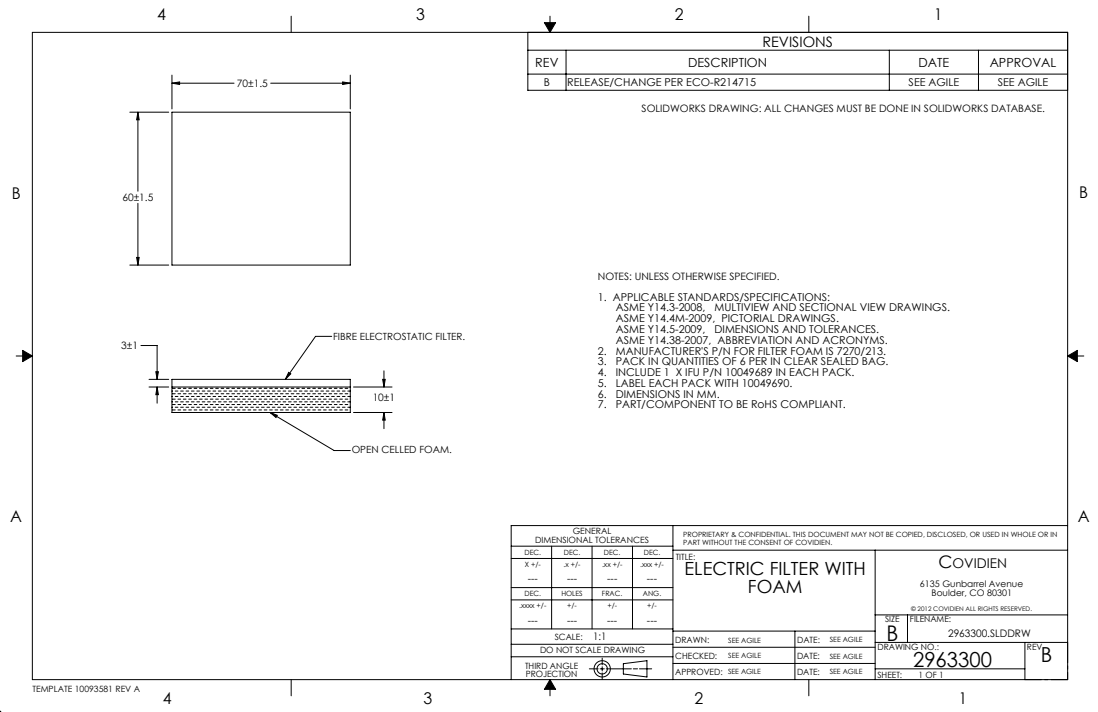
[picture p189: page 1]
2 TEMPLATE 10093581 REV A; .xxxx +/-; THIRD ANGLE; .xxx +/-; SHEET:; DATE:; DRAWING NO.:; DIMENSIONAL TOLERANCES

REVISIONS

REV | DESCRIPTION | DATE | APPROVAL
B | RELEASE/CHANGE PER ECO-R214715 | SEE AGILE | SEE AGILE

SOLIDWORKS DRAWING: ALL CHANGES MUST BE DONE IN SOLIDWORKS DATABASE.

NOTES: UNLESS OTHERWISE SPECIFIED.
1. APPLICABLE STANDARDS/SPECIFICATIONS:
ASME Y14.3-2008, MULTIVIEW AND SECTIONAL VIEW DRAWINGS.
ASME Y14.4M-2009, PICTORIAL DRAWINGS.
ASME Y14.5-2009, DIMENSIONS AND TOLERANCES.
ASME Y14.38-2007, ABBREVIATION AND ACRONYMS.
2. MANUFACTURER'S P/N FOR FILTER FOAM IS 7270/213.
3. PACK IN QUANTITIES OF 6 PER IN CLEAR SEALED BAG.
4. INCLUDE 1 X IFU P/N 10049689 IN EACH PACK.
5. LABEL EACH PACK WITH 10049690.
6. DIMENSIONS IN MM.
7. PART/COMPONENT TO BE RoHS COMPLIANT.

FIBRE ELECTROSTATIC FILTER.

OPEN CELLED FOAM.

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

TITLE: ELECTRIC FILTER WITH FOAM | COVIDIEN 6135 Gunbarrel Avenue Boulder, CO 80301 © 2012 COVIDIEN ALL RIGHTS RESERVED. B ---

SIZE | FILENAME: 2963300.SLDDRW

1:1 SCALE: | DRAWN: SEE AGILE CHECKED: SEE AGILE APPROVED: SEE AGILE | SEE AGILE DATE: SEE AGILE DATE: SEE AGILE
DO NOT SCALE DRAWING | | | 2963300 | REV B
