hesingh/ventilator/Medtronic/medtronic-pb560-ventilator-system-file-set-2/Mechanical Part Drawings/2971700/2971700C00.PDF

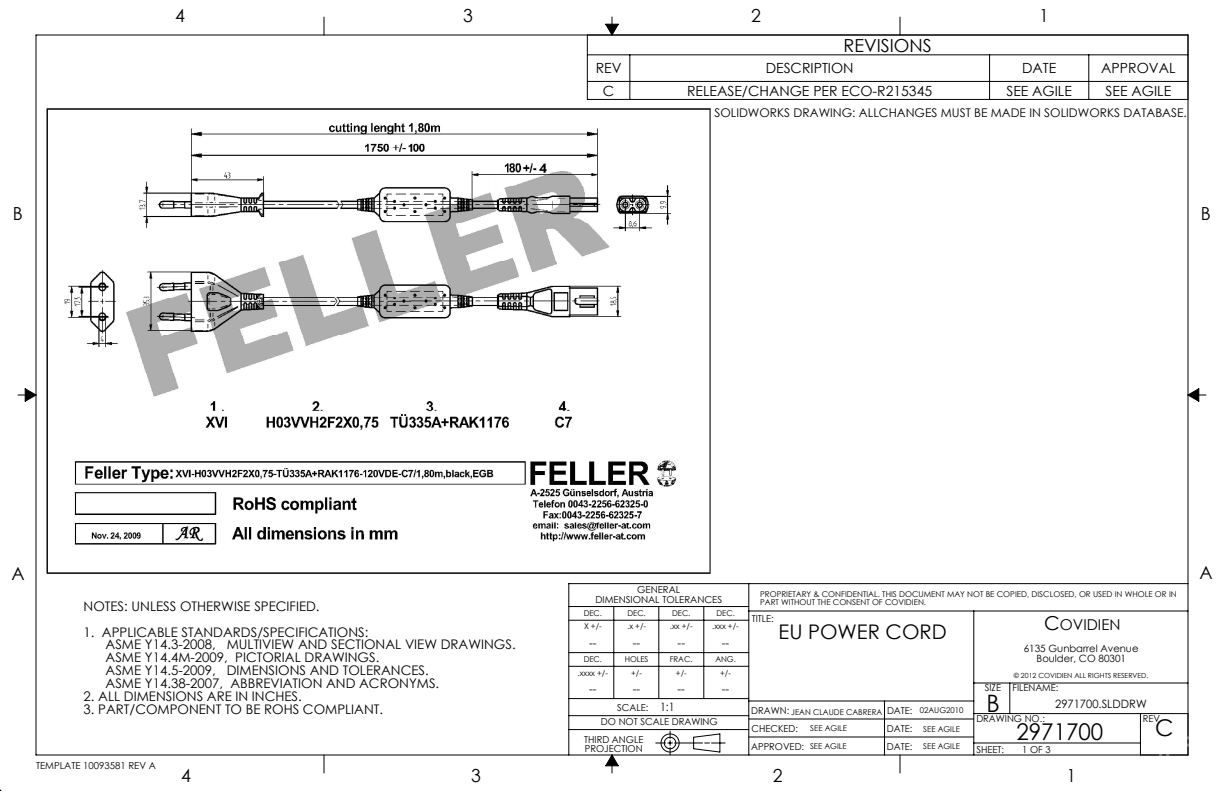
[picture p192: page 1]
2 TEMPLATE 10093581 REV A; .xxxx +/-; THIRD ANGLE; .xxx +/-; SHEET:; DATE:; DRAWING NO.:; DIMENSIONAL TOLERANCES

REVISIONS

REV | DESCRIPTION | DATE | APPROVAL
C | RELEASE/CHANGE PER ECO-R215345 | SEE AGILE | SEE AGILE

SOLIDWORKS DRAWING: ALLCHANGES MUST BE MADE IN SOLIDWORKS DATABASE.

PROPRIETARY & CONFIDENTIAL. THIS DOCUMENT MAY NOT BE COPIED, DISCLOSED, OR USED IN WHOLE OR IN
PART WITHOUT THE CONSENT OF COVIDIEN.

NOTES: UNLESS OTHERWISE SPECIFIED.
1. APPLICABLE STANDARDS/SPECIFICATIONS:
ASME Y14.3-2008, MULTIVIEW AND SECTIONAL VIEW DRAWINGS.
ASME Y14.4M-2009, PICTORIAL DRAWINGS.
ASME Y14.5-2009, DIMENSIONS AND TOLERANCES.
ASME Y14.38-2007, ABBREVIATION AND ACRONYMS.
2. ALL DIMENSIONS ARE IN INCHES.
3. PART/COMPONENT TO BE ROHS COMPLIANT.

TITLE: EU POWER CORD | COVIDIEN 6135 Gunbarrel Avenue Boulder, CO 80301 © 2012 COVIDIEN ALL RIGHTS RESERVED. B --

SIZE | FILENAME: 2971700.SLDDRW

1:1 SCALE: | DRAWN: JEAN CLAUDE CABRERA CHECKED: SEE AGILE APPROVED: SEE AGILE | 02AUG2010 DATE: SEE AGILE DATE: SEE AGILE
DO NOT SCALE DRAWING | | | 2971700 | REV C

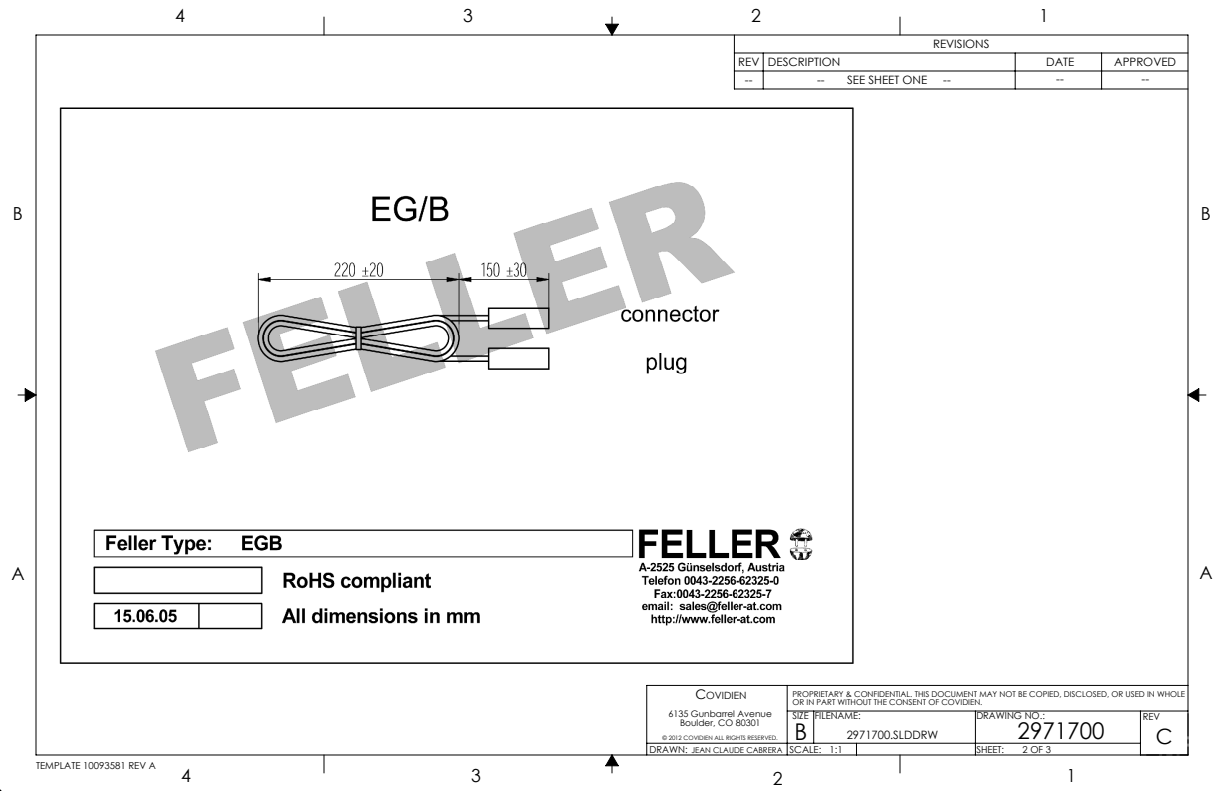
[picture p193: page 2]
TEMPLATE 10093581 REV A

REV | DESCRIPTION | DATE | APPROVED
-- | --SEE SHEET ONE -- | -- | --

COVIDIEN 6135 Gunbarrel Avenue Boulder, CO 80301 © 2012 COVIDIEN ALL RIGHTS RESERVED. | PROPRIETARY & CONFIDENTIAL. THIS DOCUMENT MAY NOT BE COPIED, DISCLOSED, OR USED IN WHOLE OR IN PART WITHOUT THE CONSENT OF COVIDIEN.

SIZE B | FILENAME: 2971700.SLDDRW | DRAWING NO.: 2971700 | REV C

DRAWN: JEAN CLAUDE CABRERA | SCALE: 1:1 | | SHEET: 2 OF 3

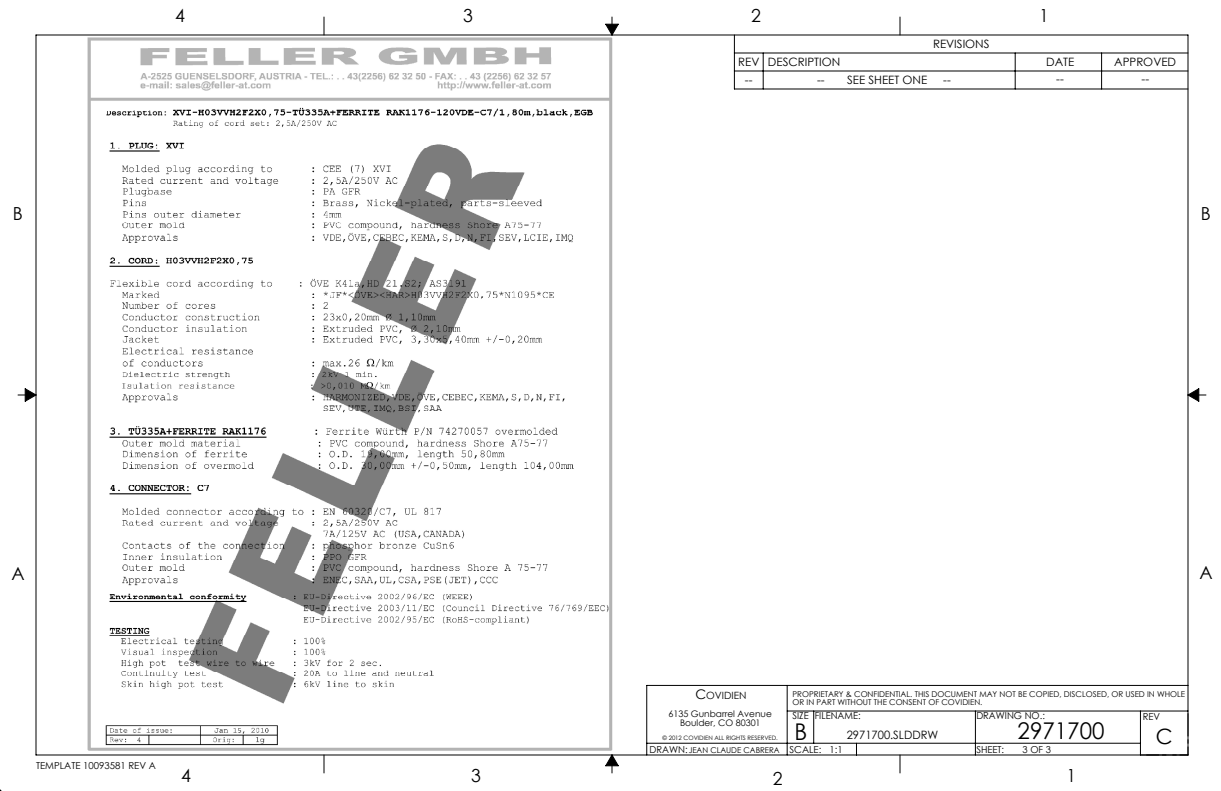
[picture p194: page 3]
TEMPLATE 10093581 REV A

REV | DESCRIPTION | DATE | APPROVED
-- | --SEE SHEET ONE -- | -- | --

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

SIZE B | FILENAME: 2971700.SLDDRW | DRAWING NO.: 2971700 | REV C

DRAWN: JEAN CLAUDE CABRERA | SCALE: 1:1 | | SHEET: 3 OF 3
