hesingh/ventilator/Medtronic/medtronic-pb560-ventilator-system-file-set-2/Mechanical Part Drawings/3824200/3824200B00.PDF

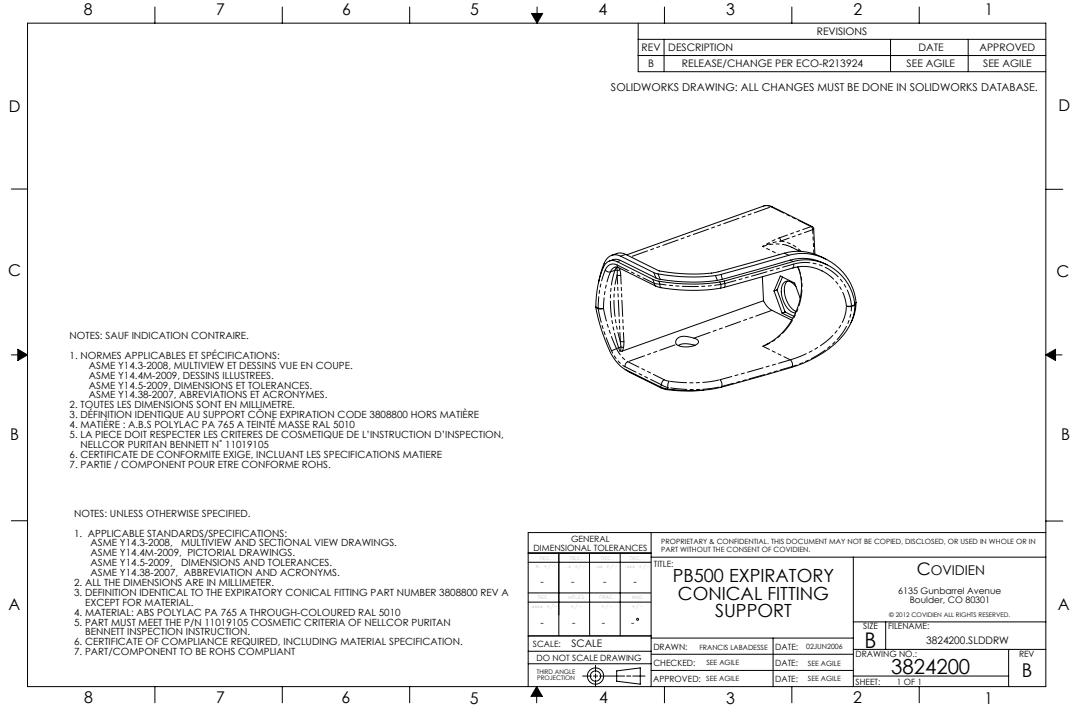
[picture p196: page 1]
FRANCIS LABADESSE; 02JUN2006; THIRD ANGLE; SHEET:; DATE:; DRAWING NO.:; SEE AGILE; .xxxx +/-; .xxx +/-

REVISIONS

REV | DESCRIPTION | DATE | APPROVED
B | RELEASE/CHANGE PER ECO-R213924 | SEE AGILE | SEE AGILE

SOLIDWORKS DRAWING: ALL CHANGES MUST BE DONE IN SOLIDWORKS DATABASE.

NOTES: SAUF INDICATION CONTRAIRE.
1. NORMES APPLICABLES ET SPÉCIFICATIONS:
ASME Y14.3-2008, MULTIVIEW ET DESSINS VUE EN COUPE.
ASME Y14.4M-2009, DESSINS ILLUSTREES.
ASME Y14.5-2009, DIMENSIONS ET TOLERANCES.
ASME Y14.38-2007, ABREVIATIONS ET ACRONYMES.
2. TOUTES LES DIMENSIONS SONT EN MILLIMETRE.
3. DÉFINITION IDENTIQUE AU SUPPORT CÔNE EXPIRATION CODE 3808800 HORS MATIÈRE
4. MATIÈRE : A.B.S POLYLAC PA 765 A TEINTÉ MASSE RAL 5010

5. LA PIECE DOIT RESPECTER LES CRITERES DE COSMETIQUE DE L’INSTRUCTION D’INSPECTION,
NELLCOR PURITAN BENNETT N˚ 11019105
6. CERTIFICATE DE CONFORMITE EXIGE, INCLUANT LES SPECIFICATIONS MATIERE
7. PARTIE / COMPONENT POUR ETRE CONFORME ROHS.

NOTES: UNLESS OTHERWISE SPECIFIED.
1. APPLICABLE STANDARDS/SPECIFICATIONS:
ASME Y14.3-2008, MULTIVIEW AND SECTIONAL VIEW DRAWINGS.
ASME Y14.4M-2009, PICTORIAL DRAWINGS.
ASME Y14.5-2009, DIMENSIONS AND TOLERANCES.
ASME Y14.38-2007, ABBREVIATION AND ACRONYMS.
2. ALL THE DIMENSIONS ARE IN MILLIMETER.
3. DEFINITION IDENTICAL TO THE EXPIRATORY CONICAL FITTING PART NUMBER 3808800 REV A

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

TITLE: PB500 EXPIRATORY CONICAL FITTING SUPPORT | COVIDIEN 6135 Gunbarrel Avenue Boulder, CO 80301 © 2012 COVIDIEN ALL RIGHTS RESERVED. B -

EXCEPT FOR MATERIAL.
4. MATERIAL: ABS POLYLAC PA 765 A THROUGH-COLOURED RAL 5010
5. PART MUST MEET THE P/N 11019105 COSMETIC CRITERIA OF NELLCOR PURITAN
BENNETT INSPECTION INSTRUCTION.
6. CERTIFICATE OF COMPLIANCE REQUIRED, INCLUDING MATERIAL SPECIFICATION.
7. PART/COMPONENT TO BE ROHS COMPLIANT

- | - -
DO NOT SCALE DRAWING | | 3824200 | REV B

SIZE | FILENAME: 3824200.SLDDRW
