hesingh/ventilator/Medtronic/pb560-vent-files-4/Accessories/10000464/10000464 - Assembly Instructions.pdf

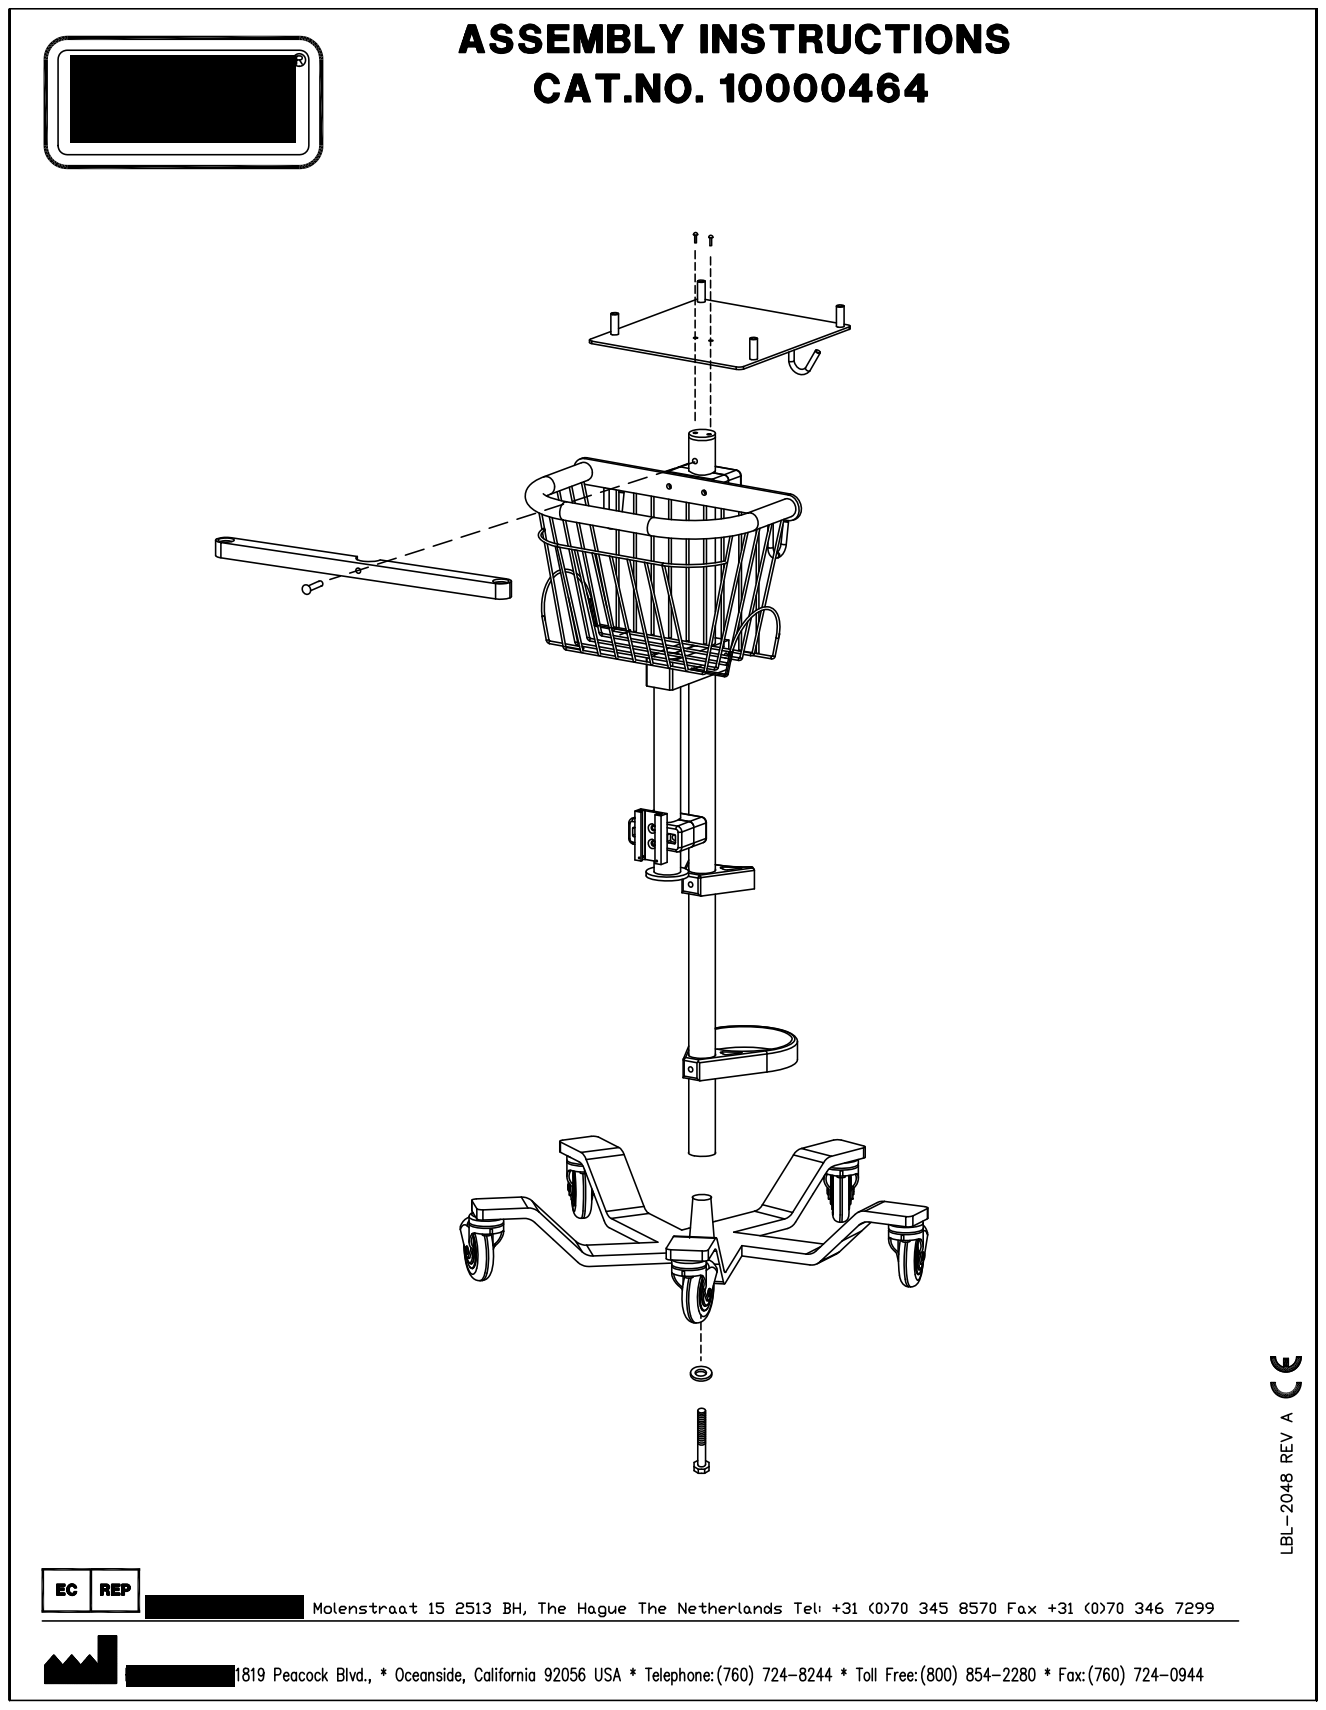
[picture p197: page 1]
