hesingh/ventilator/Medtronic/pb560-vent-files-4/Accessories/10000464/10000464 - Specifications.pdf

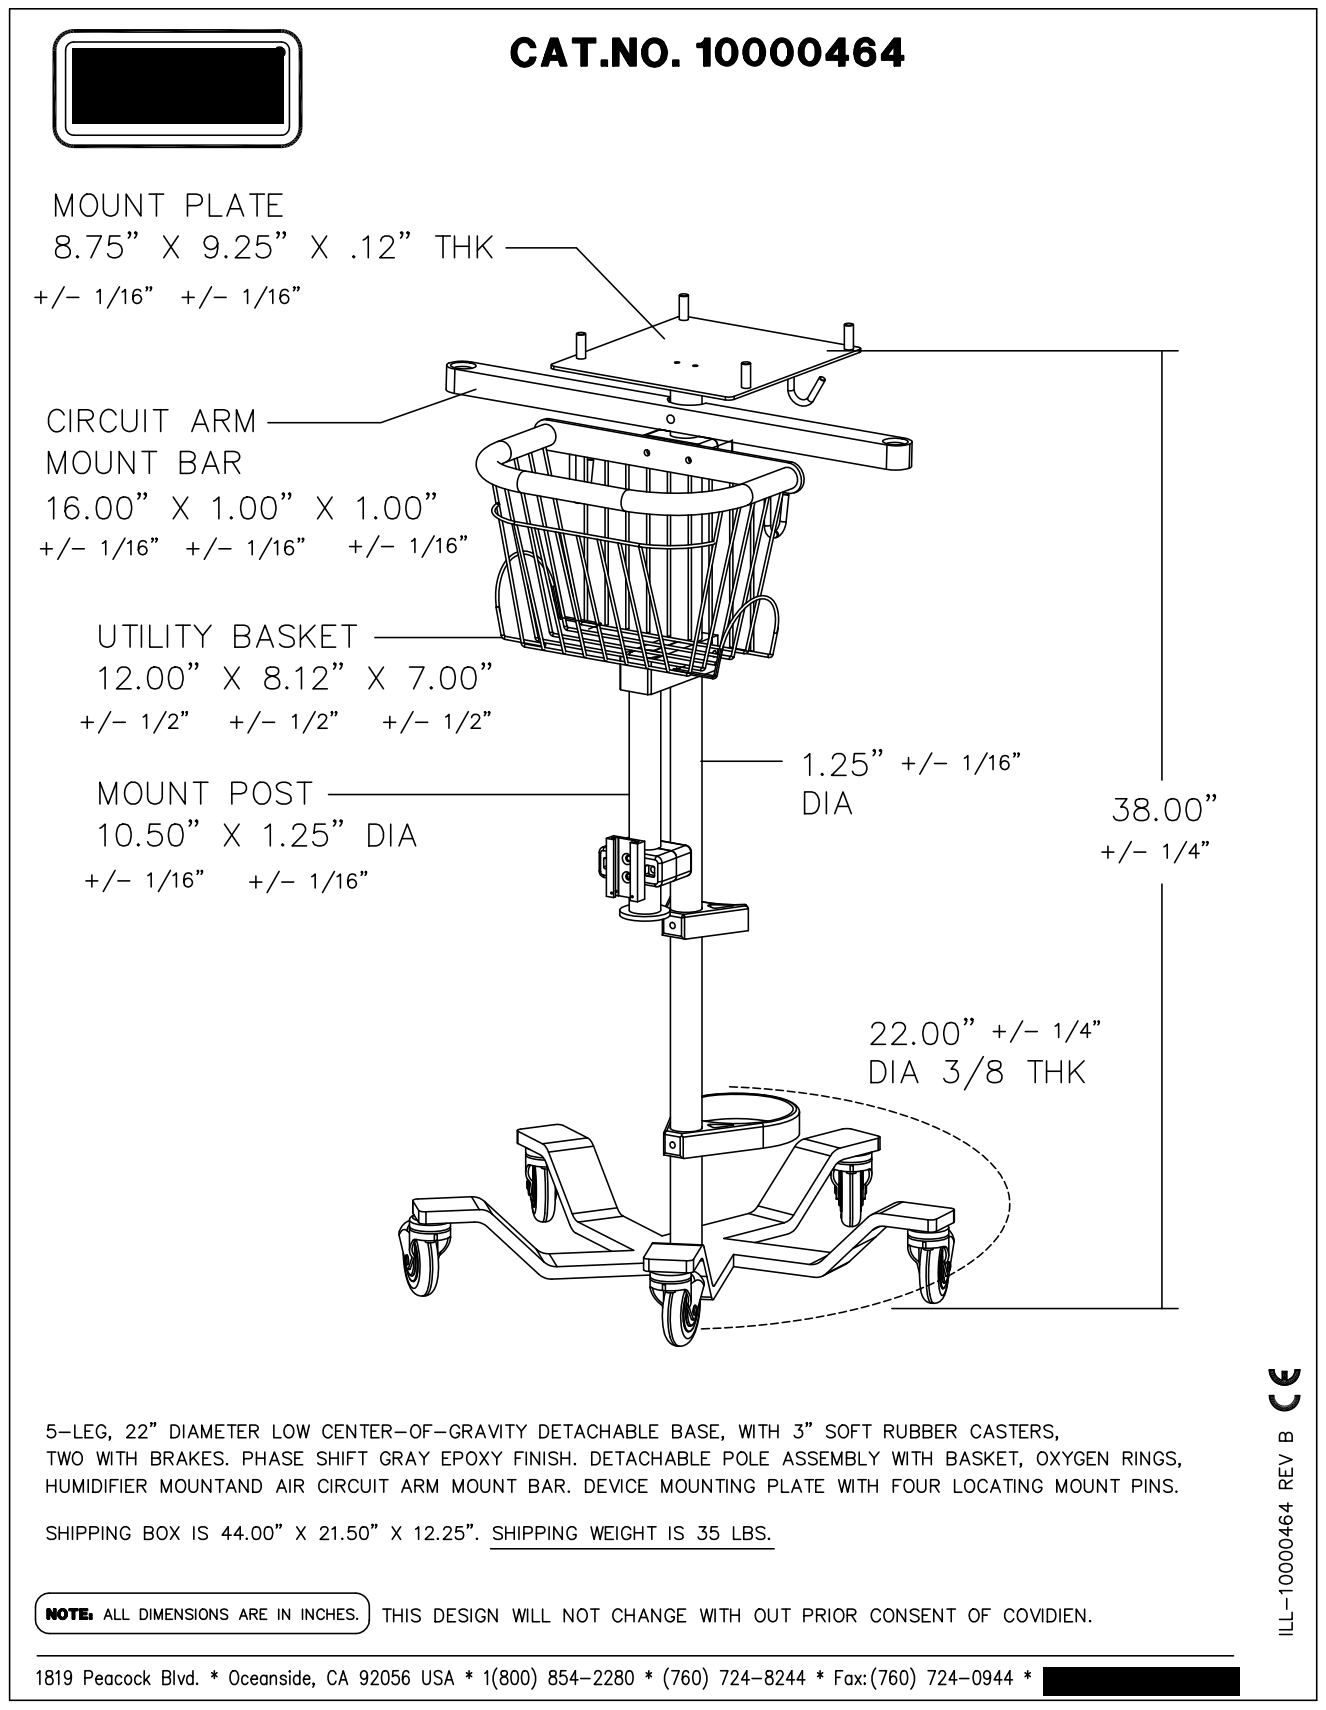
[picture p198: page 1]
