hesingh/ventilator/Medtronic/pb560-vent-files-4/BOM Drawings/PB560 Ventilator/10073068D00.pdf

75.0
12.50 | 50.0

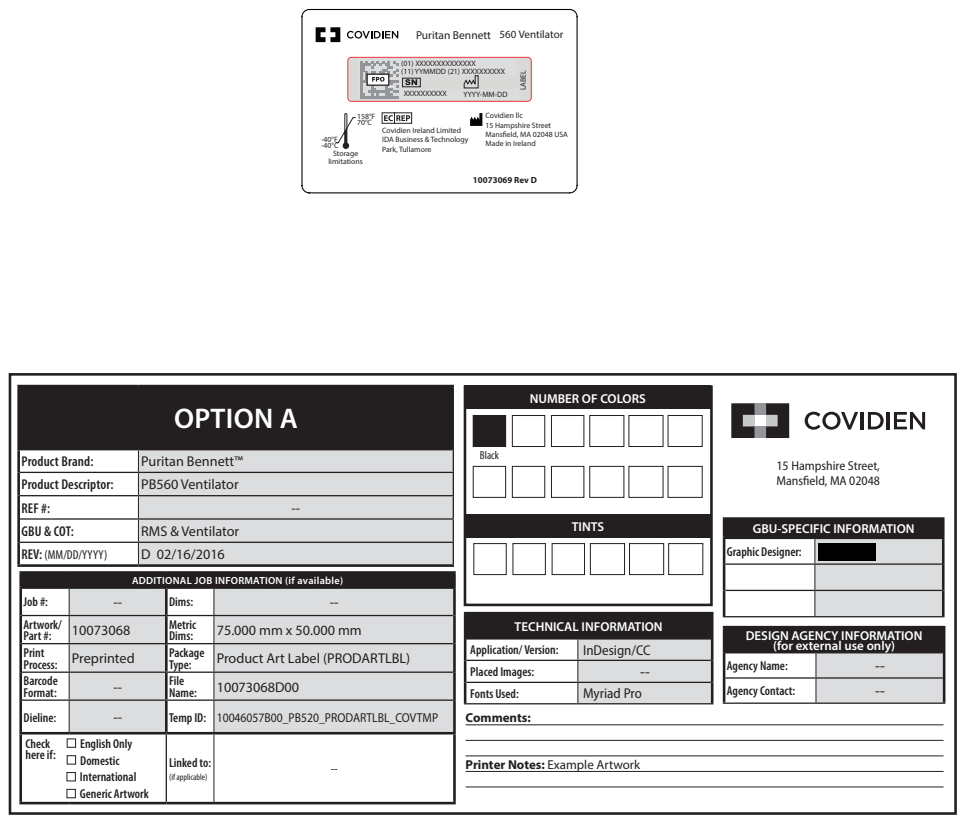
[picture p199: page 1]
10073069 Rev D; Storage limitations; XXXXXXXXXX; YYYY-MM-DD; (01) XXXXXXXXXXXXXX (11) YYMMDD (21) XXXXXXXXXX; LABEL; Clear Window; OPTION A; GBU & COT:; RMS & Ventilator; TECHNICAL INFORMATION; Comments:; 15 Hampshire Street, Mansfield, MA 02048; TINTS; Black; Job #:; Dims:; Artwork/; Part #:; Metric

Puritan Bennett 560 Ventilator

Covidien Ireland Limited
IDA Business & Technology
Park, Tullamore

Covidien llc
15 Hampshire Street
Mansfield, MA 02048 USA
Made in Ireland

NUMBER OF COLORS

Product Brand: | Puritan Bennett™
Product Descriptor: | PB560 Ventilator
REF #: | --

GBU-SPECIFIC INFORMATION

REV: (MM/DD/YYYY) | D 02/16/2016

Graphic Designer:

ADDITIONAL JOB INFORMATION (if available)

DESIGN AGENCY INFORMATION
(for external use only)

Application/ Version: | InDesign/CC
Placed Images: | --
Fonts Used: | Myriad Pro

Print Process: | Preprinted | Package Type: | Product Art Label (PRODARTLBL)
Barcode Format: | -- | File Name: | 10073068D00

Agency Name: | --
Agency Contact: | --

Dieline: | -- | Temp ID: | 10046057B00_PB520_PRODARTLBL_COVTMP
Check English Only here if: Domestic International Generic Artwork | | Linked to: (if applicable) | --

Printer Notes: Example Artwork
